awkwardengineer/Clock/Mechanical/Quotes/Case/Rev D Case Quote Package/Change notes to revC and revD.pdf

AWK-105-010 Rev C notes

# Change notes since last quote (now at Rev D.)

1. Material thickness changed from .060” to .050”
2. Overall dimensions slightly smaller
3. Addition of notches (see below)
4. QTY will be 550 pcs, each.
5. I am talking to Roy about finish. We’ll run two different colors, ANSI 61 Gray with black screenprint, and FED STD 34094 Green, with white screenprint. Final batch sizes TBD.
6. Artwork for screenprints is attached

# Changes from C to D

7. Height of box changed from 4” to 3.5”
8. Holes for knobs in top opened up
9. Only powder coat exterior faces
10. Artwork updated for new box size

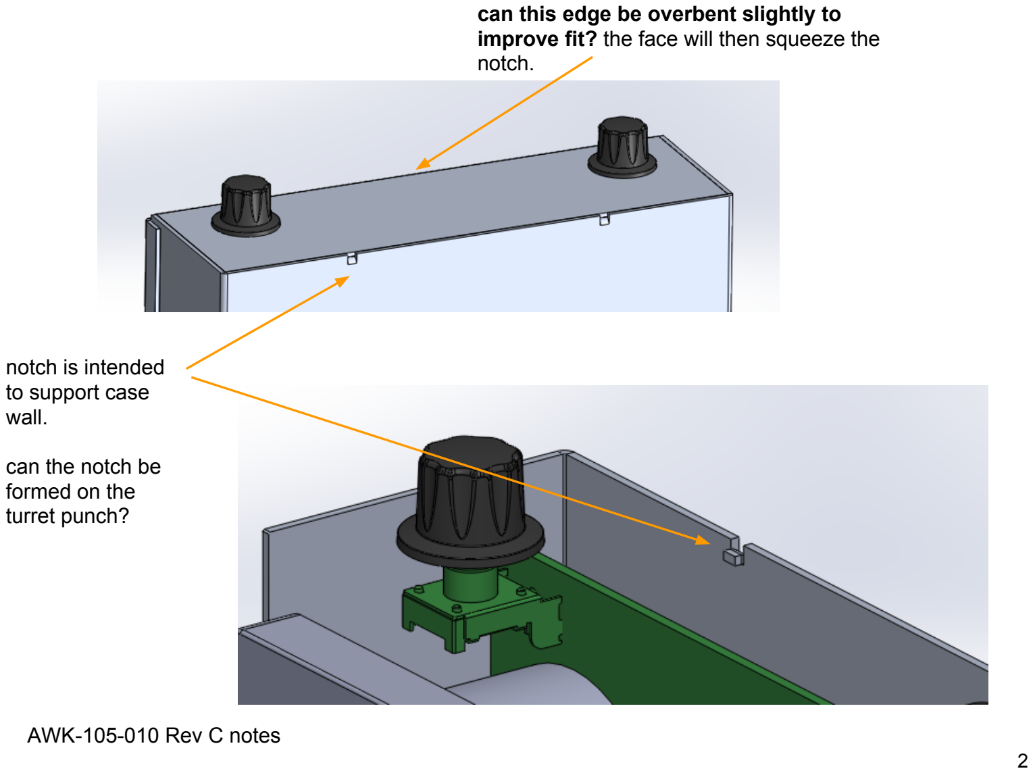
[picture p24: page 2]

notch is intended
to support case
wall.

can the notch be
formed on the
turret punch?

can this edge be overbent slightly to improve fit? the face will then squeeze the notch.

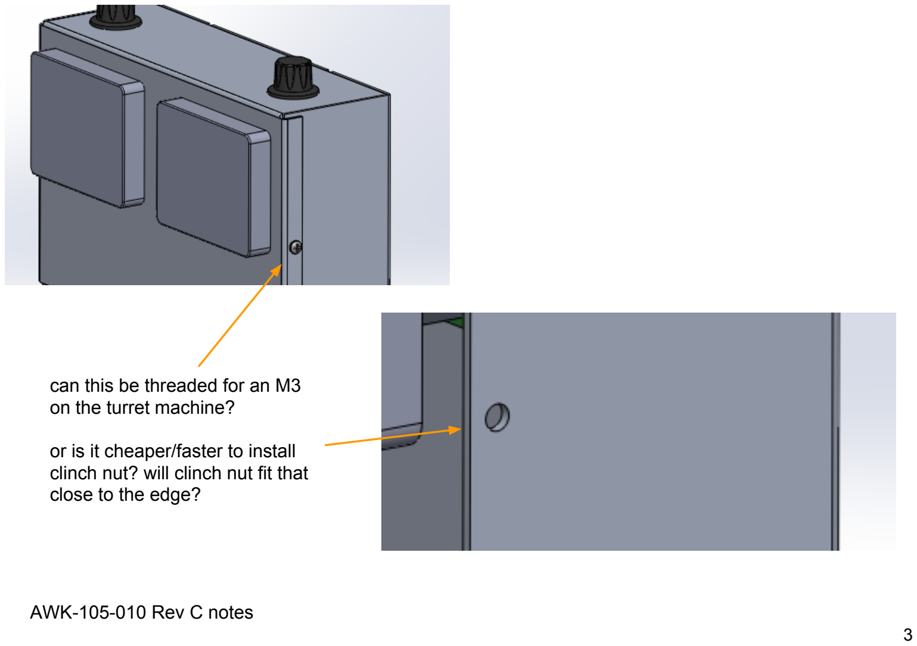
[picture p25: page 3]

can this be threaded for an M3 on the turret machine?

or is it cheaper/faster to install clinch nut? will clinch nut fit that close to the edge?
