awkwardengineer/Clock/Mechanical/Artwork/jameco 316603.pdf

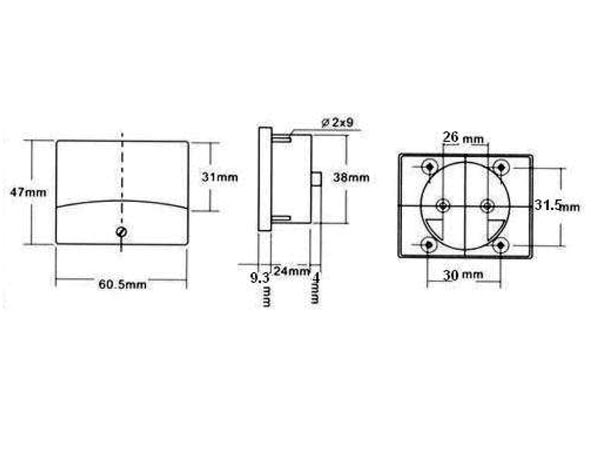
[picture p26: page 1]
