awkwardengineer/Clock/Mechanical/Quotes/Case/Rev D Case Quote Package/revD notes.pdf

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

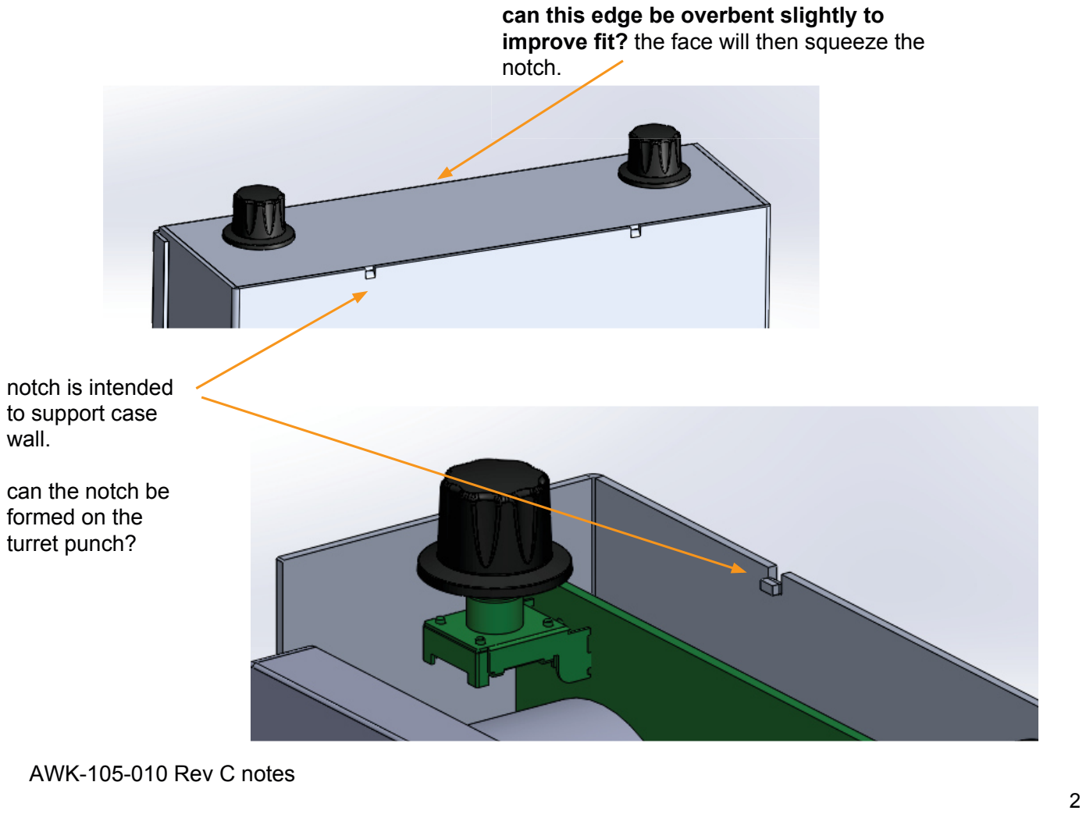
[picture p27: page 1]

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

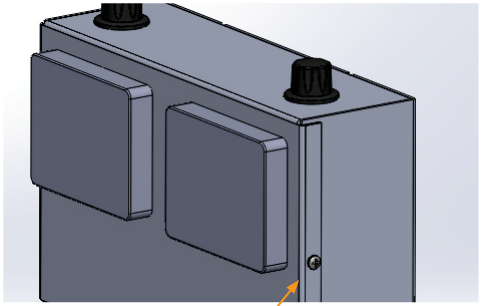
[picture p28: figure]
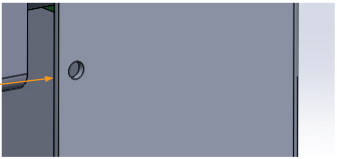
[picture p29: figure]
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
