awkwardengineer/Clock/Photos/exploded view.pdf

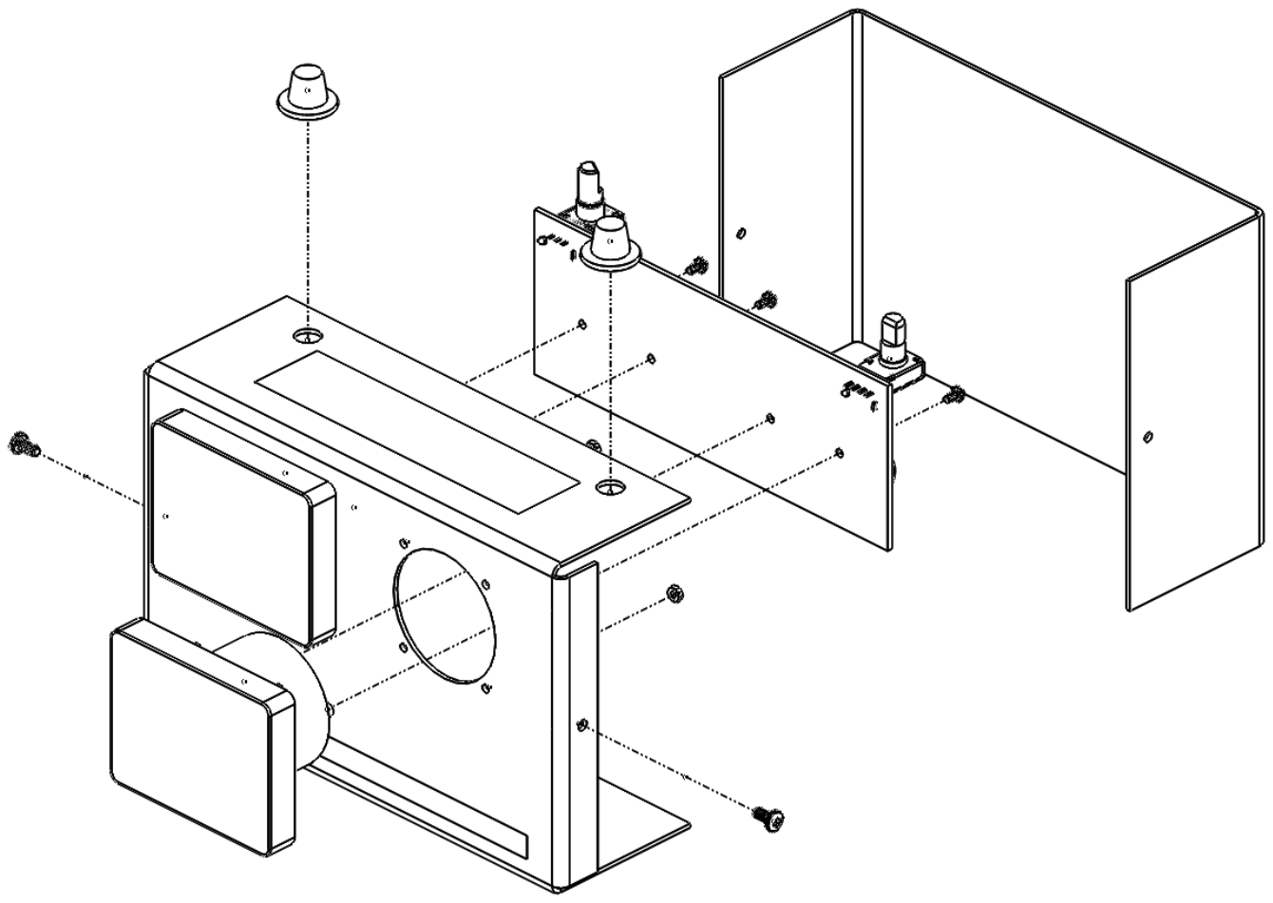
[picture p30: page 1]
