awkwardengineer/Clock/Mechanical/Artwork/AWK-105-0016 revE.png

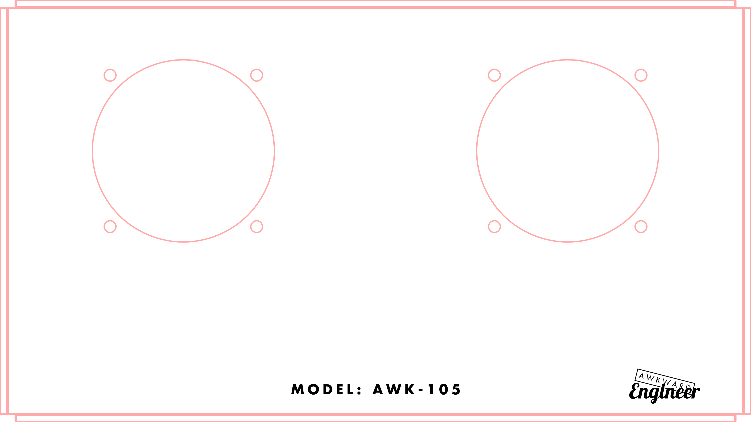
Mechanical/Artwork/AWK-105-0016 revE.png
