awkwardengineer/Clock/Mechanical/Artwork/AWK-105-0021-GRAY.png

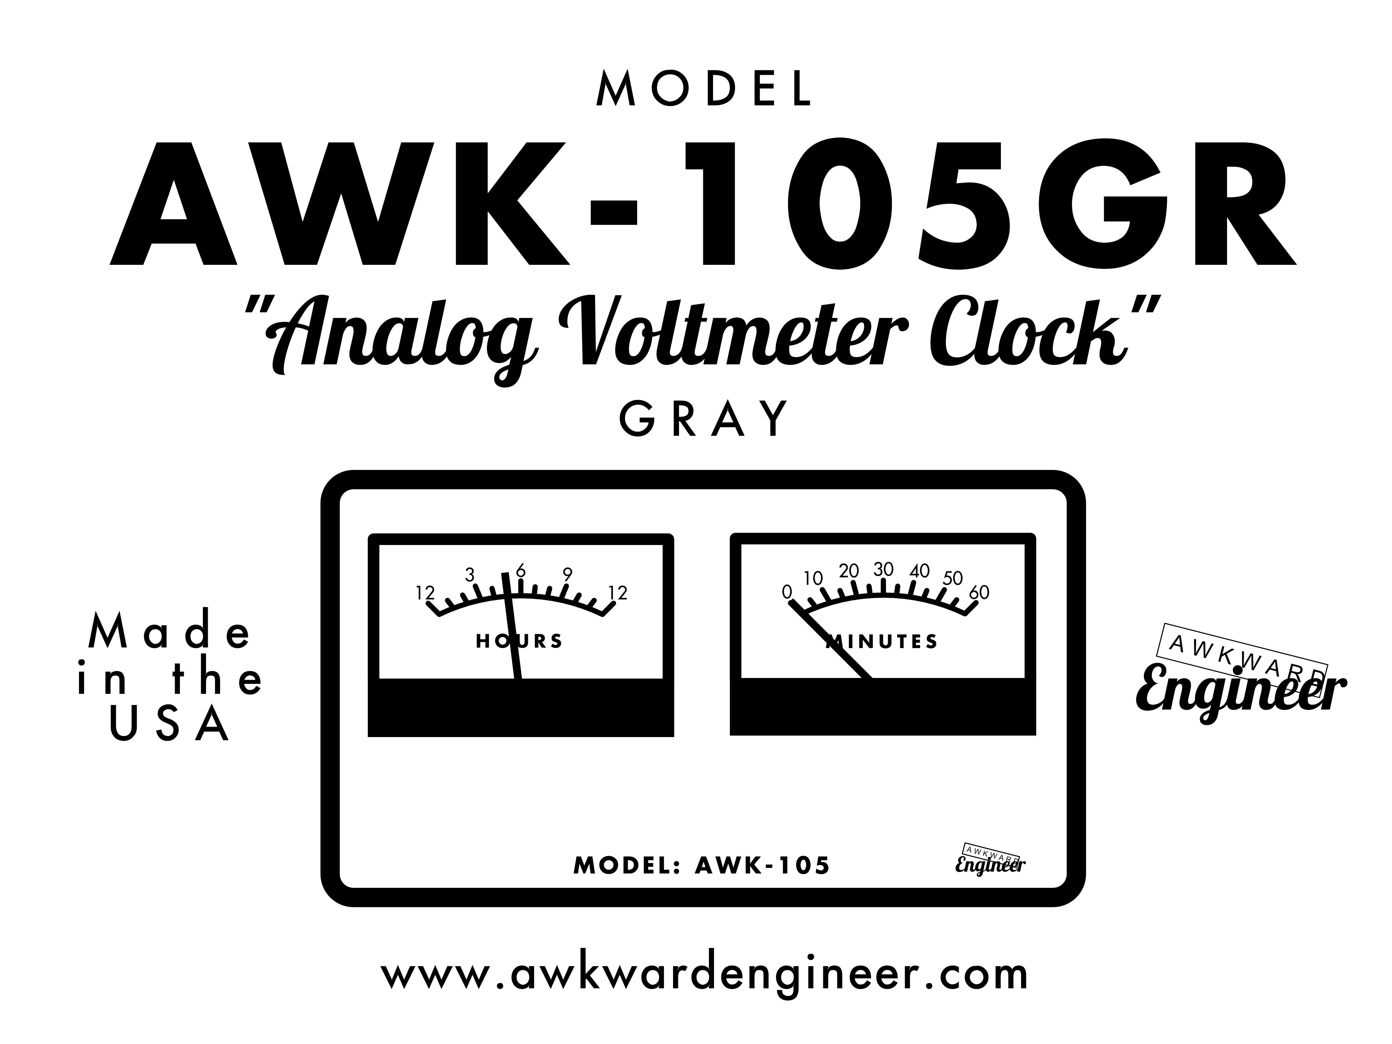
Mechanical/Artwork/AWK-105-0021-GRAY.png
