awkwardengineer/Clock/Mechanical/Artwork/AWK-105-0045.png

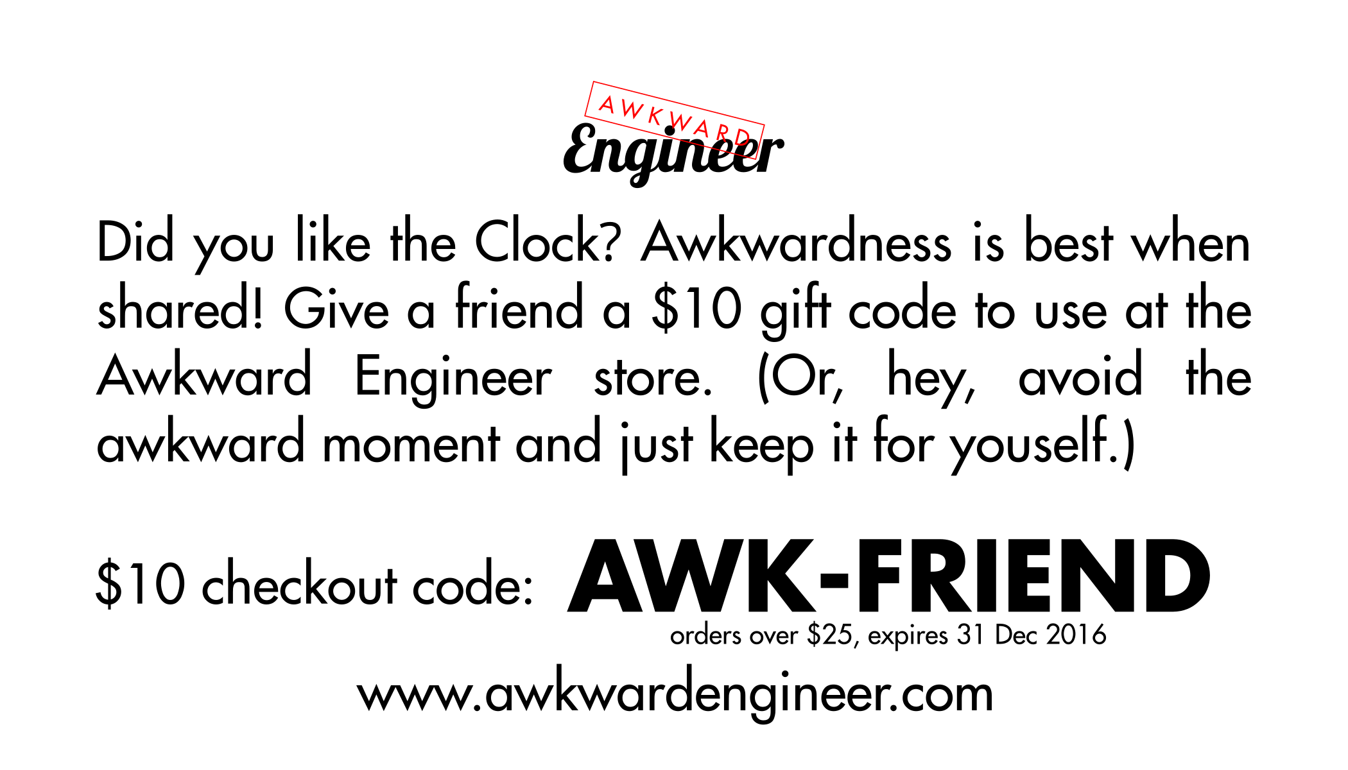
Mechanical/Artwork/AWK-105-0045.png
