awkwardengineer/Clock/Mechanical/Artwork/front decal.png

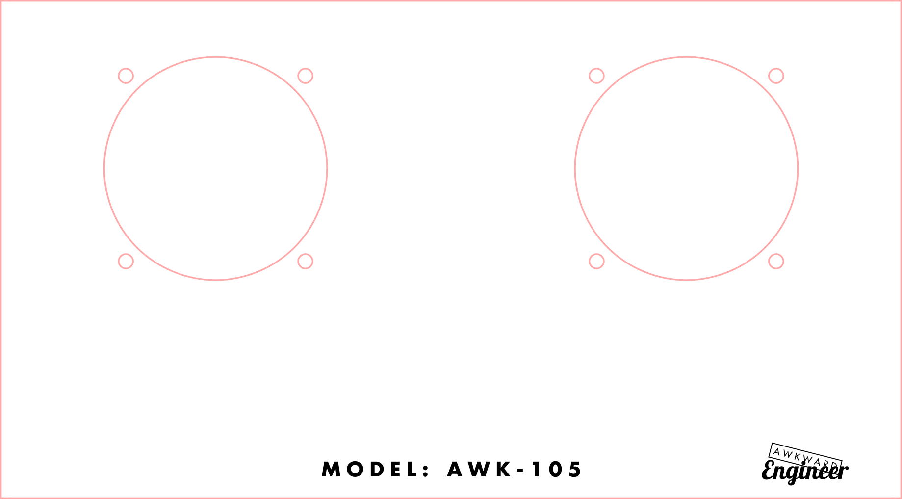
Mechanical/Artwork/front decal.png
