awkwardengineer/Clock/Mechanical/Artwork/Jameco 316603.png

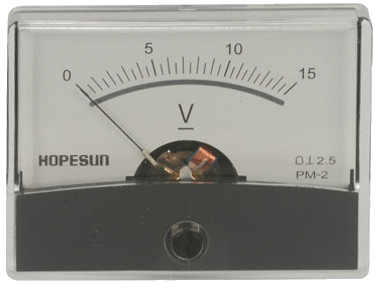
Mechanical/Artwork/Jameco 316603.png
