awkwardengineer/Clock/Mechanical/Artwork/Sparkfun 10285.jpg

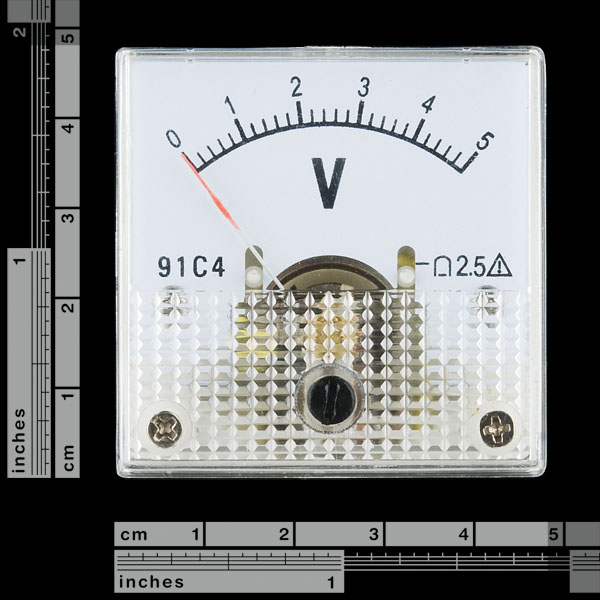
Mechanical/Artwork/Sparkfun 10285.jpg
