awkwardengineer/Clock/Mechanical/Artwork/top decal alarm.png

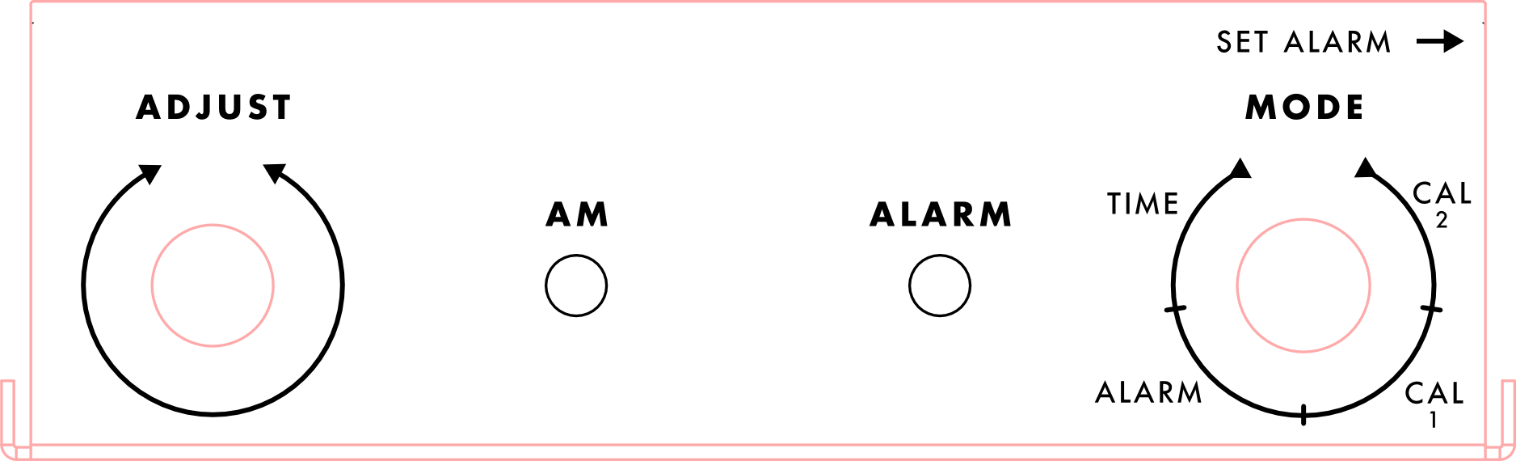
Mechanical/Artwork/top decal alarm.png
