awkwardengineer/Clock/Mechanical/Artwork/top decal.png

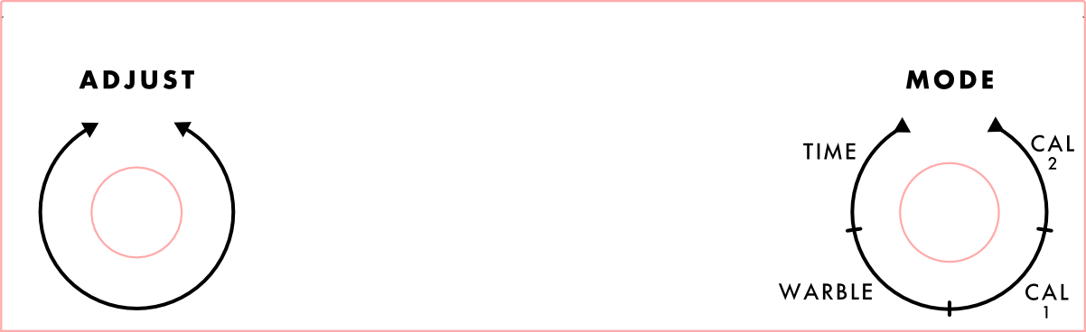
Mechanical/Artwork/top decal.png
