awkwardengineer/Clock/Mechanical/CAD/AWK-105-0007jpg.JPG

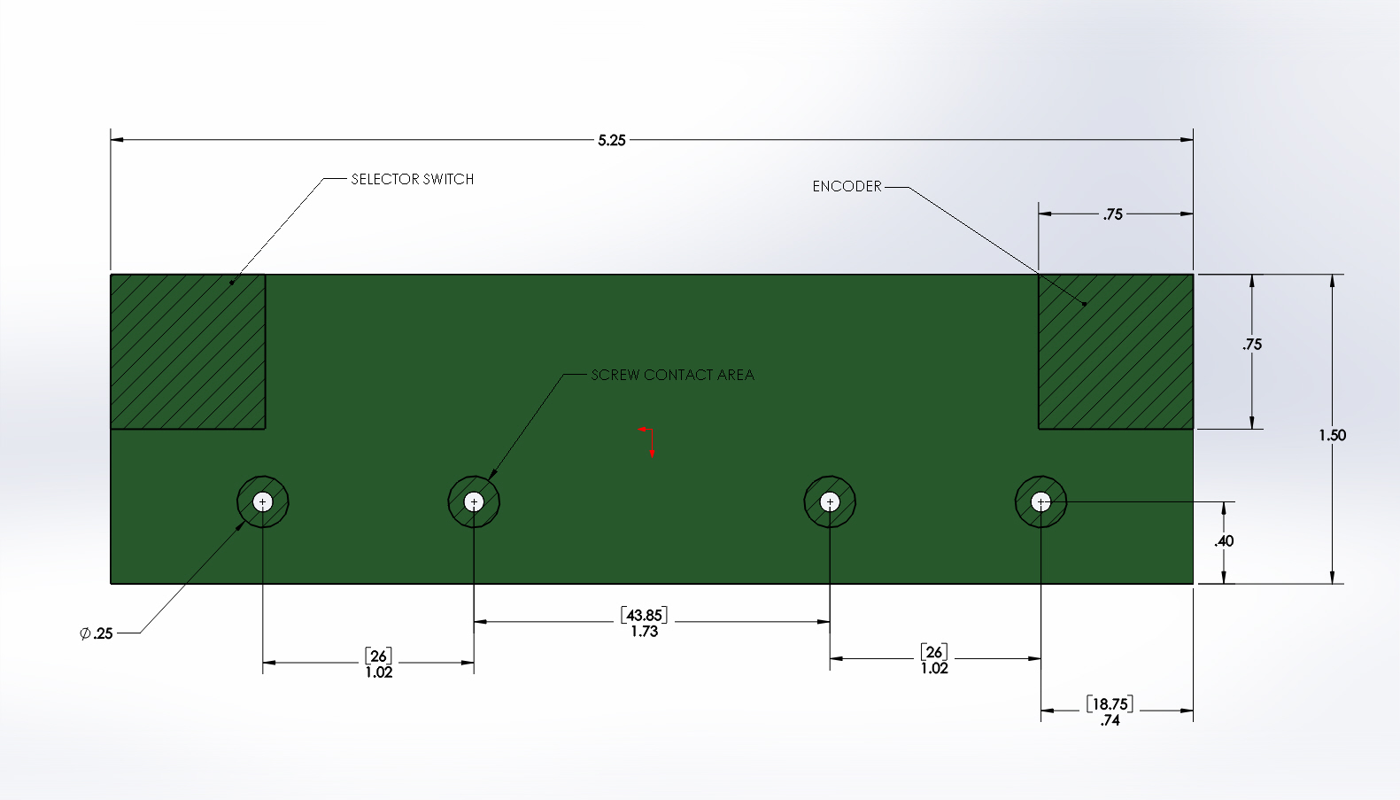
Mechanical/CAD/AWK-105-0007jpg.JPG
