awkwardengineer/Clock/Mechanical/Reference Material/ENCODER_mechanical.JPG

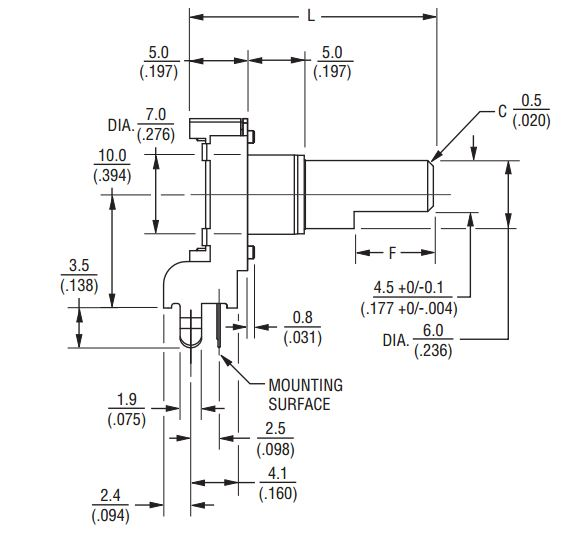
Mechanical/Reference Material/ENCODER_mechanical.JPG
