awkwardengineer/Clock/Photos/Blog Post Material/software_architecture.png

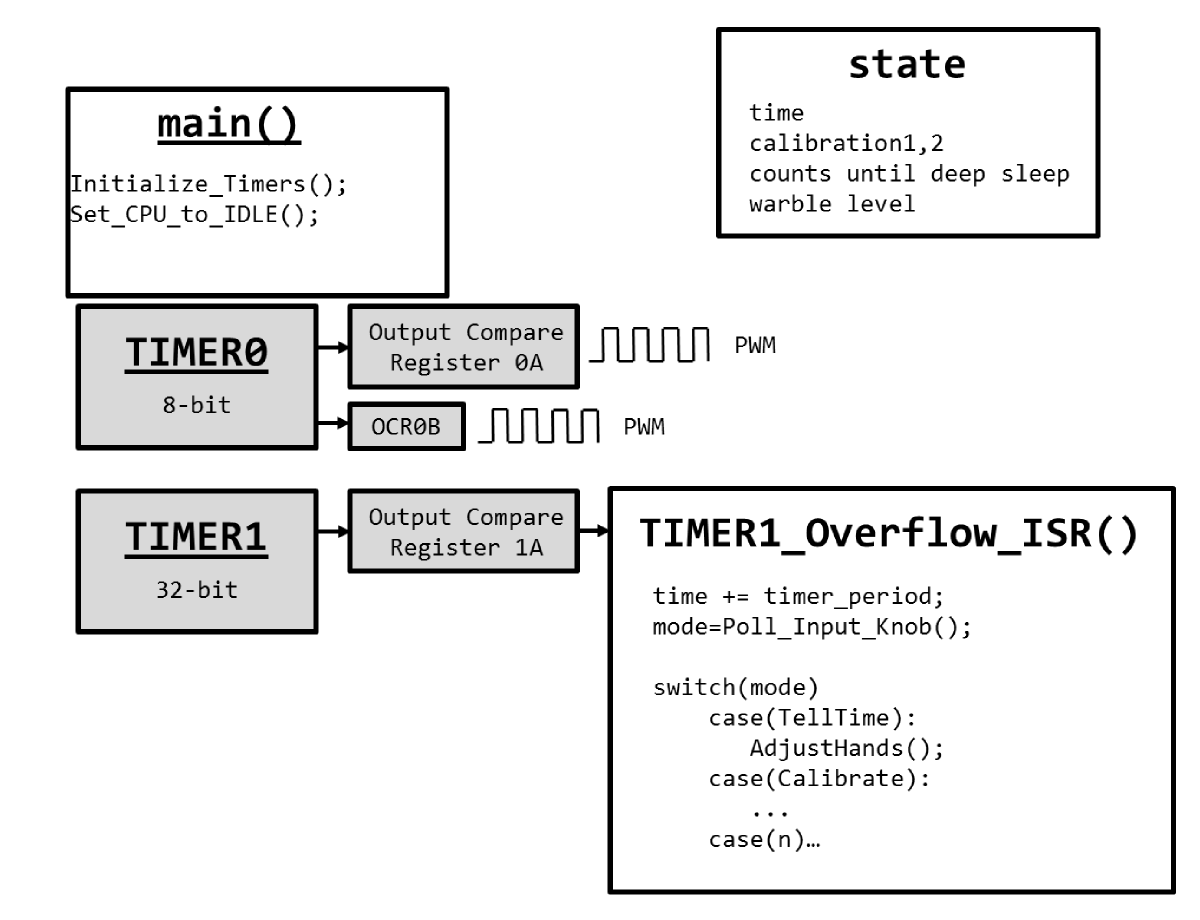
Photos/Blog Post Material/software_architecture.png
