awkwardengineer/Clock/Photos/Board Production Media/20150706_070131.jpg

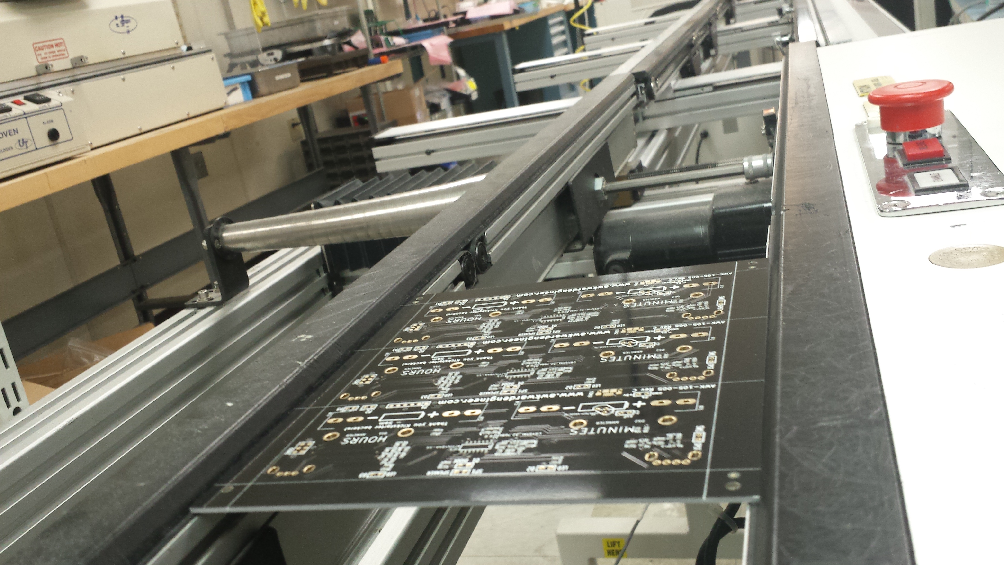
Photos/Board Production Media/20150706_070131.jpg
