awkwardengineer/Clock/Photos/Board Production Media/20150706_070157.jpg

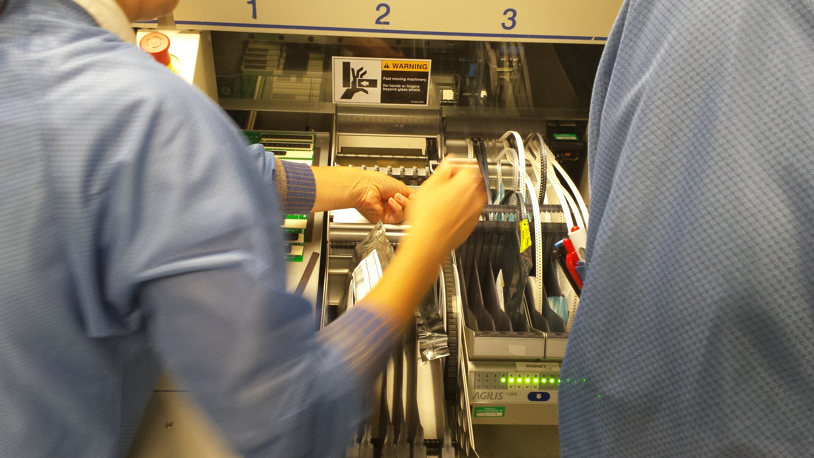
Photos/Board Production Media/20150706_070157.jpg
