awkwardengineer/Clock/Photos/Board Production Media/20150706_070753.jpg

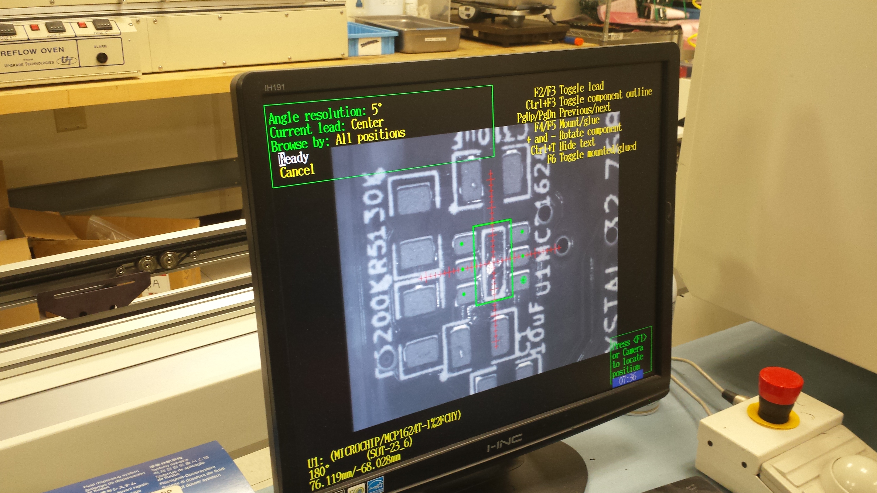
Photos/Board Production Media/20150706_070753.jpg
