awkwardengineer/Clock/Photos/Board Production Media/20150706_072234.jpg

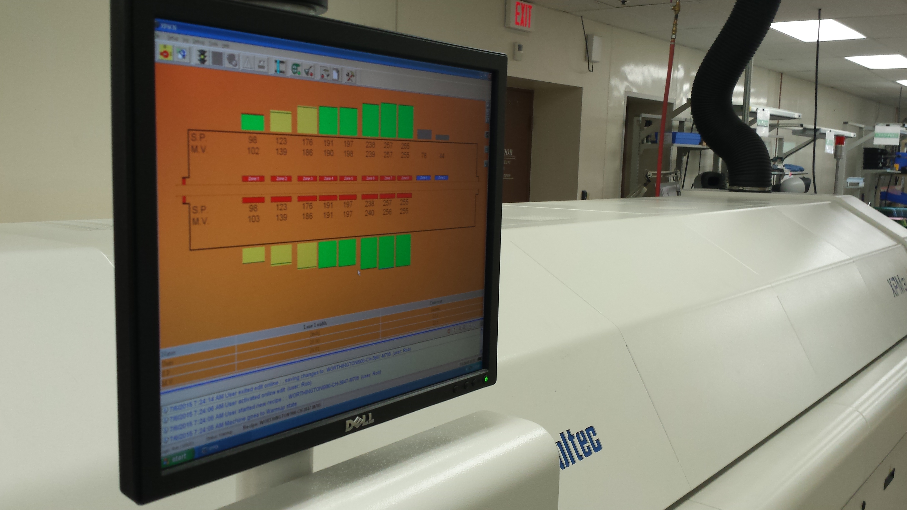
Photos/Board Production Media/20150706_072234.jpg
