awkwardengineer/Clock/Photos/Board Production Media/20150706_081147.jpg

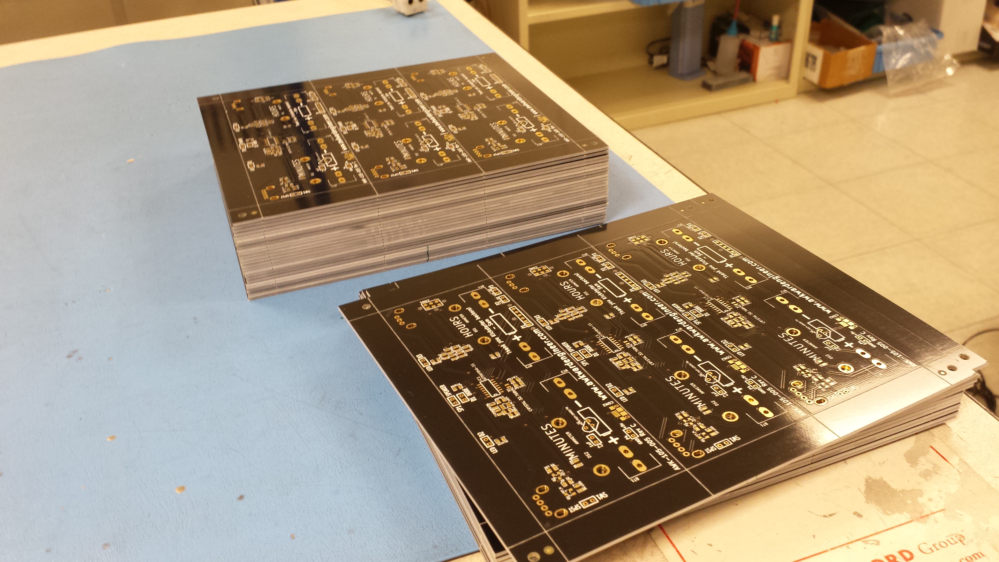
Photos/Board Production Media/20150706_081147.jpg
