awkwardengineer/Clock/Photos/Board Production Media/20150706_091250.jpg

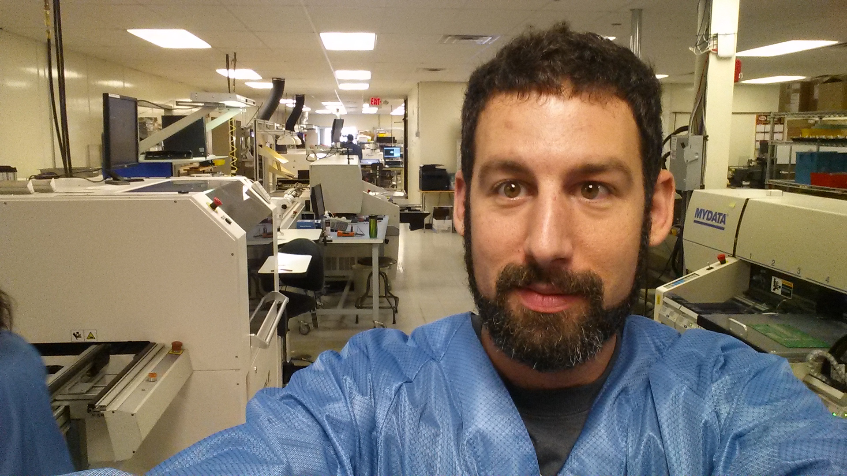
Photos/Board Production Media/20150706_091250.jpg
