awkwardengineer/Clock/Photos/Board Production Media/20150706_094641.jpg

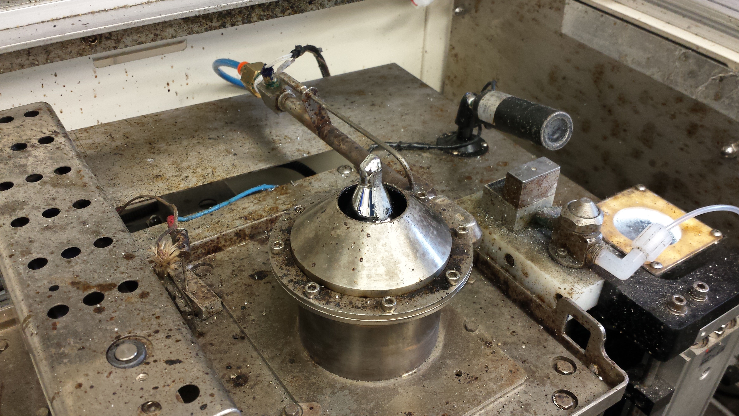
Photos/Board Production Media/20150706_094641.jpg
