awkwardengineer/Clock/Photos/Board Production Media/20150706_095433.jpg

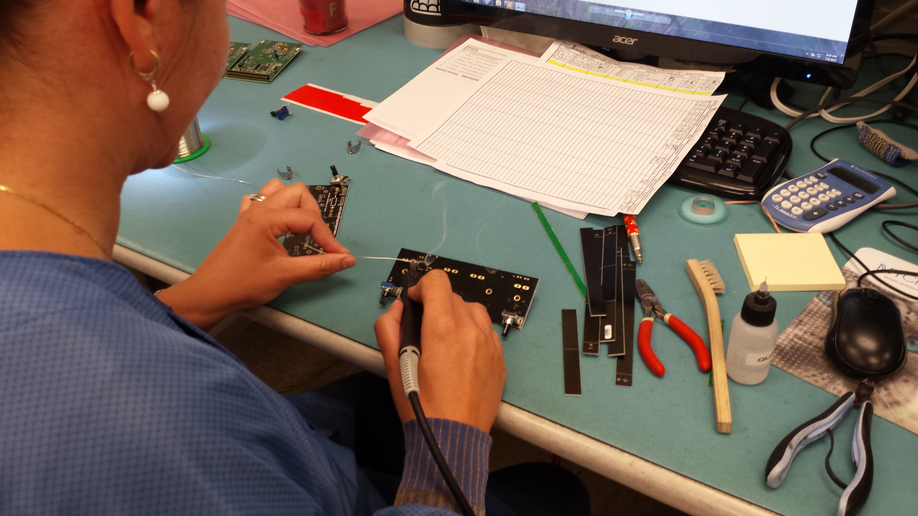
Photos/Board Production Media/20150706_095433.jpg
