awkwardengineer/Clock/Photos/Board Production Media/factory/20150706_064646.jpg

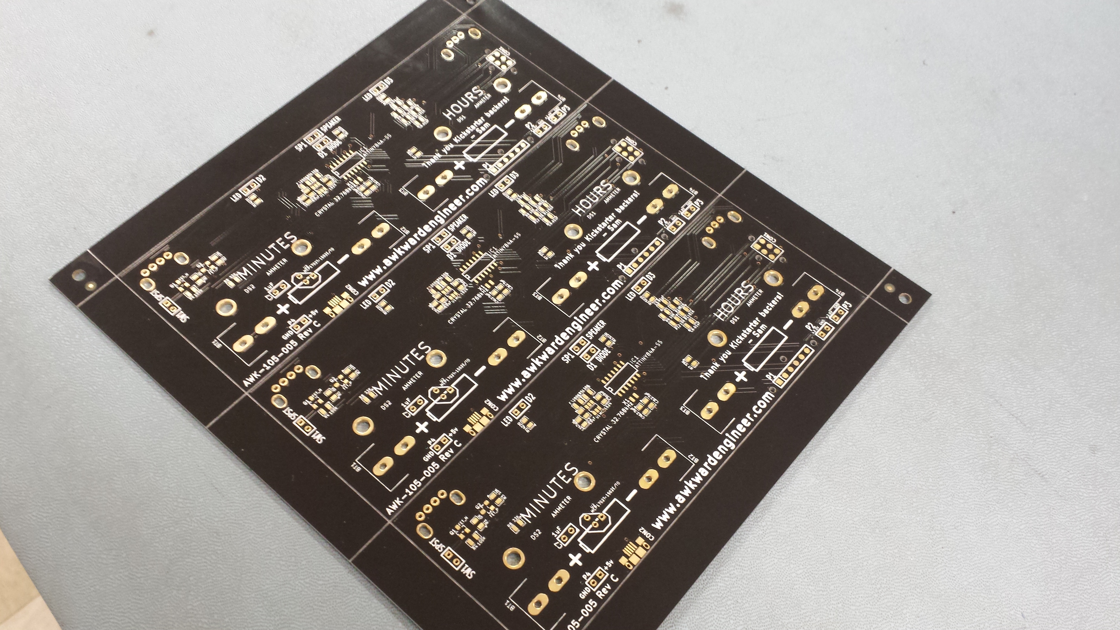
Photos/Board Production Media/factory/20150706_064646.jpg
