awkwardengineer/Clock/Photos/Board Production Media/factory/20150706_070143.jpg

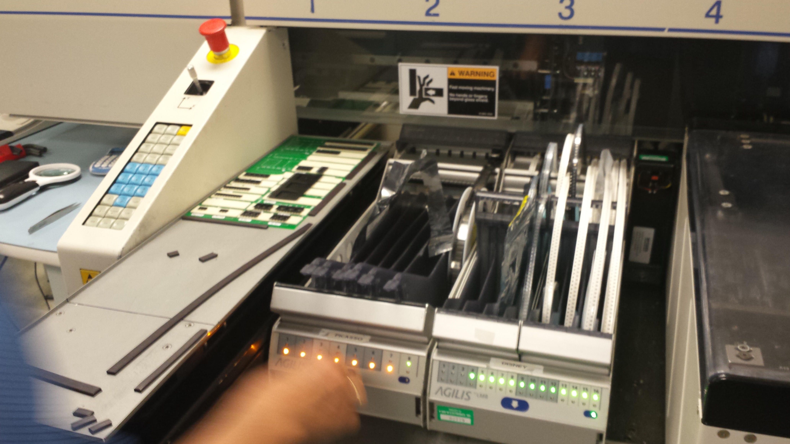
Photos/Board Production Media/factory/20150706_070143.jpg
