awkwardengineer/Clock/Photos/Board Production Media/factory/20150706_070641.jpg

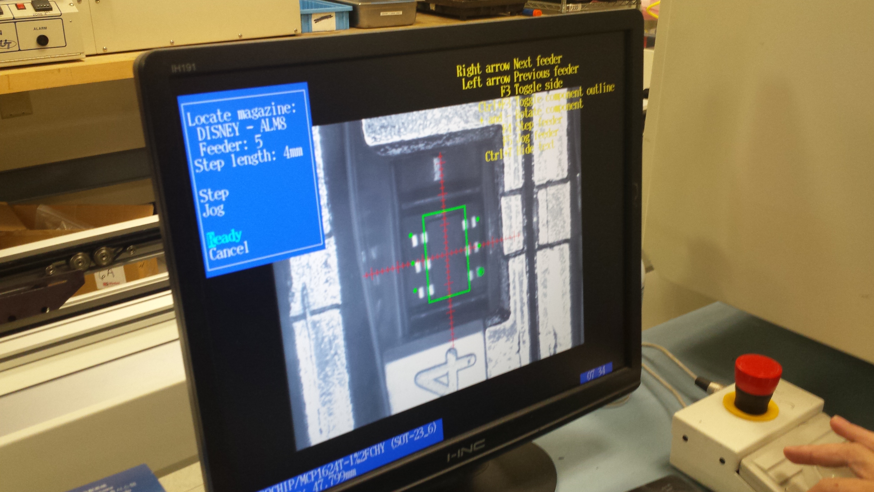
Photos/Board Production Media/factory/20150706_070641.jpg
