awkwardengineer/Clock/Photos/Board Production Media/factory/20150706_071905.jpg

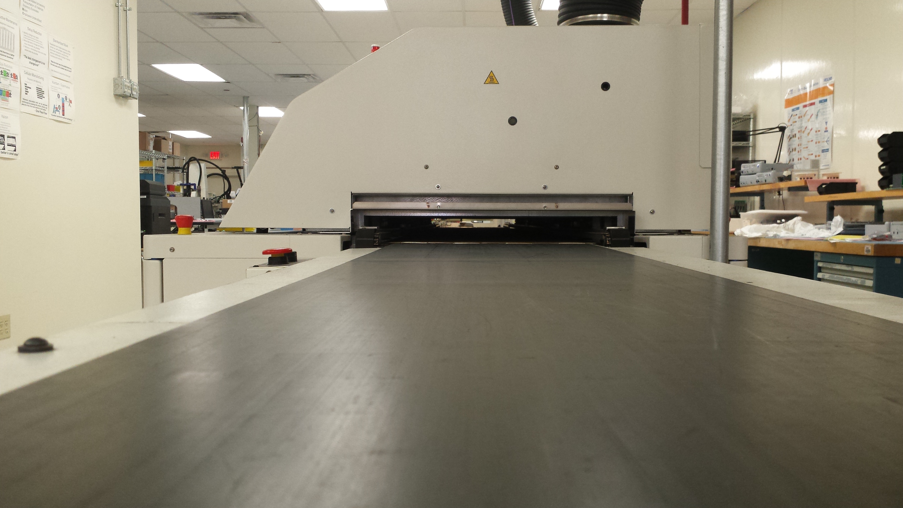
Photos/Board Production Media/factory/20150706_071905.jpg
