awkwardengineer/Clock/Photos/Board Production Media/factory/20150706_071955.jpg

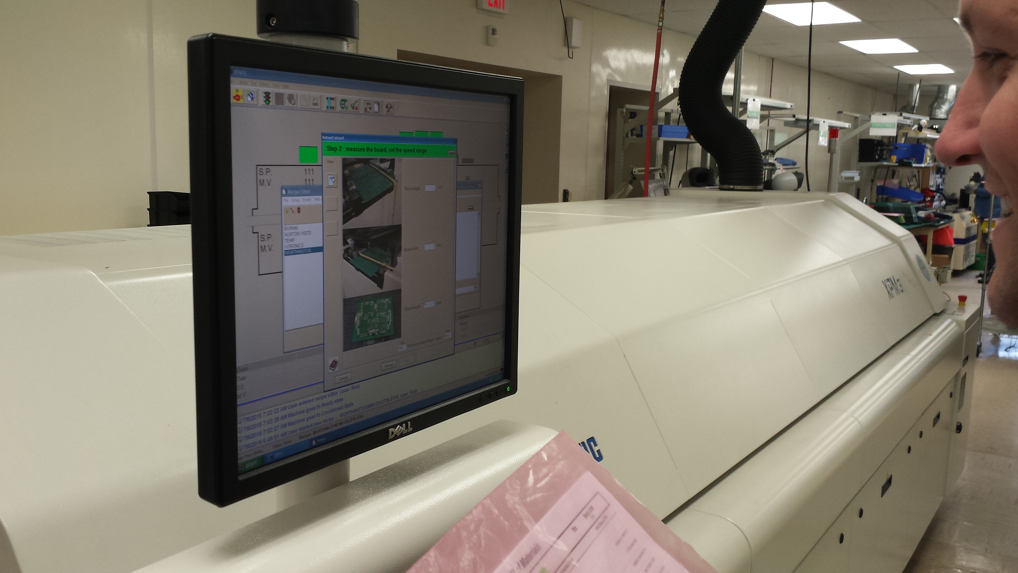
Photos/Board Production Media/factory/20150706_071955.jpg
