awkwardengineer/Clock/Photos/Board Production Media/factory/20150706_072637.jpg

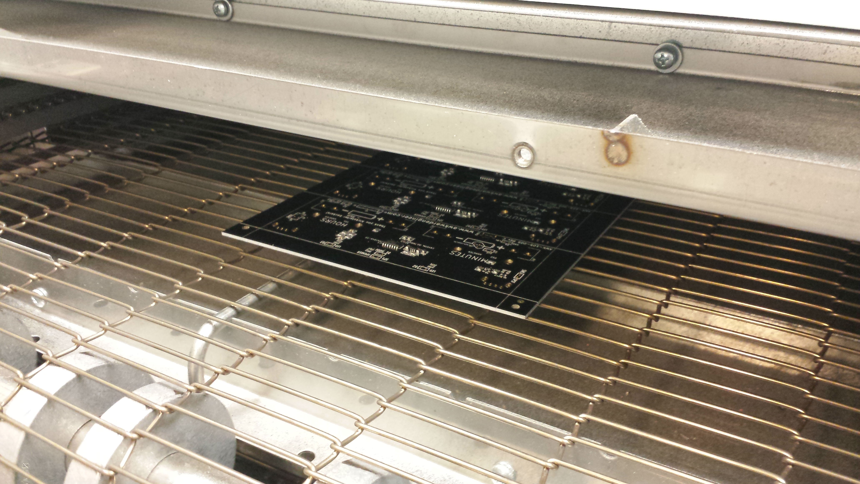
Photos/Board Production Media/factory/20150706_072637.jpg
