awkwardengineer/Clock/Photos/Board Production Media/factory/20150706_073539.jpg

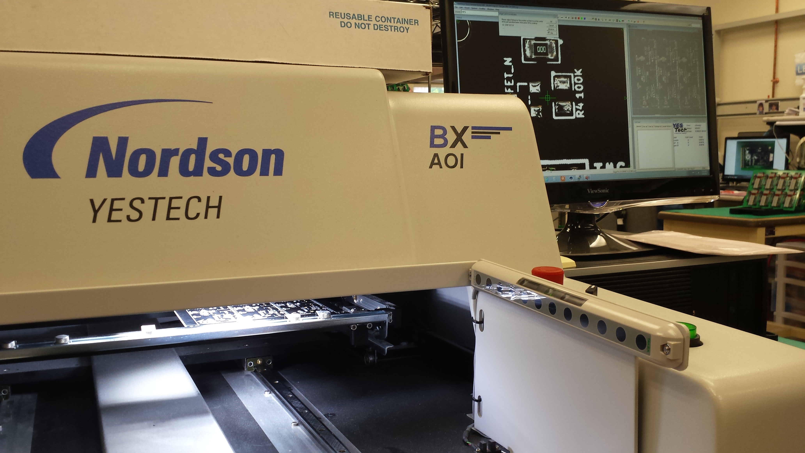
Photos/Board Production Media/factory/20150706_073539.jpg
