awkwardengineer/Clock/Photos/Board Production Media/factory/20150706_075311.jpg

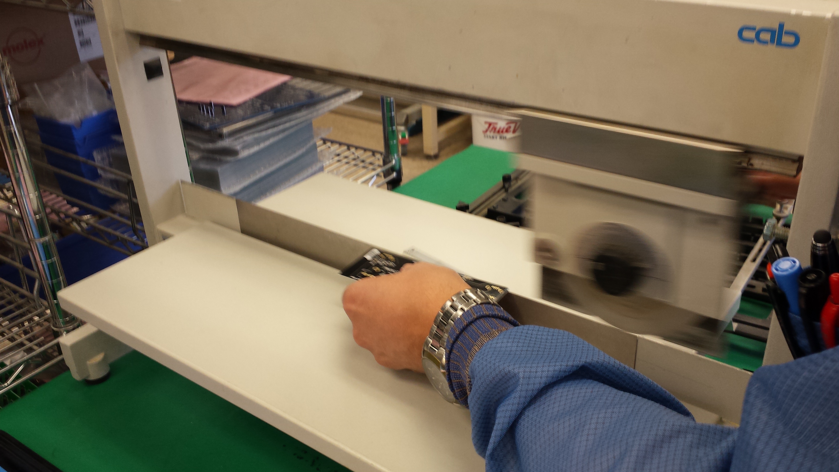
Photos/Board Production Media/factory/20150706_075311.jpg
