awkwardengineer/Clock/Photos/Board Production Media/factory/20150706_092922.jpg

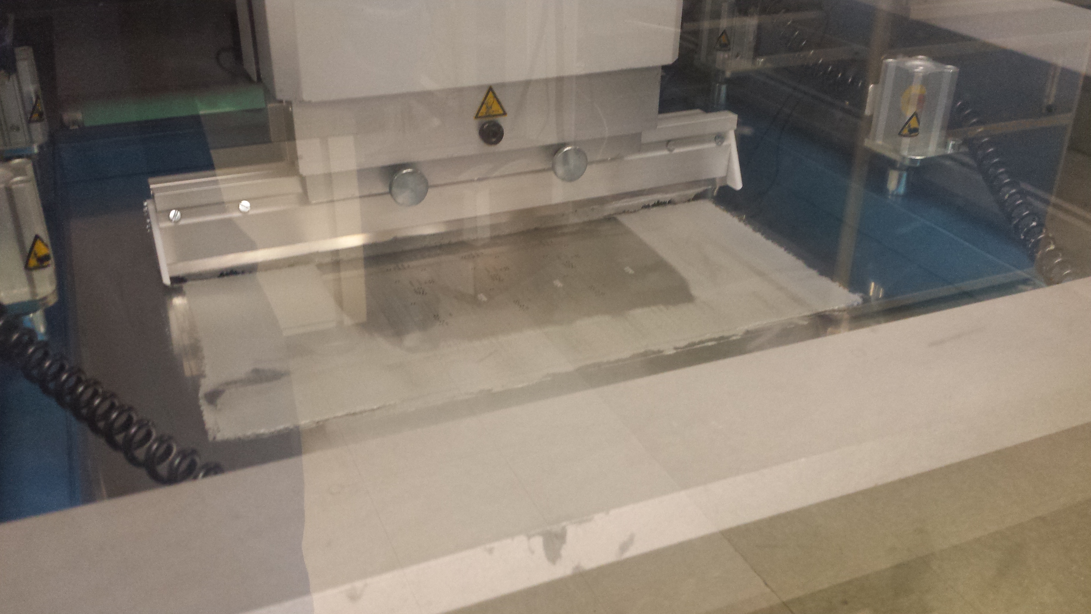
Photos/Board Production Media/factory/20150706_092922.jpg
