awkwardengineer/Clock/Photos/Board Production Media/factory/20150706_094656.jpg

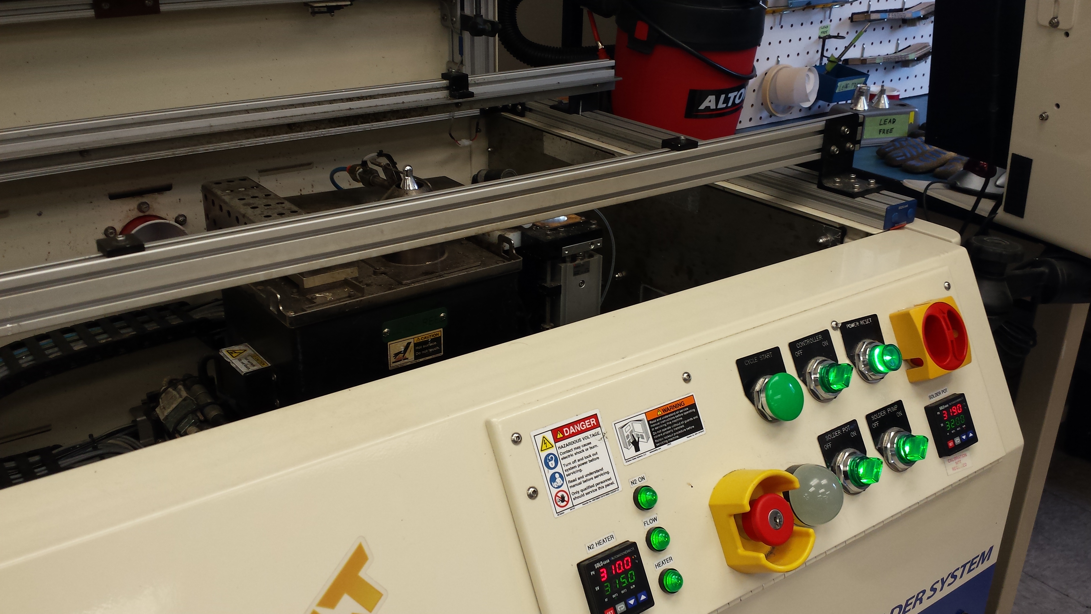
Photos/Board Production Media/factory/20150706_094656.jpg
