awkwardengineer/Clock/Photos/Board Production Media/factory/20150706_095524.jpg

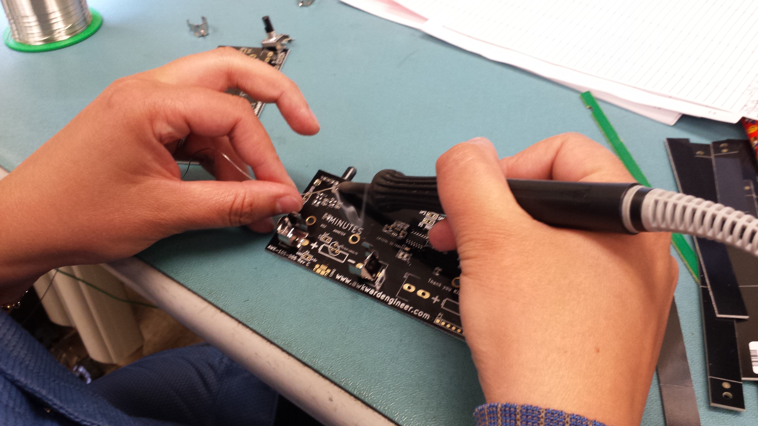
Photos/Board Production Media/factory/20150706_095524.jpg
