awkwardengineer/Clock/Photos/Covers/_ cover - cookie DFM.png

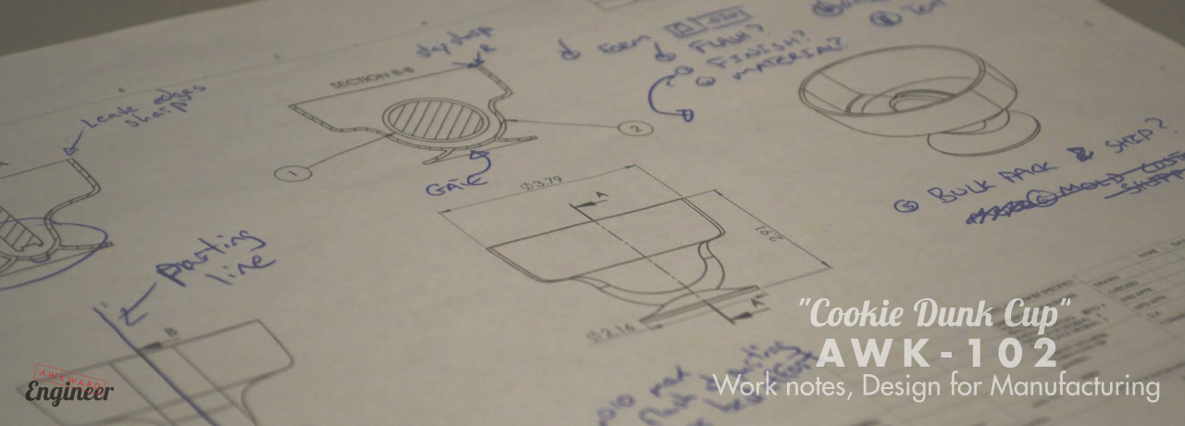
Photos/Covers/_ cover - cookie DFM.png
