awkwardengineer/Clock/Photos/Covers/_ cover - prodaddy.png

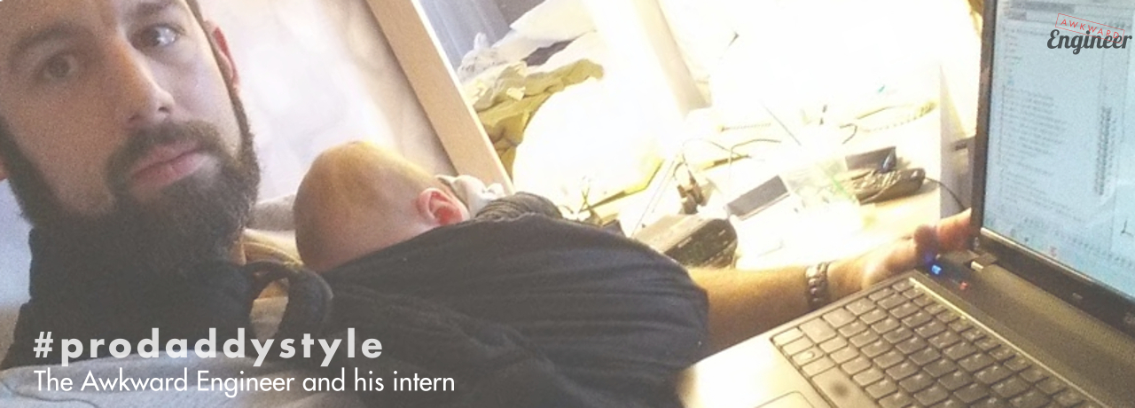
Photos/Covers/_ cover - prodaddy.png
