awkwardengineer/Clock/Photos/Covers/AWK-105AL cover.JPG

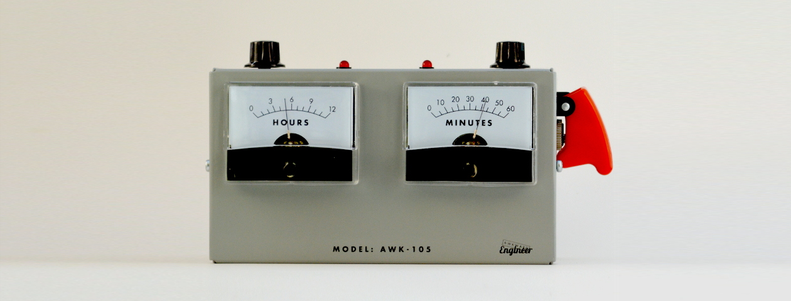
Photos/Covers/AWK-105AL cover.JPG
