awkwardengineer/Clock/Photos/Covers/click20.png

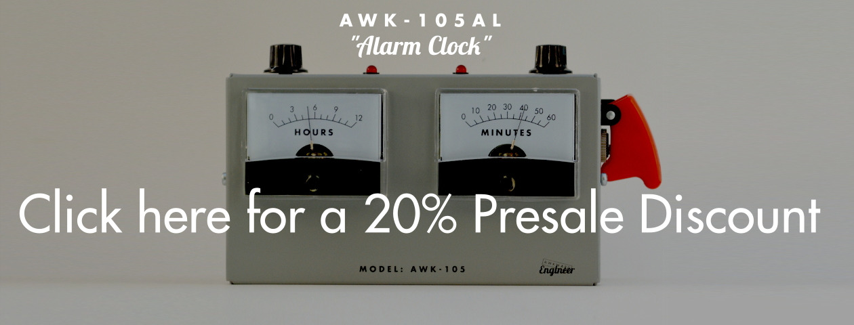
Photos/Covers/click20.png
