awkwardengineer/Clock/Photos/Covers/cover - awk moustache.jpg

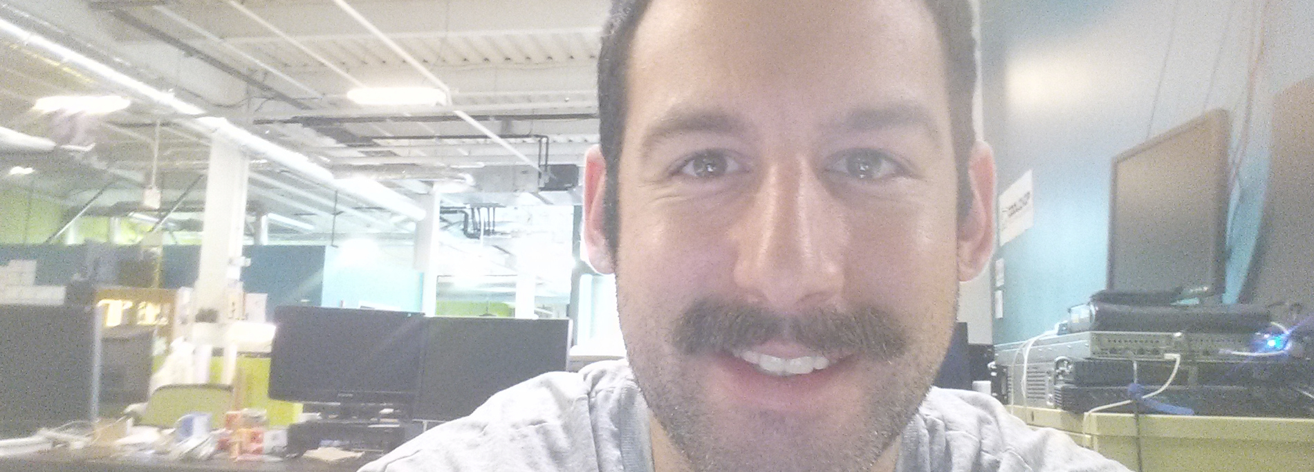
Photos/Covers/cover - awk moustache.jpg
