awkwardengineer/Clock/Photos/Covers/cover - button.JPG

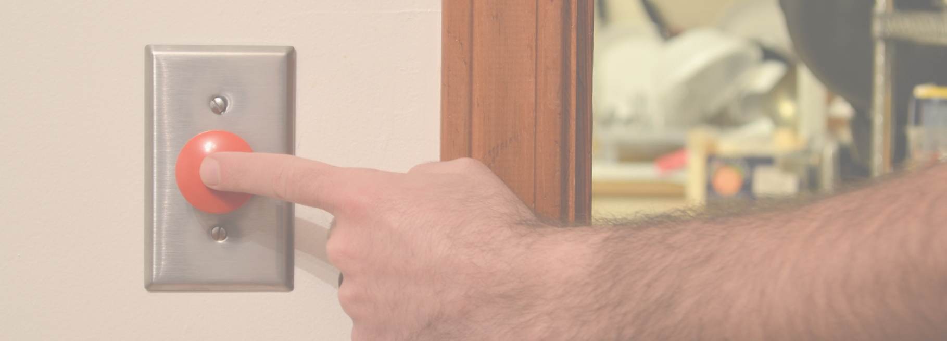
Photos/Covers/cover - button.JPG
