awkwardengineer/Clock/Photos/Covers/cover- button factory.jpg

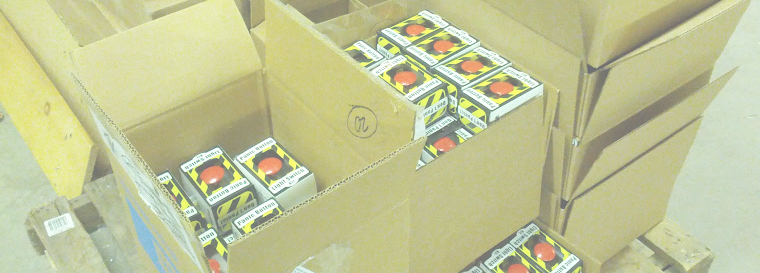
Photos/Covers/cover- button factory.jpg
