awkwardengineer/Clock/Photos/Covers/member20.png

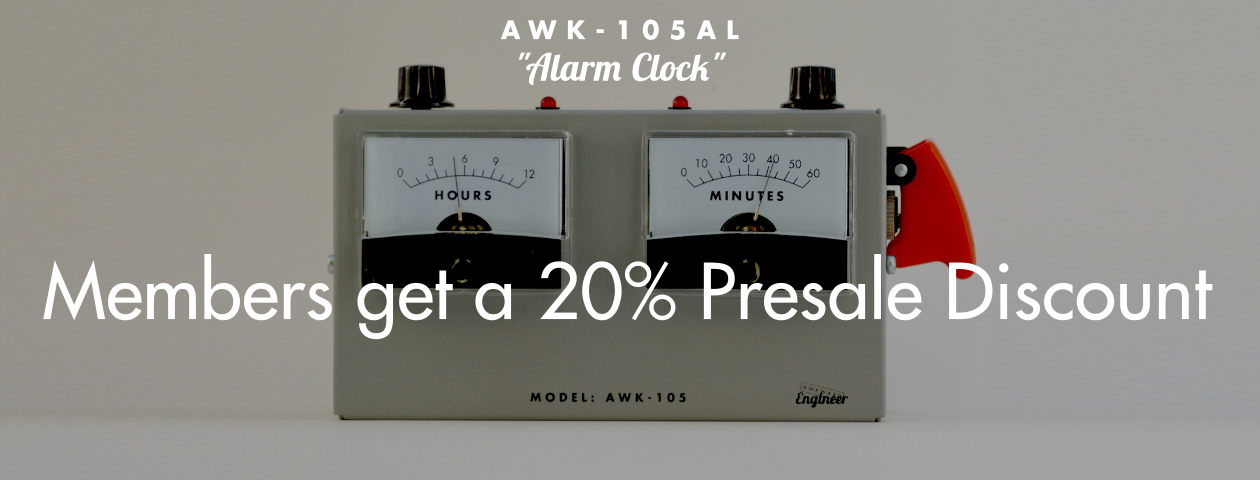
Photos/Covers/member20.png
