awkwardengineer/Clock/Photos/Covers/original covers/cover - alarm in progress.jpg

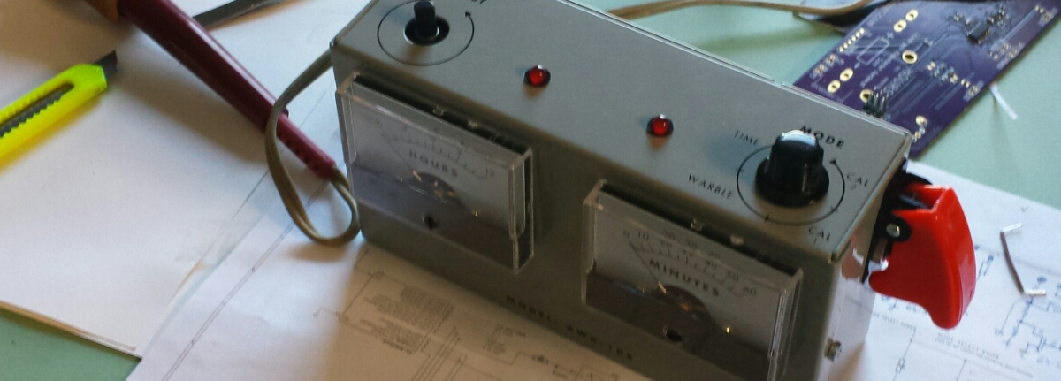
Photos/Covers/original covers/cover - alarm in progress.jpg
