awkwardengineer/Clock/Photos/Covers/original covers/cover - clock at paint.jpg

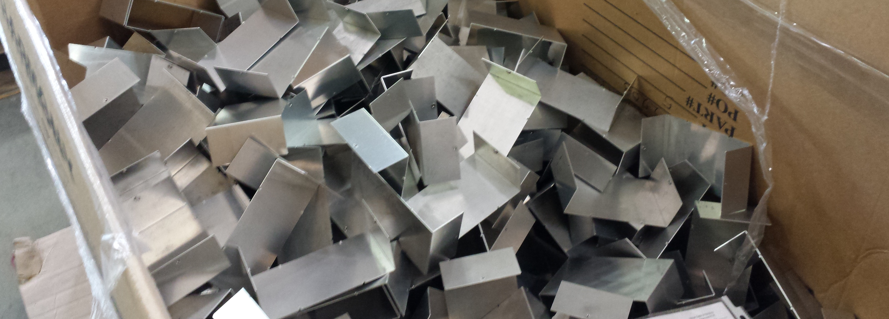
Photos/Covers/original covers/cover - clock at paint.jpg
