awkwardengineer/Clock/Photos/Covers/original covers/cover - paper prototype.jpg

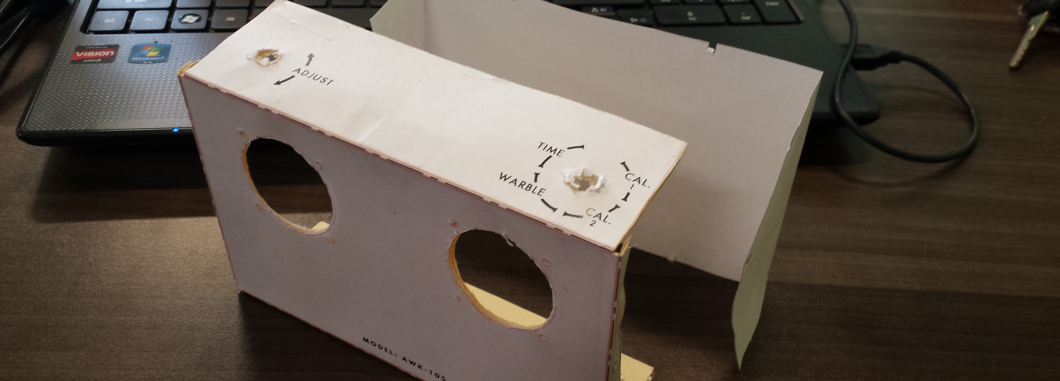
Photos/Covers/original covers/cover - paper prototype.jpg
