awkwardengineer/Clock/Photos/Customer Pics/12576274_10156384217585332_1704815280_n.jpg

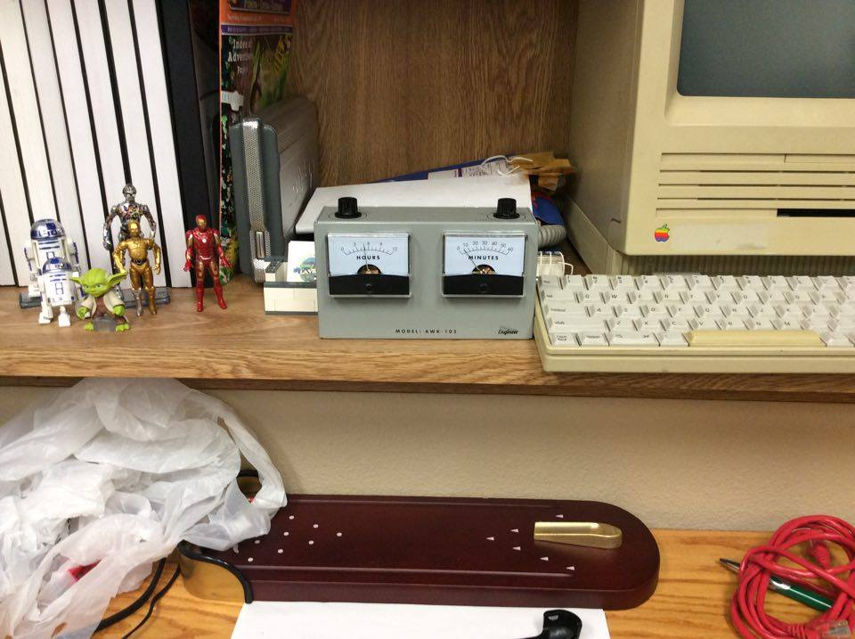
Photos/Customer Pics/12576274_10156384217585332_1704815280_n.jpg
