awkwardengineer/Clock/Photos/Customer Pics/audio studio.jpg

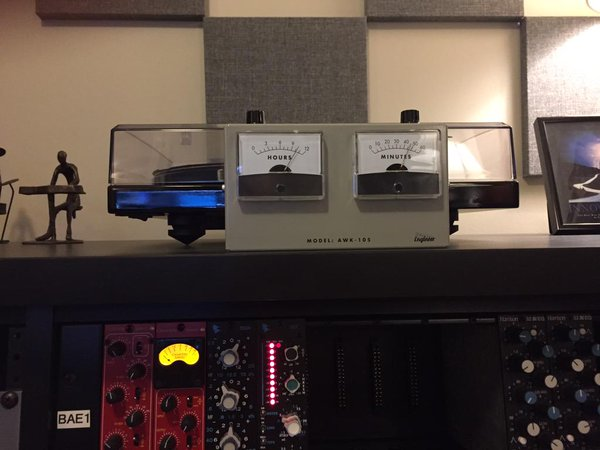
Photos/Customer Pics/audio studio.jpg
