awkwardengineer/Clock/Photos/Customer Pics/awk.JPG

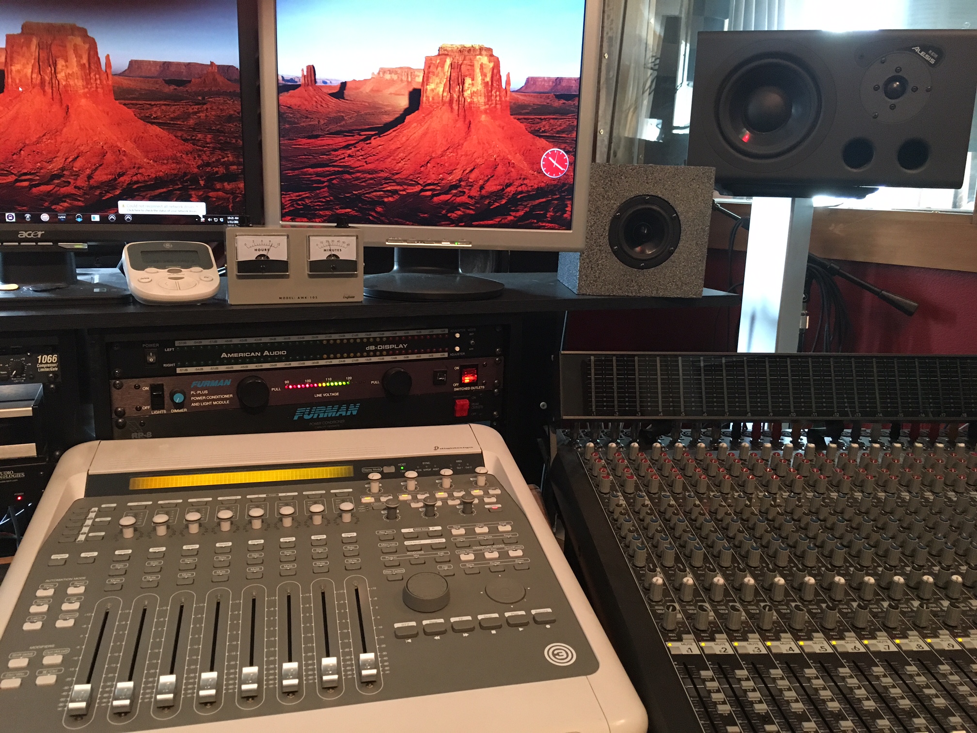
Photos/Customer Pics/awk.JPG
