awkwardengineer/Clock/Photos/Customer Pics/backlit.jpg

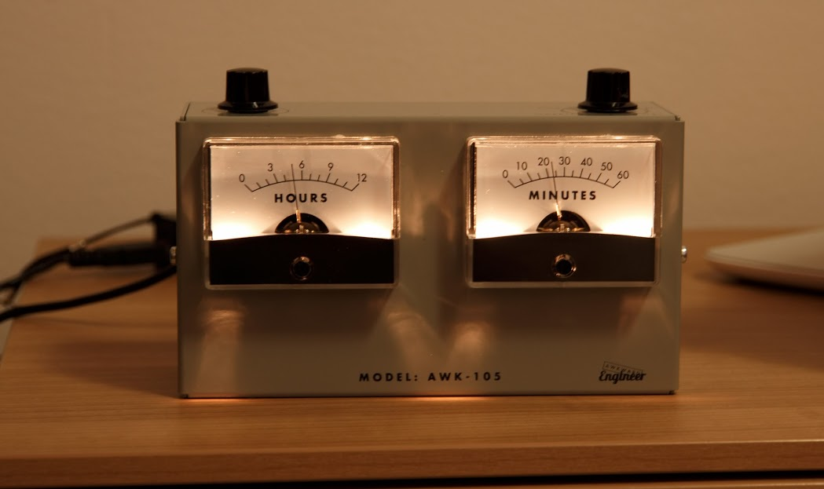
Photos/Customer Pics/backlit.jpg
