awkwardengineer/Clock/Photos/Customer Pics/bench.jpg

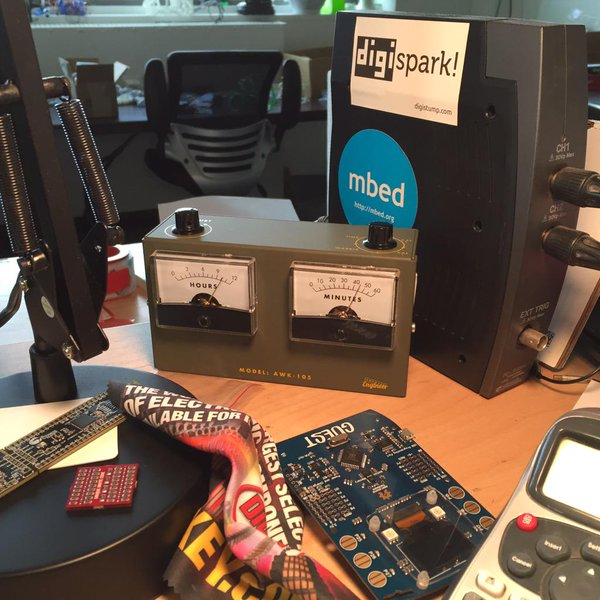
Photos/Customer Pics/bench.jpg
