awkwardengineer/Clock/Photos/Customer Pics/cat.jpg

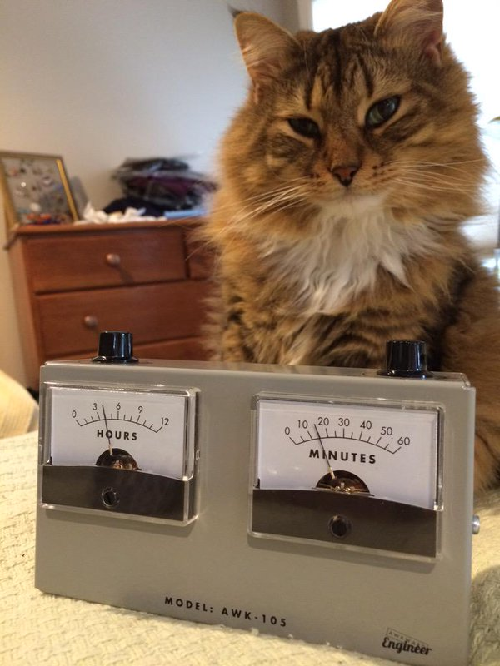
Photos/Customer Pics/cat.jpg
