awkwardengineer/Clock/Photos/Customer Pics/clock and coca-cola.jpg

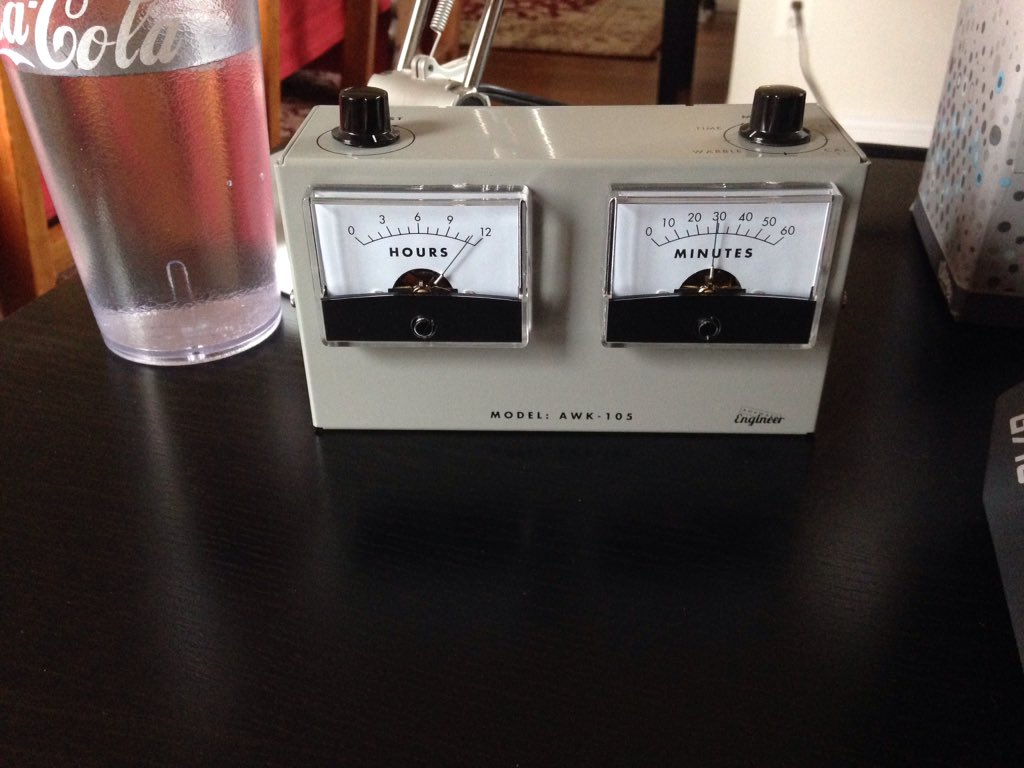
Photos/Customer Pics/clock and coca-cola.jpg
