awkwardengineer/Clock/Photos/Customer Pics/IMG_20151218_141032602.jpg

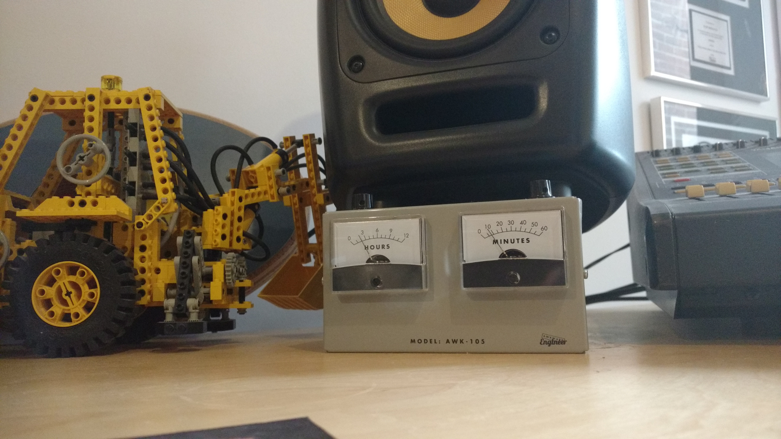
Photos/Customer Pics/IMG_20151218_141032602.jpg
