awkwardengineer/Clock/Photos/Customer Pics/launch2.jpg

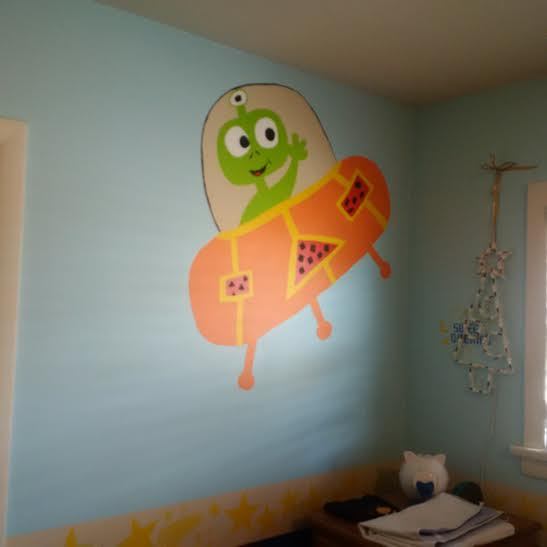
Photos/Customer Pics/launch2.jpg
