awkwardengineer/Clock/Photos/Customer Pics/leather.jpg

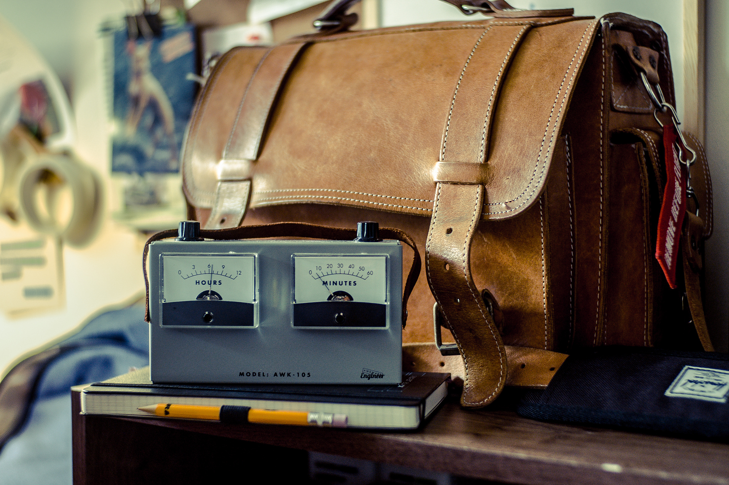
Photos/Customer Pics/leather.jpg
