awkwardengineer/Clock/Photos/Customer Pics/unposted pics/12473788_10154740270178206_92843413550761521_o.jpg

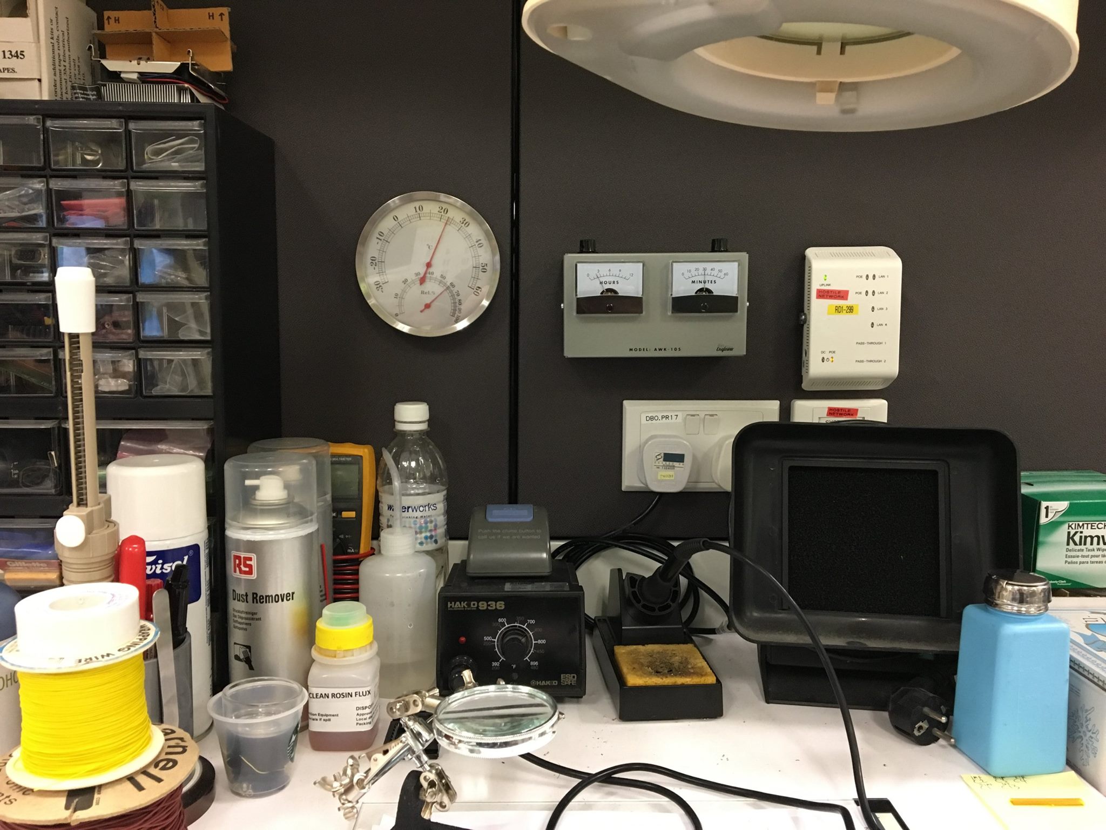
Photos/Customer Pics/unposted pics/12473788_10154740270178206_92843413550761521_o.jpg
