awkwardengineer/Clock/Photos/Customer Pics/unposted pics/IMG_1218.JPG

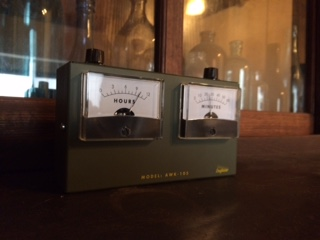
Photos/Customer Pics/unposted pics/IMG_1218.JPG
