awkwardengineer/Clock/Photos/Customer Pics/unposted pics/IMG_2800.jpg

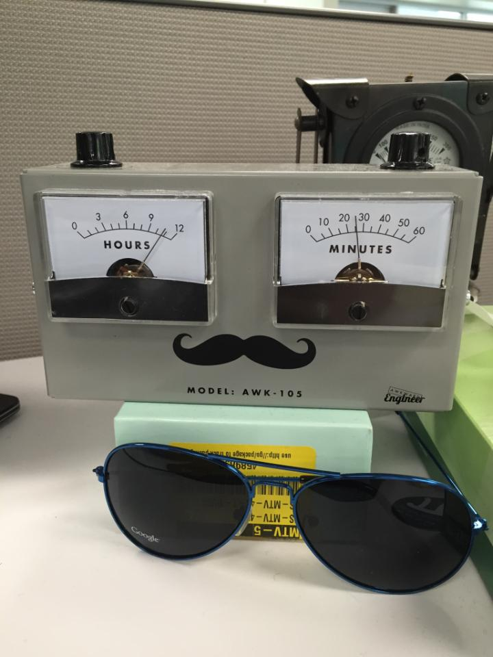
Photos/Customer Pics/unposted pics/IMG_2800.jpg
