awkwardengineer/Clock/Photos/Customer Pics/unposted pics/IMG_8957.JPG

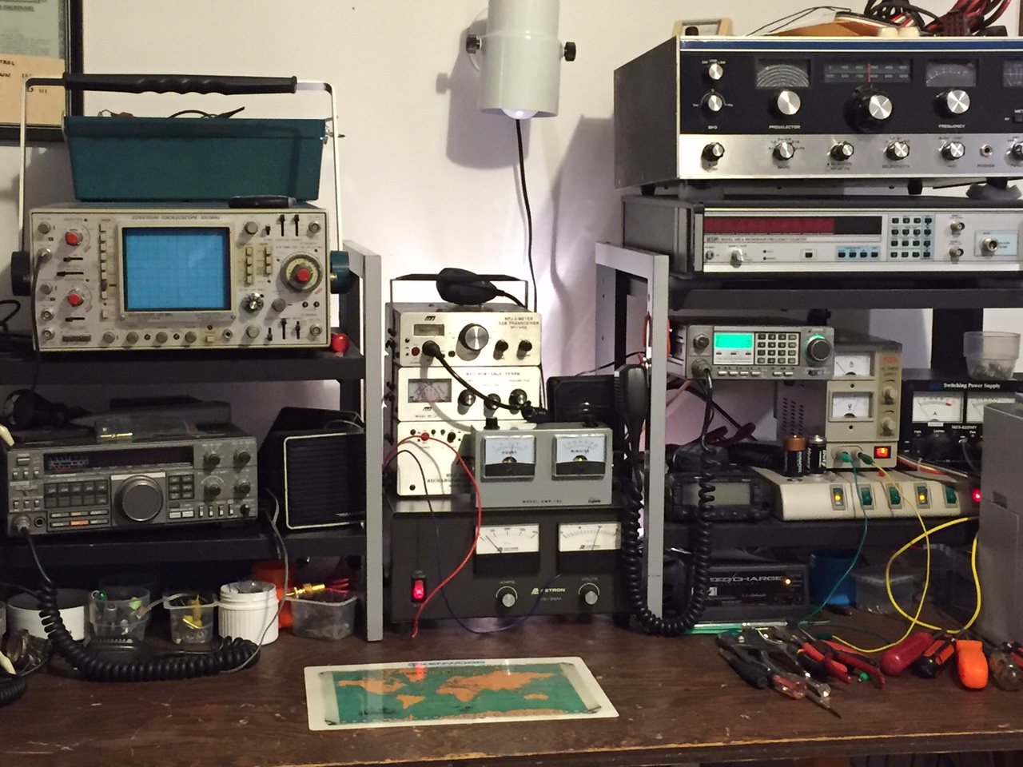
Photos/Customer Pics/unposted pics/IMG_8957.JPG
