awkwardengineer/Clock/Photos/Dial Designs for Backer Updates/baseline.png

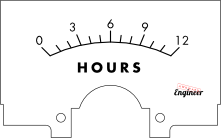
Photos/Dial Designs for Backer Updates/baseline.png
