awkwardengineer/Clock/Photos/Dial Designs for Backer Updates/case colors.png

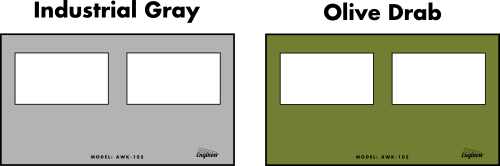
Photos/Dial Designs for Backer Updates/case colors.png
