awkwardengineer/Clock/Photos/Dial Designs for Backer Updates/concept A.png

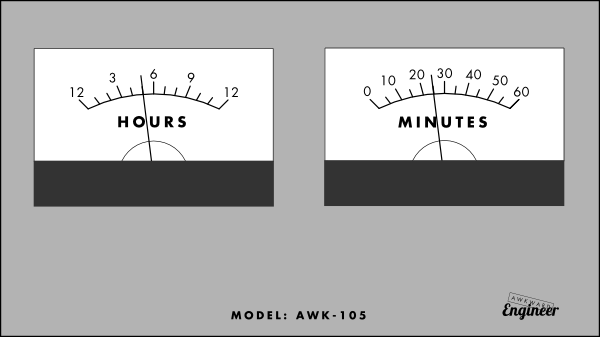
Photos/Dial Designs for Backer Updates/concept A.png
