awkwardengineer/Clock/Photos/Dial Designs for Backer Updates/hours_concepts.png

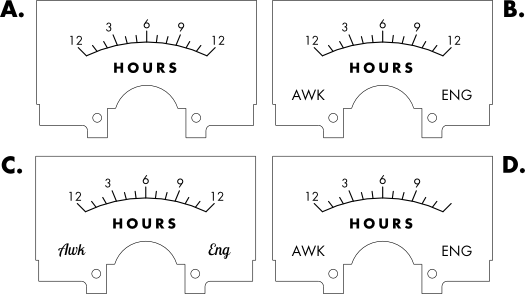
Photos/Dial Designs for Backer Updates/hours_concepts.png
