awkwardengineer/Clock/Photos/Dial Designs for Backer Updates/minutes_concepts.png

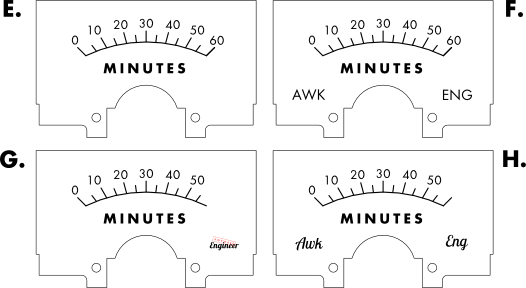
Photos/Dial Designs for Backer Updates/minutes_concepts.png
