awkwardengineer/Clock/Photos/Facebook/clock ad 1.png

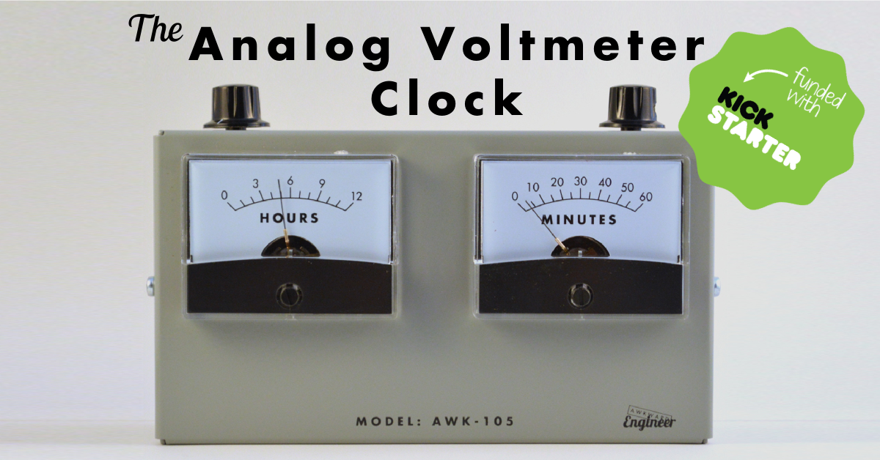
Photos/Facebook/clock ad 1.png
