awkwardengineer/Clock/Photos/Facebook/clock ad 2.png

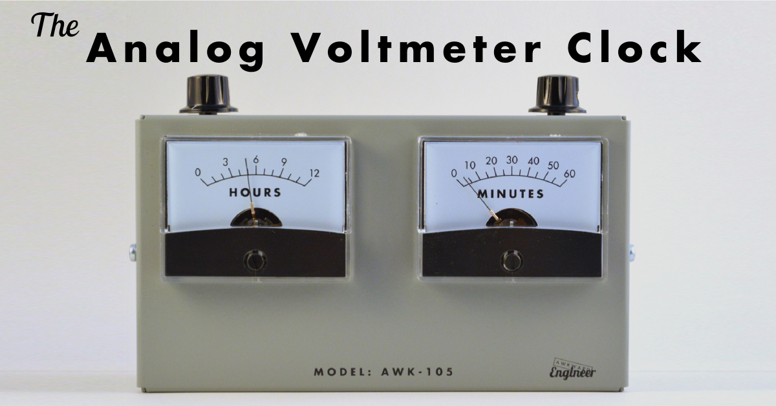
Photos/Facebook/clock ad 2.png
