awkwardengineer/Clock/Photos/Facebook/clock ad 4.png

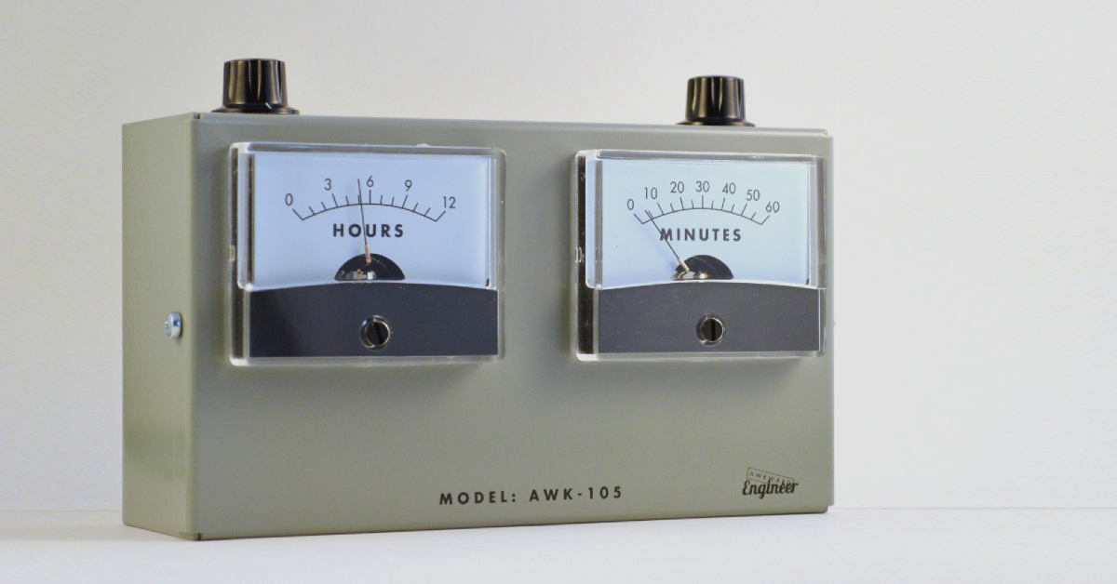
Photos/Facebook/clock ad 4.png
