awkwardengineer/Clock/Photos/Facebook/clock ad 5.png

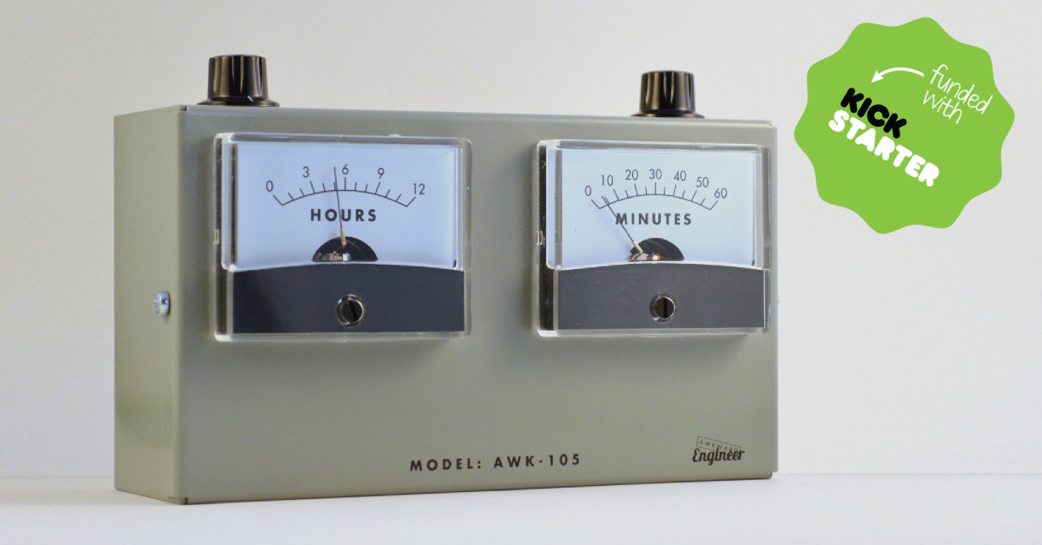
Photos/Facebook/clock ad 5.png
