awkwardengineer/Clock/Photos/Facebook/goog 1.jpg

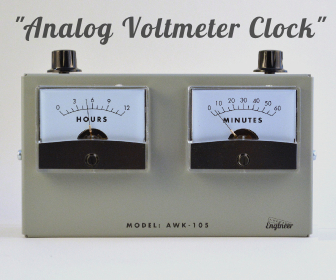
Photos/Facebook/goog 1.jpg
