awkwardengineer/Clock/Photos/Facebook/goog 2.png

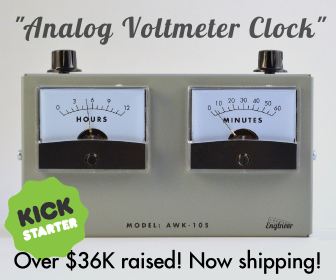
Photos/Facebook/goog 2.png
