awkwardengineer/Clock/Photos/Facebook/goog_1.JPG

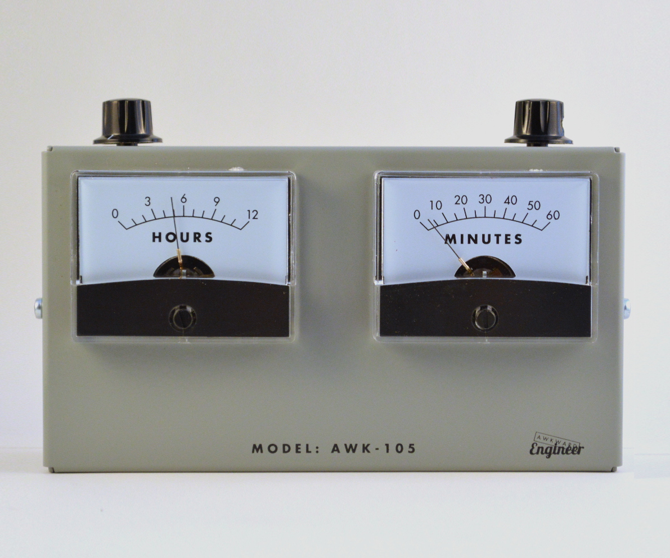
Photos/Facebook/goog_1.JPG
