awkwardengineer/Clock/Photos/Facebook/kickstarter_funded.png

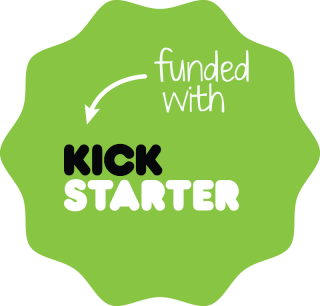
Photos/Facebook/kickstarter_funded.png
