awkwardengineer/Clock/Photos/Facebook/science.jpg

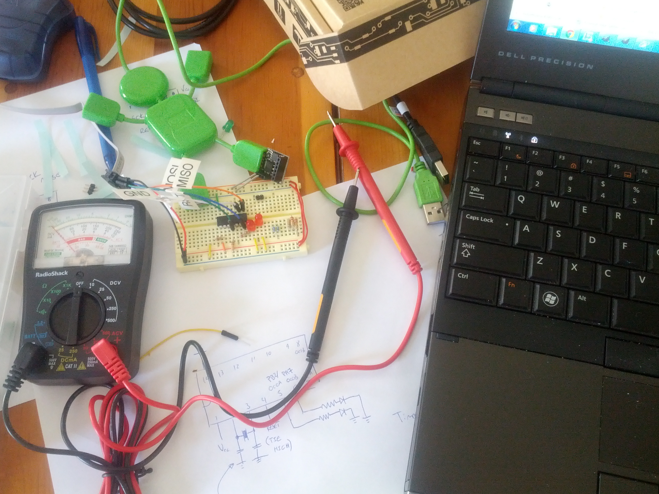
Photos/Facebook/science.jpg
