awkwardengineer/Clock/Photos/Facebook/wtf.jpg

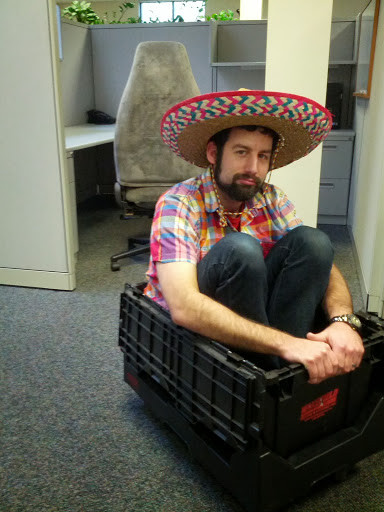
Photos/Facebook/wtf.jpg
