awkwardengineer/Clock/Photos/Meter Communications/20151102_094958.jpg

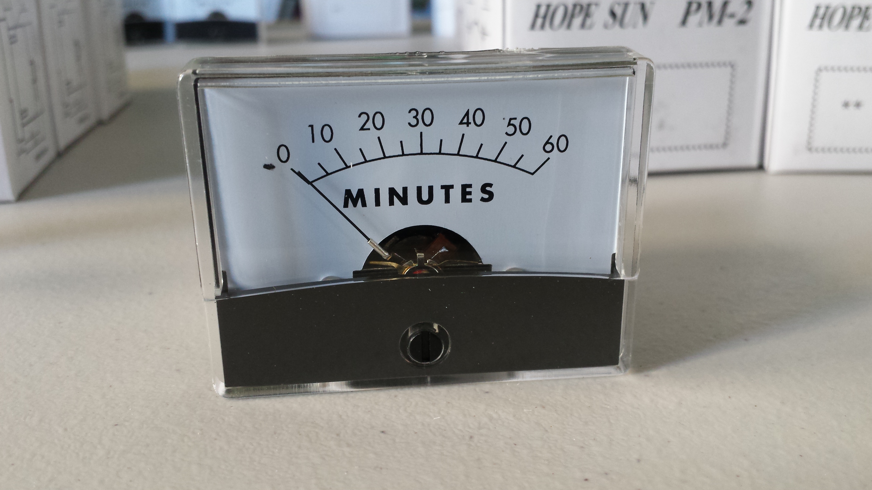
Photos/Meter Communications/20151102_094958.jpg
