awkwardengineer/Clock/Photos/Meter Communications/20151102_095239.jpg

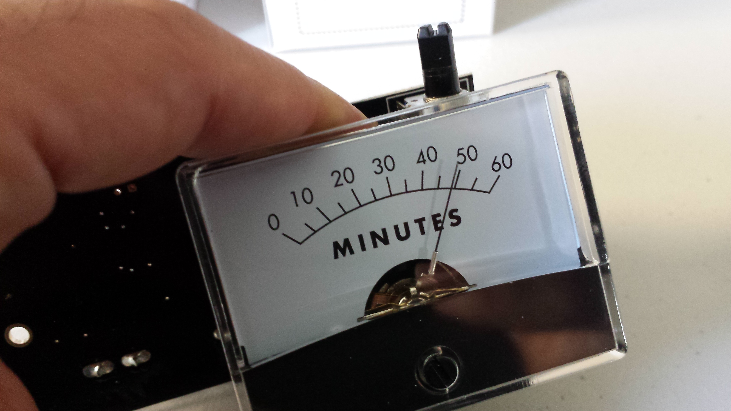
Photos/Meter Communications/20151102_095239.jpg
