awkwardengineer/Clock/Photos/Meter Communications/20160421_092021.jpg

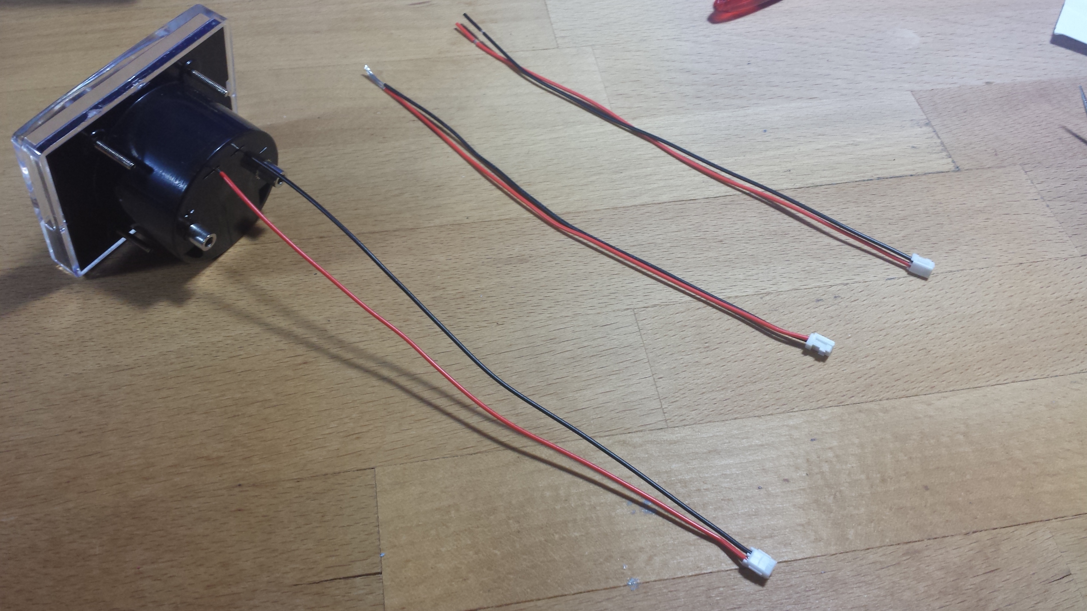
Photos/Meter Communications/20160421_092021.jpg
