awkwardengineer/Clock/Photos/Meter Communications/bulk pack carton.jpg

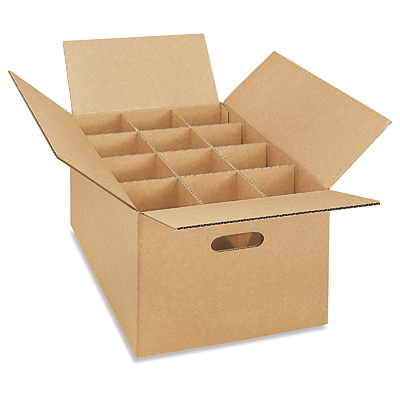
Photos/Meter Communications/bulk pack carton.jpg
