awkwardengineer/Clock/Photos/Meter Communications/bulk pack request.png

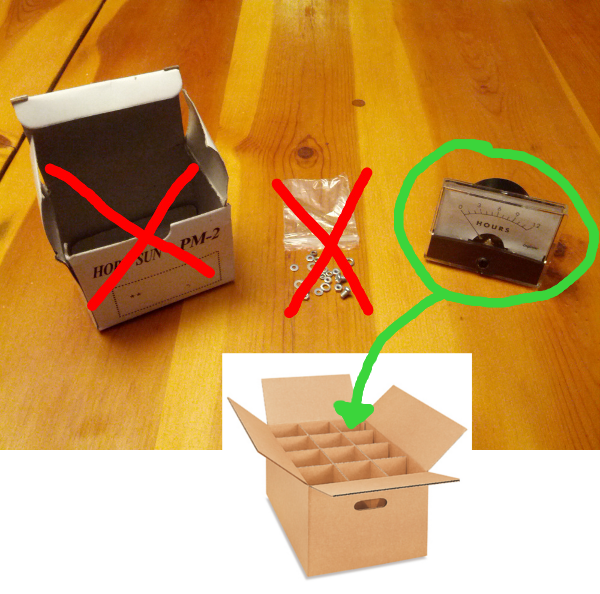
Photos/Meter Communications/bulk pack request.png
