awkwardengineer/Clock/Photos/Meter Communications/IMG_20150117_212509.jpg

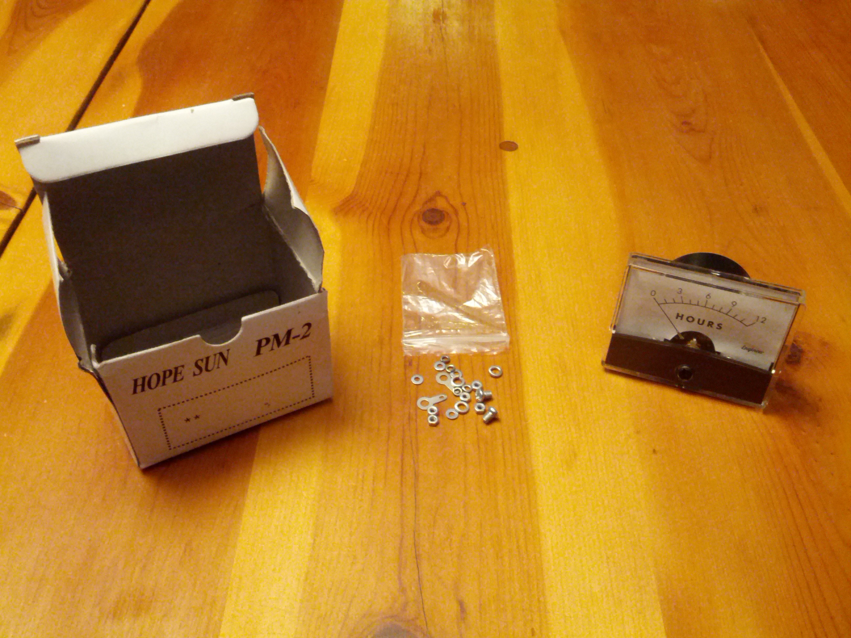
Photos/Meter Communications/IMG_20150117_212509.jpg
