awkwardengineer/Clock/Photos/Meter Communications/meter crop.jpg

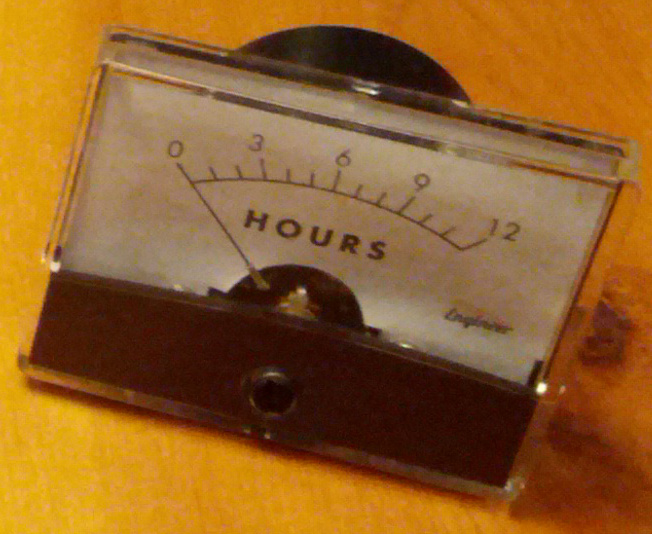
Photos/Meter Communications/meter crop.jpg
