awkwardengineer/Clock/Photos/Meter Communications/scale_alignment_quality.png

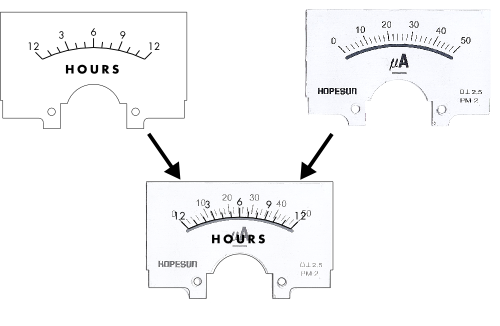
Photos/Meter Communications/scale_alignment_quality.png
