awkwardengineer/Clock/Photos/Meter Communications/scale_explanation.png

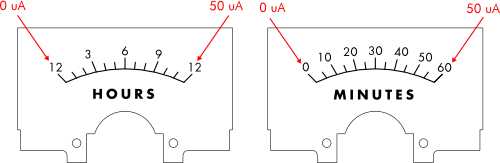
Photos/Meter Communications/scale_explanation.png
