awkwardengineer/Clock/Photos/Meter Communications/screwdriver.jpg

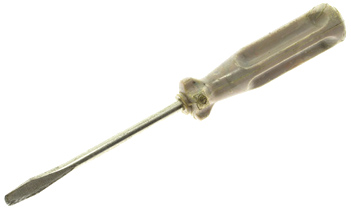
Photos/Meter Communications/screwdriver.jpg
