awkwardengineer/Clock/Photos/Meter Communications/shorter thread.jpg

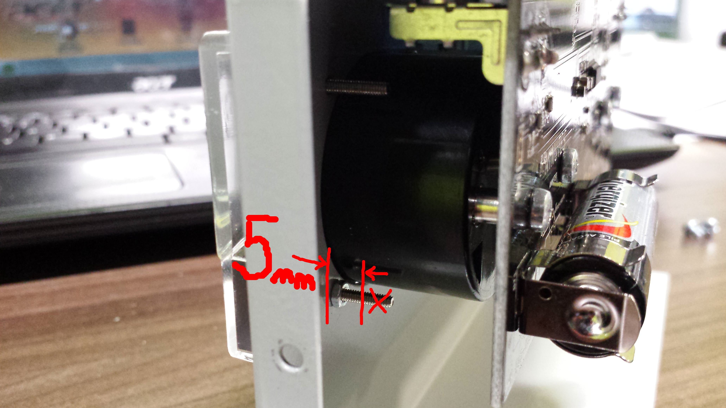
Photos/Meter Communications/shorter thread.jpg
