awkwardengineer/Clock/Photos/Painting/20150825_132055.jpg

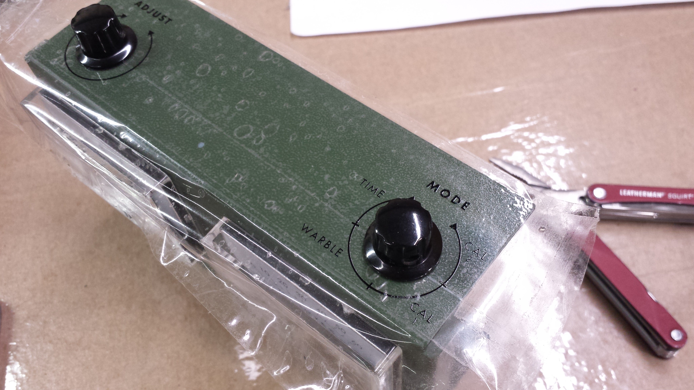
Photos/Painting/20150825_132055.jpg
