awkwardengineer/Clock/Photos/Painting/20150825_132628.jpg

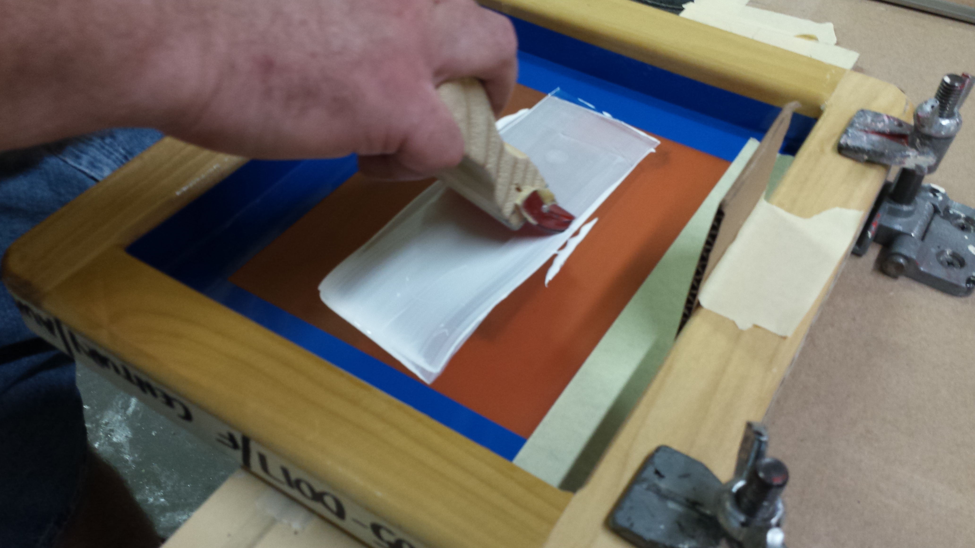
Photos/Painting/20150825_132628.jpg
