awkwardengineer/Clock/Photos/Painting/20150825_135141.jpg

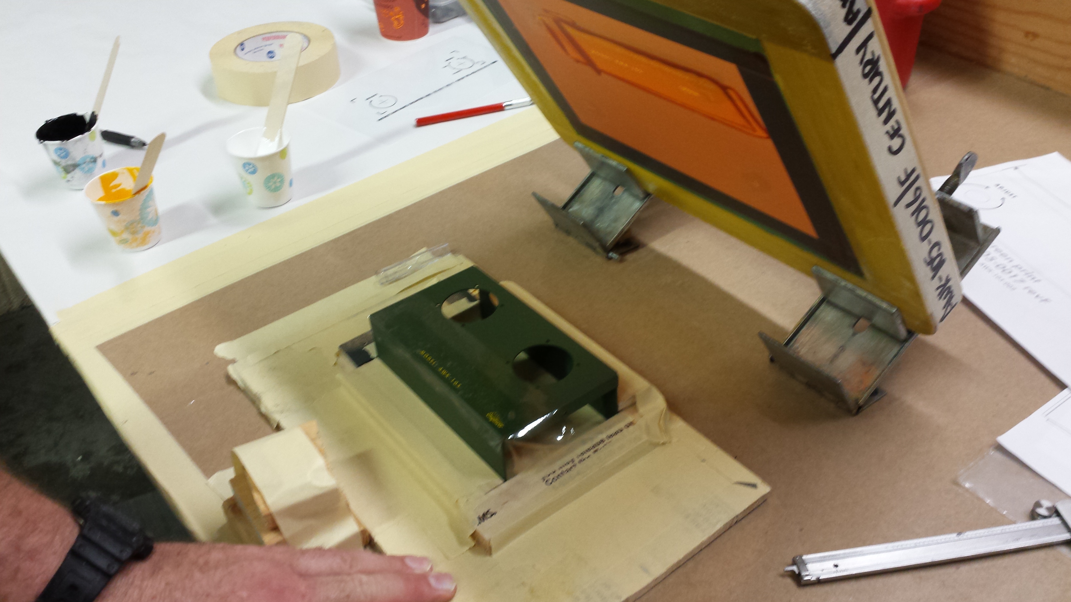
Photos/Painting/20150825_135141.jpg
