awkwardengineer/Clock/Photos/Painting/20150825_135424.jpg

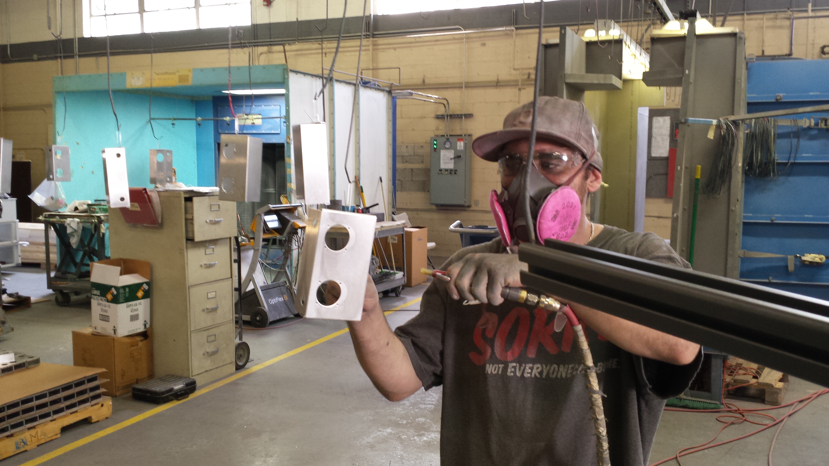
Photos/Painting/20150825_135424.jpg
