awkwardengineer/Clock/Photos/Painting/20150825_135453.jpg

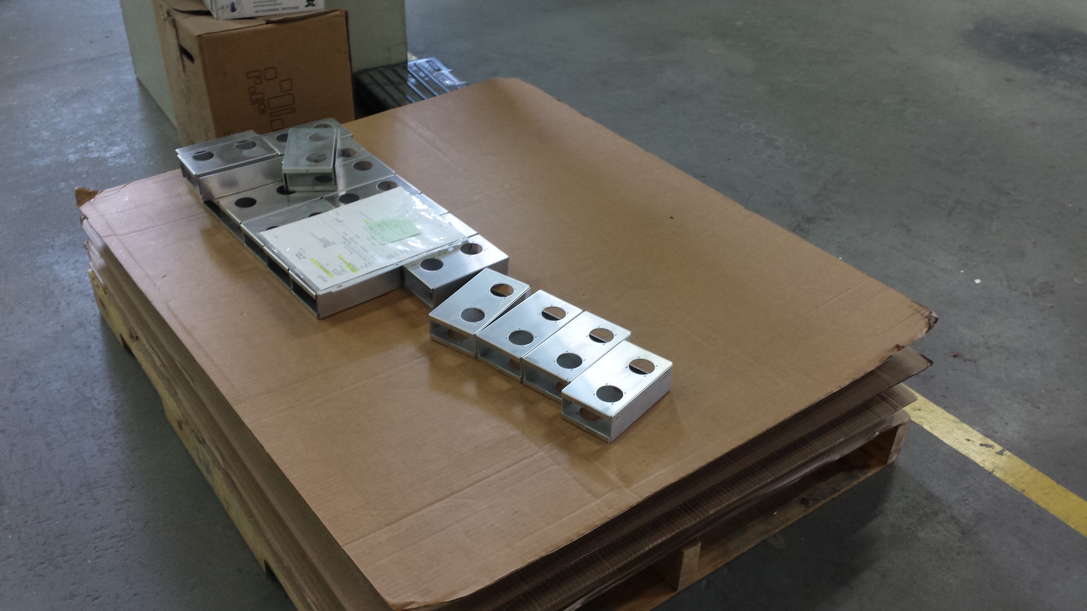
Photos/Painting/20150825_135453.jpg
