awkwardengineer/Clock/Photos/Painting/20150825_135511.jpg

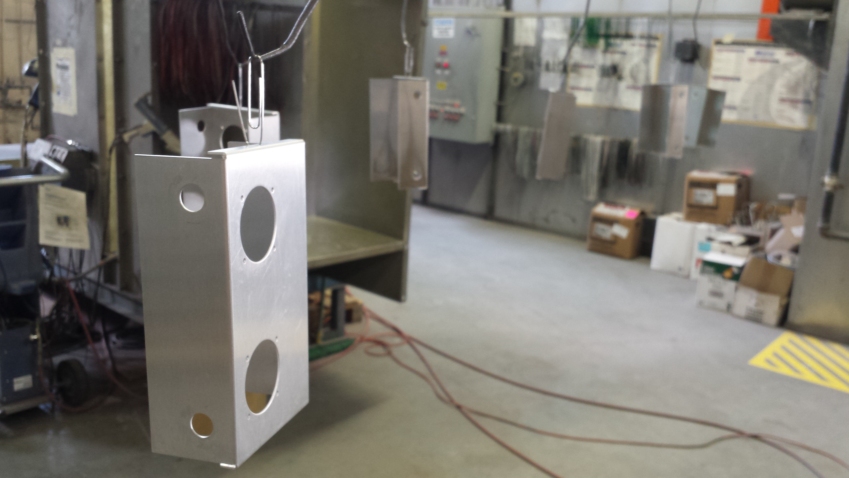
Photos/Painting/20150825_135511.jpg
