awkwardengineer/Clock/Photos/Painting/20150825_135517.jpg

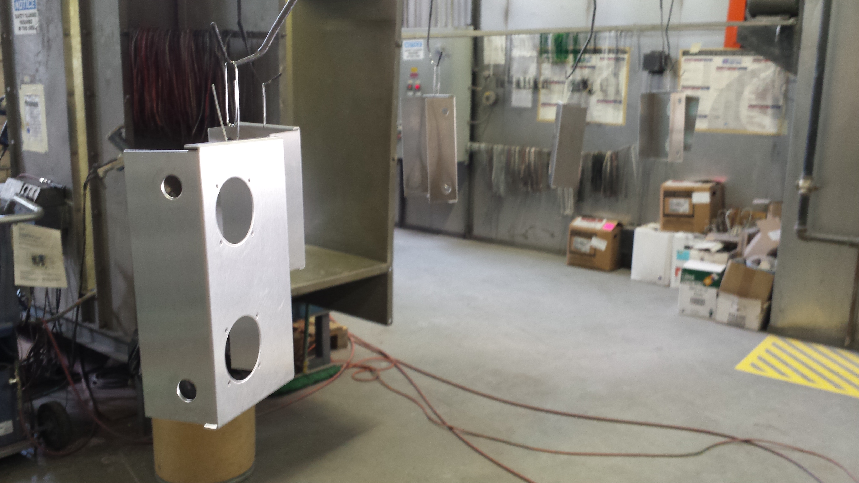
Photos/Painting/20150825_135517.jpg
