awkwardengineer/Clock/Photos/Painting/20150825_140420.jpg

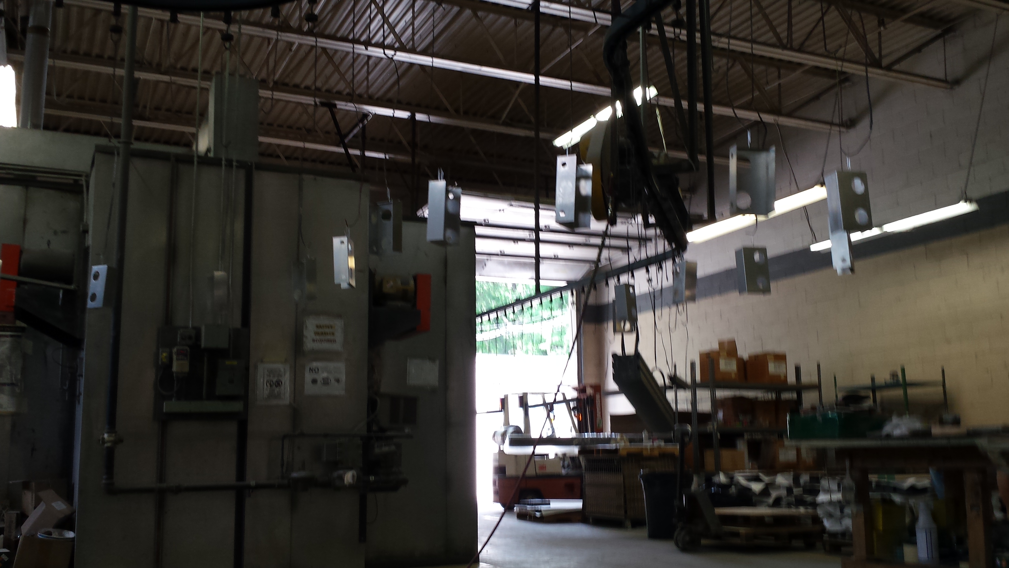
Photos/Painting/20150825_140420.jpg
