awkwardengineer/Clock/Photos/Painting/20150825_140557.jpg

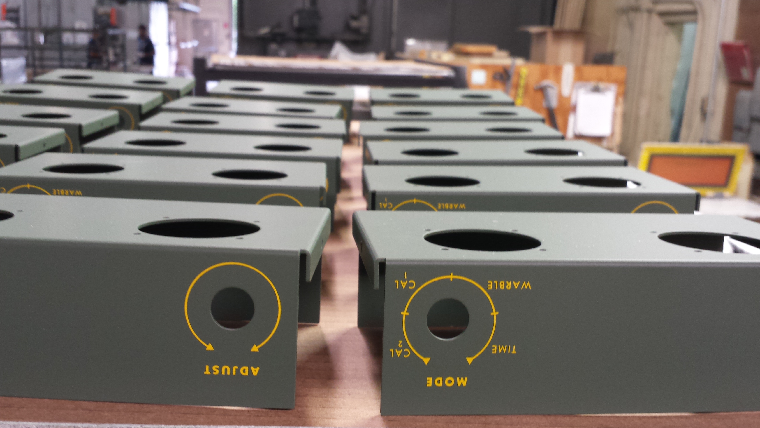
Photos/Painting/20150825_140557.jpg
