awkwardengineer/Clock/Photos/Painting/20150825_140642.jpg

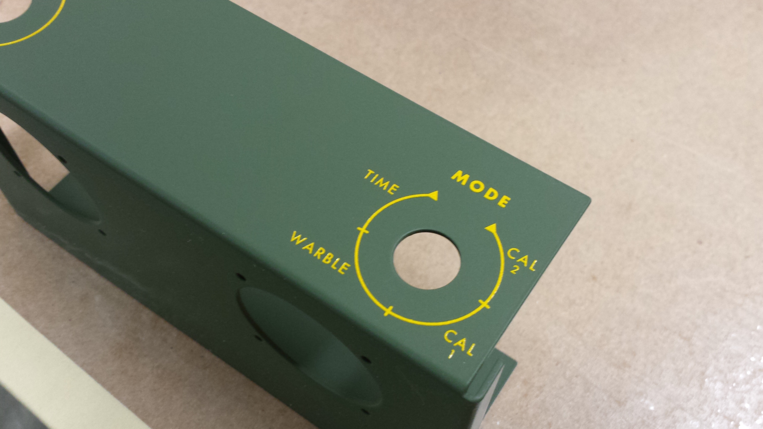
Photos/Painting/20150825_140642.jpg
