awkwardengineer/Clock/Photos/Raw/20150322_172100.jpg

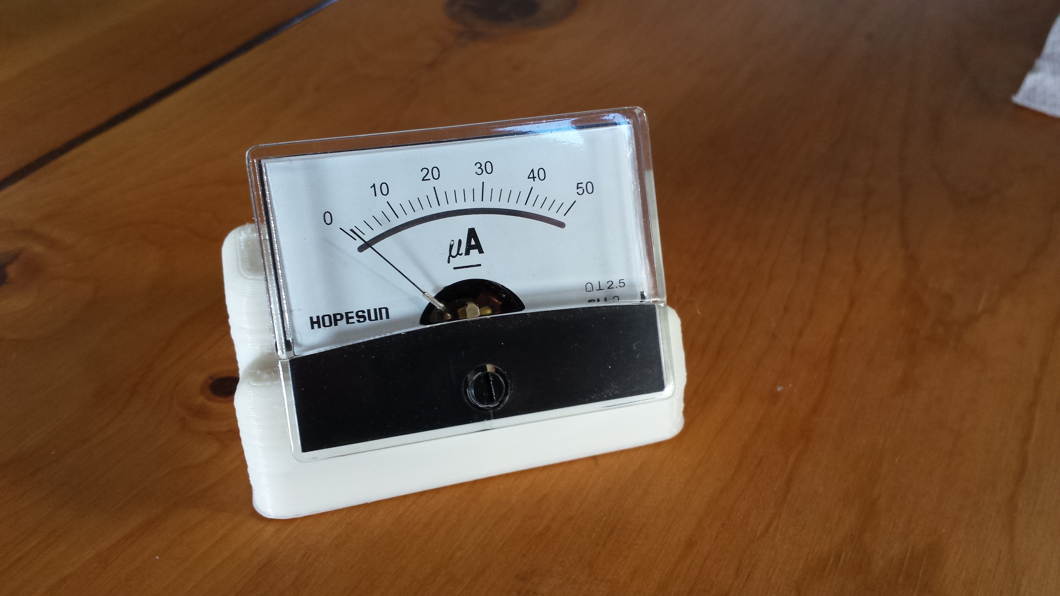
Photos/Raw/20150322_172100.jpg
