awkwardengineer/Clock/Photos/Raw/20150503_134743.jpg

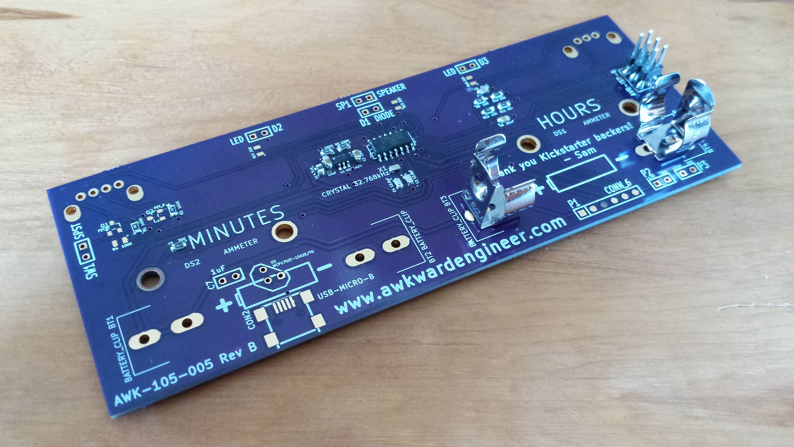
Photos/Raw/20150503_134743.jpg
