awkwardengineer/Clock/Photos/Raw/20150503_135845.jpg

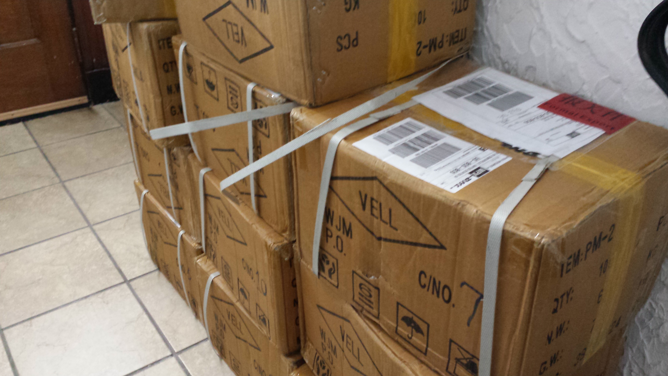
Photos/Raw/20150503_135845.jpg
