awkwardengineer/Clock/Photos/Raw/20150518_184042.jpg

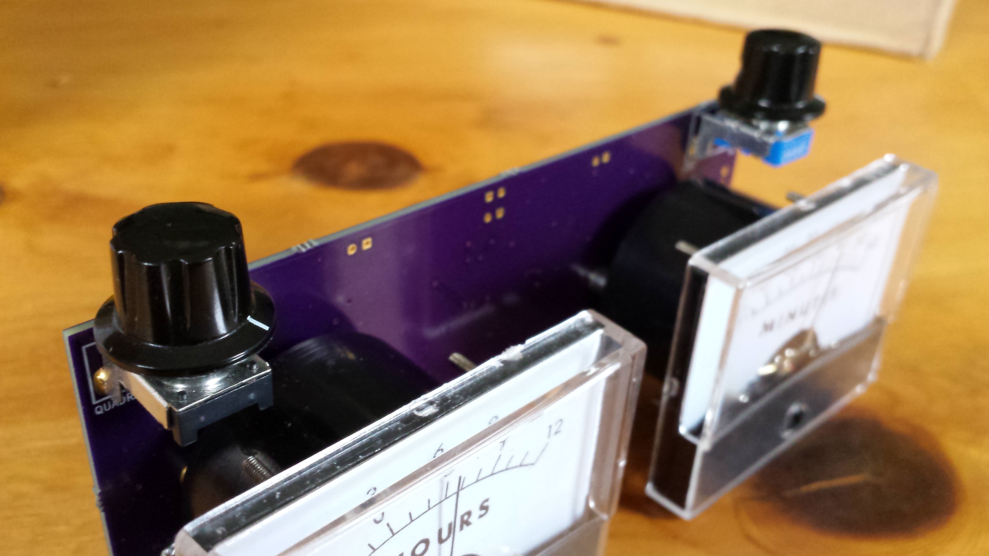
Photos/Raw/20150518_184042.jpg
