awkwardengineer/Clock/Photos/Raw/20150611_153450.jpg

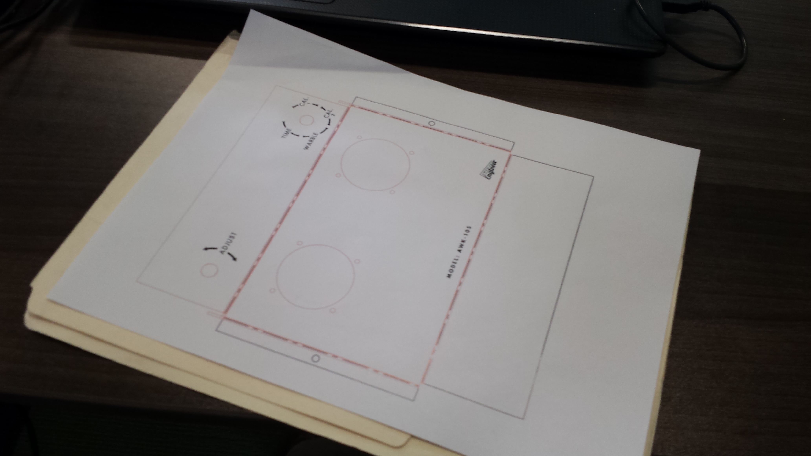
Photos/Raw/20150611_153450.jpg
