awkwardengineer/Clock/Photos/Raw/20150623_145908.jpg

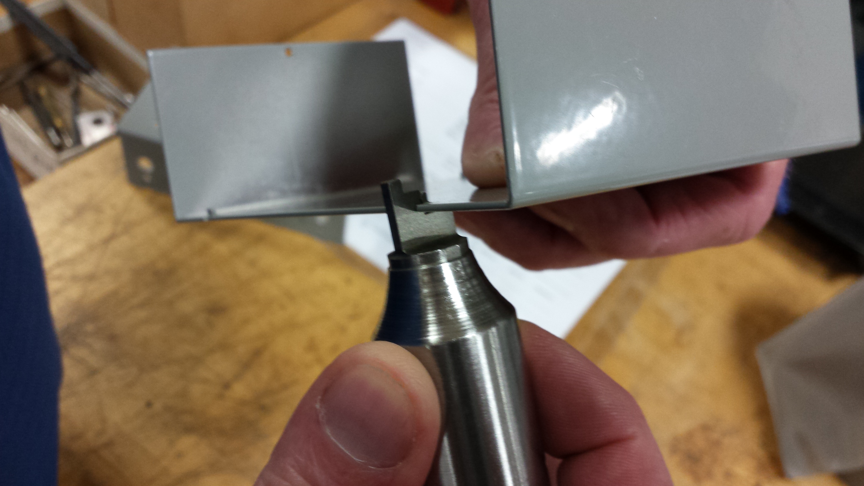
Photos/Raw/20150623_145908.jpg
