awkwardengineer/Clock/Photos/Raw/20150623_145926.jpg

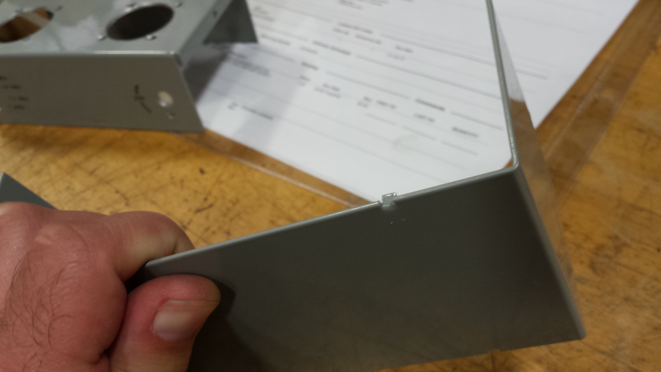
Photos/Raw/20150623_145926.jpg
