awkwardengineer/Clock/Photos/Raw/20150623_145947.jpg

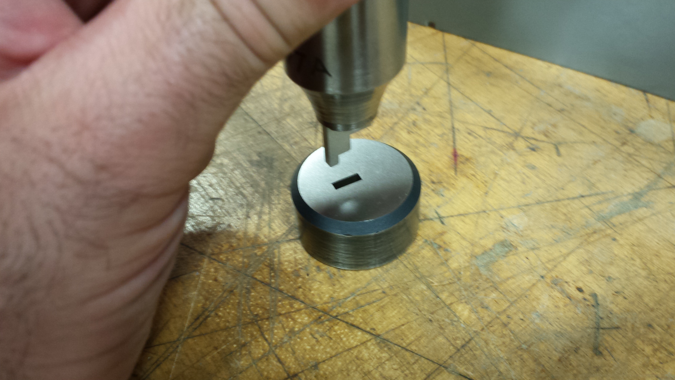
Photos/Raw/20150623_145947.jpg
