awkwardengineer/Clock/Photos/Raw/20150702_162255.jpg

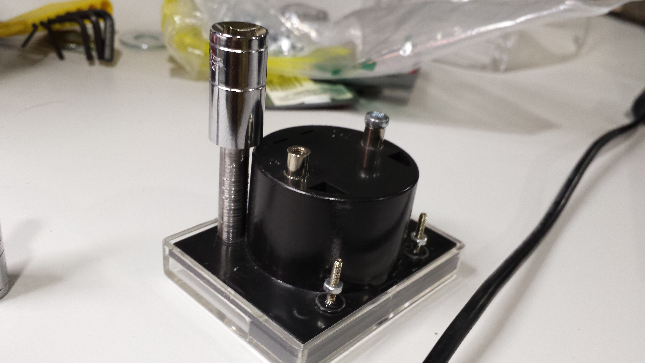
Photos/Raw/20150702_162255.jpg
