awkwardengineer/Clock/Photos/Raw/20150715_215624_1_bestshot.jpg

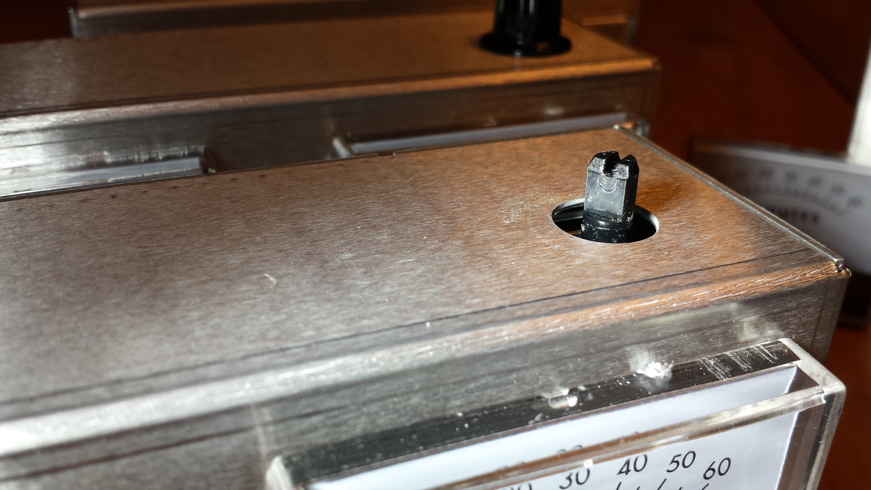
Photos/Raw/20150715_215624_1_bestshot.jpg
