awkwardengineer/Clock/Photos/Raw/20150715_215901.jpg

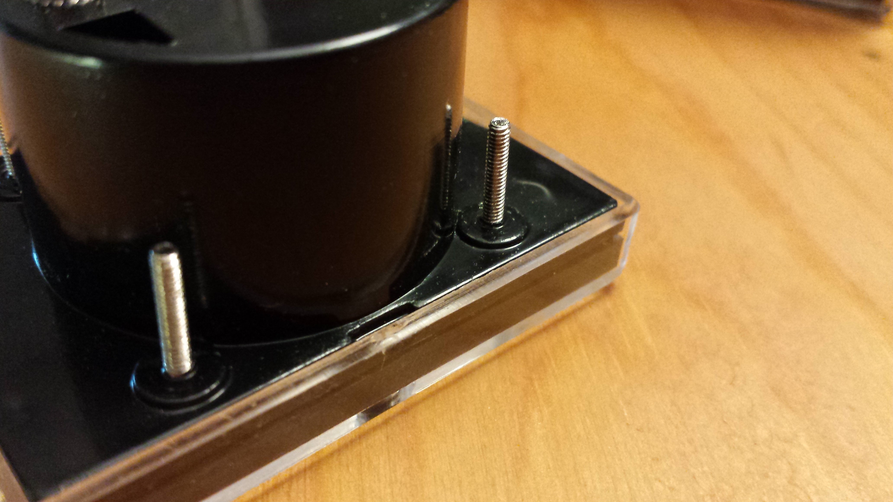
Photos/Raw/20150715_215901.jpg
