awkwardengineer/Clock/Photos/Raw/20151026_153911.png

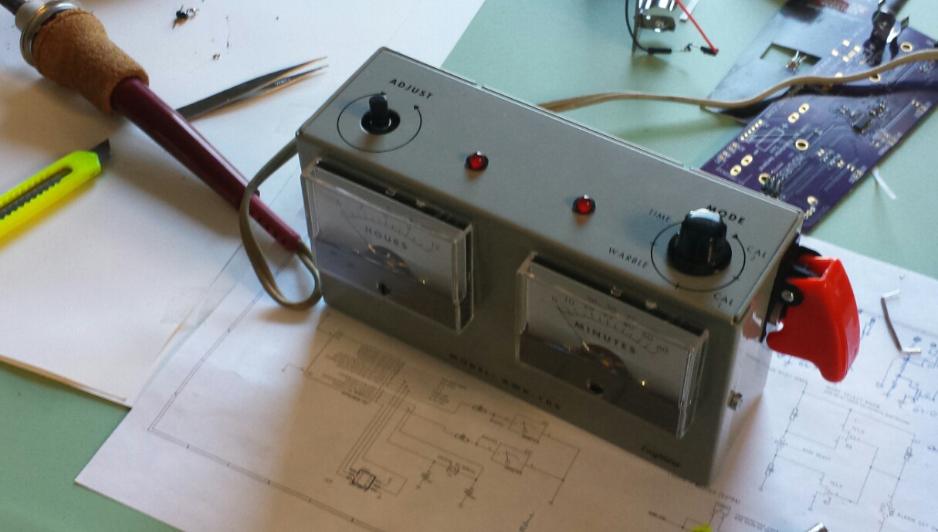
Photos/Raw/20151026_153911.png
