awkwardengineer/Clock/Photos/Raw/board layout.PNG

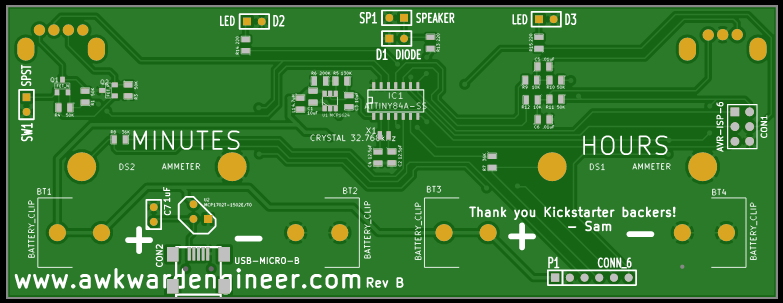
Photos/Raw/board layout.PNG
