awkwardengineer/Clock/Photos/Raw/board_meter_interface.jpg

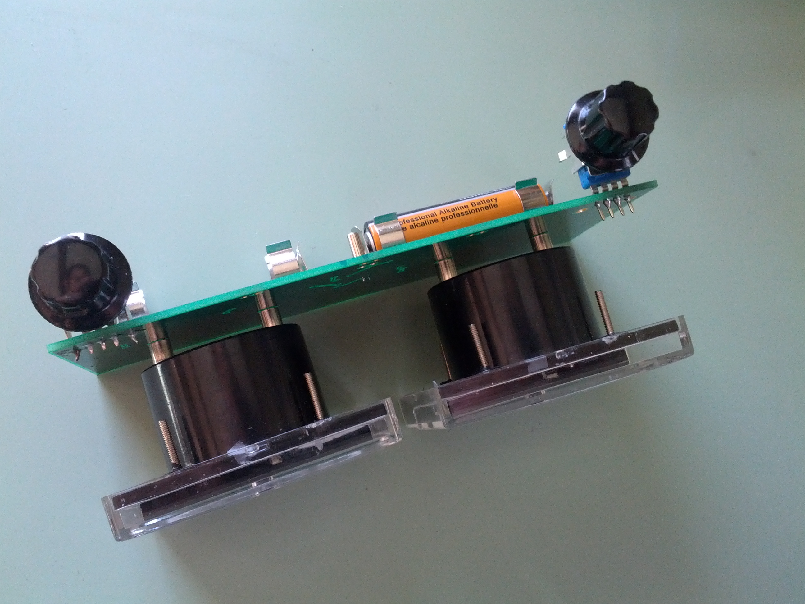
Photos/Raw/board_meter_interface.jpg
