awkwardengineer/Clock/Photos/Raw/board_meters_on.jpg

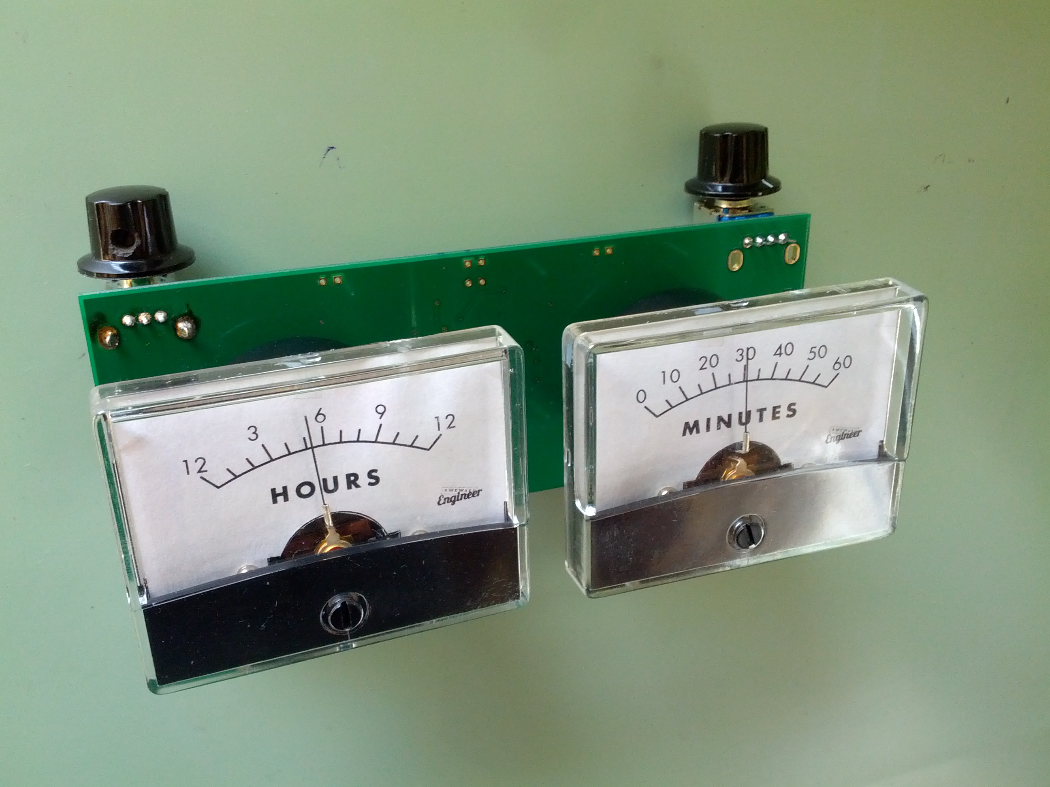
Photos/Raw/board_meters_on.jpg
