awkwardengineer/Clock/Photos/Raw/footprint.PNG

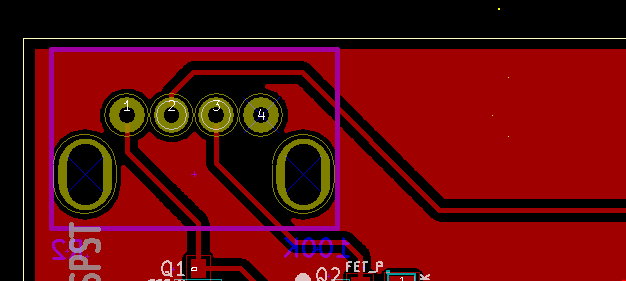
Photos/Raw/footprint.PNG
