awkwardengineer/Clock/Photos/Raw/IMG_20150103_105238.jpg

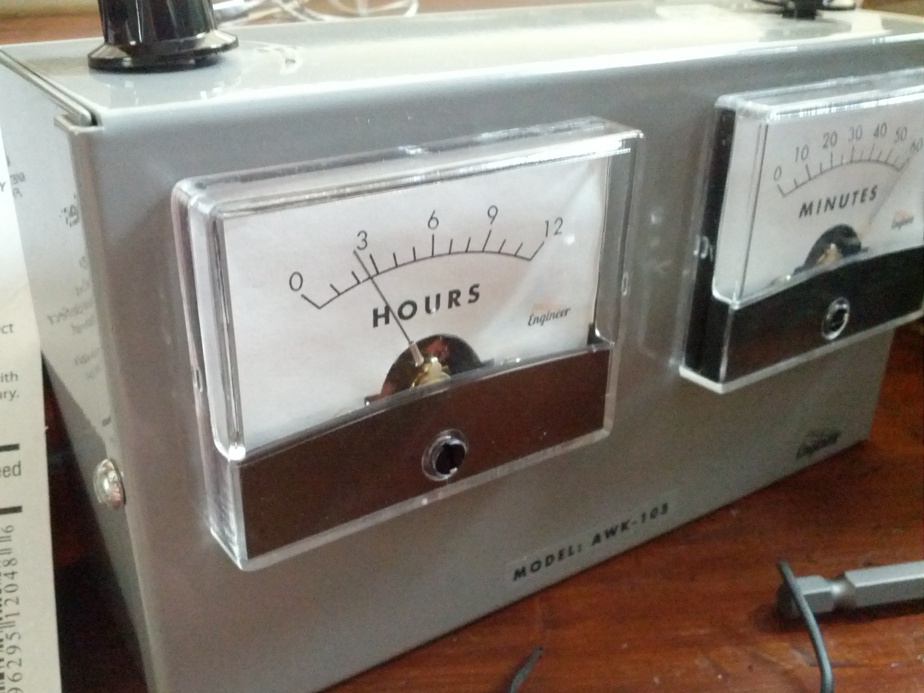
Photos/Raw/IMG_20150103_105238.jpg
