awkwardengineer/Clock/Photos/Raw/IMG_20150115_111529.jpg

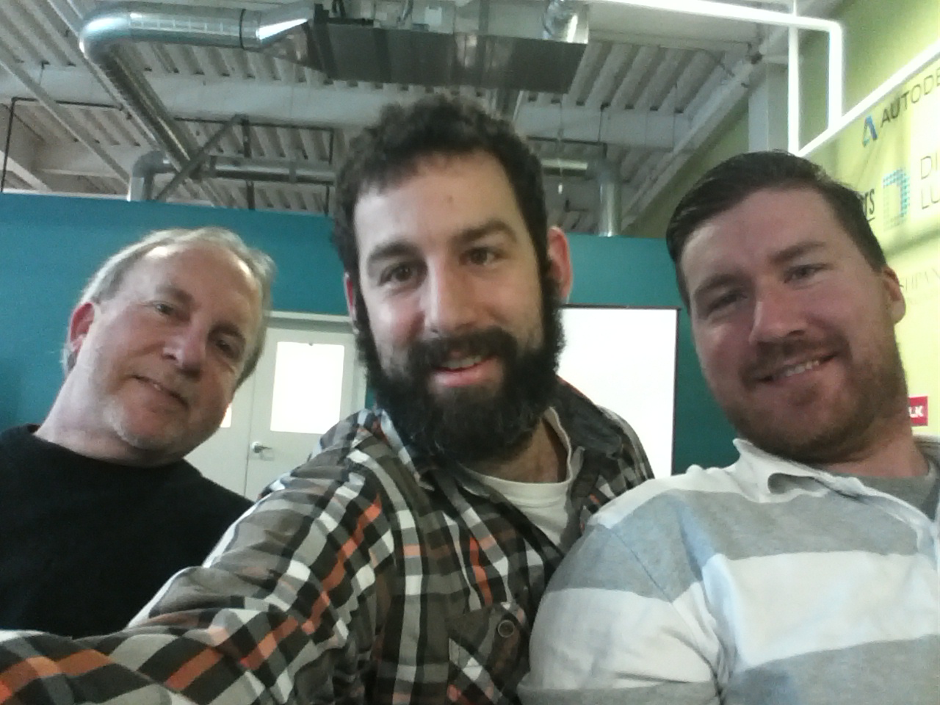
Photos/Raw/IMG_20150115_111529.jpg
