awkwardengineer/Clock/Photos/Raw/IMG_20150117_133323.jpg

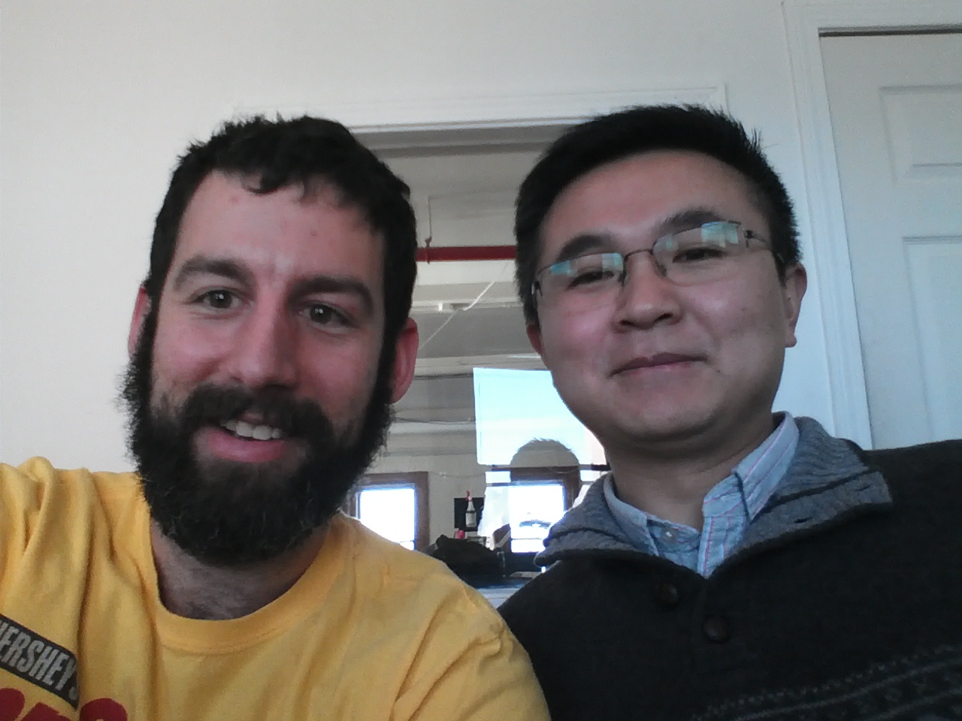
Photos/Raw/IMG_20150117_133323.jpg
