awkwardengineer/Clock/Photos/Raw/IMG_20150129_182523.jpg

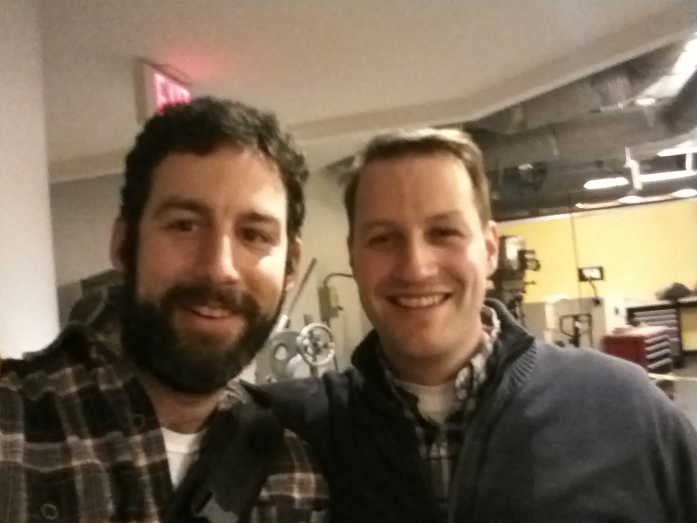
Photos/Raw/IMG_20150129_182523.jpg
