awkwardengineer/Clock/Photos/Raw/knob sample.JPG

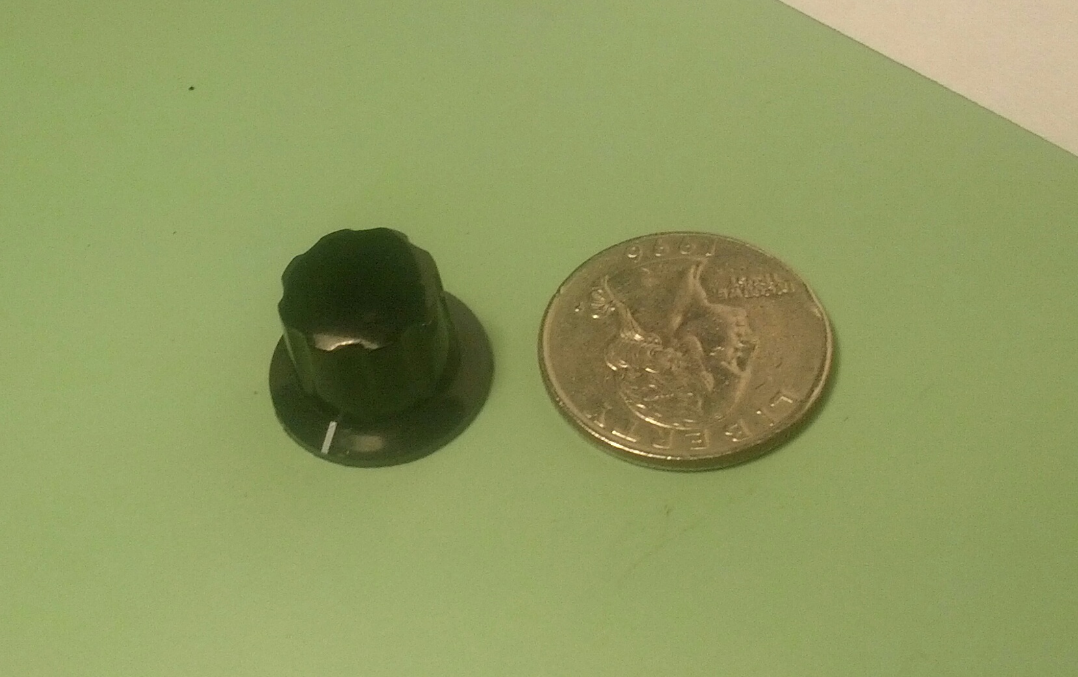
Photos/Raw/knob sample.JPG
