awkwardengineer/Clock/Photos/Raw/packaging planning.jpg

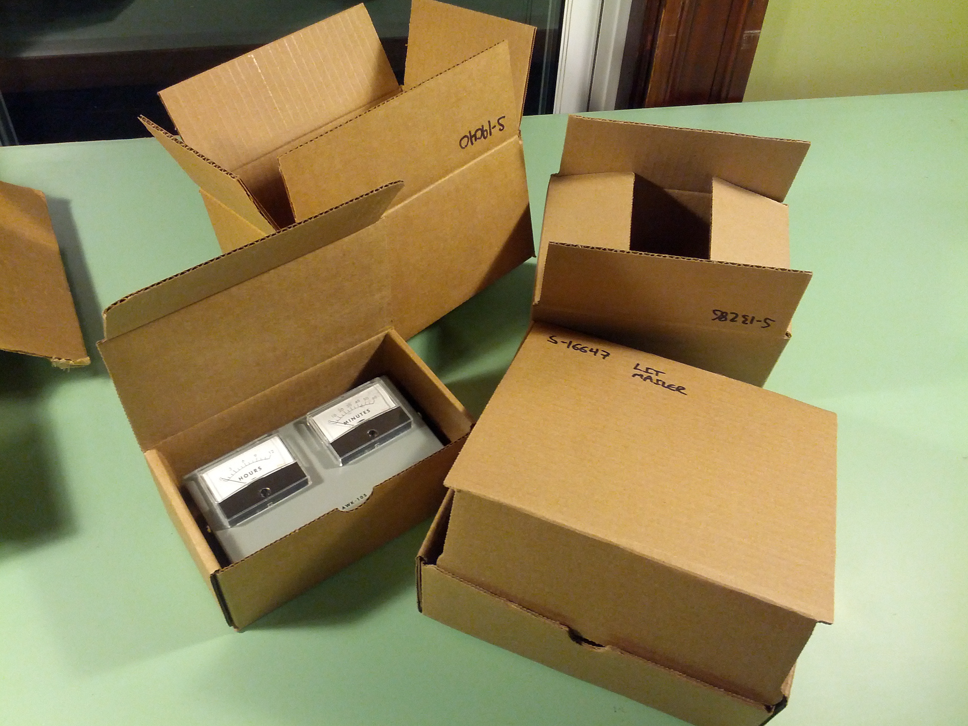
Photos/Raw/packaging planning.jpg
