awkwardengineer/Clock/Photos/Raw/PM-2 50UA 1.JPG

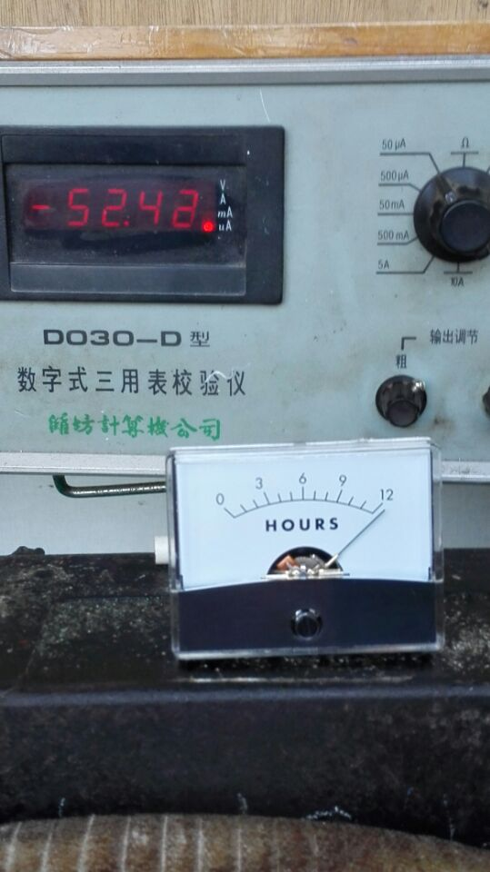
Photos/Raw/PM-2 50UA 1.JPG
