awkwardengineer/Clock/Photos/Raw/PM-2 50UA 2.JPG

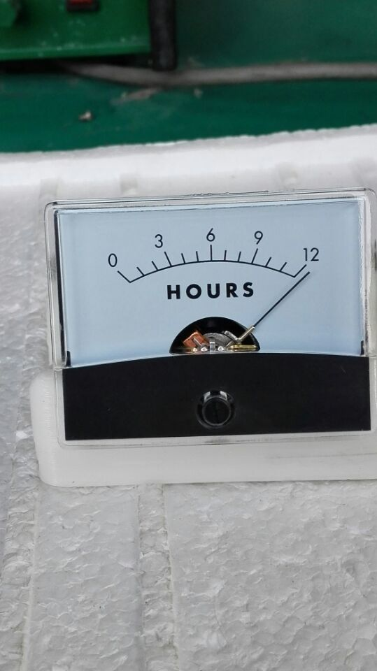
Photos/Raw/PM-2 50UA 2.JPG
