awkwardengineer/Clock/Photos/Raw/powder coat house.jpg

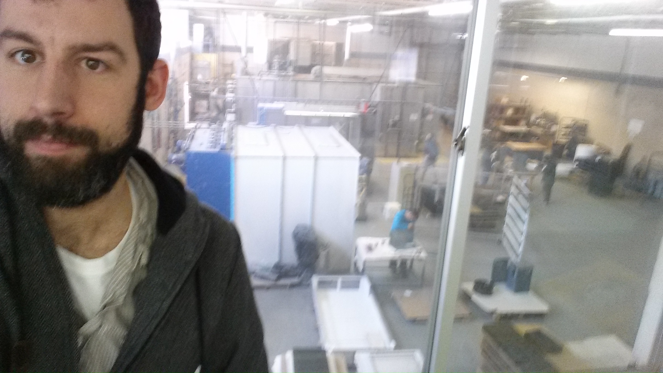
Photos/Raw/powder coat house.jpg
