awkwardengineer/Clock/Photos/Raw/set screw.PNG

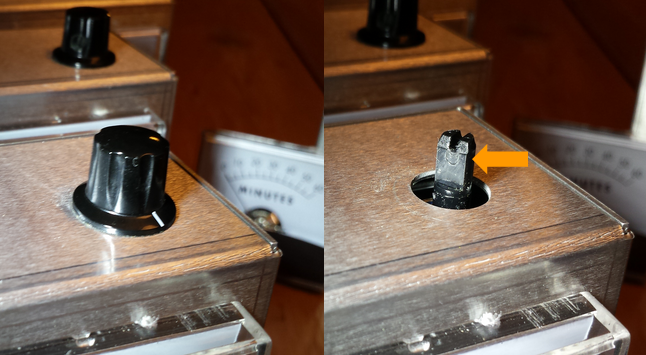
Photos/Raw/set screw.PNG
