awkwardengineer/Clock/Photos/Raw/translation.PNG

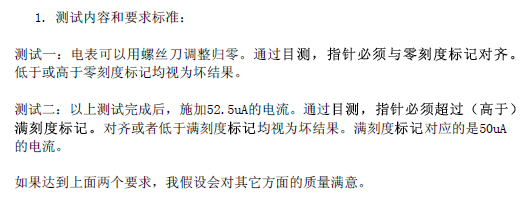
Photos/Raw/translation.PNG
