awkwardengineer/Clock/Photos/Retouched/AWK-105_500px.jpg

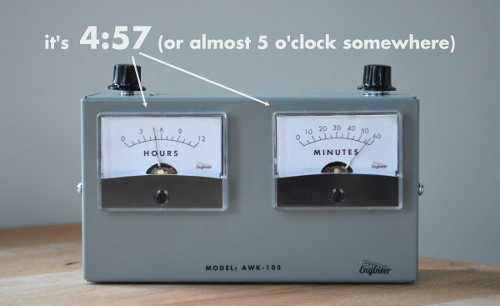
Photos/Retouched/AWK-105_500px.jpg
