awkwardengineer/Clock/Photos/Retouched/AWK-105AL left cover.JPG

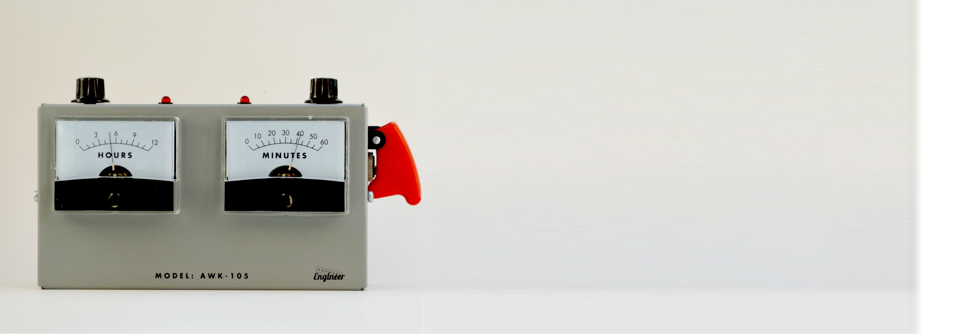
Photos/Retouched/AWK-105AL left cover.JPG
