awkwardengineer/Clock/Photos/Retouched/AWK-105AL-GR2.JPG

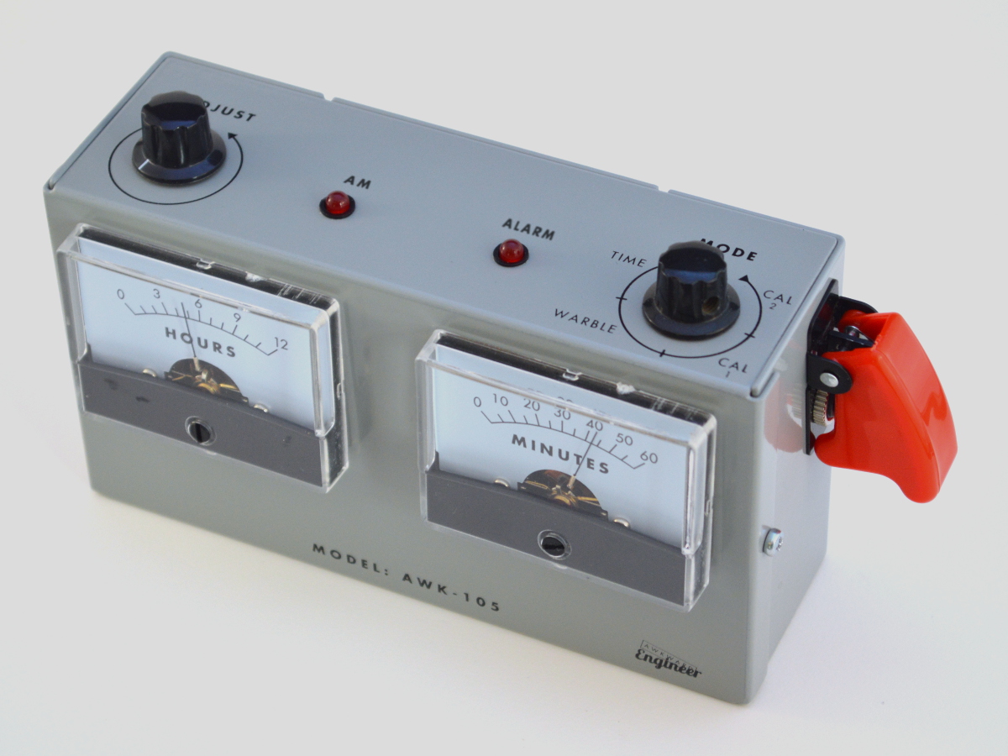
Photos/Retouched/AWK-105AL-GR2.JPG
