awkwardengineer/Clock/Photos/Retouched/AWK-105GR_3.JPG

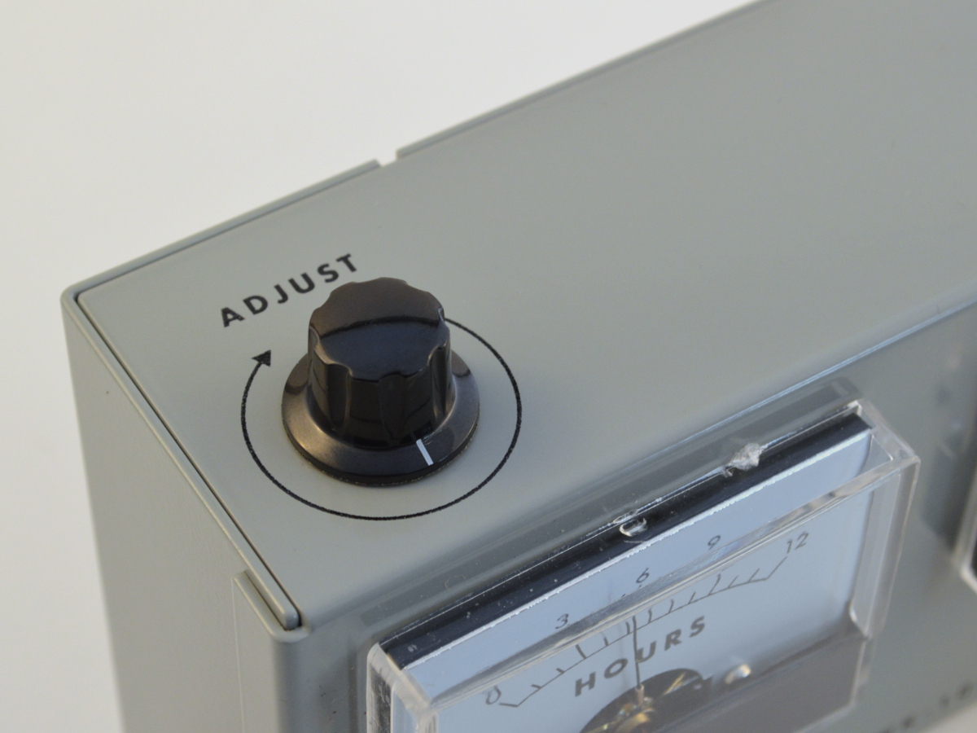
Photos/Retouched/AWK-105GR_3.JPG
