awkwardengineer/Clock/Photos/Retouched/AWK-105GR_4.JPG

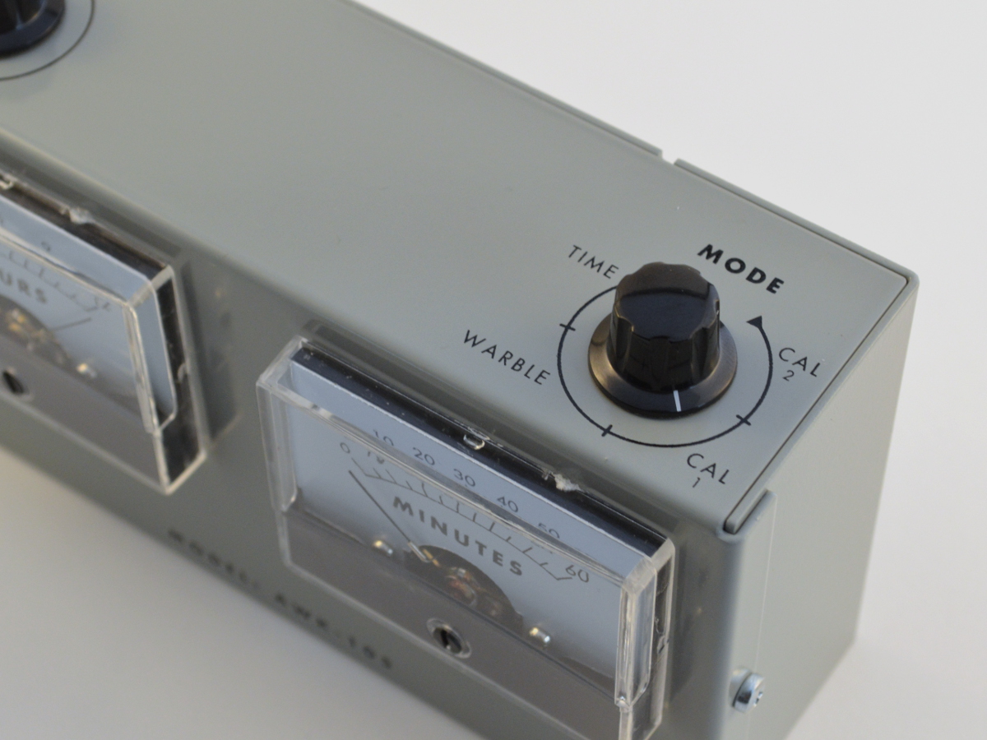
Photos/Retouched/AWK-105GR_4.JPG
