awkwardengineer/Clock/Photos/Retouched/AWK-105OL_2.JPG

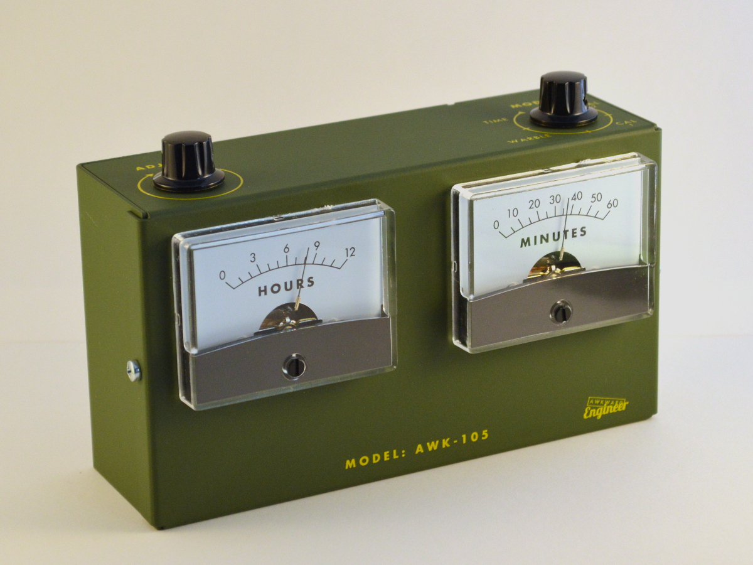
Photos/Retouched/AWK-105OL_2.JPG
