awkwardengineer/Clock/Photos/Retouched/AWK-105OL_4.JPG

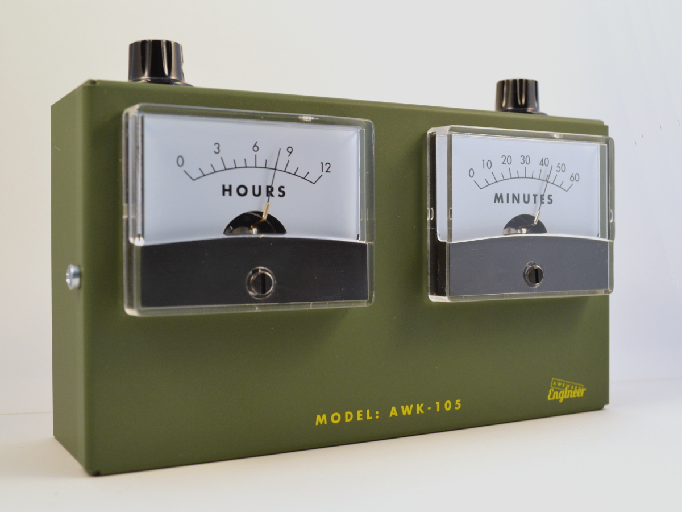
Photos/Retouched/AWK-105OL_4.JPG
