awkwardengineer/Clock/Photos/Retouched/clock.png

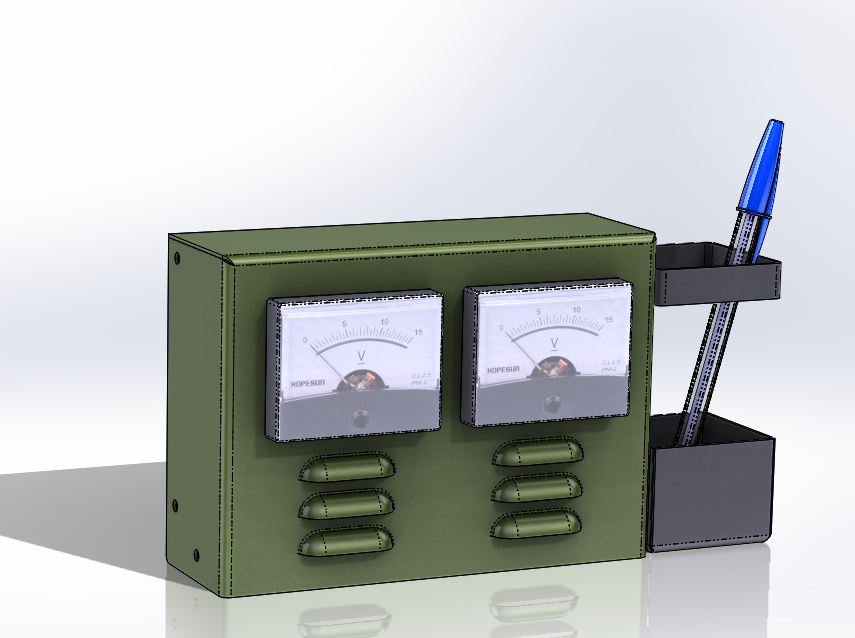
Photos/Retouched/clock.png
