awkwardengineer/Clock/Photos/Retouched/fb1.JPG

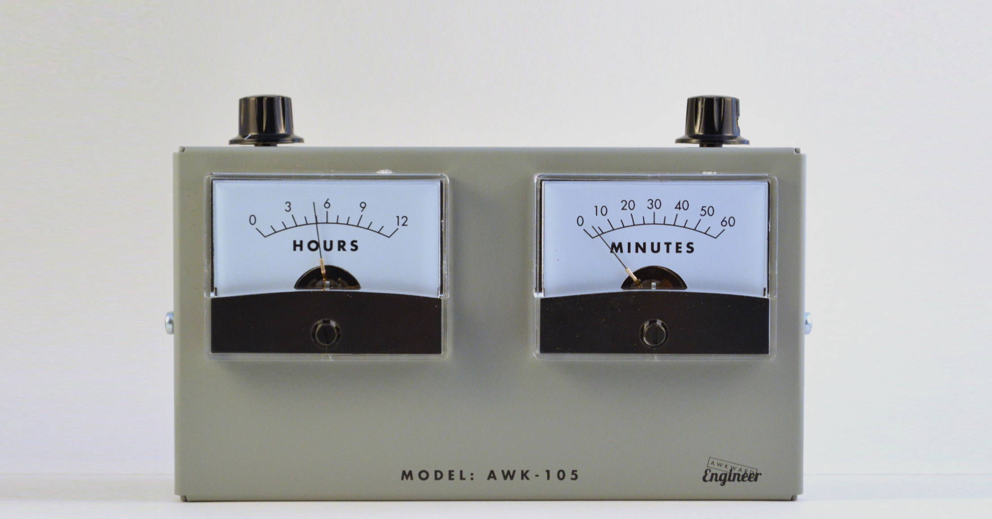
Photos/Retouched/fb1.JPG
