awkwardengineer/Clock/Photos/Retouched/outofstock.png

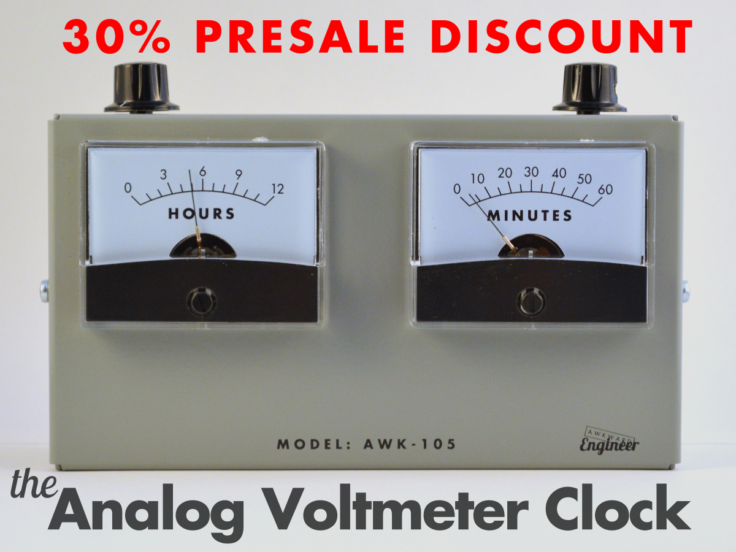
Photos/Retouched/outofstock.png
