awkwardengineer/Clock/Photos/USB Upgrade/2015-10-03 15_31_16.png

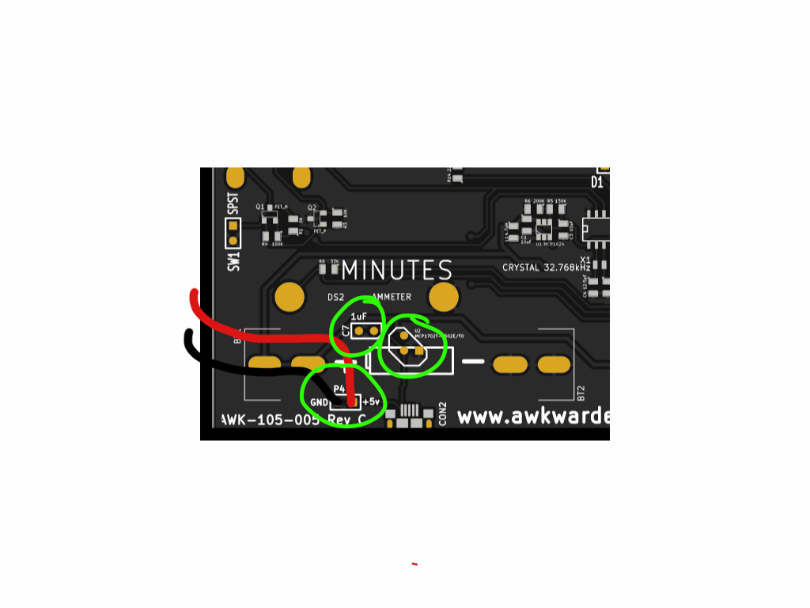
Photos/USB Upgrade/2015-10-03 15_31_16.png
