awkwardengineer/Clock/Photos/USB Upgrade/2015-10-03 15_46_44.png

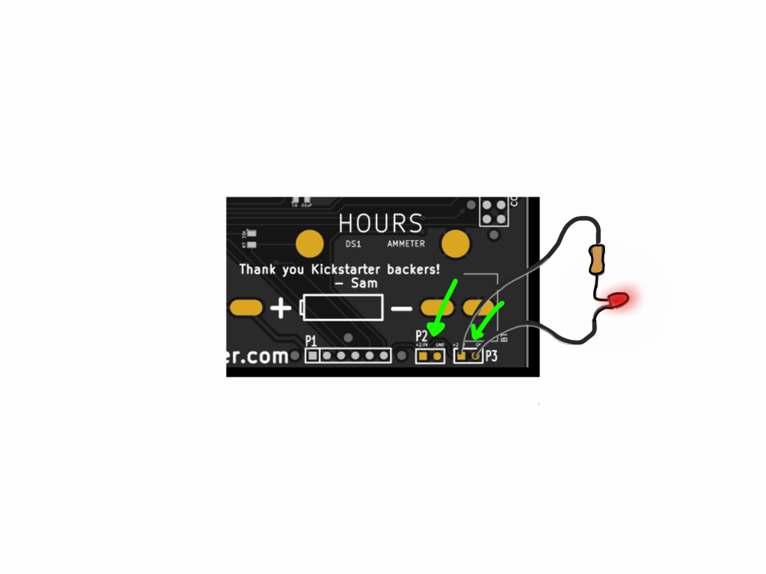
Photos/USB Upgrade/2015-10-03 15_46_44.png
