awkwardengineer/Clock/Photos/USB Upgrade/LED holders.jpg

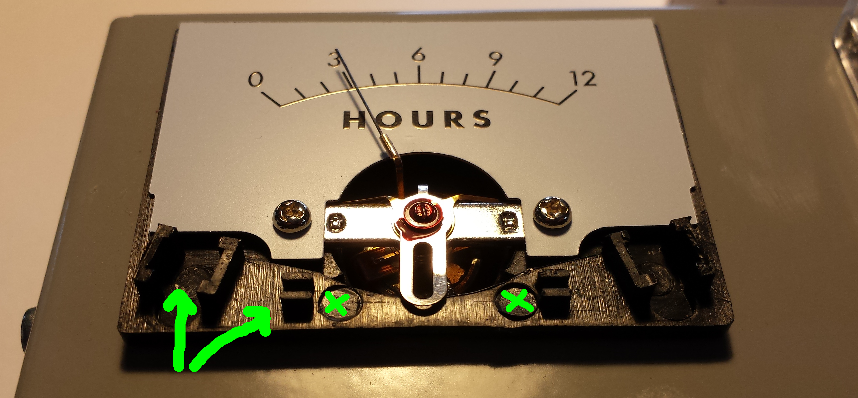
Photos/USB Upgrade/LED holders.jpg
