awkwardengineer/Clock/Photos/USB Upgrade/USB wires.jpg

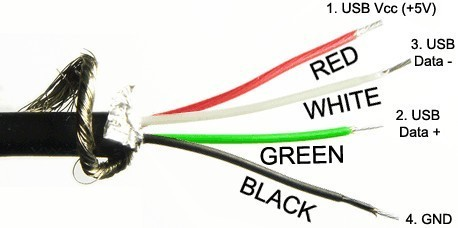
Photos/USB Upgrade/USB wires.jpg
