awkwardengineer/Clock/Photos/USB Upgrade/USB.PNG

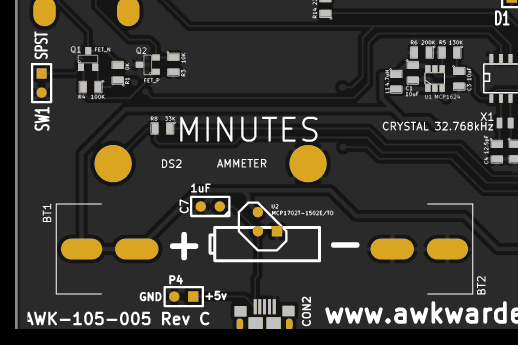
Photos/USB Upgrade/USB.PNG
