awkwardengineer/Clock/Photos/WW II Key/telegraph2.jpg

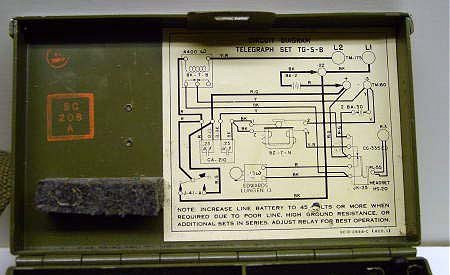
Photos/WW II Key/telegraph2.jpg
