awkwardengineer/Clock/Photos/WW II Key/telegraph3.jpg

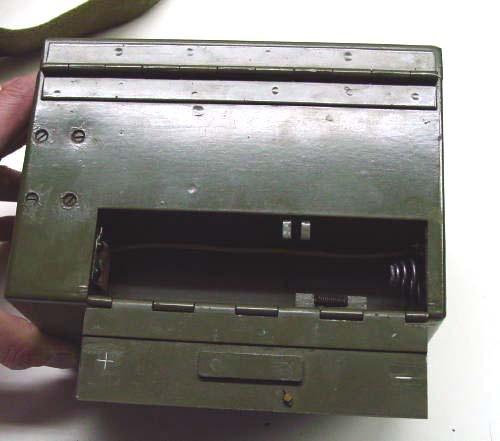
Photos/WW II Key/telegraph3.jpg
