awkwardengineer/Clock/Photos/WW II Key/telegraph.jpg

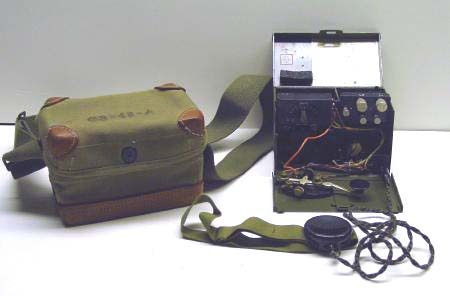
Photos/WW II Key/telegraph.jpg
