awkwardengineer/Clock/Photos/xander and clock.jpg

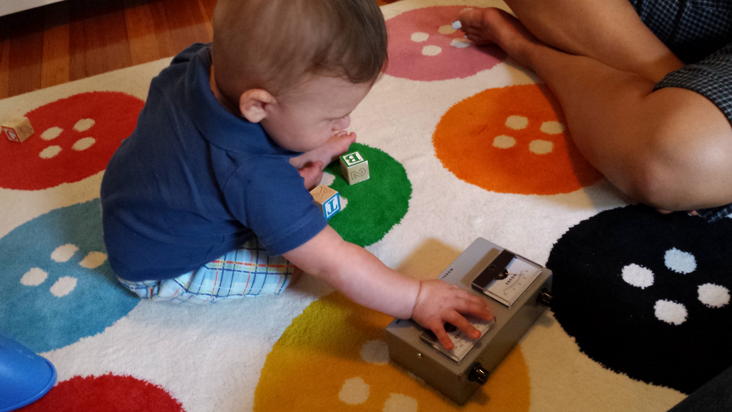
Photos/xander and clock.jpg
