awkwardengineer/Clock/Electrical/Reference Material/GT-4X toggle cover.pdf

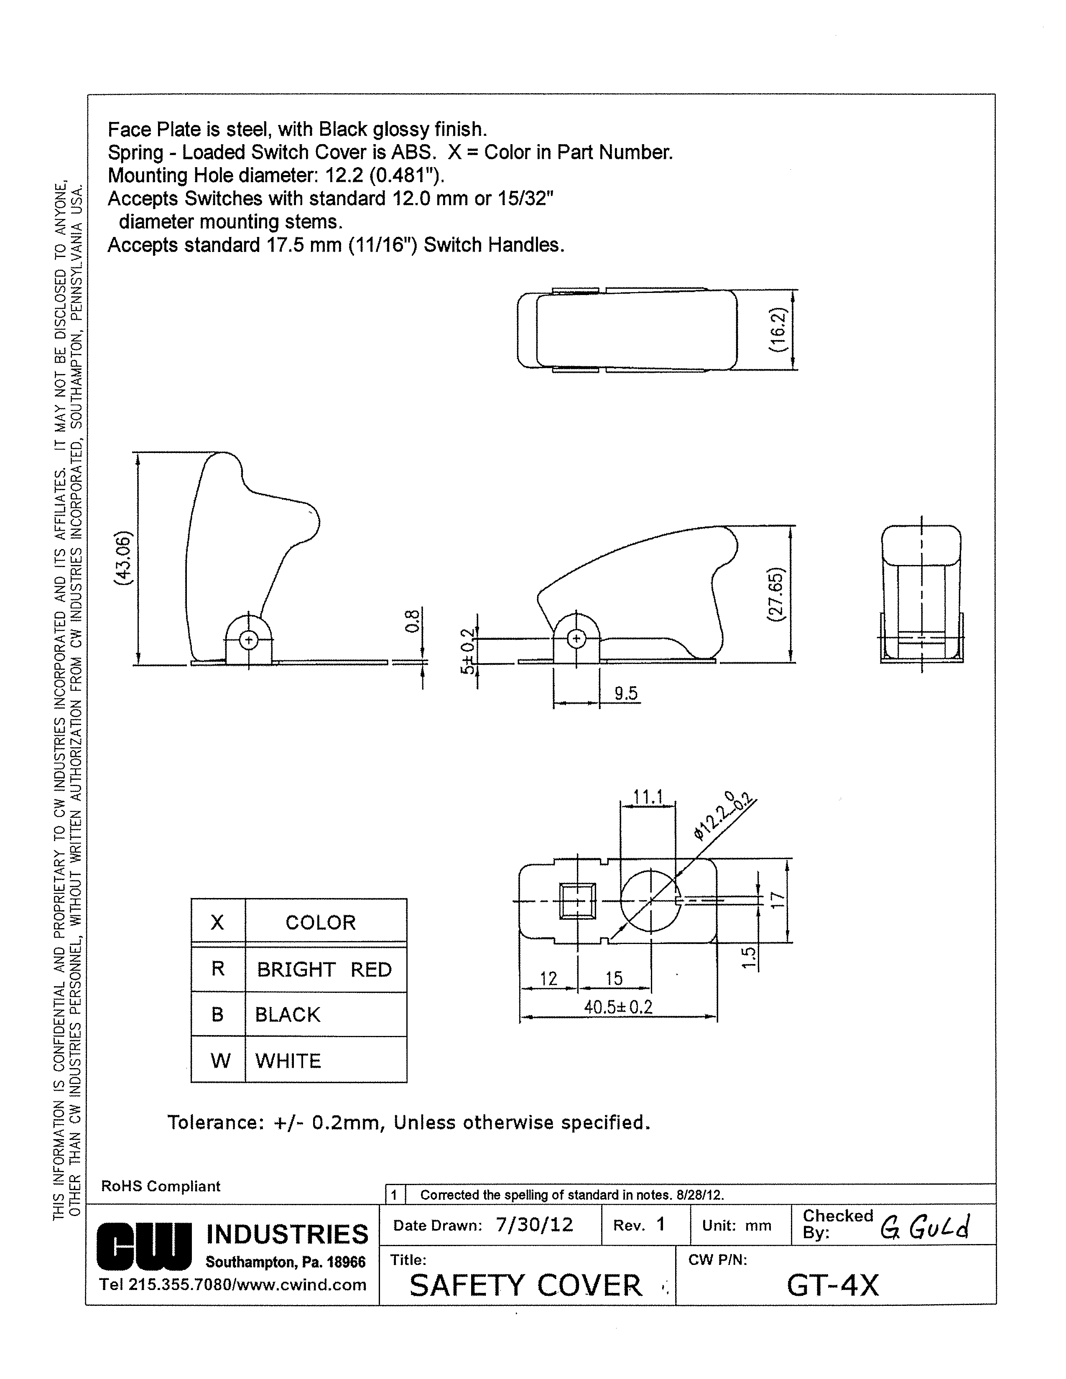
[picture p179: page 1]
