awkwardengineer/Clock/Electrical/Reference Material/GTS447SERIES toggle switch.pdf

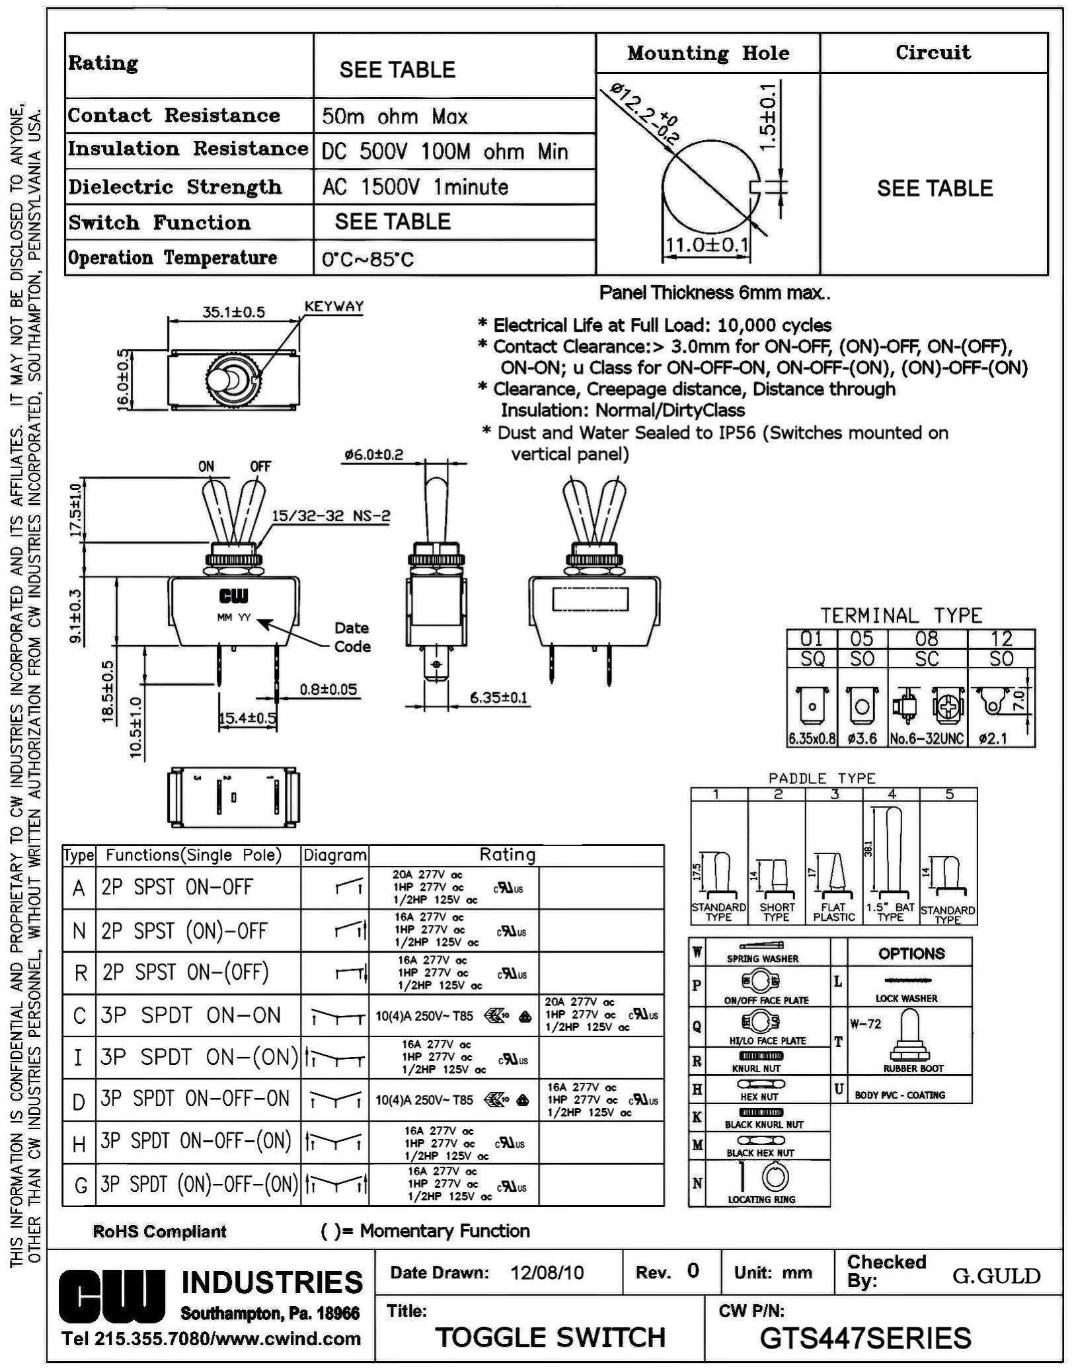
[picture p180: page 1]
