awkwardengineer/Clock/Electrical/Reference Material/fibonacci clock.jpg

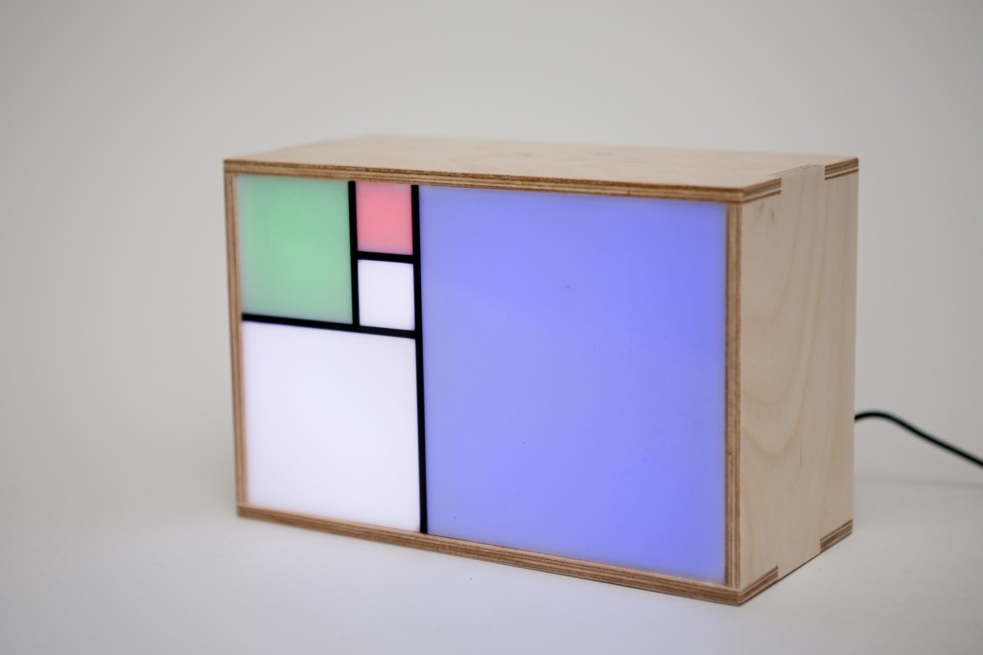
Electrical/Reference Material/fibonacci clock.jpg
