awkwardengineer/Clock/Electrical/Release to QUOTE/NexPCB (nov 25th release)/reference material/selected pot.JPG

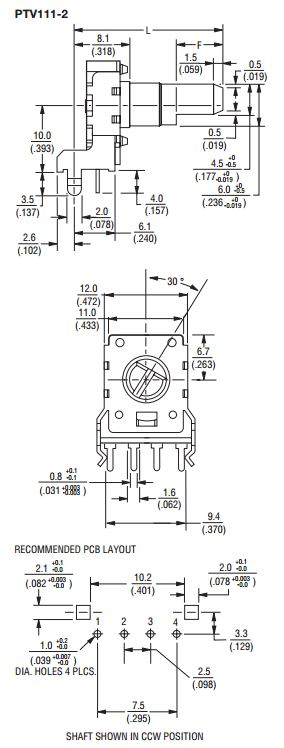
Electrical/Release to QUOTE/NexPCB (nov 25th release)/reference material/selected pot.JPG
