awkwardengineer/Clock/Mechanical/Design Memos/meter related sourcing questions/xander1.jpg

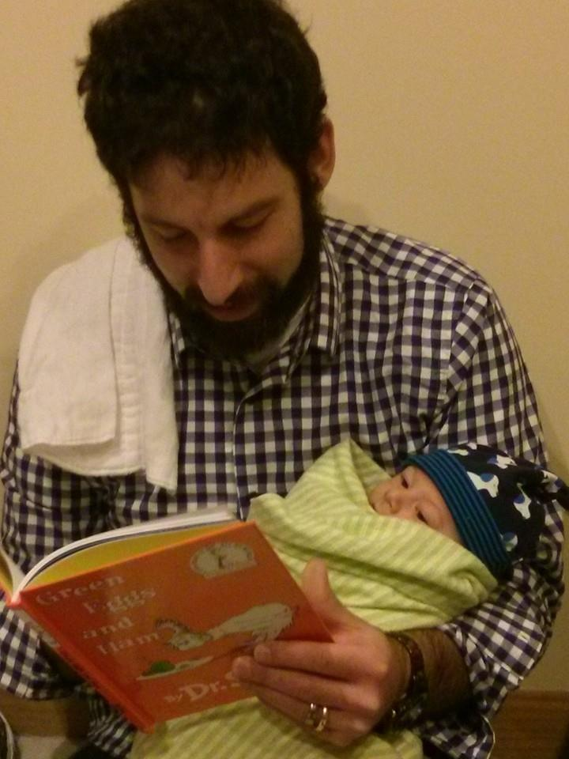
Mechanical/Design Memos/meter related sourcing questions/xander1.jpg
