awkwardengineer/Clock/Mechanical/Reference Material/BK-92 clip.PNG

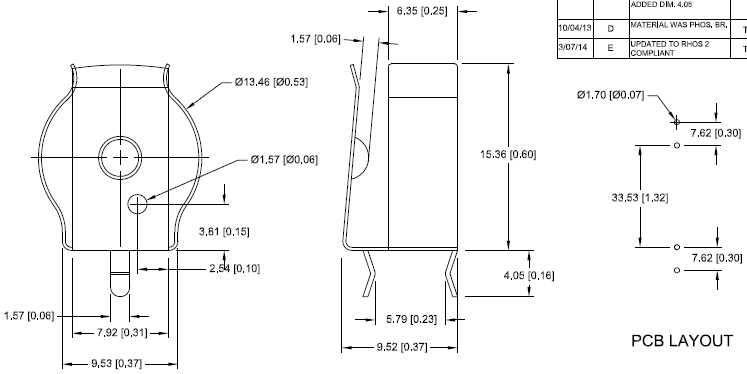
Mechanical/Reference Material/BK-92 clip.PNG
