awkwardengineer/Clock/Mechanical/Reference Material/davies 1910 knob.PNG

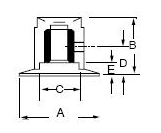
Mechanical/Reference Material/davies 1910 knob.PNG
