awkwardengineer/Clock/Mechanical/Reference Material/GTS447 toggle switch.PNG

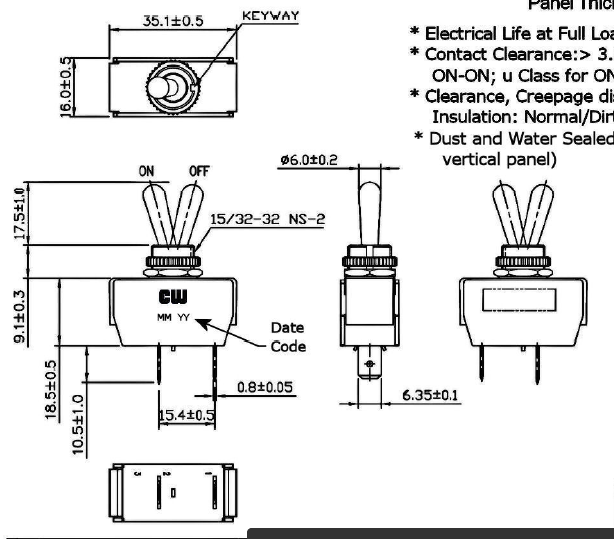
Mechanical/Reference Material/GTS447 toggle switch.PNG
