awkwardengineer/Clock/Mechanical/Reference Material/Hopesun - JM2.jpg

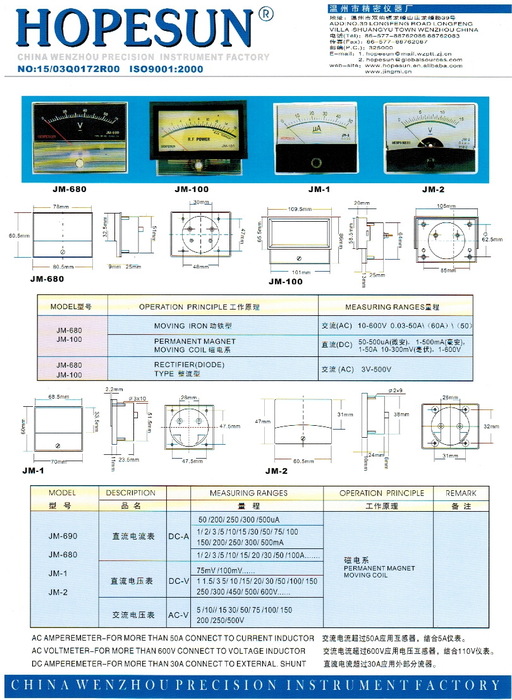
Mechanical/Reference Material/Hopesun - JM2.jpg
