awkwardengineer/Clock/Mechanical/Reference Material/Hopesun - PM2.jpg

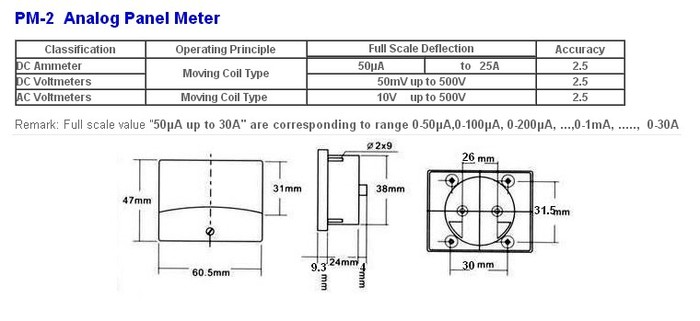
Mechanical/Reference Material/Hopesun - PM2.jpg
