awkwardengineer/Clock/Mechanical/Reference Material/switch cover.PNG

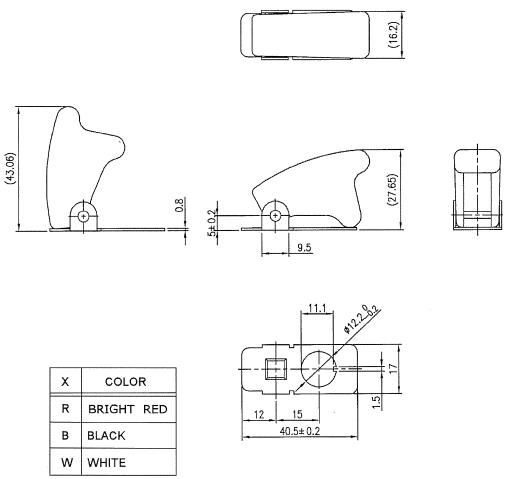
Mechanical/Reference Material/switch cover.PNG
