awkwardengineer/Clock/Media Campaign/Media Kit/board_components.jpg

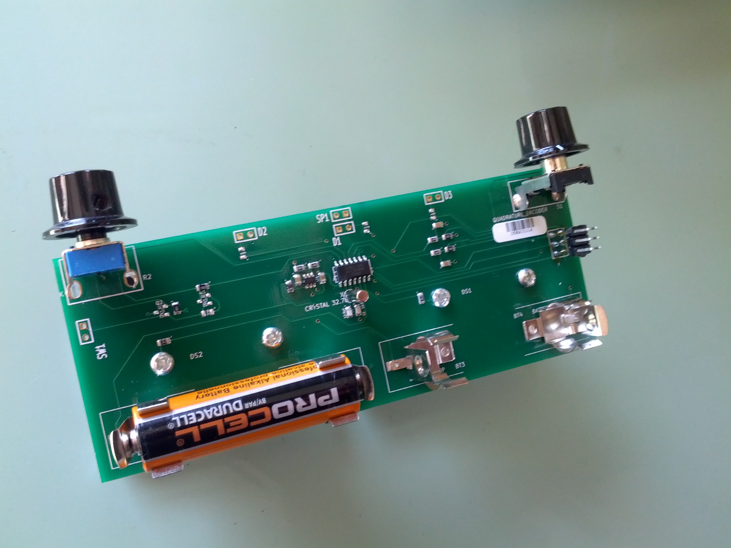
Media Campaign/Media Kit/board_components.jpg
