awkwardengineer/Clock/Photos/Blog Post Material/20151106_100225.jpg

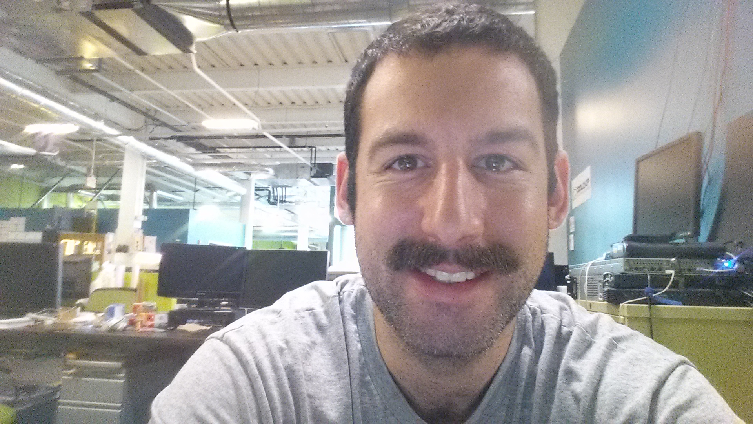
Photos/Blog Post Material/20151106_100225.jpg
