awkwardengineer/Clock/Photos/Blog Post Material/20151129_111324.jpg

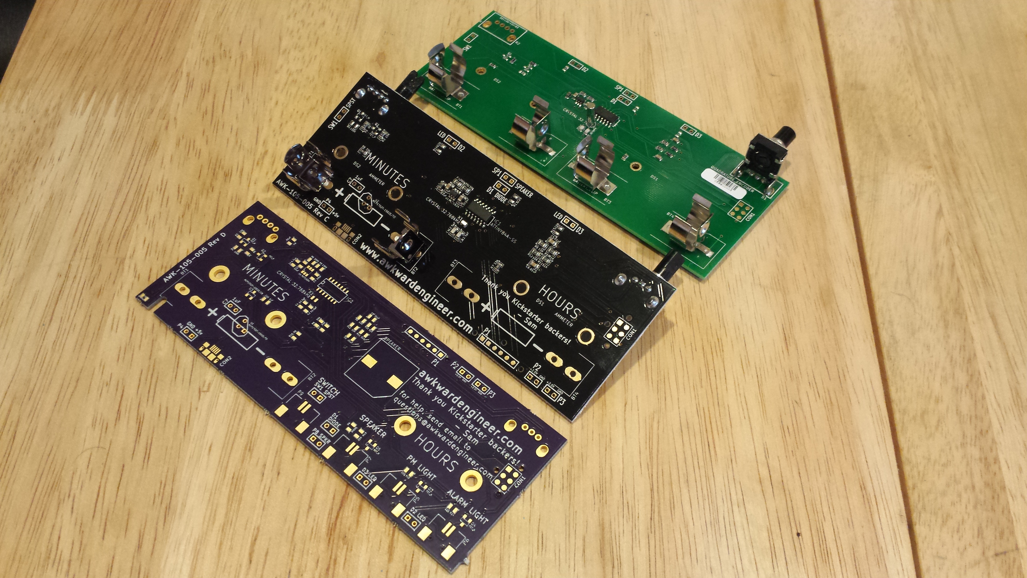
Photos/Blog Post Material/20151129_111324.jpg
