awkwardengineer/Clock/Photos/Blog Post Material/20151202_105100.jpg

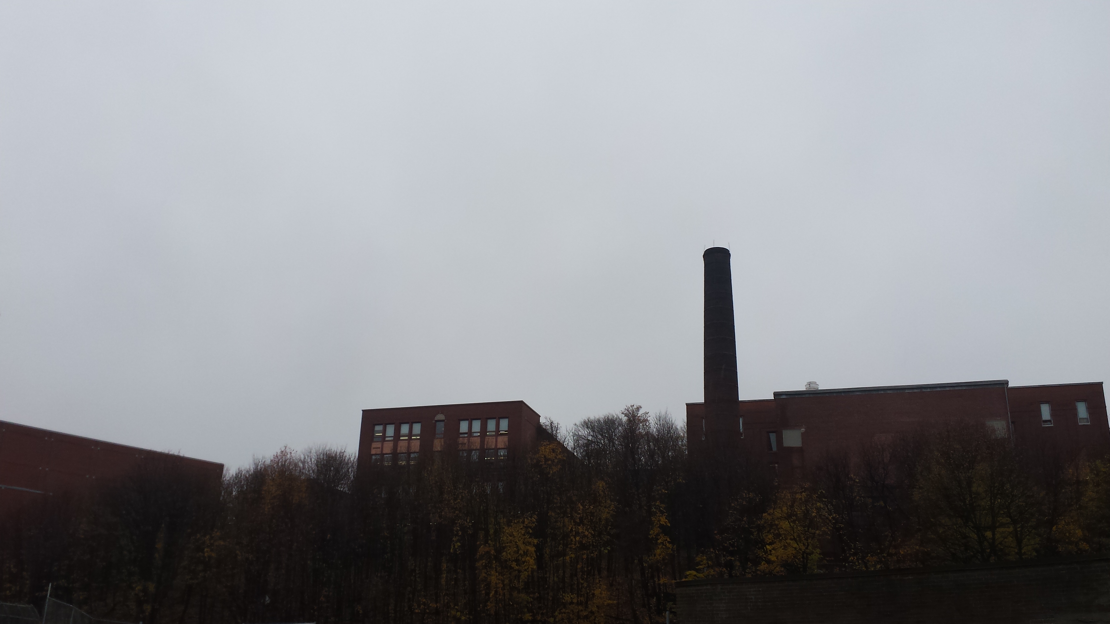
Photos/Blog Post Material/20151202_105100.jpg
