awkwardengineer/Clock/Photos/Blog Post Material/20151202_105147.jpg

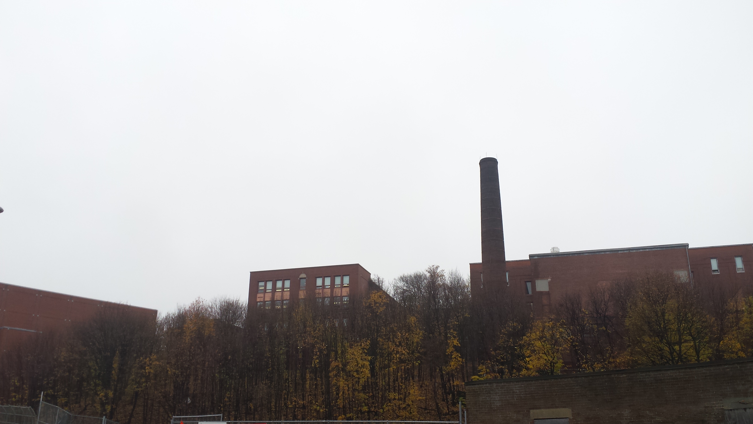
Photos/Blog Post Material/20151202_105147.jpg
