awkwardengineer/Clock/Photos/Blog Post Material/20151216_120424.jpg

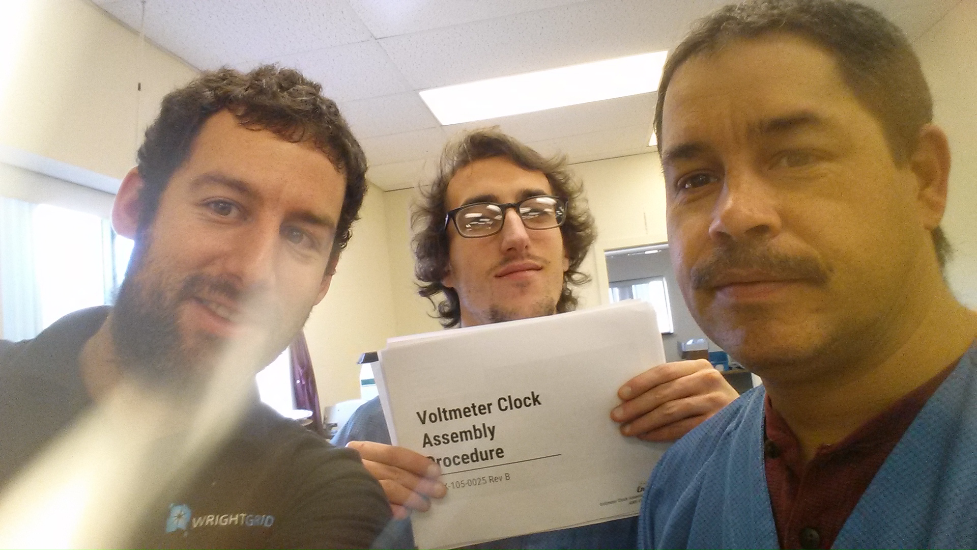
Photos/Blog Post Material/20151216_120424.jpg
