awkwardengineer/Clock/Photos/Blog Post Material/20160106_175553.jpg

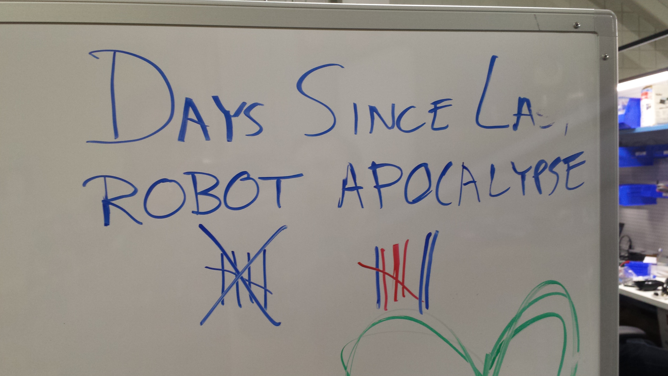
Photos/Blog Post Material/20160106_175553.jpg
