awkwardengineer/Clock/Photos/Blog Post Material/20160108_110015.jpg

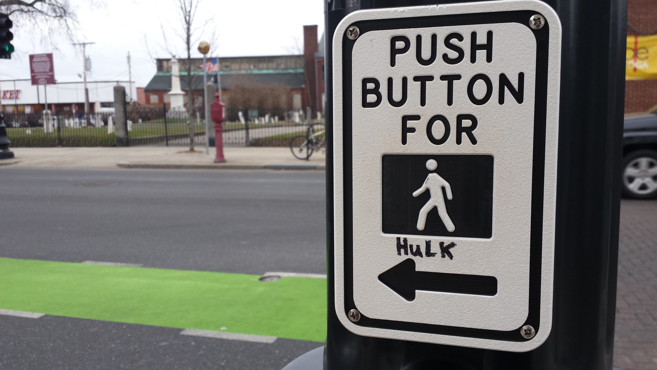
Photos/Blog Post Material/20160108_110015.jpg
