awkwardengineer/Clock/Photos/Blog Post Material/20160120_221308.jpg

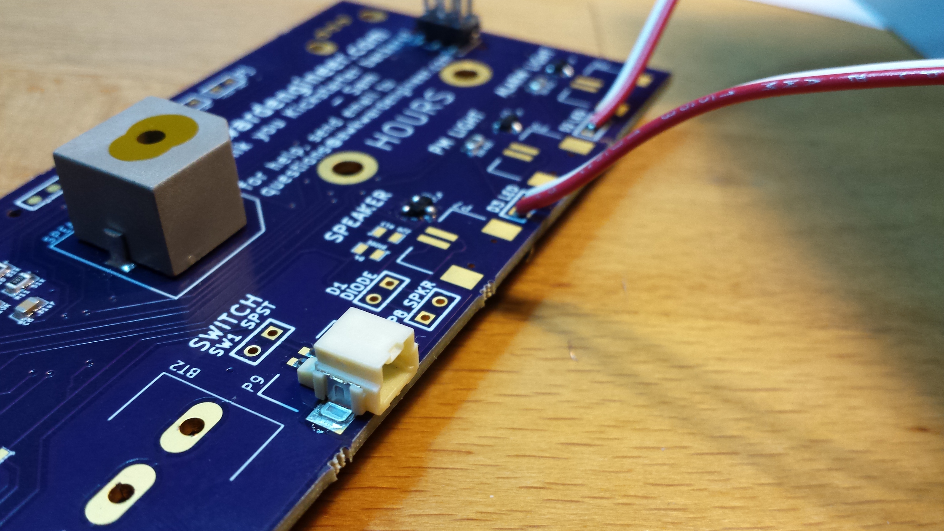
Photos/Blog Post Material/20160120_221308.jpg
