awkwardengineer/Clock/Photos/Blog Post Material/20160217_222457.jpg

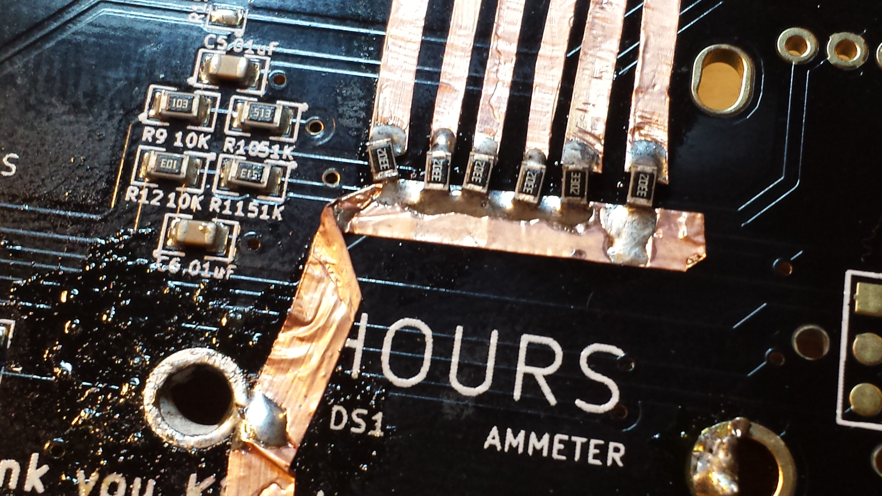
Photos/Blog Post Material/20160217_222457.jpg
