awkwardengineer/Clock/Photos/Blog Post Material/20160221_204508.jpg

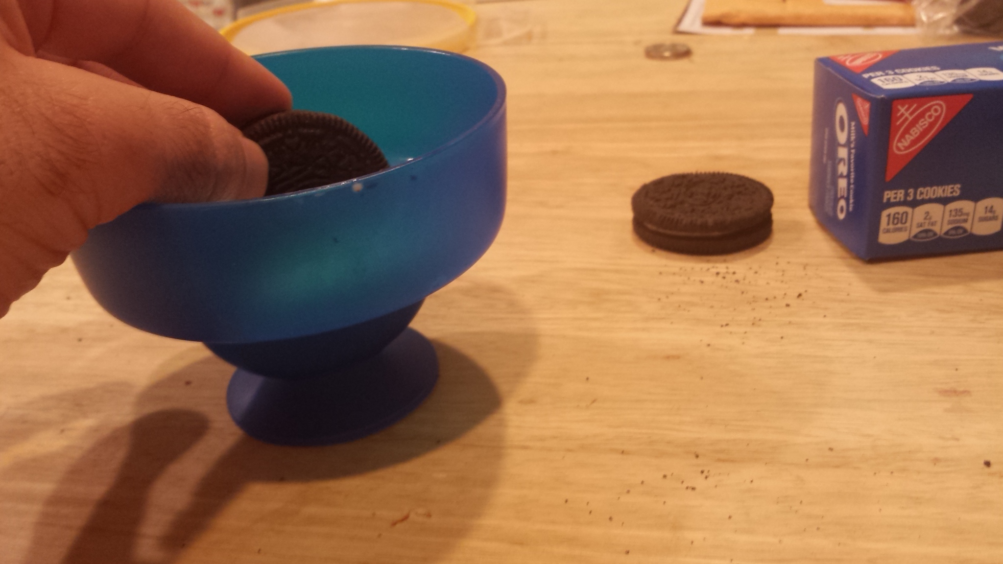
Photos/Blog Post Material/20160221_204508.jpg
