awkwardengineer/Clock/Photos/Blog Post Material/20160222_232903.jpg

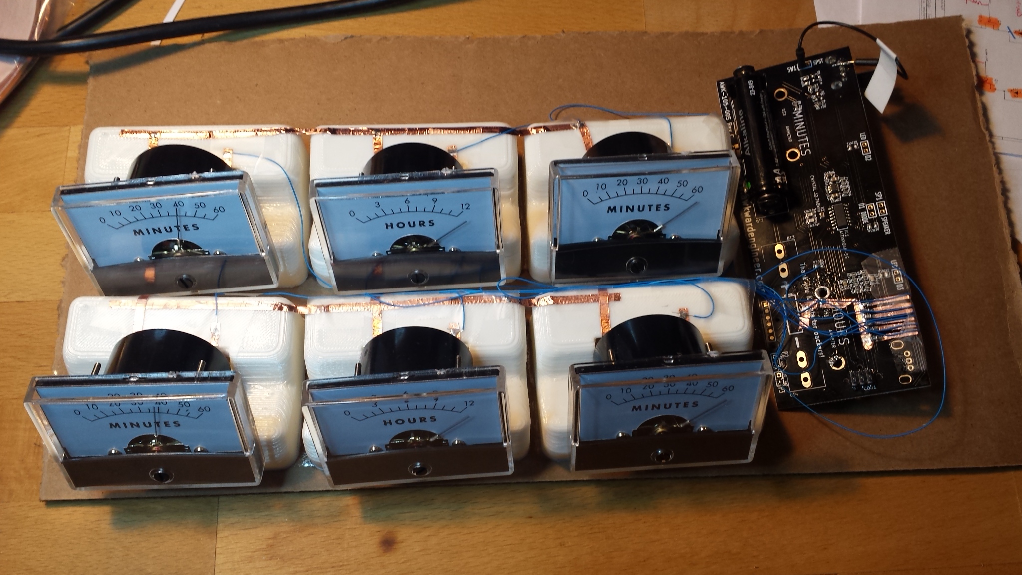
Photos/Blog Post Material/20160222_232903.jpg
