awkwardengineer/Clock/Photos/Blog Post Material/20160222_232951.jpg

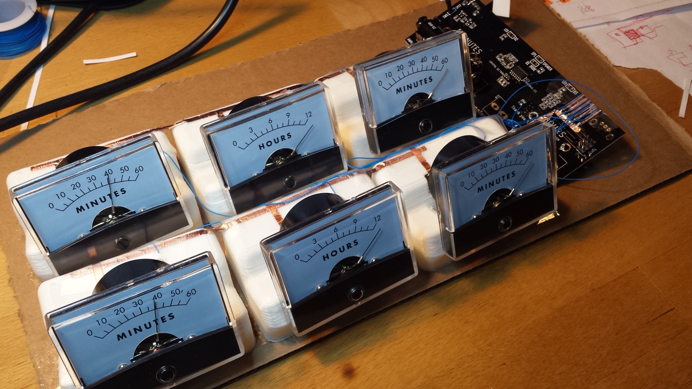
Photos/Blog Post Material/20160222_232951.jpg
