awkwardengineer/Clock/Photos/Blog Post Material/20160403_220637.jpg

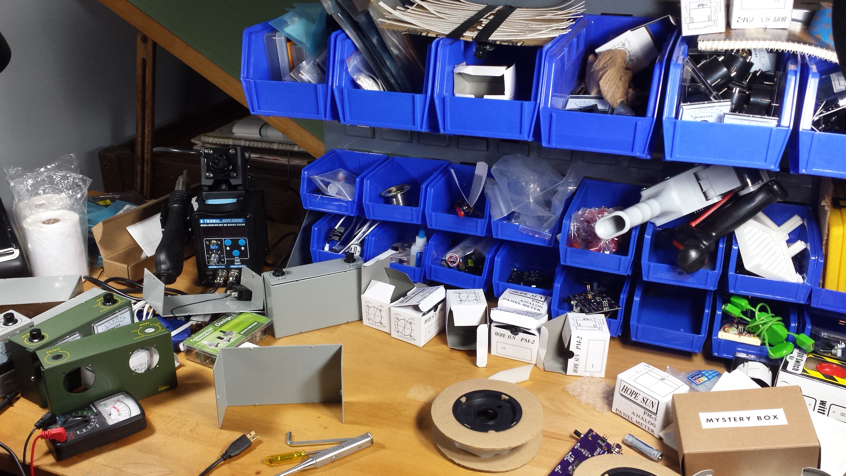
Photos/Blog Post Material/20160403_220637.jpg
