awkwardengineer/Clock/Photos/Blog Post Material/April/17 found this on my walk.jpg

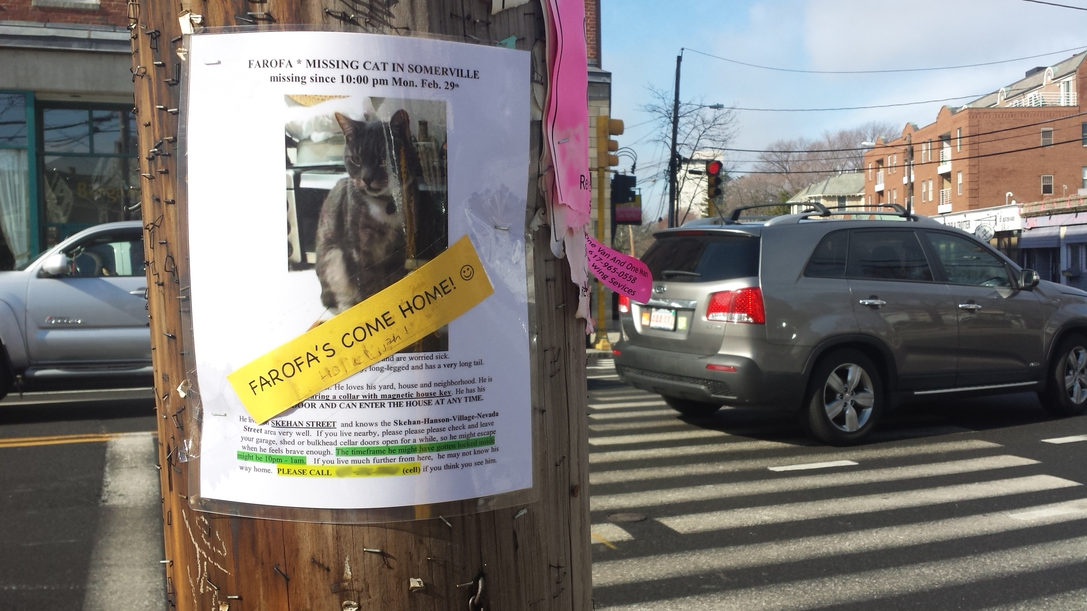
Photos/Blog Post Material/April/17 found this on my walk.jpg
