awkwardengineer/Clock/Photos/Blog Post Material/April/12919627_10156963606000354_4155046746797818152_n.jpg

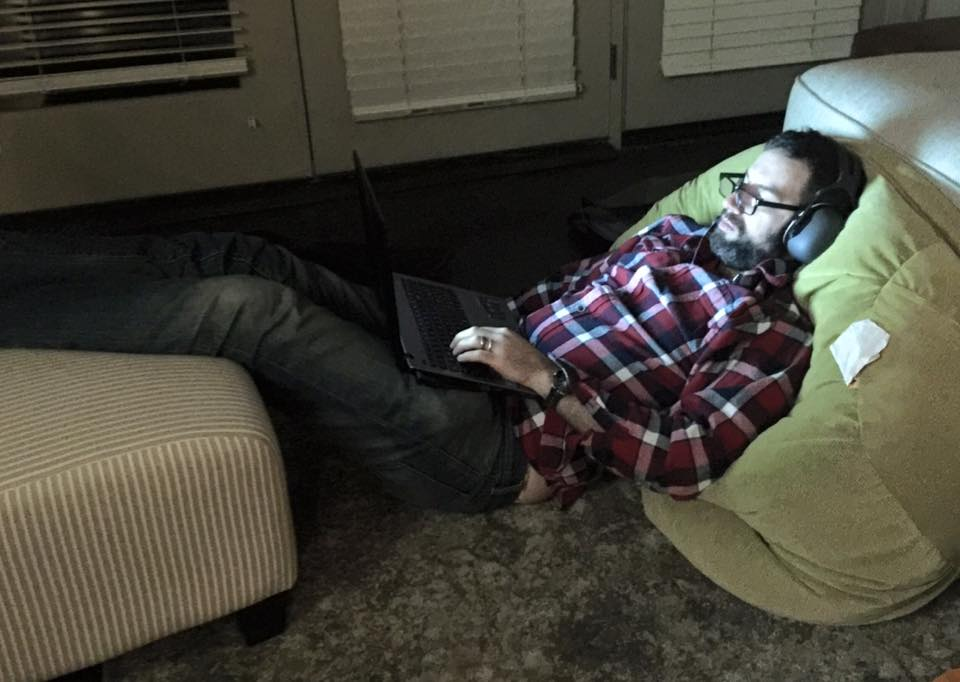
Photos/Blog Post Material/April/12919627_10156963606000354_4155046746797818152_n.jpg
