awkwardengineer/Clock/Photos/Blog Post Material/April/20160330_155615.jpg

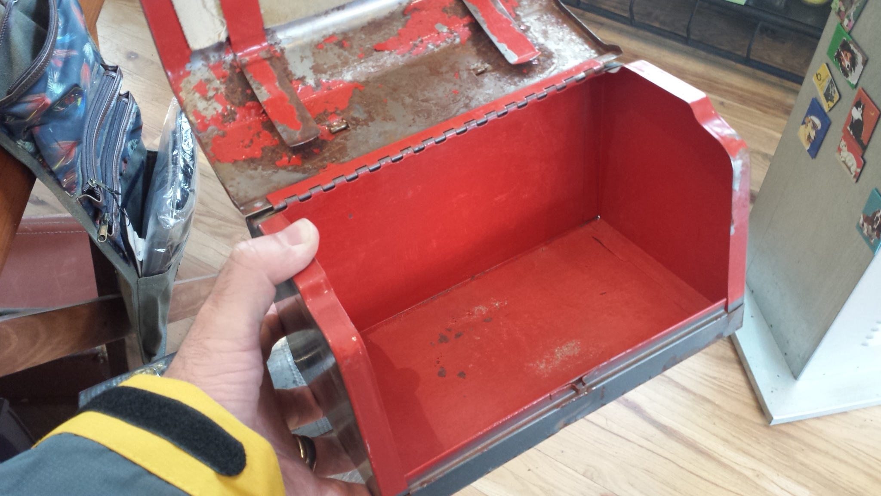
Photos/Blog Post Material/April/20160330_155615.jpg
