awkwardengineer/Clock/Photos/Blog Post Material/April/20160330_155641.jpg

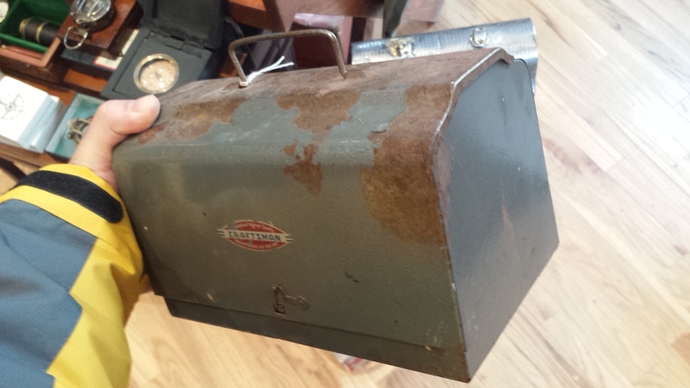
Photos/Blog Post Material/April/20160330_155641.jpg
