awkwardengineer/Clock/Photos/Blog Post Material/bare case.jpg

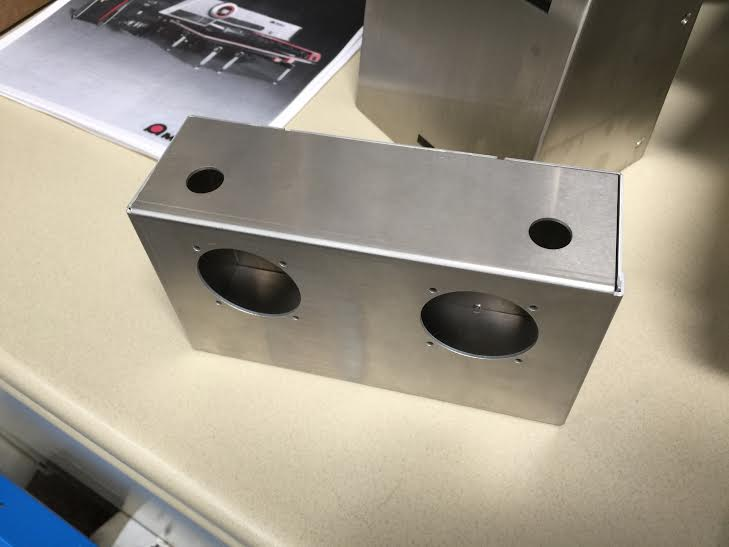
Photos/Blog Post Material/bare case.jpg
