awkwardengineer/Clock/Photos/Blog Post Material/board options.PNG

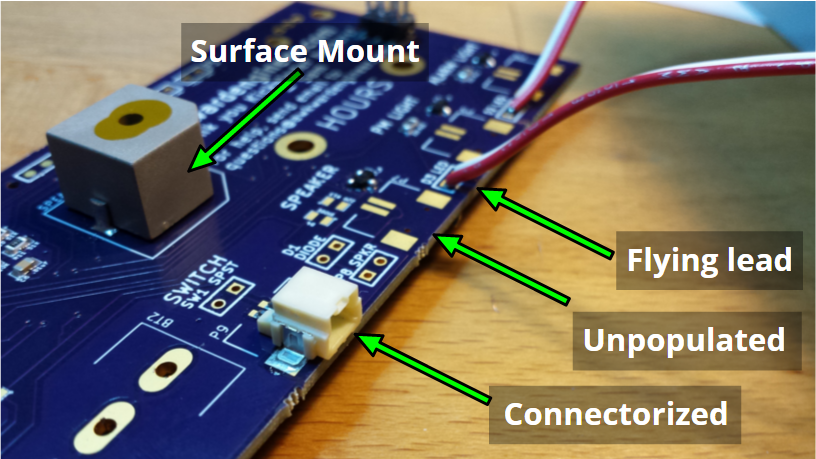
Photos/Blog Post Material/board options.PNG
