awkwardengineer/Clock/Photos/Blog Post Material/board_layout.JPG

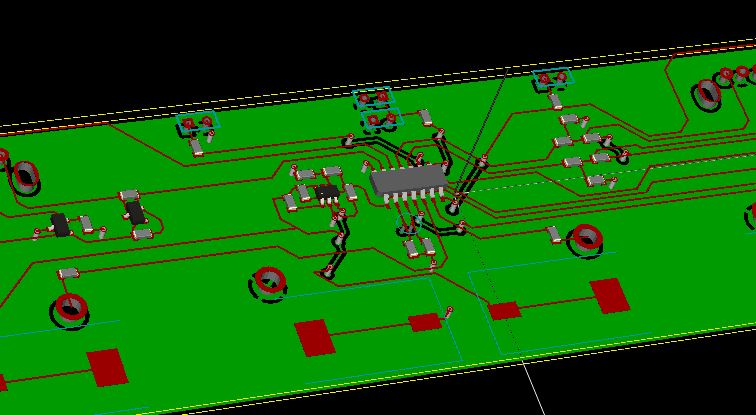
Photos/Blog Post Material/board_layout.JPG
