awkwardengineer/Clock/Photos/Blog Post Material/BOM.PNG

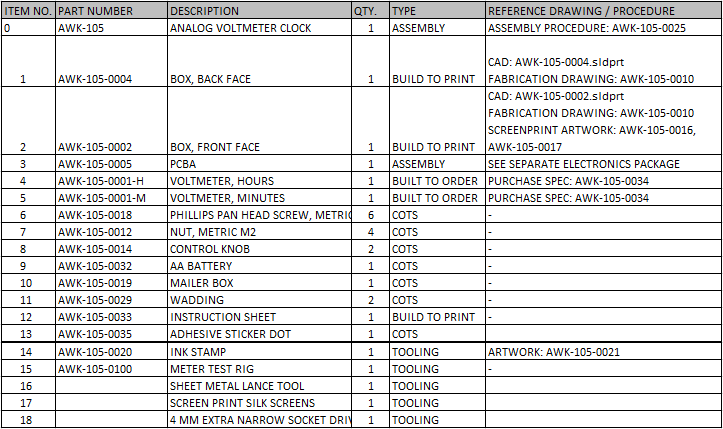
Photos/Blog Post Material/BOM.PNG
