awkwardengineer/Clock/Photos/Blog Post Material/hot and sparky.jpg

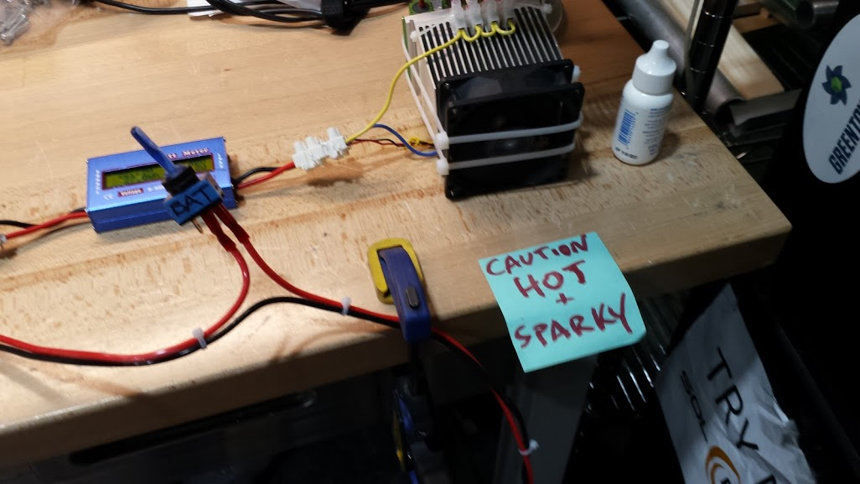
Photos/Blog Post Material/hot and sparky.jpg
