awkwardengineer/Clock/Photos/Blog Post Material/low power 1.PNG

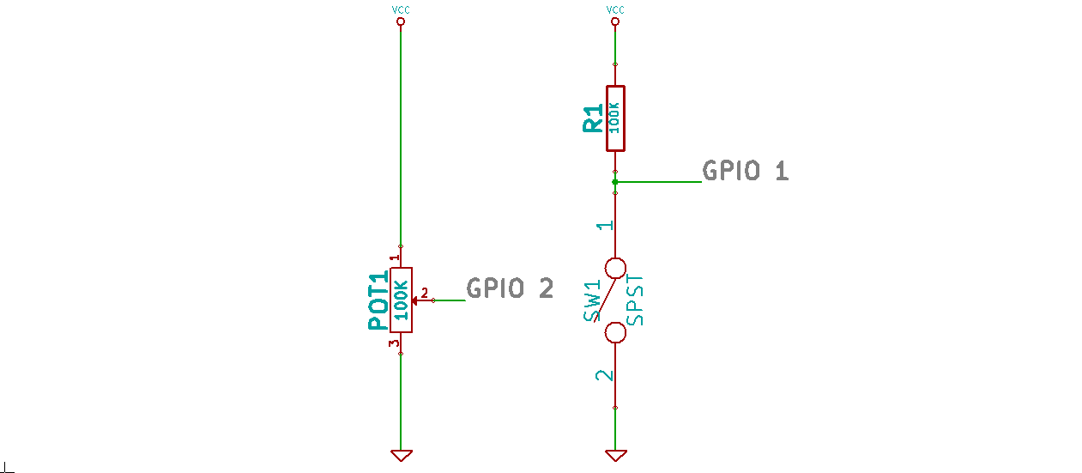
Photos/Blog Post Material/low power 1.PNG
