awkwardengineer/Clock/Photos/Blog Post Material/low power 2.PNG

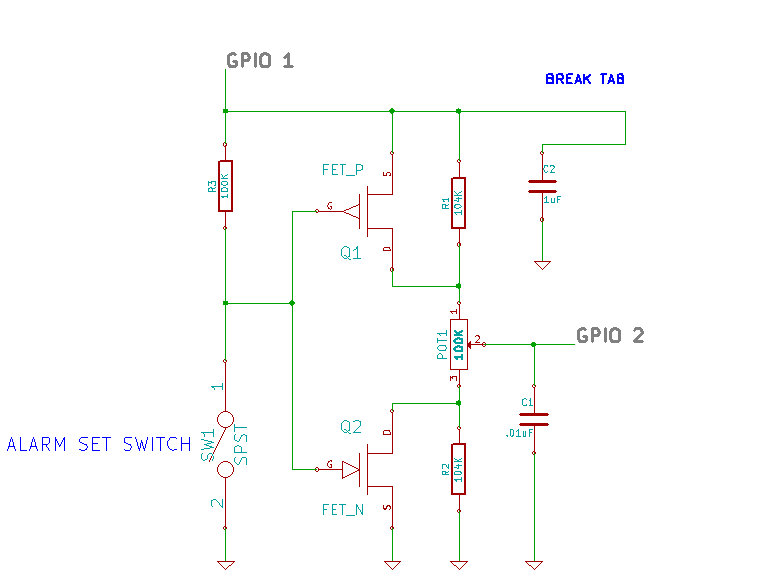
Photos/Blog Post Material/low power 2.PNG
