awkwardengineer/Clock/Photos/Blog Post Material/low power 3.PNG

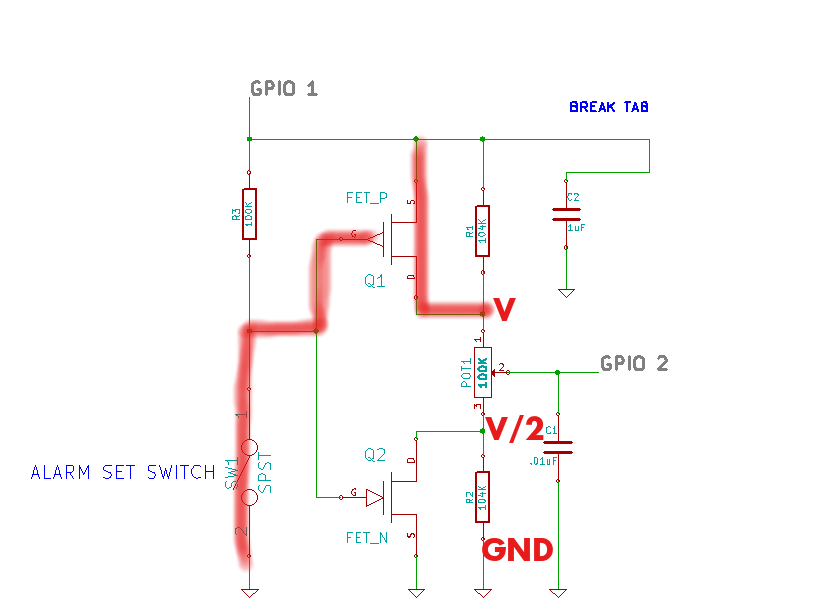
Photos/Blog Post Material/low power 3.PNG
