awkwardengineer/Clock/Photos/Blog Post Material/low power 4.PNG

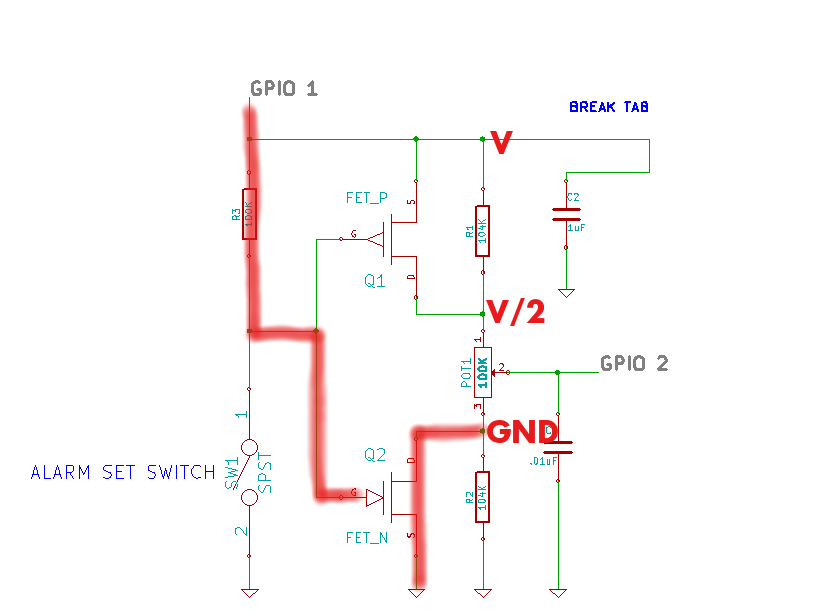
Photos/Blog Post Material/low power 4.PNG
