awkwardengineer/Clock/Photos/Blog Post Material/low power 5.PNG

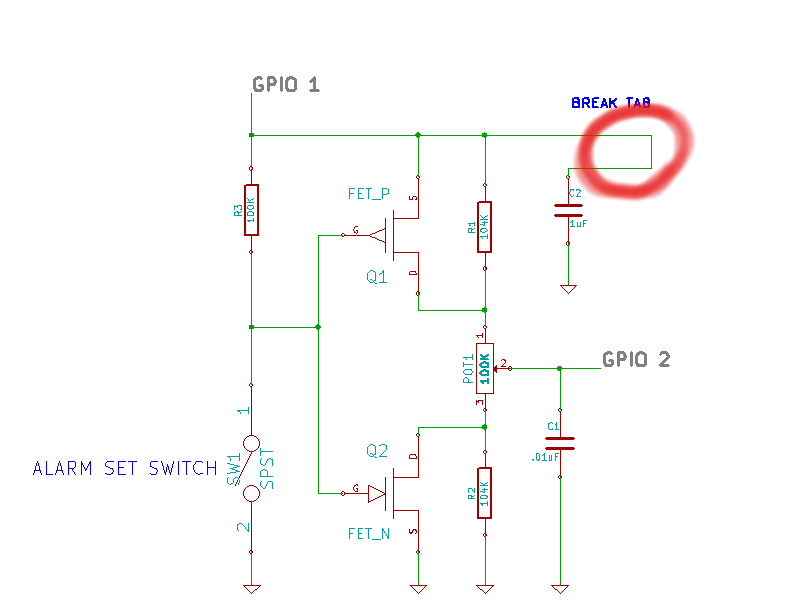
Photos/Blog Post Material/low power 5.PNG
