awkwardengineer/Clock/Photos/Blog Post Material/low power 7.jpg

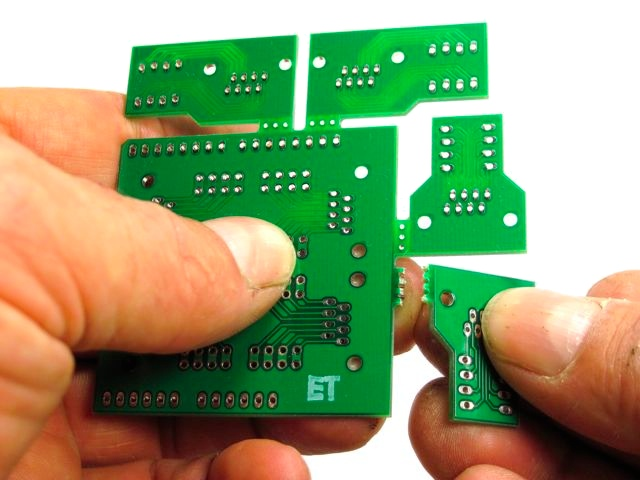
Photos/Blog Post Material/low power 7.jpg
