awkwardengineer/Clock/Photos/Blog Post Material/March/20150901_142101.jpg

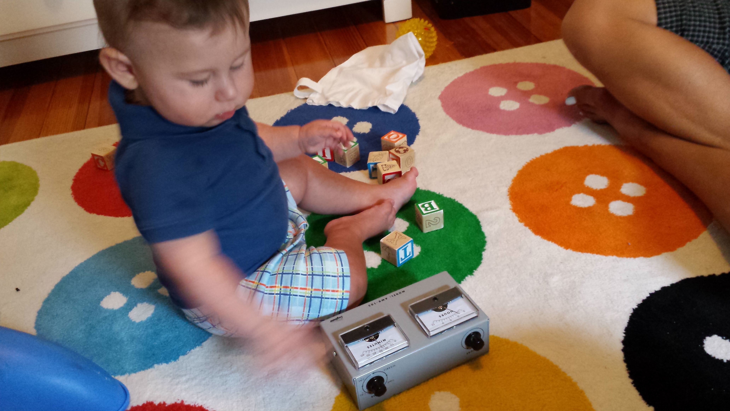
Photos/Blog Post Material/March/20150901_142101.jpg
