awkwardengineer/Clock/Photos/Blog Post Material/March/bts 0.jpg

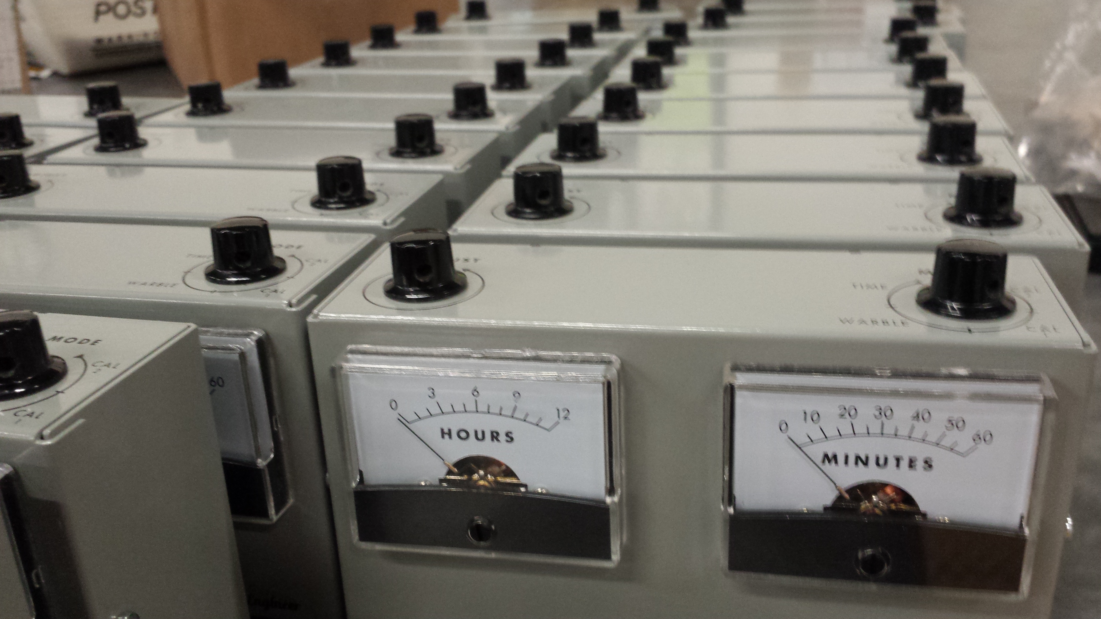
Photos/Blog Post Material/March/bts 0.jpg
