awkwardengineer/Clock/Photos/Blog Post Material/March/bts 1.jpg

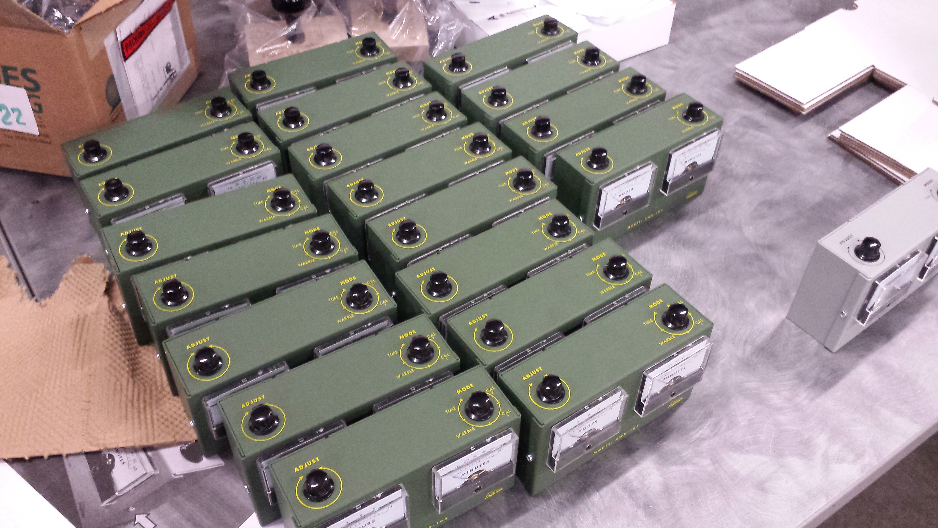
Photos/Blog Post Material/March/bts 1.jpg
