awkwardengineer/Clock/Photos/Blog Post Material/March/bts 3.jpg

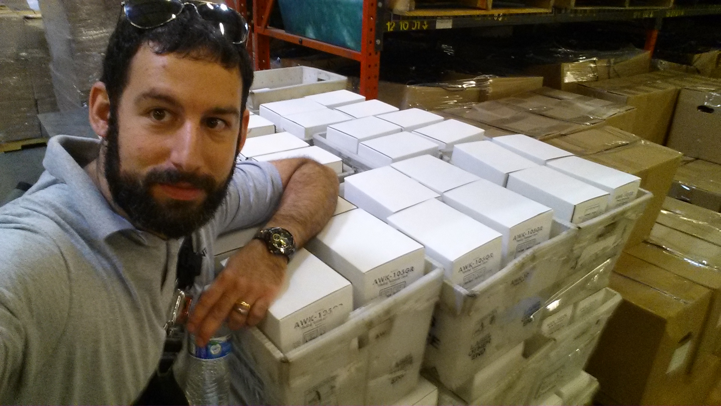
Photos/Blog Post Material/March/bts 3.jpg
