awkwardengineer/Clock/Photos/Blog Post Material/March/bts 4.jpg

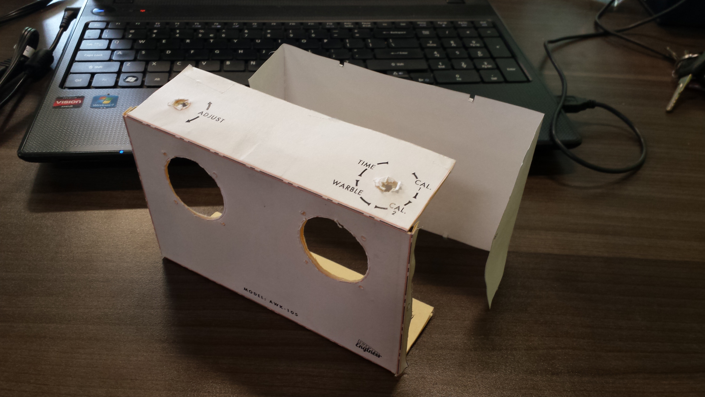
Photos/Blog Post Material/March/bts 4.jpg
