awkwardengineer/Clock/Photos/Blog Post Material/March/fig+1-2.jpg

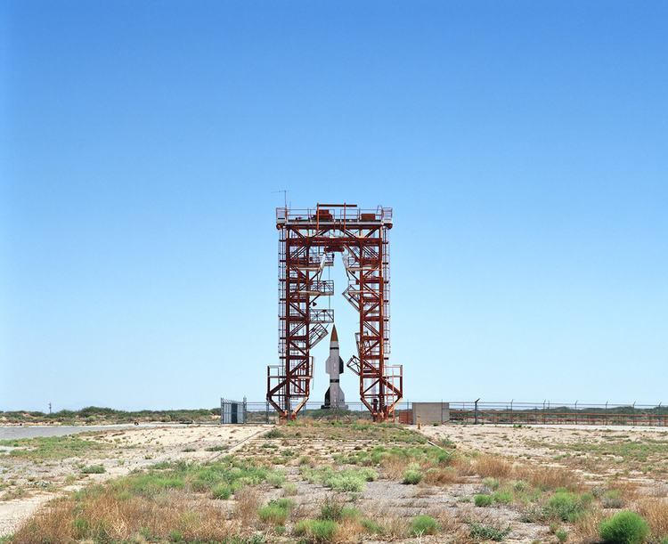
Photos/Blog Post Material/March/fig+1-2.jpg
