awkwardengineer/Clock/Photos/Blog Post Material/March/fig+3-18.jpg

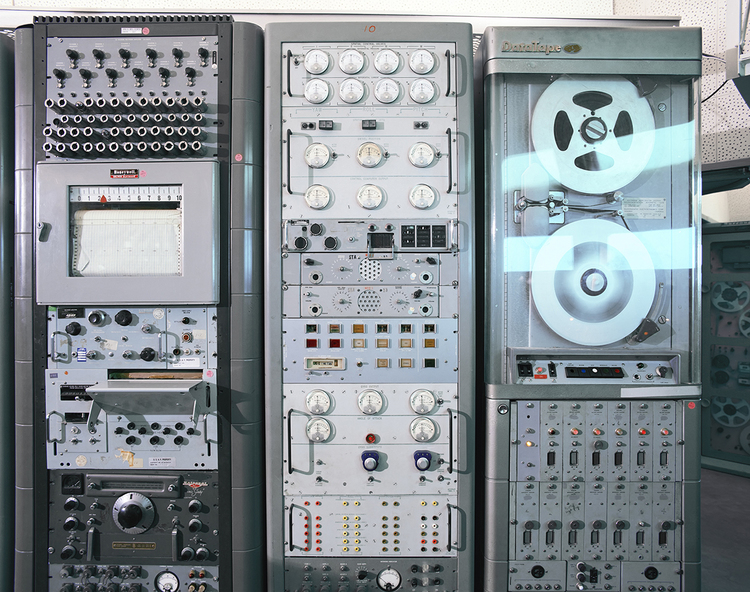
Photos/Blog Post Material/March/fig+3-18.jpg
