awkwardengineer/Clock/Photos/Blog Post Material/March/fig+4-17.jpg

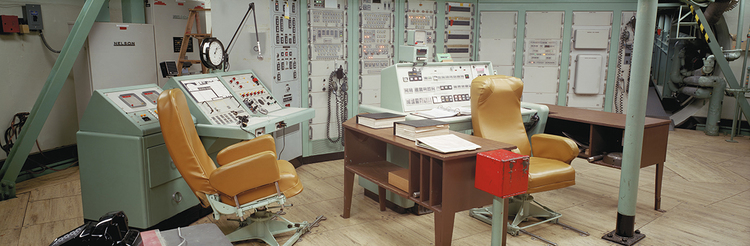
Photos/Blog Post Material/March/fig+4-17.jpg
