awkwardengineer/Clock/Photos/Blog Post Material/March/mr._sulu.JPG

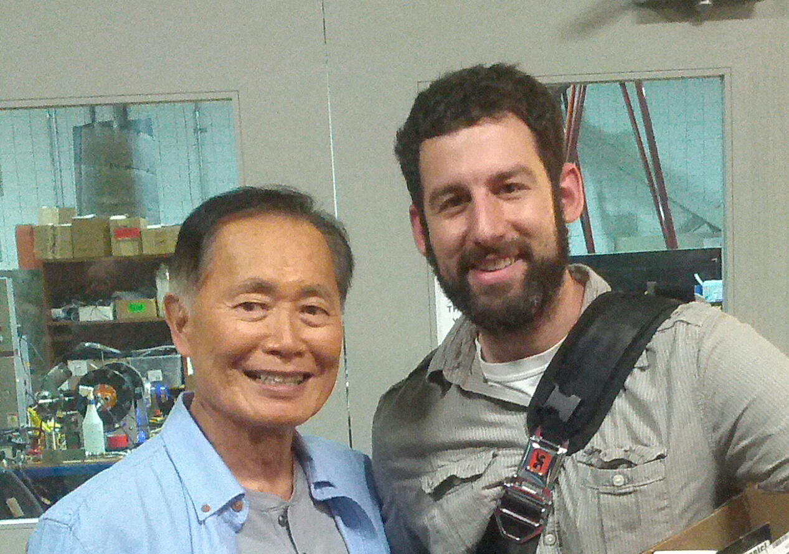
Photos/Blog Post Material/March/mr._sulu.JPG
