awkwardengineer/Clock/Photos/Blog Post Material/March/p1.JPG

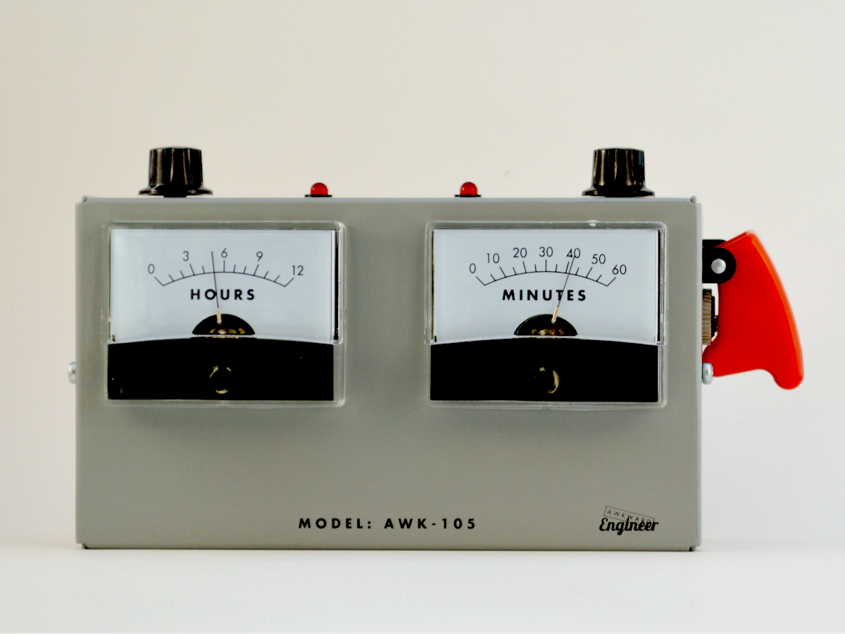
Photos/Blog Post Material/March/p1.JPG
