awkwardengineer/Clock/Photos/Blog Post Material/March/p2.JPG

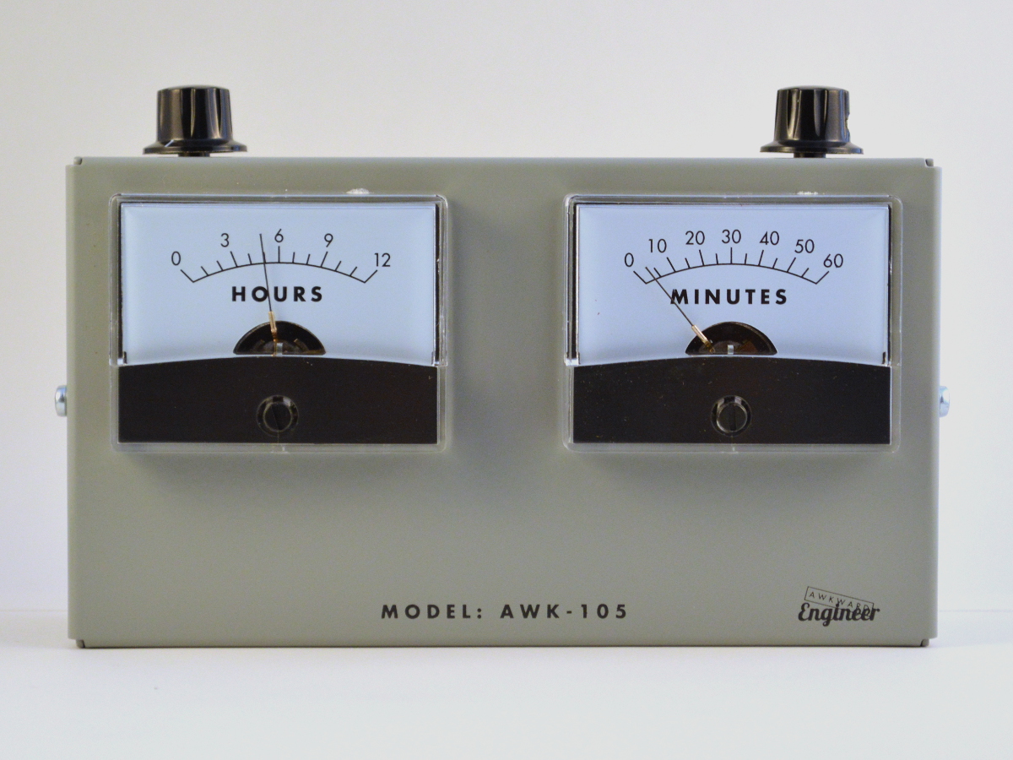
Photos/Blog Post Material/March/p2.JPG
