awkwardengineer/Clock/Photos/Blog Post Material/March/p3.JPG

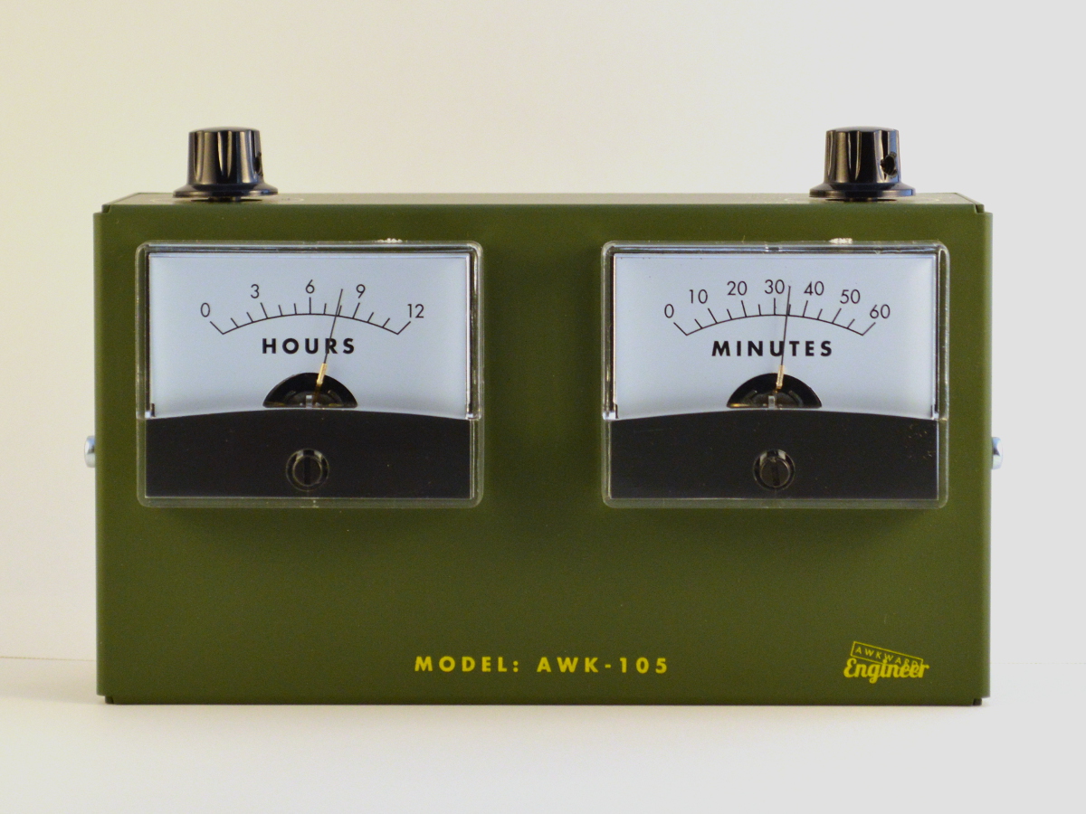
Photos/Blog Post Material/March/p3.JPG
