awkwardengineer/Clock/Photos/Blog Post Material/March/tbt 2.jpg

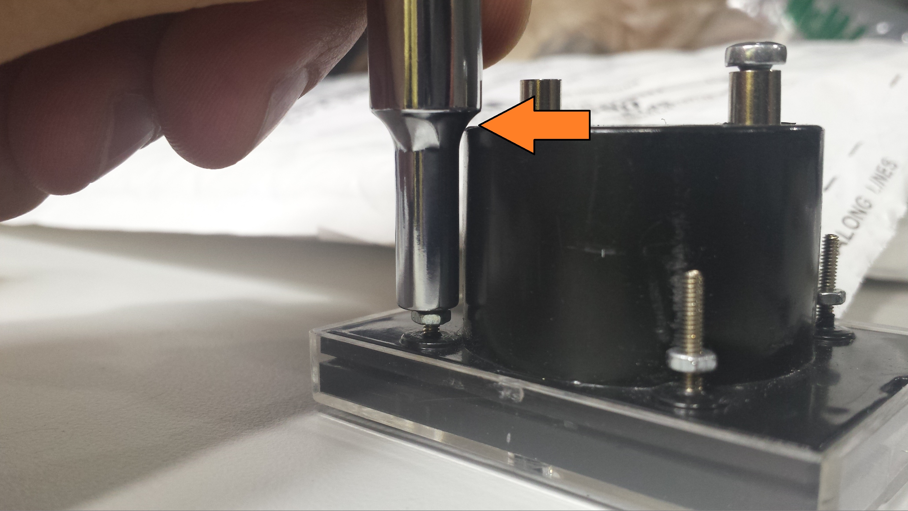
Photos/Blog Post Material/March/tbt 2.jpg
