awkwardengineer/Clock/Photos/Blog Post Material/more_with_less.JPG

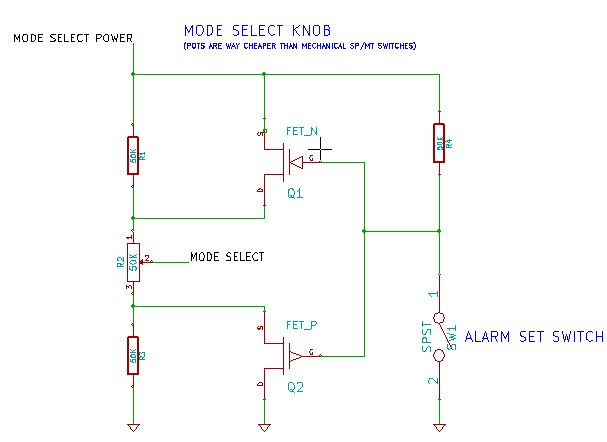
Photos/Blog Post Material/more_with_less.JPG
