awkwardengineer/Clock/Photos/Blog Post Material/New Doc 5_1.jpg

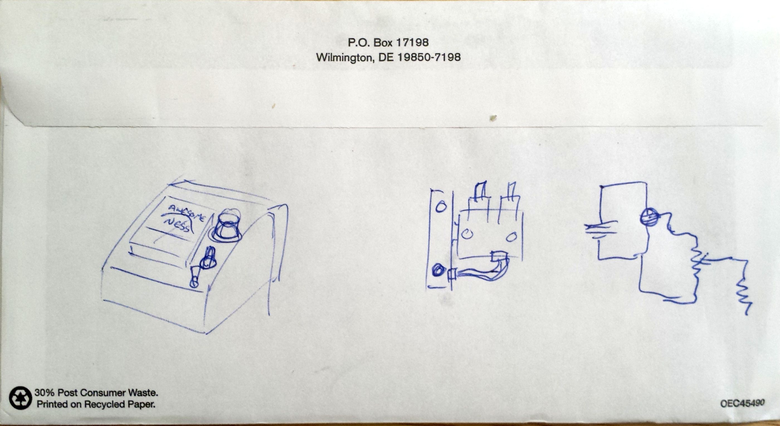
Photos/Blog Post Material/New Doc 5_1.jpg
