awkwardengineer/Clock/Photos/Blog Post Material/path_to_ground.jpg

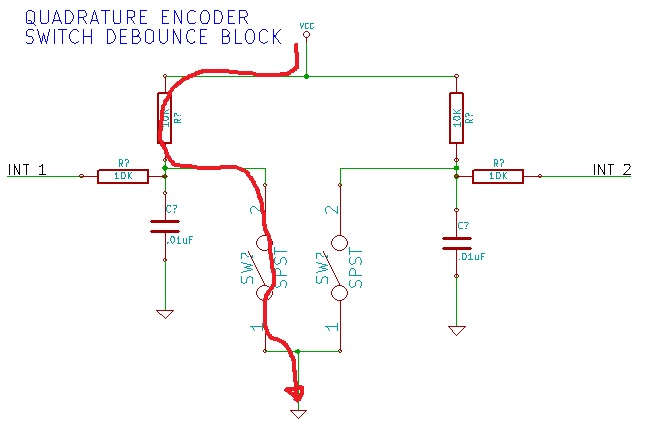
Photos/Blog Post Material/path_to_ground.jpg
