awkwardengineer/Clock/Photos/Blog Post Material/power saving code.png

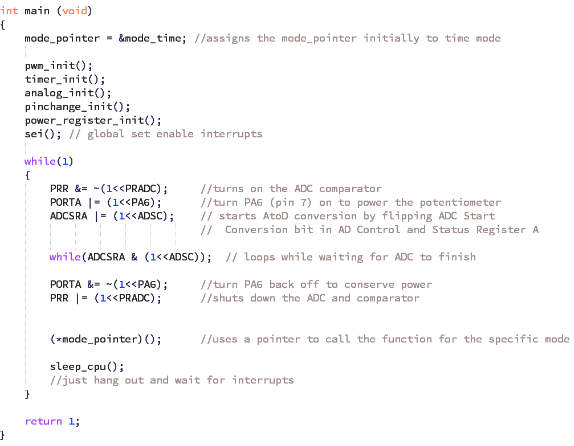
Photos/Blog Post Material/power saving code.png
