awkwardengineer/Clock/Photos/Blog Post Material/traffic and sales.png

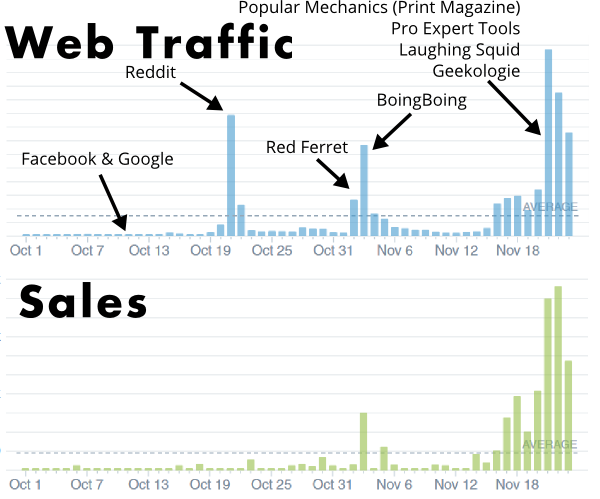
Photos/Blog Post Material/traffic and sales.png
