awkwardengineer/Clock/Photos/Blog Post Material/usbDetect.PNG

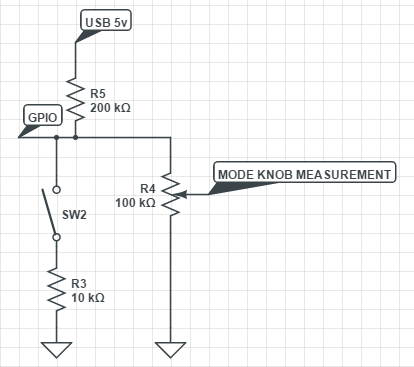
Photos/Blog Post Material/usbDetect.PNG
