awkwardengineer/Clock/Mechanical/CAD/AWK-105-0002.SLDPRT

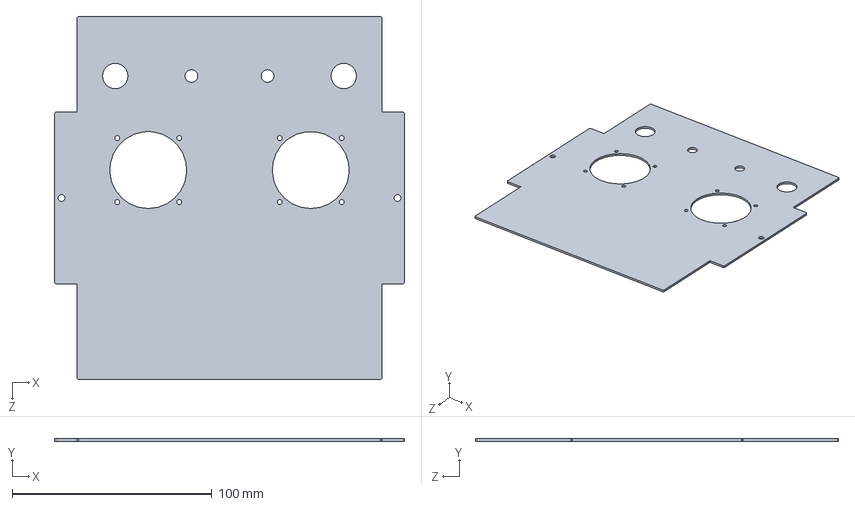
[picture p258: CAD file, 2016-03-23]
Mechanical/CAD/AWK-105-0002.SLDPRT
175.0 x 1.29 x 181.6 mm
