awkwardengineer/Clock/Mechanical/Design Memos/meter front face paper cutout/front face cutout.SLDPRT

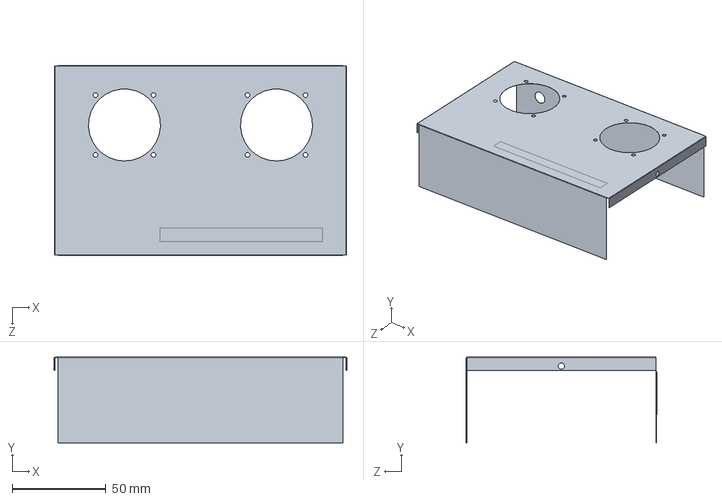
[picture p259: CAD file, 2015-07-05]
Mechanical/Design Memos/meter front face paper cutout/front face cutout.SLDPRT
156.1 x 45.8 x 101.7 mm
