awkwardengineer/Clock/Mechanical/Reference Material/BK-92.STEP

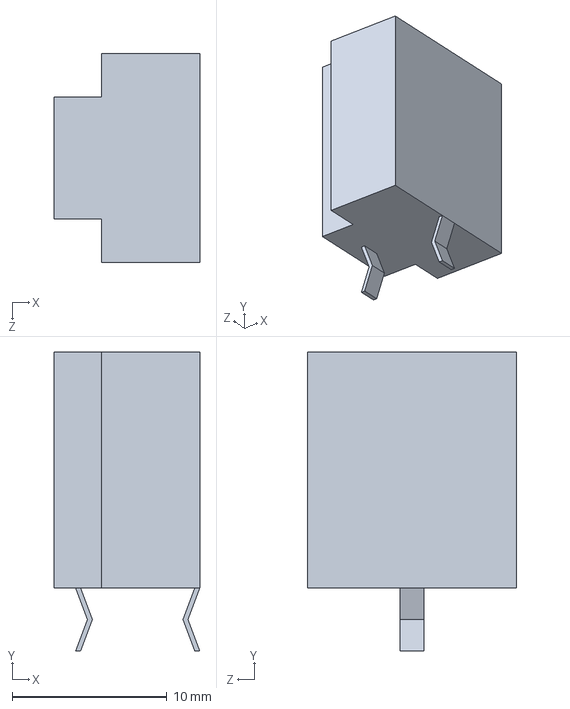
[picture p260: CAD file, 2015-03-23]
Mechanical/Reference Material/BK-92.STEP
9.40 x 19.3 x 13.5 mm
