awkwardengineer/Clock/Electrical/Design Memos/footprint test/footprint test.step

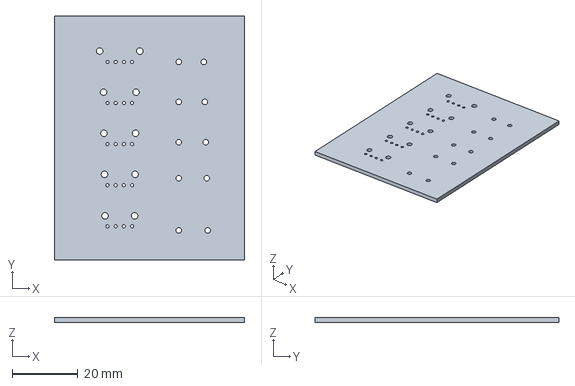
[picture p261: CAD file, 2015-05-18]
Electrical/Design Memos/footprint test/footprint test.step
57.8 x 74.2 x 1.52 mm
