awkwardengineer/Clock/Mechanical/A SIDE.SLDPRT

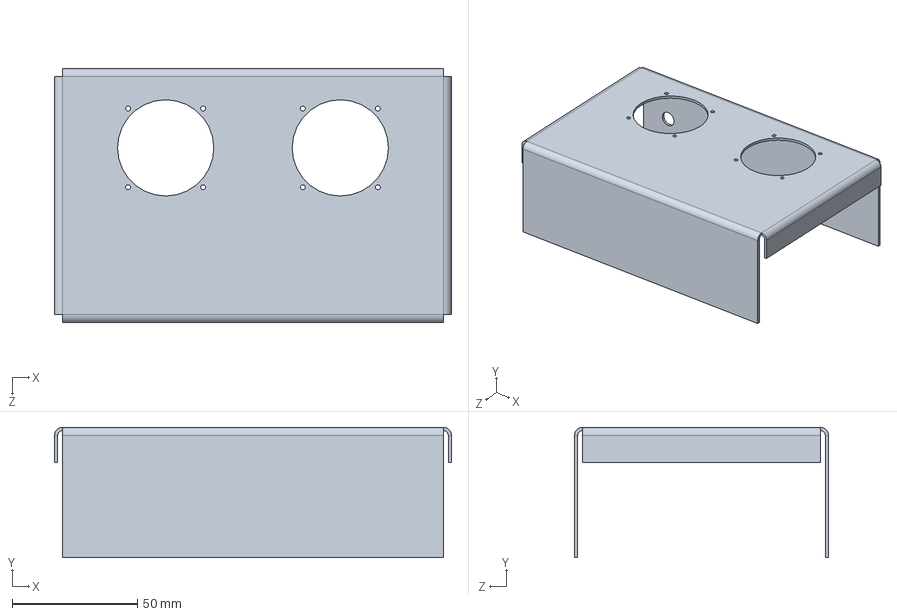
[picture p262: CAD file, 2014-03-26]
Mechanical/A SIDE.SLDPRT
158.8 x 52.1 x 101.6 mm
