awkwardengineer/Clock/Mechanical/Artwork/REFERENCE back flat pattern.DXF

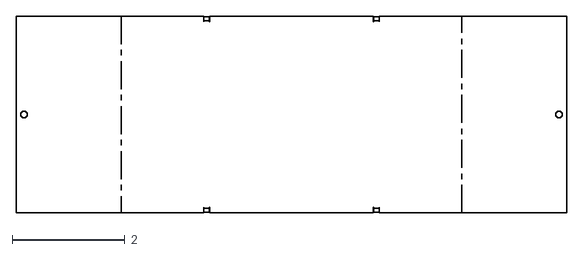
[picture p263: CAD file, 2015-07-05]
Mechanical/Artwork/REFERENCE back flat pattern.DXF
9.78 x 3.50
