awkwardengineer/Clock/Mechanical/Design Memos/meter front face paper cutout/Draw1.DXF

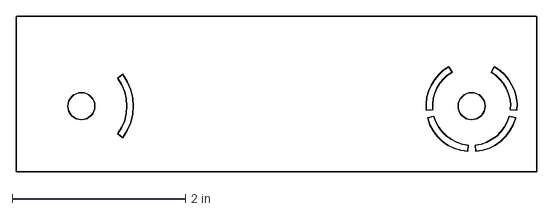
[picture p264: CAD file, 2015-07-05]
Mechanical/Design Memos/meter front face paper cutout/Draw1.DXF
6.00 x 1.79 in
