awkwardengineer/Clock/Mechanical/Quotes/Case/AWK-105-0002 revH.SLDPRT

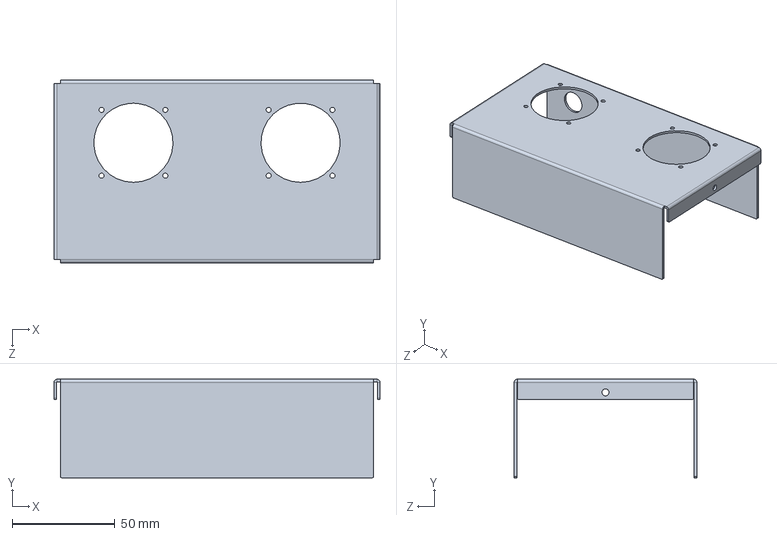
[picture p265: CAD file, 2015-12-17]
Mechanical/Quotes/Case/AWK-105-0002 revH.SLDPRT
158.5 x 48.0 x 88.9 mm
