awkwardengineer/Clock/Mechanical/Reference Material/davies 1910 knob.stp

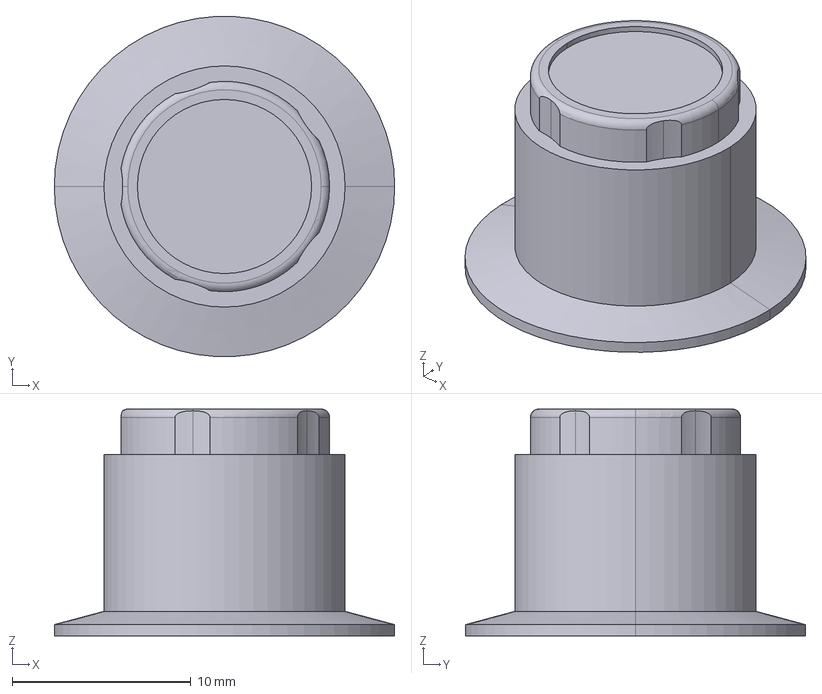
[picture p266: CAD file, 2015-03-06]
Mechanical/Reference Material/davies 1910 knob.stp
19.1 x 19.0 x 12.7 mm
