awkwardengineer/Clock/Mechanical/Artwork/REFERENCE front flat pattern.DXF

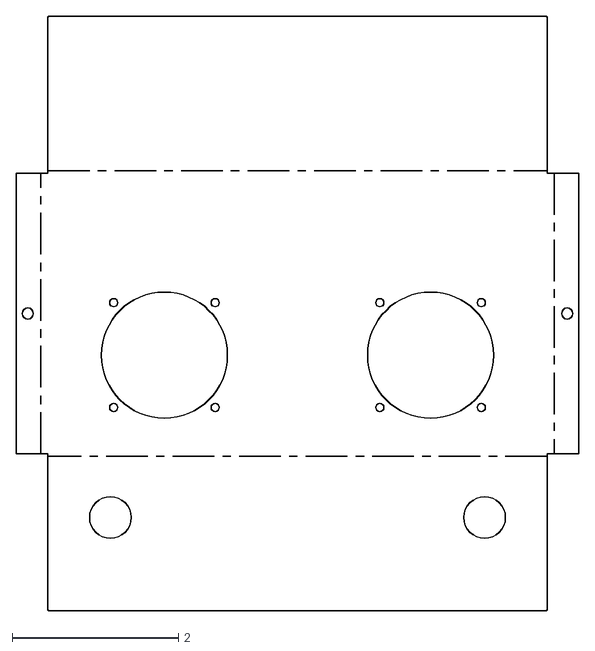
[picture p267: CAD file, 2015-07-05]
Mechanical/Artwork/REFERENCE front flat pattern.DXF
6.76 x 7.15
