awkwardengineer/Clock/Mechanical/Design Memos/meter front face paper cutout/Flat pattern - front face cutout.DXF

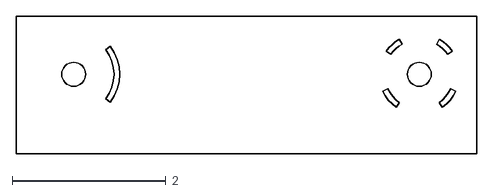
[picture p268: CAD file, 2015-07-05]
Mechanical/Design Memos/meter front face paper cutout/Flat pattern - front face cutout.DXF
6.00 x 1.79
