awkwardengineer/Clock/Mechanical/Reference Material/ptv111-2420a.stp

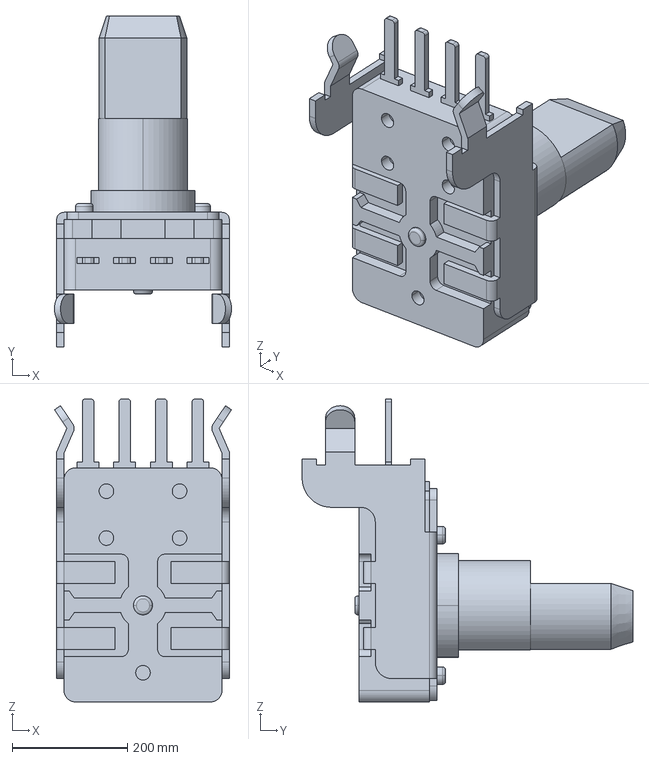
[picture p269: CAD file, 2014-07-22]
Mechanical/Reference Material/ptv111-2420a.stp
307.3 x 574.0 x 525.8 mm
