awkwardengineer/Clock/Mechanical/Artwork/REFERENCE box outlines.DXF

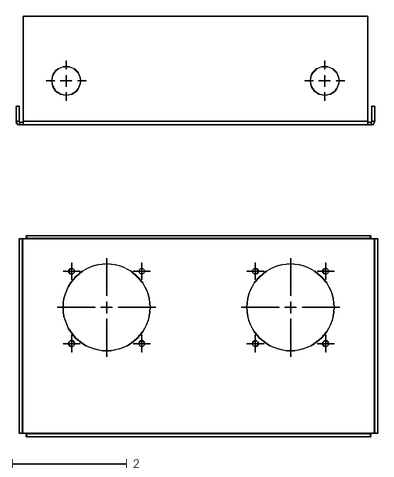
[picture p270: CAD file, 2015-07-05]
Mechanical/Artwork/REFERENCE box outlines.DXF
6.30 x 7.31
