awkwardengineer/Clock/Mechanical/CAD/AWK-105-0036.SLDPRT

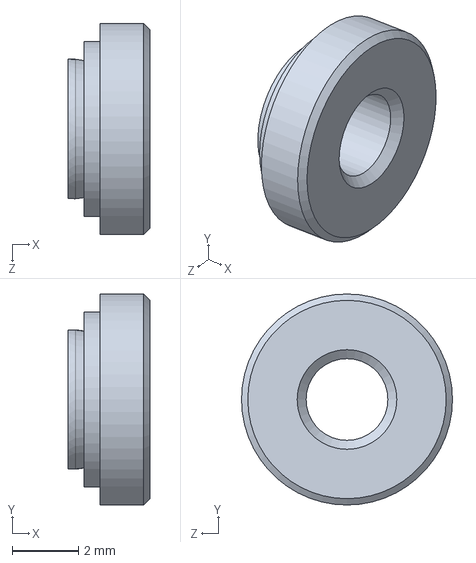
[picture p271: CAD file, 2015-10-14]
Mechanical/CAD/AWK-105-0036.SLDPRT
2.47 x 6.35 x 6.35 mm
