awkwardengineer/Clock/Mechanical/CAD/AWK-105-0014.SLDPRT

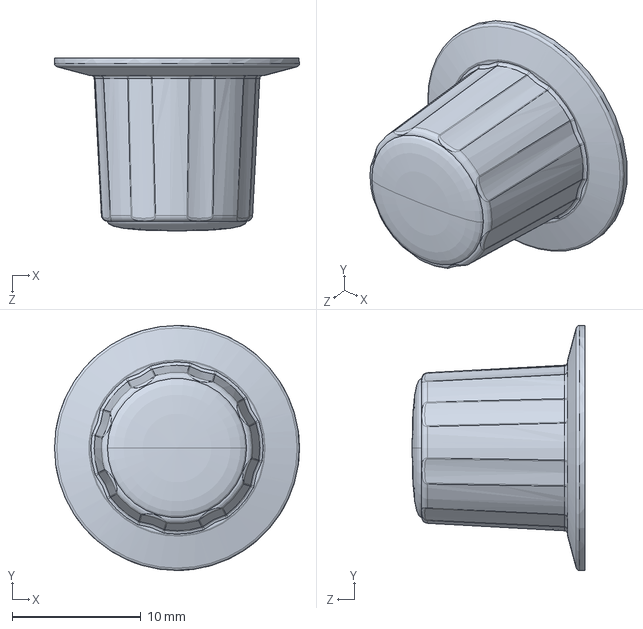
[picture p272: CAD file, 2015-10-14]
Mechanical/CAD/AWK-105-0014.SLDPRT
19.1 x 19.1 x 13.5 mm
