awkwardengineer/Clock/Mechanical/CAD/AWK-105-0019.SLDPRT

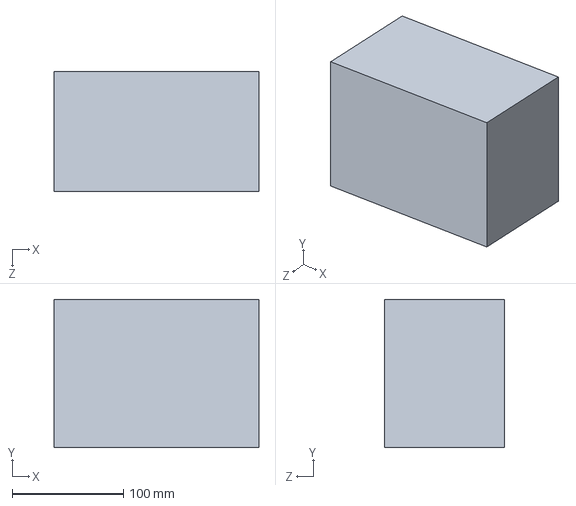
[picture p273: CAD file, 2015-10-14]
Mechanical/CAD/AWK-105-0019.SLDPRT
184.1 x 133.4 x 107.9 mm
