awkwardengineer/Clock/Mechanical/CAD/AWK-105-0008.SLDPRT

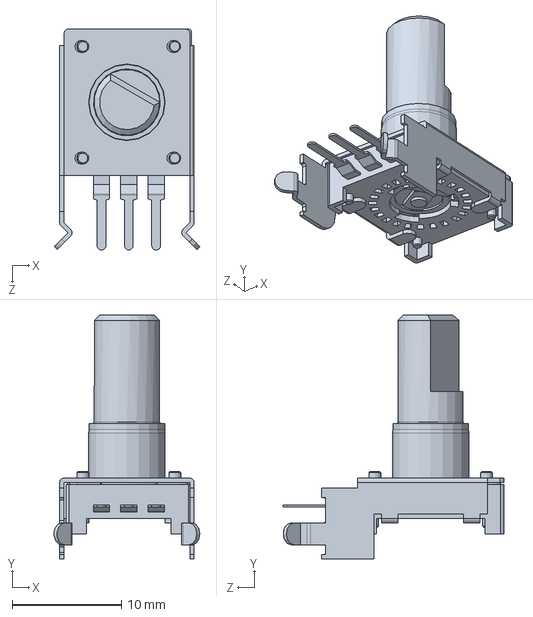
[picture p274: CAD file, 2015-10-14]
Mechanical/CAD/AWK-105-0008.SLDPRT
13.3 x 22.3 x 20.2 mm
