awkwardengineer/Clock/Mechanical/CAD/AWK-105-0001-H.SLDPRT

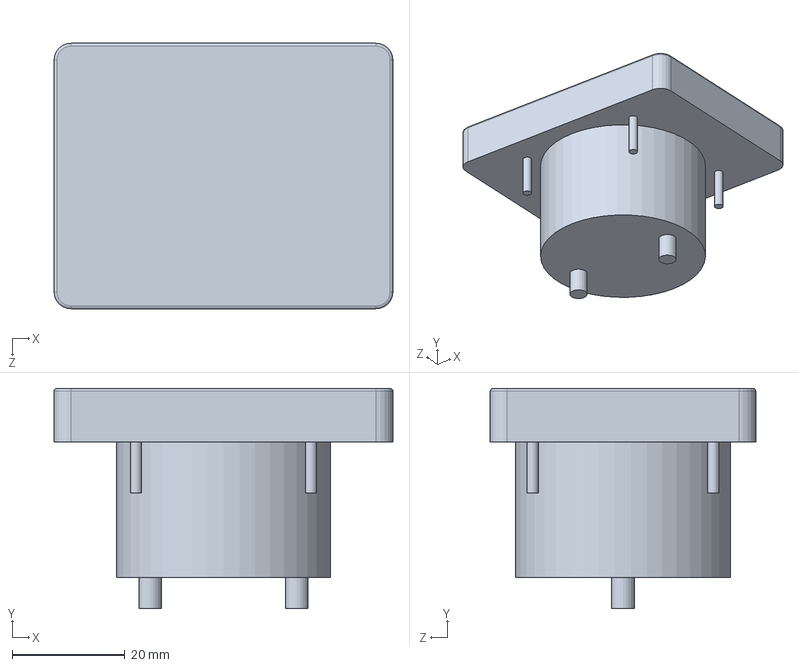
[picture p275: CAD file, 2015-10-14]
Mechanical/CAD/AWK-105-0001-H.SLDPRT
60.0 x 39.0 x 47.0 mm
