awkwardengineer/Clock/Mechanical/CAD/AWK-105-0032.SLDPRT

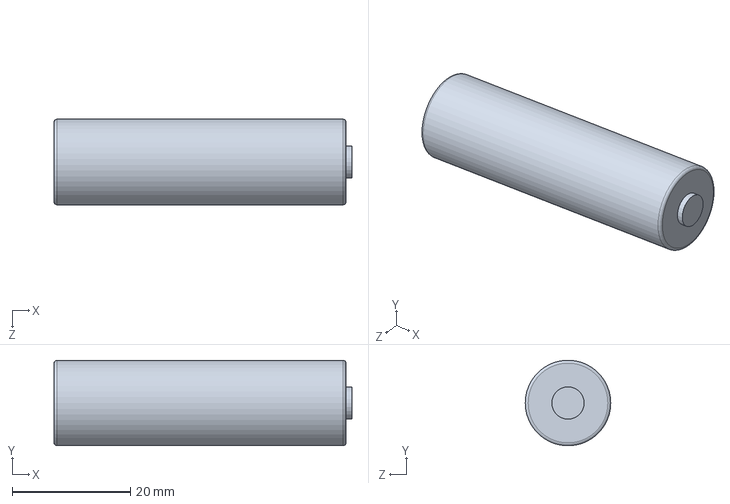
[picture p276: CAD file, 2015-10-14]
Mechanical/CAD/AWK-105-0032.SLDPRT
50.5 x 14.5 x 14.5 mm
