awkwardengineer/Clock/Mechanical/CAD/AWK-105-0018.SLDPRT

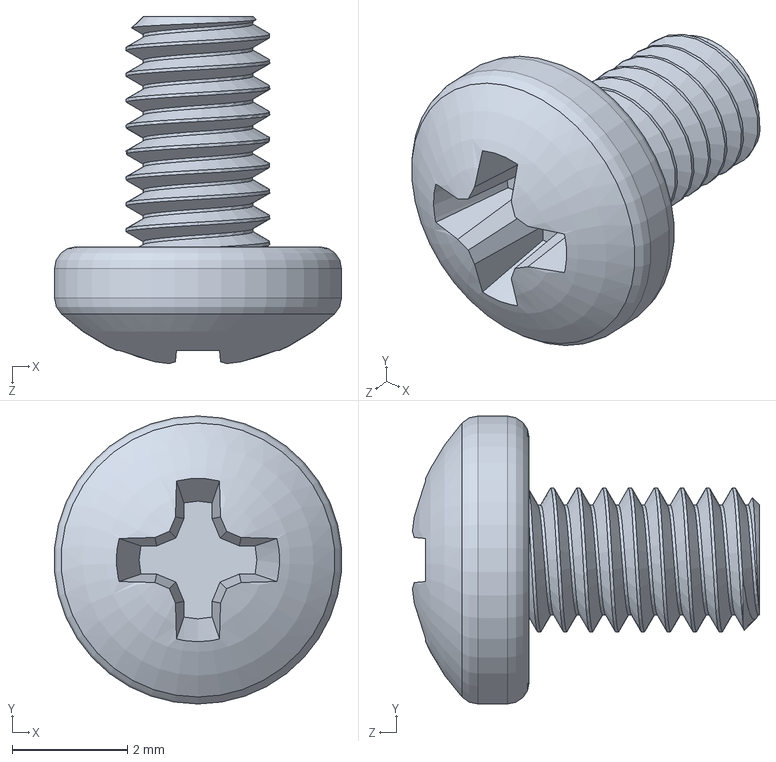
[picture p277: CAD file, 2015-08-24]
Mechanical/CAD/AWK-105-0018.SLDPRT
4.98 x 5.00 x 6.03 mm
