awkwardengineer/Clock/Mechanical/CAD/AWK-105-0026.SLDPRT

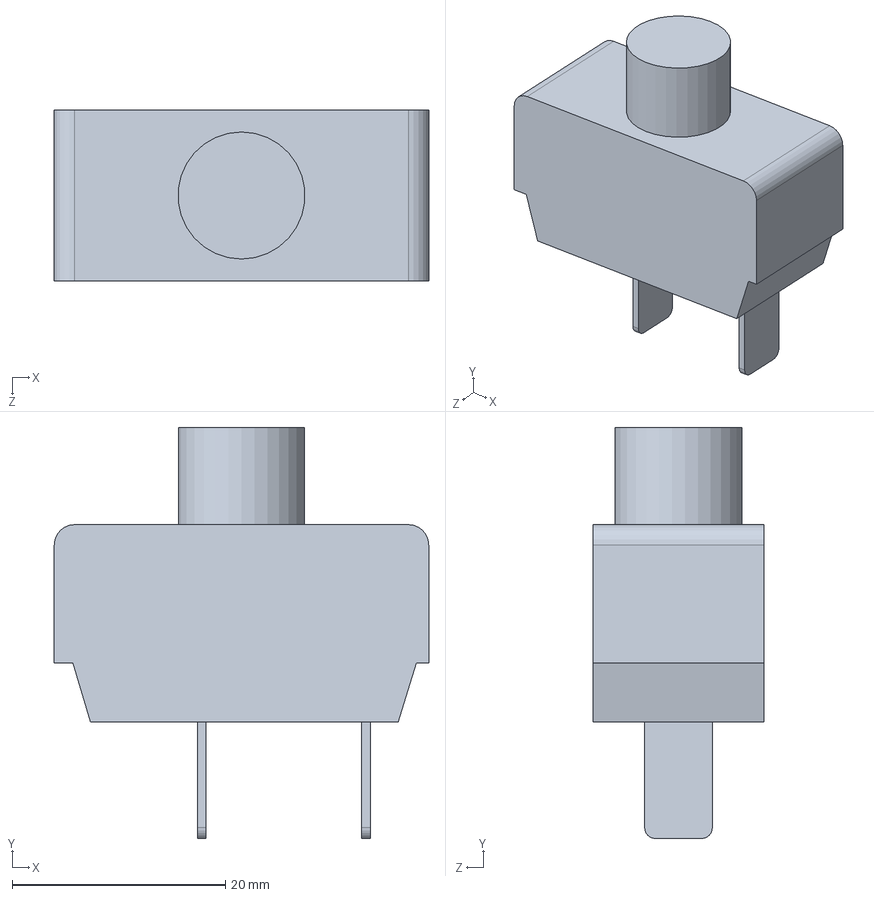
[picture p278: CAD file, 2015-08-24]
Mechanical/CAD/AWK-105-0026.SLDPRT
35.1 x 38.5 x 16.0 mm
