awkwardengineer/Clock/Mechanical/CAD/AWK-105-0028.SLDPRT

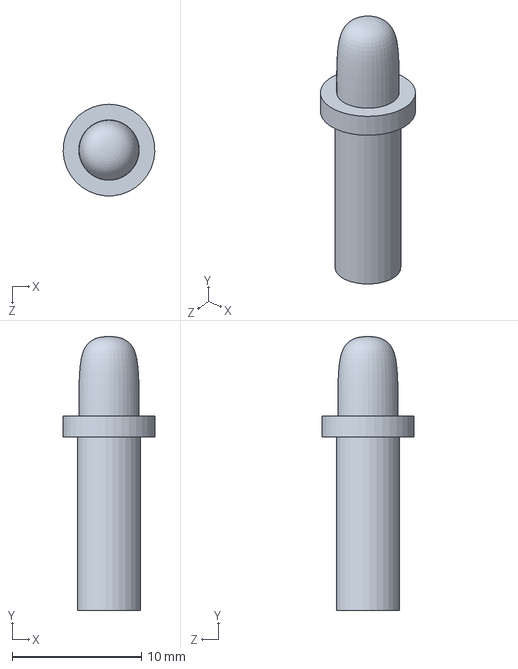
[picture p279: CAD file, 2015-08-24]
Mechanical/CAD/AWK-105-0028.SLDPRT
7.10 x 21.2 x 7.10 mm
