awkwardengineer/Clock/Mechanical/CAD/AWK-105-0027.SLDPRT

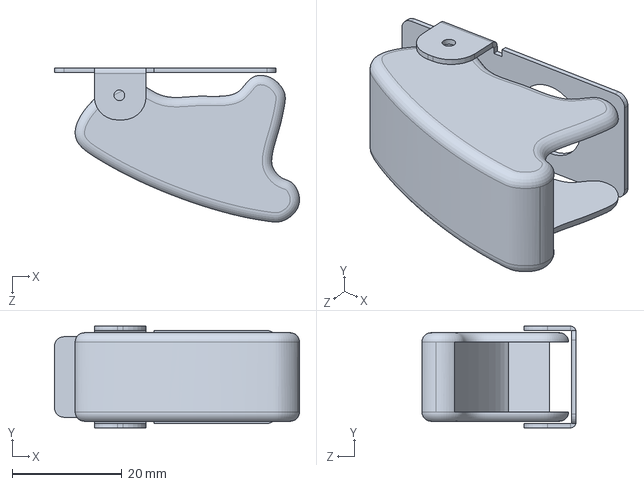
[picture p280: CAD file, 2015-08-24]
Mechanical/CAD/AWK-105-0027.SLDPRT
44.7 x 18.6 x 28.2 mm
