awkwardengineer/Clock/Mechanical/CAD/AWK-105-0009.SLDPRT

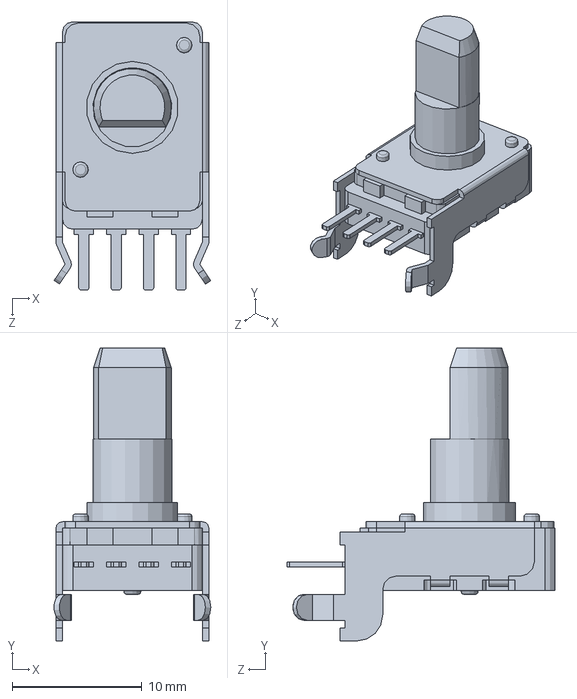
[picture p281: CAD file, 2015-08-24]
Mechanical/CAD/AWK-105-0009.SLDPRT
12.1 x 22.6 x 20.7 mm
