awkwardengineer/Clock/Mechanical/CAD/AWK-105-0012.SLDPRT

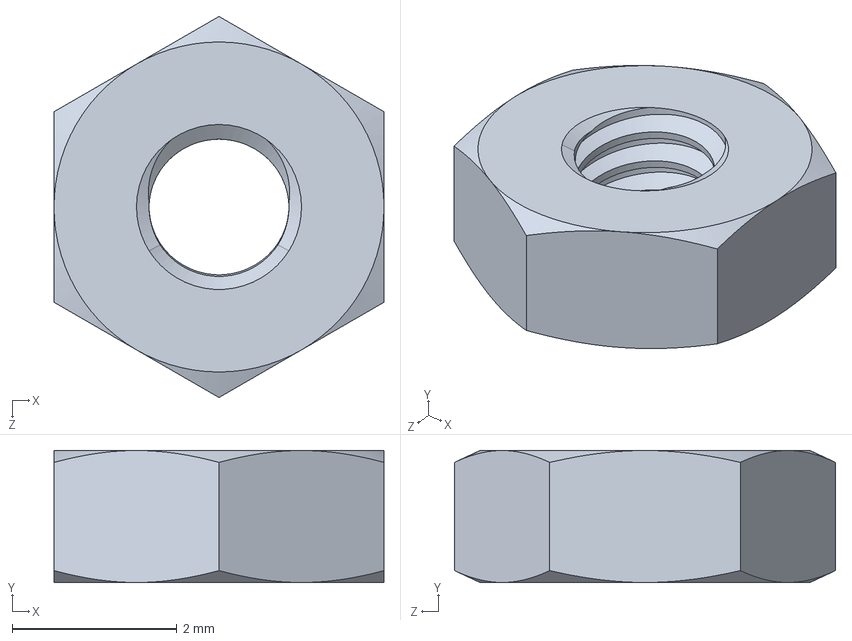
[picture p282: CAD file, 2015-04-25]
Mechanical/CAD/AWK-105-0012.SLDPRT
4.00 x 1.60 x 4.62 mm
