awkwardengineer/Clock/Mechanical/CAD/AWK-105-0014 Cosmetic.SLDPRT

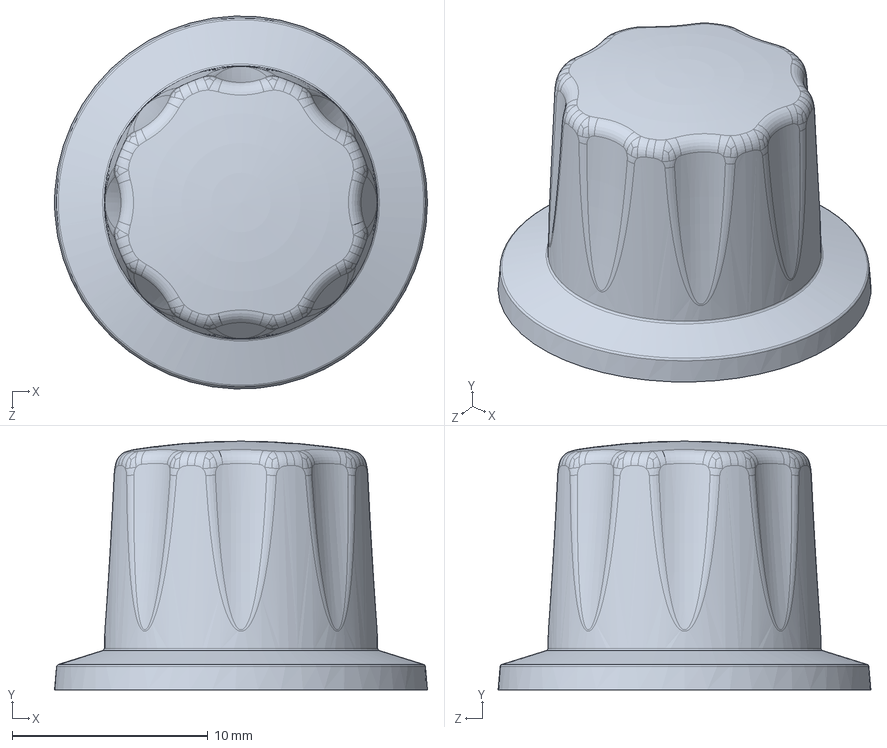
[picture p283: CAD file, 2015-04-25]
Mechanical/CAD/AWK-105-0014 Cosmetic.SLDPRT
19.1 x 12.7 x 19.0 mm
