awkwardengineer/Clock/Mechanical/CAD/bk-92.SLDPRT

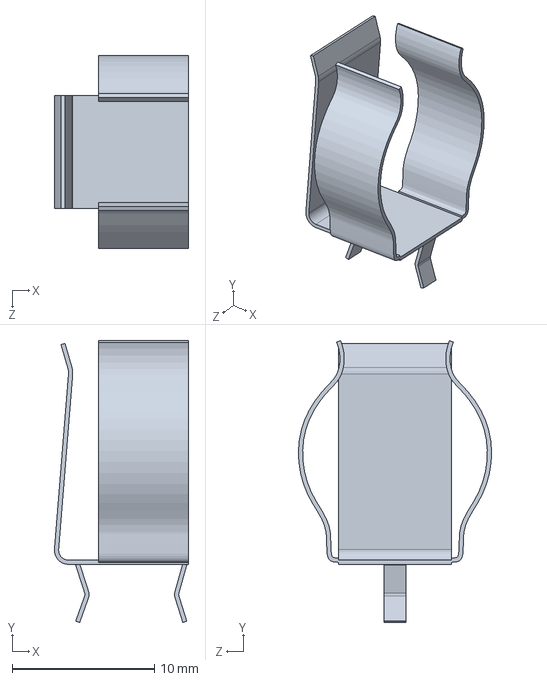
[picture p284: CAD file, 2015-03-23]
Mechanical/CAD/bk-92.SLDPRT
9.43 x 19.8 x 13.6 mm
