awkwardengineer/Clock/Mechanical/CAD/AWK-105-0013.SLDPRT

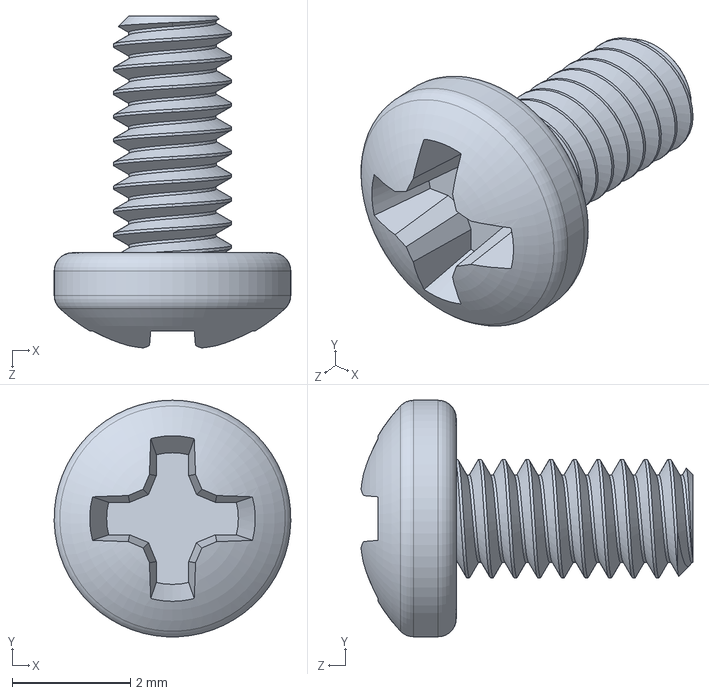
[picture p285: CAD file, 2014-11-13]
Mechanical/CAD/AWK-105-0013.SLDPRT
4.00 x 4.00 x 5.61 mm
