awkwardengineer/Clock/Mechanical/CAD/PTV111-3415A.stp

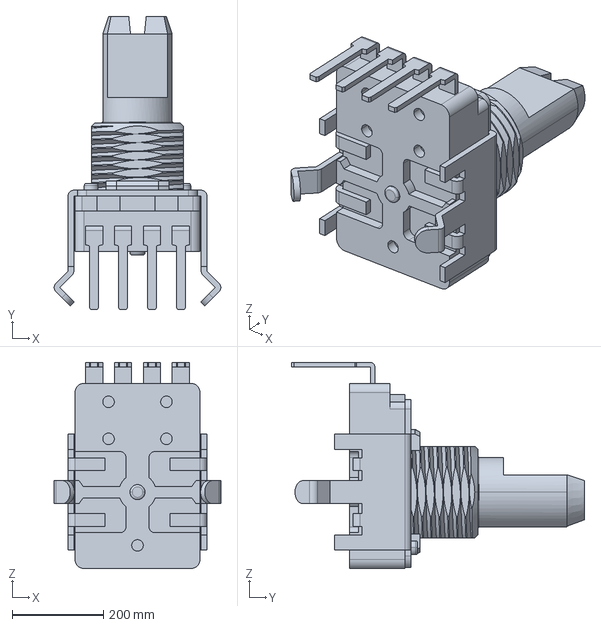
[picture p286: CAD file, 2014-07-17]
Mechanical/CAD/PTV111-3415A.stp
365.7 x 642.6 x 452.1 mm
