awkwardengineer/Clock/Mechanical/CAD/PEC12-2125F.STP

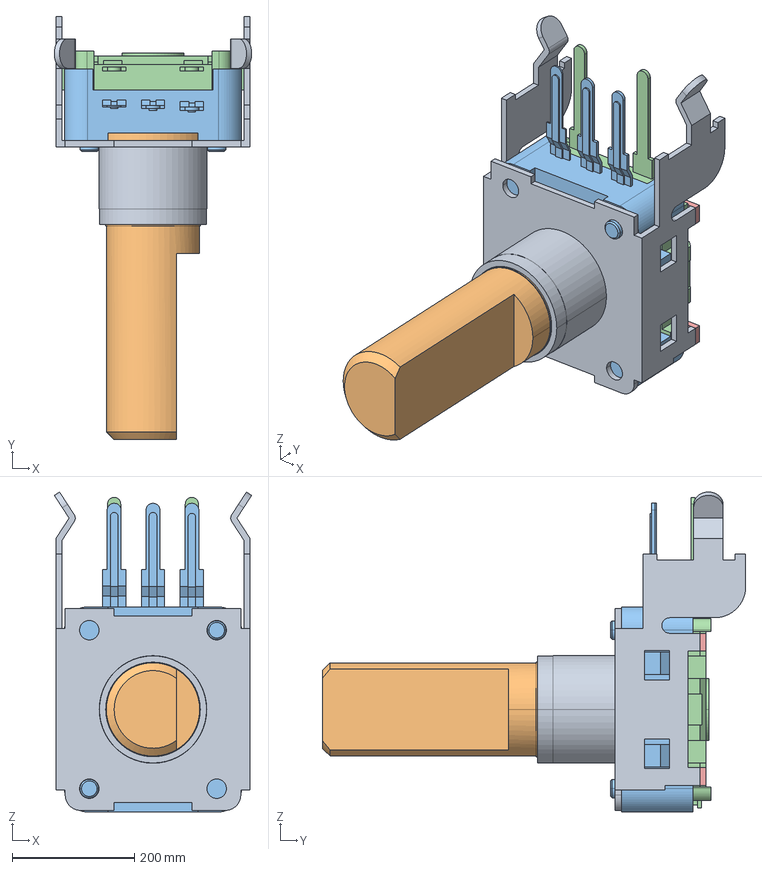
[picture p287: CAD file, 2014-07-17]
Mechanical/CAD/PEC12-2125F.STP
322.6 x 692.1 x 523.0 mm
EA12133_AF1
EI12139
EB12121
ES12124
PRT0002
