awkwardengineer/Clock/Mechanical/CAD/AWK-105-0011.SLDPRT

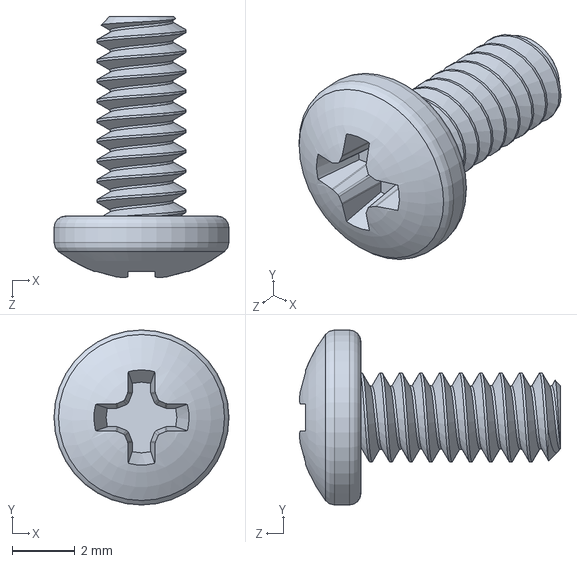
[picture p288: CAD file, 2014-06-24]
Mechanical/CAD/AWK-105-0011.SLDPRT
5.56 x 5.56 x 8.31 mm
