awkwardengineer/Clock/Mechanical/CAD/Faceplate.SLDPRT

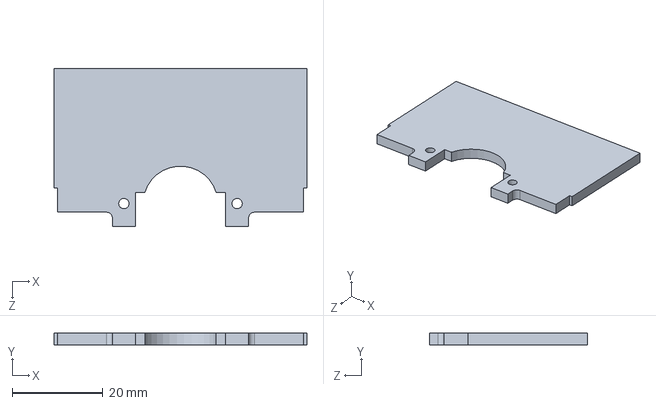
[picture p289: CAD file, 2014-04-25]
Mechanical/CAD/Faceplate.SLDPRT
55.9 x 2.54 x 34.9 mm
