awkwardengineer/Clock/Mechanical/CAD/AWK-105-0007.DXF

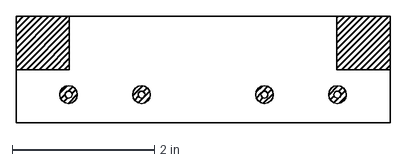
[picture p290: CAD file, 2014-03-26]
Mechanical/CAD/AWK-105-0007.DXF
5.25 x 1.50 in
