awkwardengineer/Clock/Mechanical/CAD/ENCODER CARTOON.SLDPRT

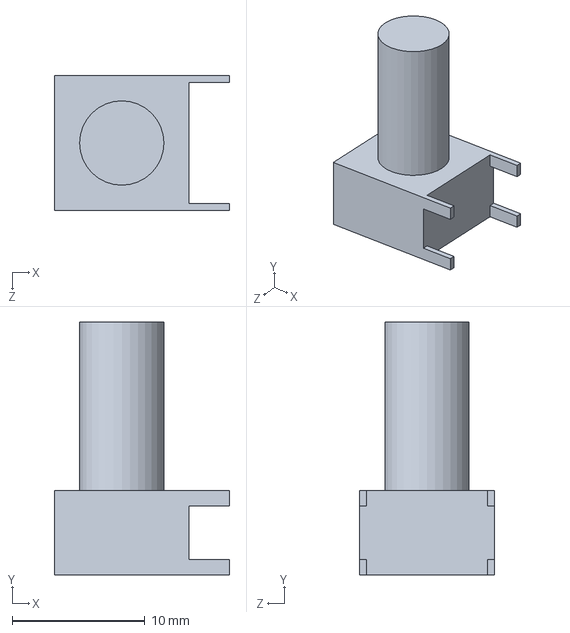
[picture p291: CAD file, 2014-03-26]
Mechanical/CAD/ENCODER CARTOON.SLDPRT
13.2 x 19.0 x 10.2 mm
