awkwardengineer/Clock/Mechanical/CAD/Jameco 316603.SLDPRT

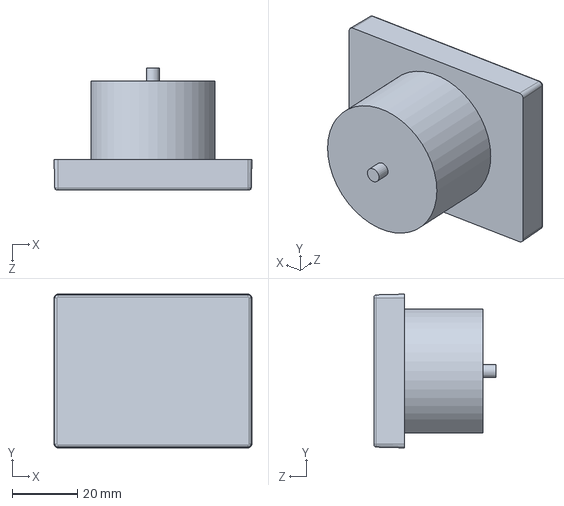
[picture p292: CAD file, 2014-03-26]
Mechanical/CAD/Jameco 316603.SLDPRT
60.5 x 47.0 x 37.3 mm
