awkwardengineer/Clock/Mechanical/Quotes/Full Turnkey Assembly/AWK-105-0033 instruction sheet.pdf

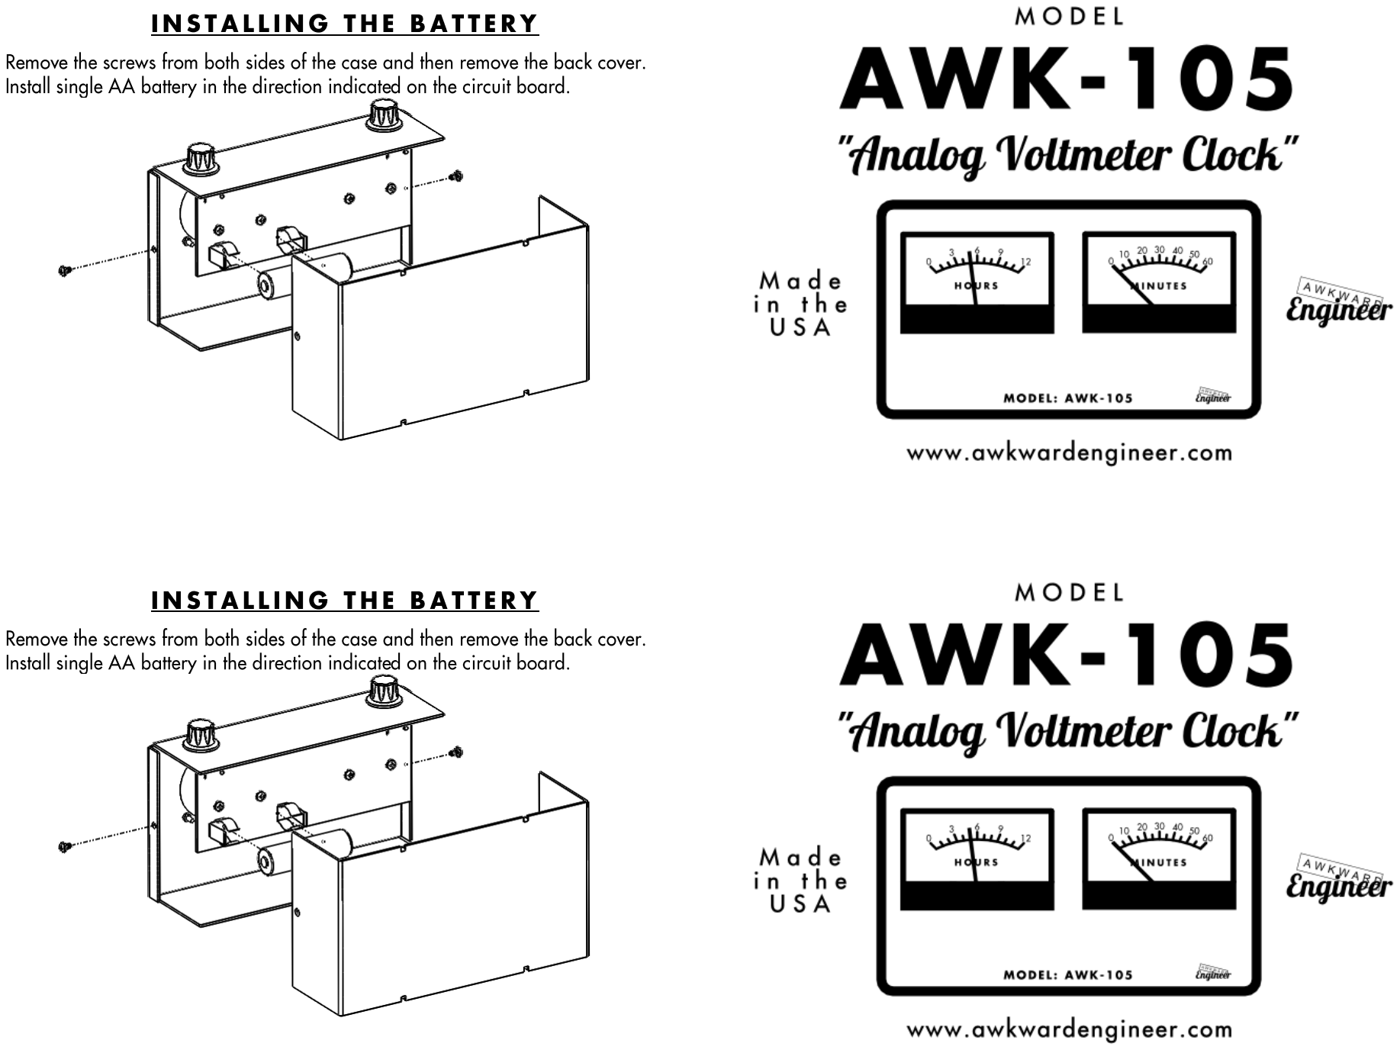
[picture p294: page 1]
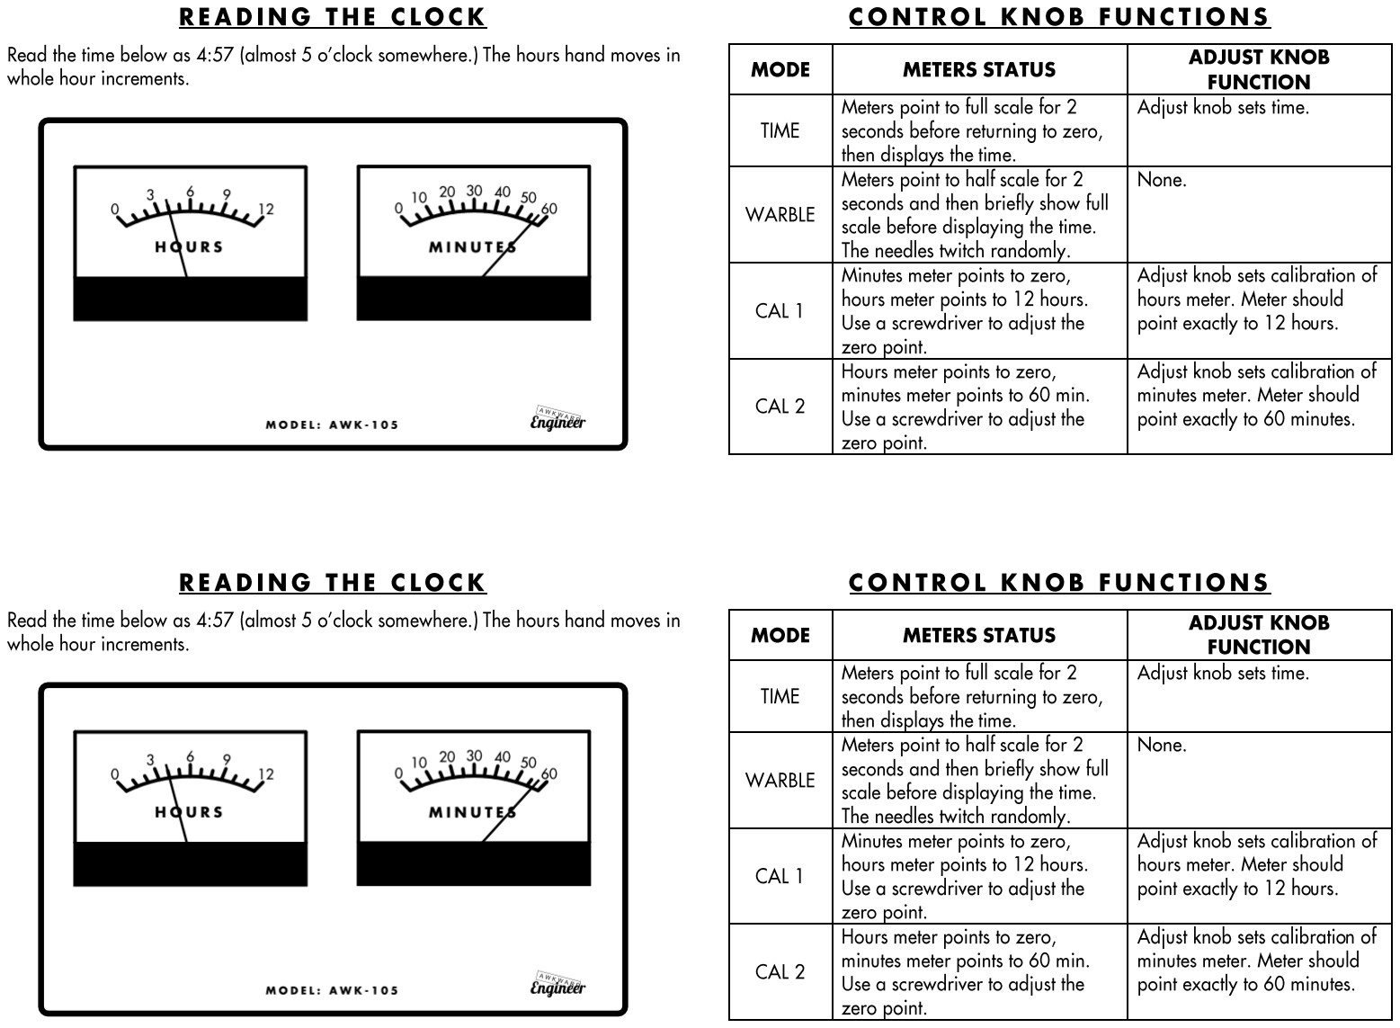
[picture p295: page 2]
