awkwardengineer/Clock/Mechanical/Assembly Pics/20150322_172204.jpg

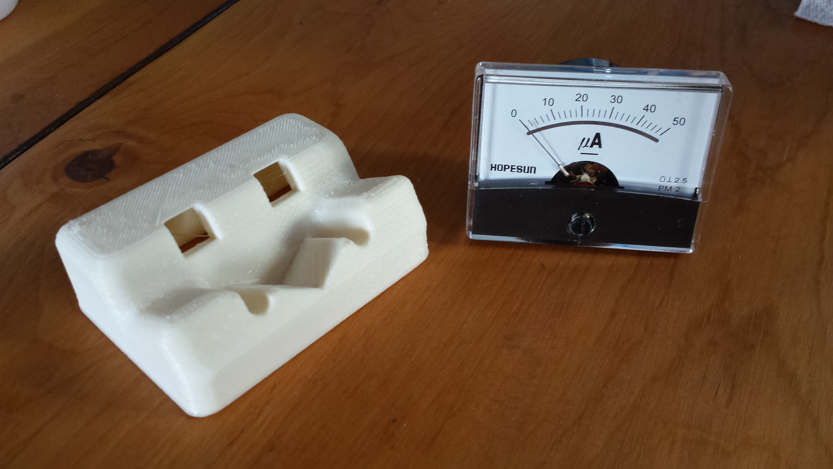
Mechanical/Assembly Pics/20150322_172204.jpg
