awkwardengineer/Clock/Mechanical/Assembly Pics/20150503_135418.jpg

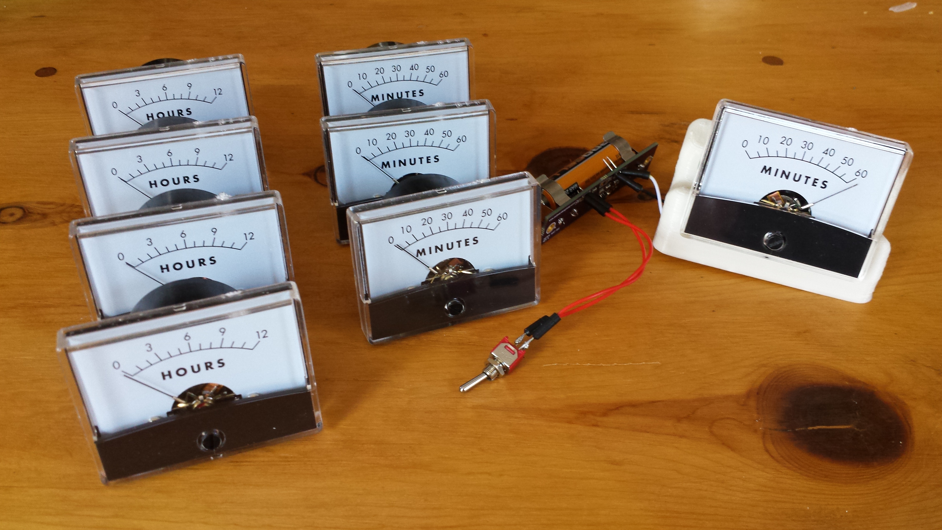
Mechanical/Assembly Pics/20150503_135418.jpg
