awkwardengineer/Clock/Mechanical/Assembly Pics/20150617_092149.jpg

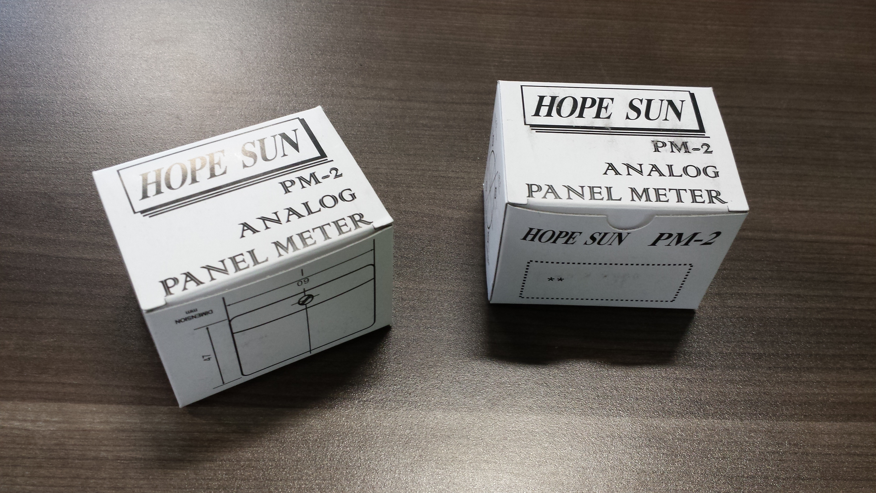
Mechanical/Assembly Pics/20150617_092149.jpg
