awkwardengineer/Clock/Mechanical/Assembly Pics/20150617_092314.jpg

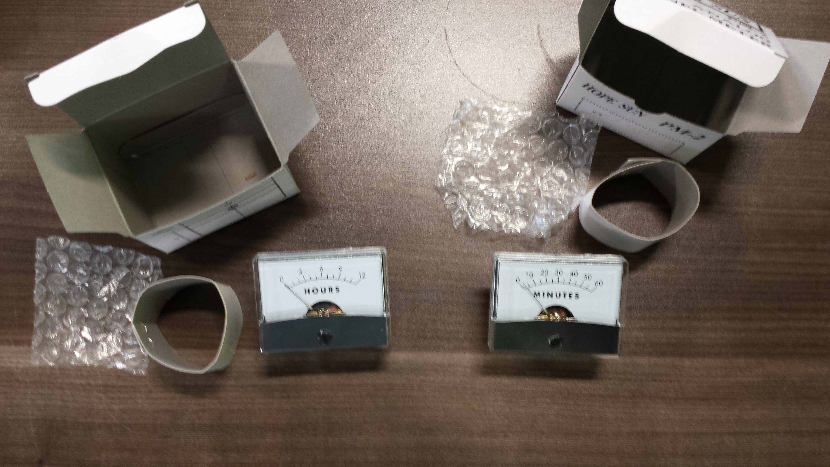
Mechanical/Assembly Pics/20150617_092314.jpg
