awkwardengineer/Clock/Mechanical/Assembly Pics/20150617_092450.jpg

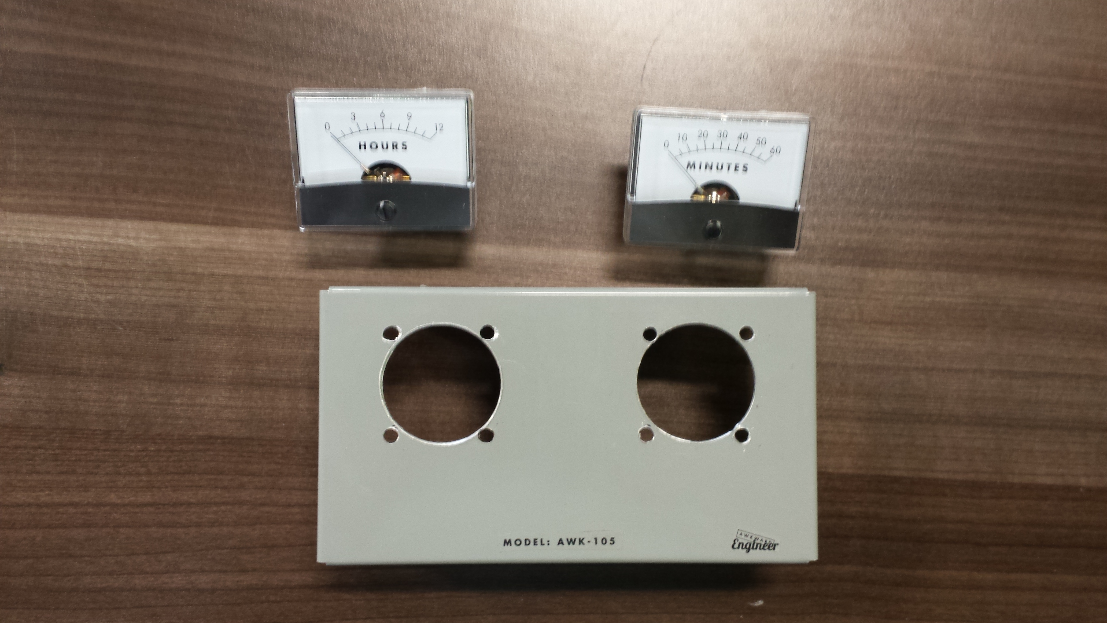
Mechanical/Assembly Pics/20150617_092450.jpg
