awkwardengineer/Clock/Mechanical/Assembly Pics/20150617_092522.jpg

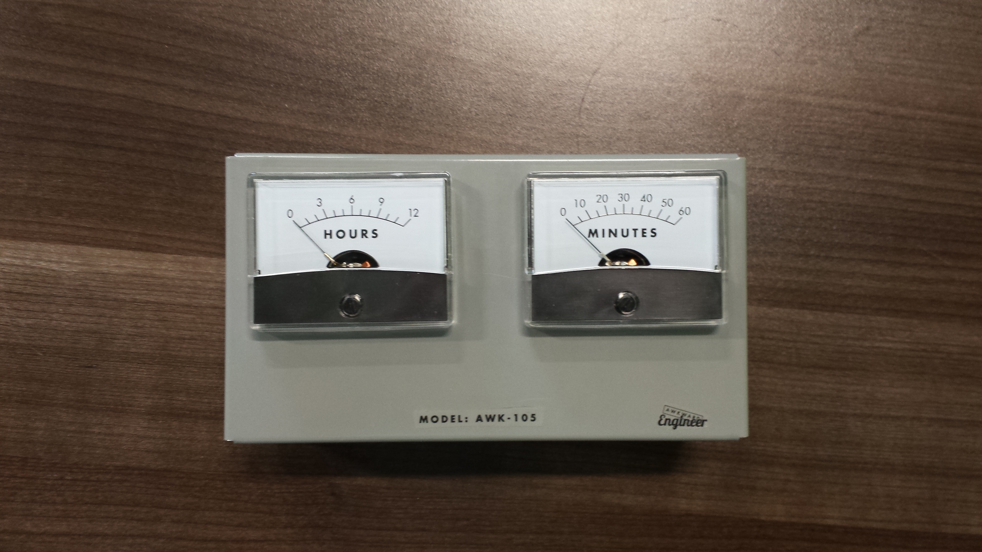
Mechanical/Assembly Pics/20150617_092522.jpg
