awkwardengineer/Clock/Mechanical/Assembly Pics/20150617_092629.jpg

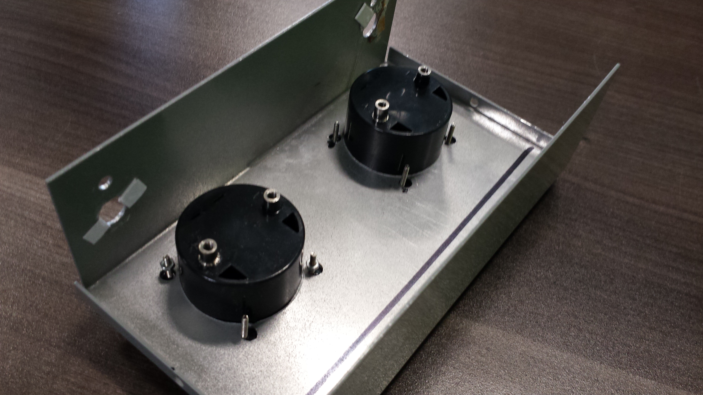
Mechanical/Assembly Pics/20150617_092629.jpg
