awkwardengineer/Clock/Mechanical/Assembly Pics/20150617_093341.jpg

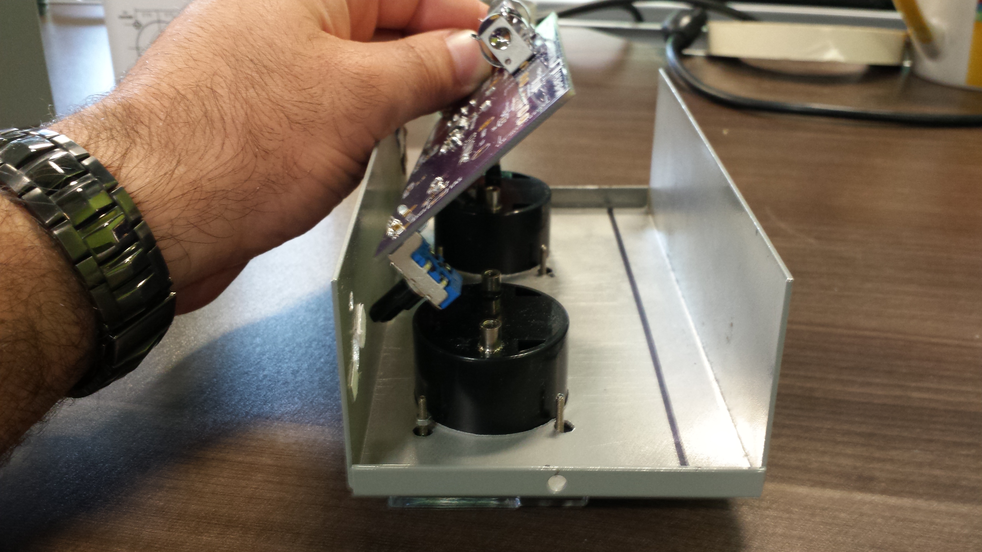
Mechanical/Assembly Pics/20150617_093341.jpg
