awkwardengineer/Clock/Mechanical/Assembly Pics/20150617_093510.jpg

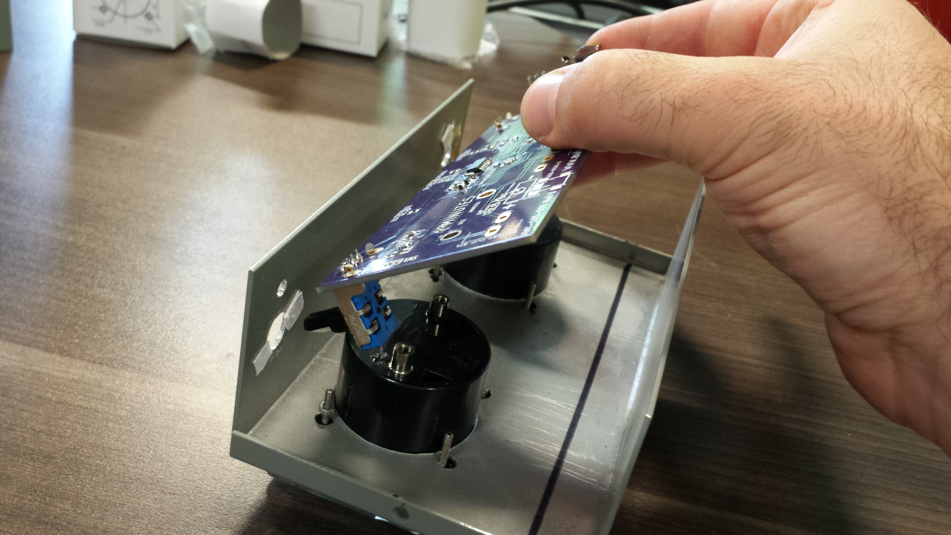
Mechanical/Assembly Pics/20150617_093510.jpg
