awkwardengineer/Clock/Mechanical/Assembly Pics/20150617_094124.jpg

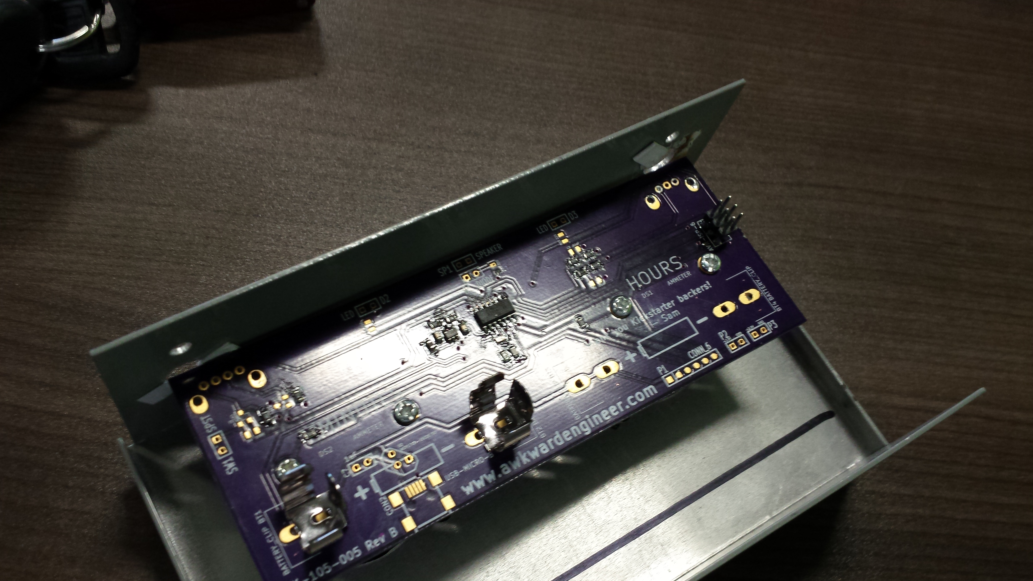
Mechanical/Assembly Pics/20150617_094124.jpg
