awkwardengineer/Clock/Mechanical/Assembly Pics/20150617_094423.jpg

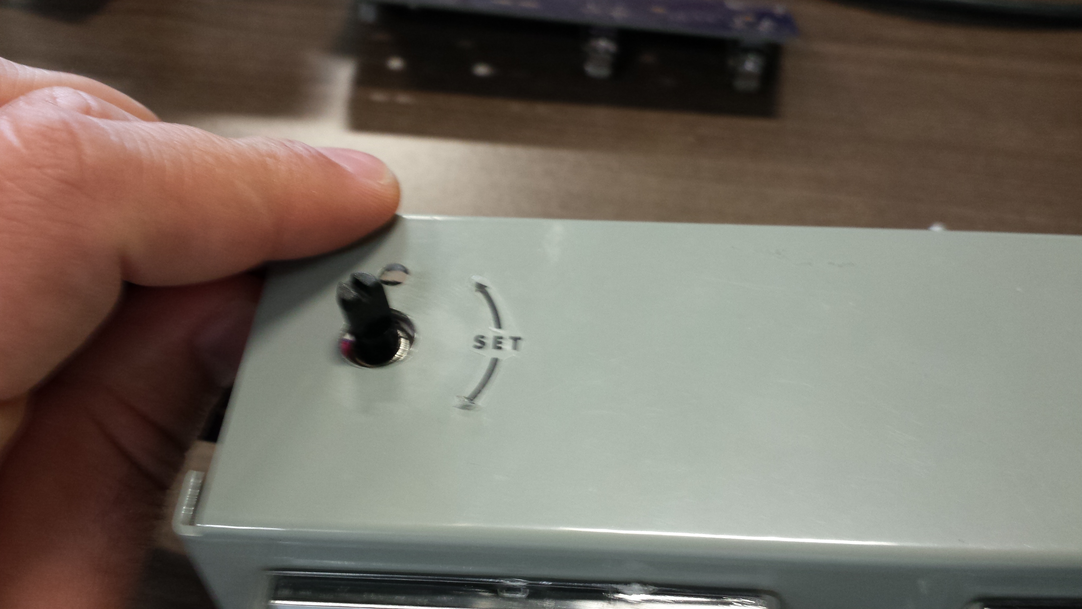
Mechanical/Assembly Pics/20150617_094423.jpg
