awkwardengineer/Clock/Mechanical/Assembly Pics/20150617_094558.jpg

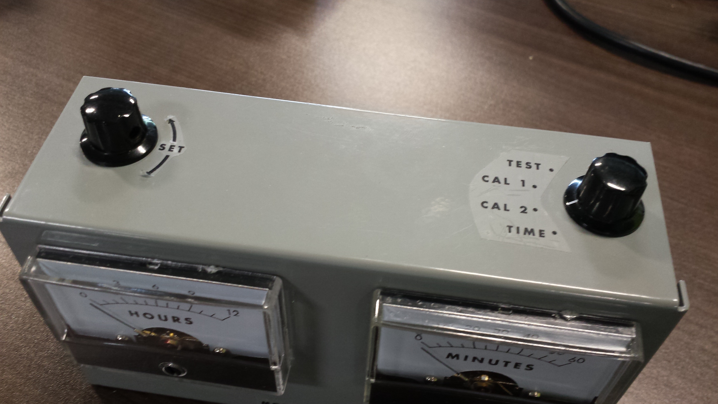
Mechanical/Assembly Pics/20150617_094558.jpg
