awkwardengineer/Clock/Mechanical/Assembly Pics/20150617_094918.jpg

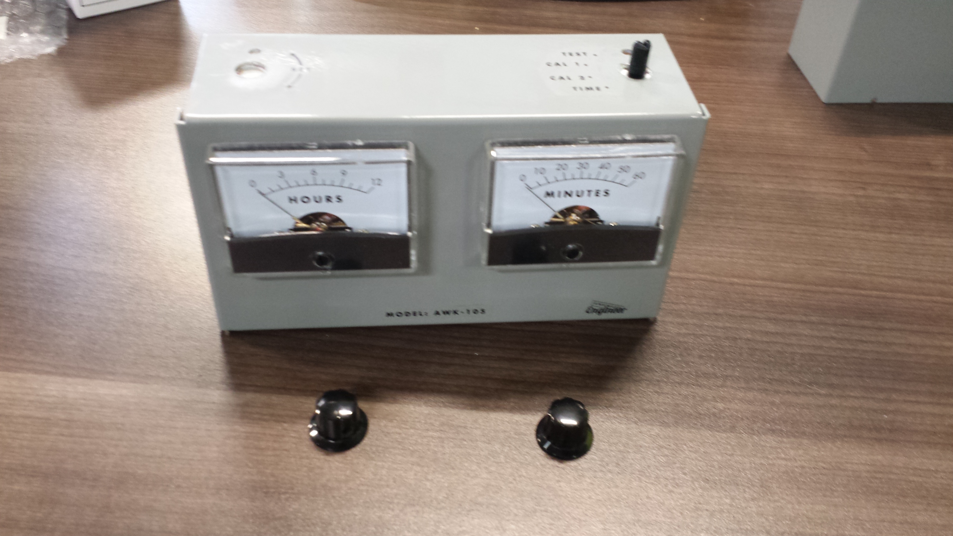
Mechanical/Assembly Pics/20150617_094918.jpg
