awkwardengineer/Clock/Mechanical/Assembly Pics/20150617_095010.jpg

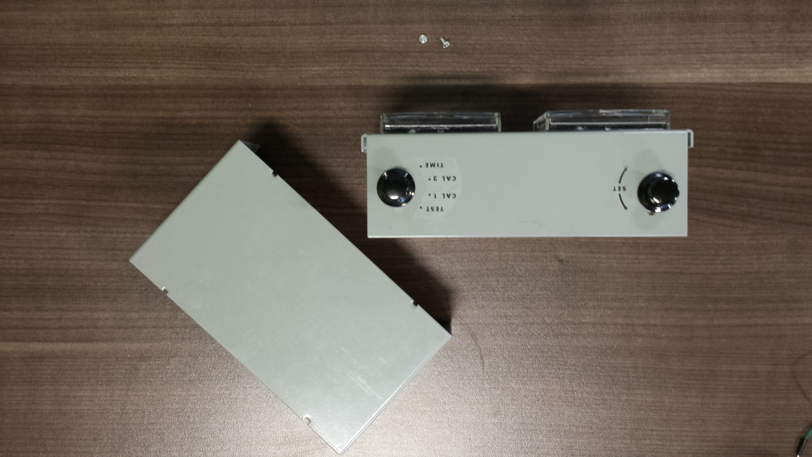
Mechanical/Assembly Pics/20150617_095010.jpg
