awkwardengineer/Clock/Mechanical/Assembly Pics/20150617_095140.jpg

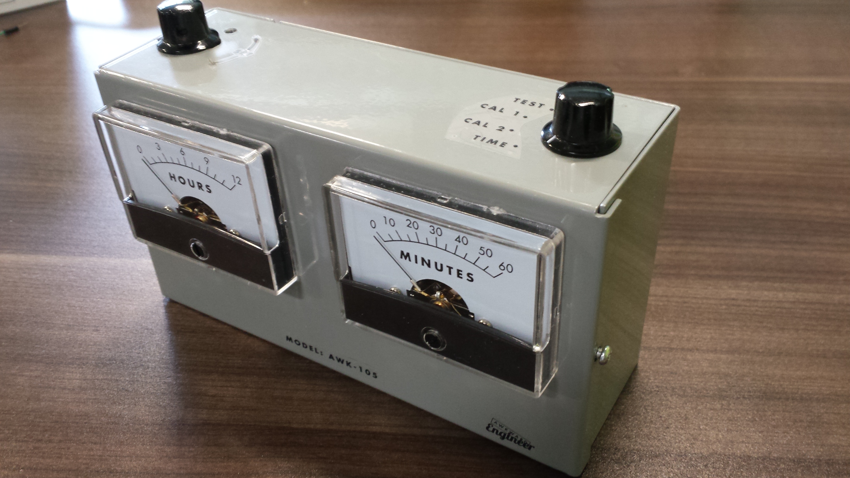
Mechanical/Assembly Pics/20150617_095140.jpg
