awkwardengineer/Clock/Media Campaign/Media Kit/mechanical assembly.png

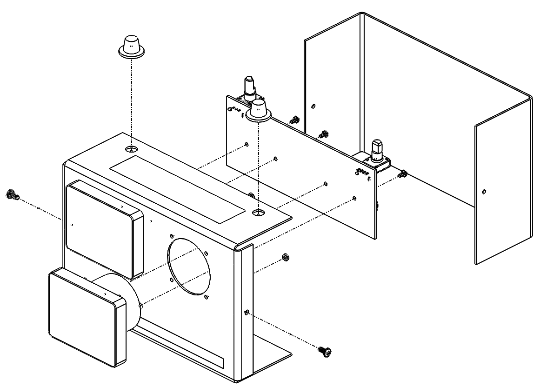
Media Campaign/Media Kit/mechanical assembly.png
