awkwardengineer/Clock/Photos/Assembly/20150909_100646.jpg

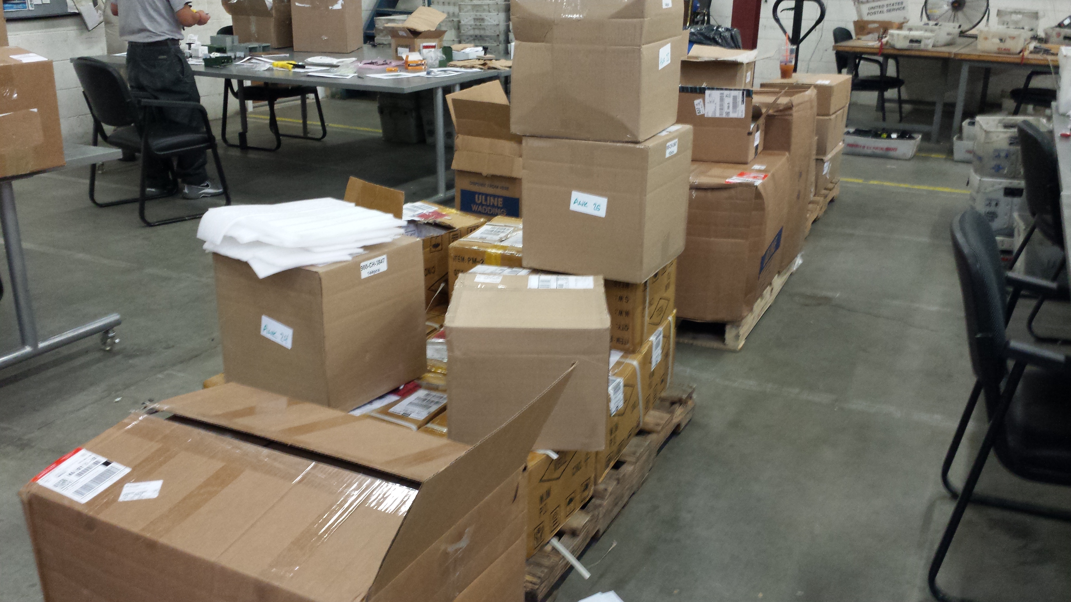
Photos/Assembly/20150909_100646.jpg
