awkwardengineer/Clock/Photos/Assembly/20150909_100700.jpg

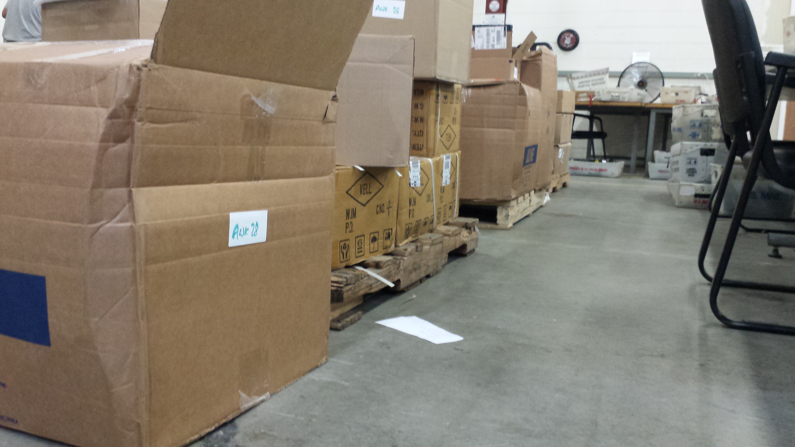
Photos/Assembly/20150909_100700.jpg
