awkwardengineer/Clock/Photos/Assembly/20150909_100712.jpg

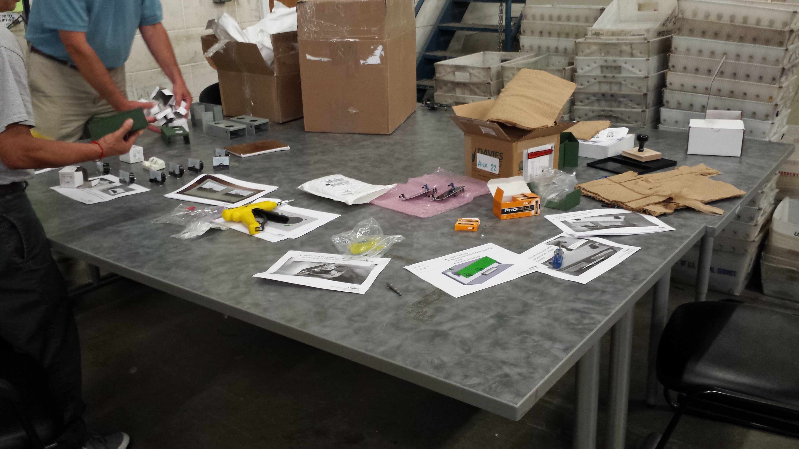
Photos/Assembly/20150909_100712.jpg
