awkwardengineer/Clock/Photos/Assembly/20150909_111654.jpg

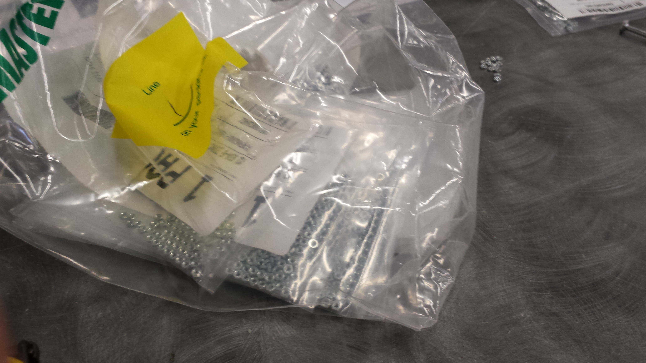
Photos/Assembly/20150909_111654.jpg
