awkwardengineer/Clock/Photos/Assembly/20150909_112817.jpg

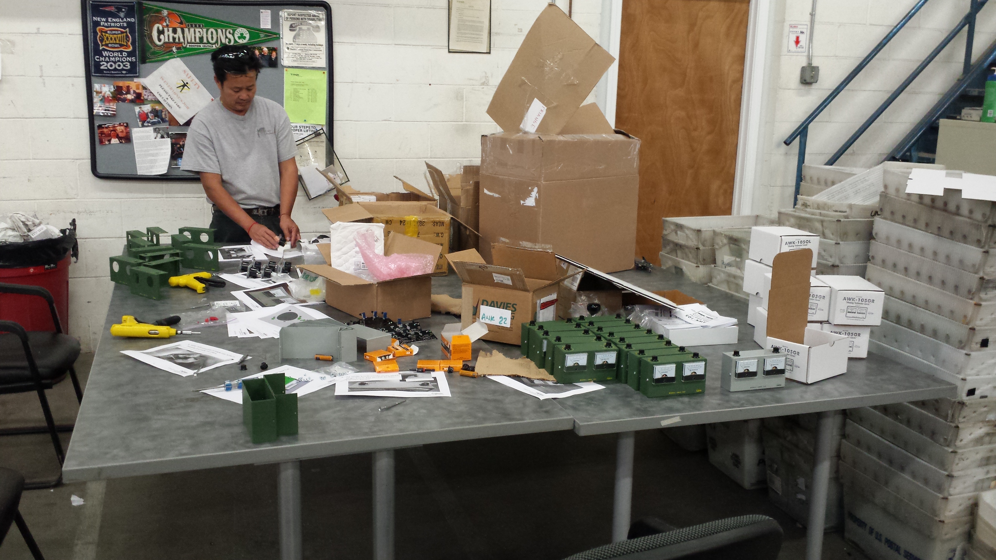
Photos/Assembly/20150909_112817.jpg
