awkwardengineer/Clock/Photos/Assembly/20150909_115054.jpg

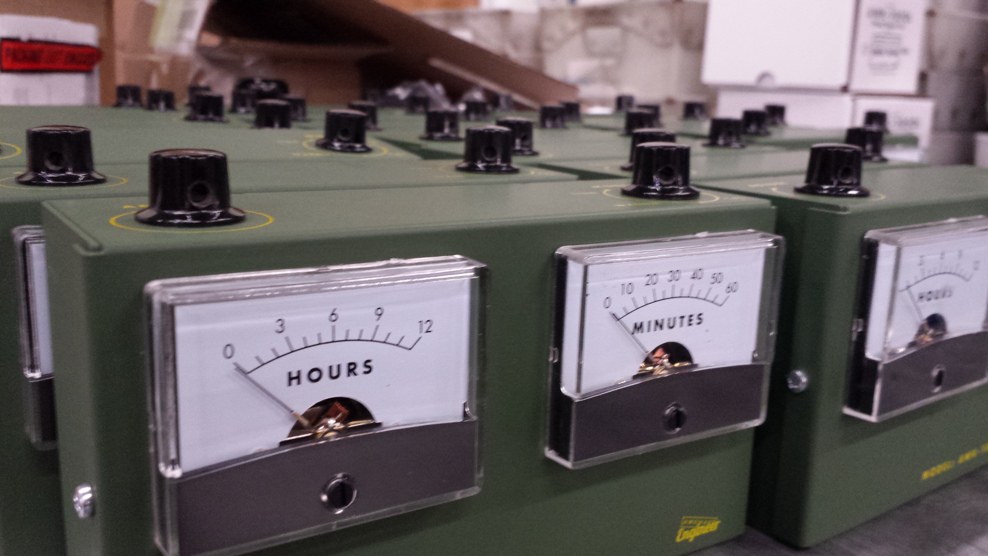
Photos/Assembly/20150909_115054.jpg
