awkwardengineer/Clock/Photos/Assembly/20150909_115239.jpg

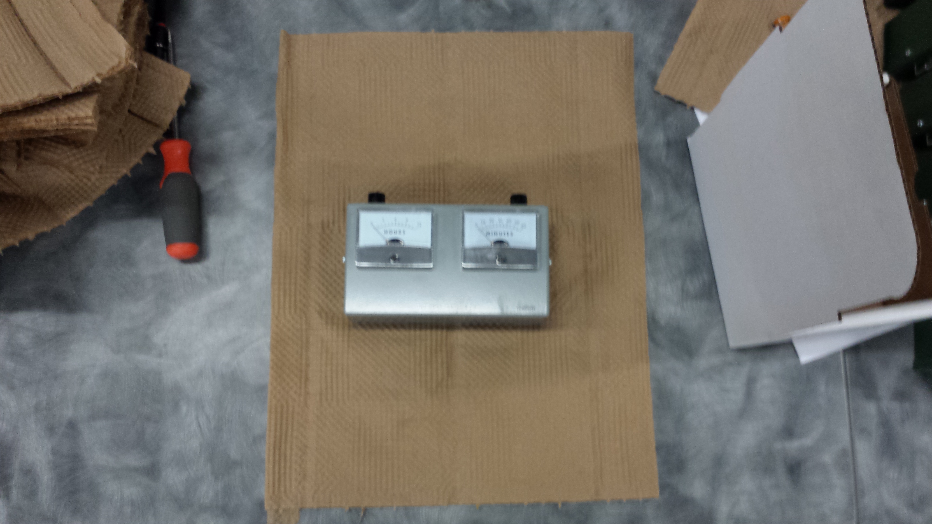
Photos/Assembly/20150909_115239.jpg
