awkwardengineer/Clock/Photos/Assembly/20150909_115340.jpg

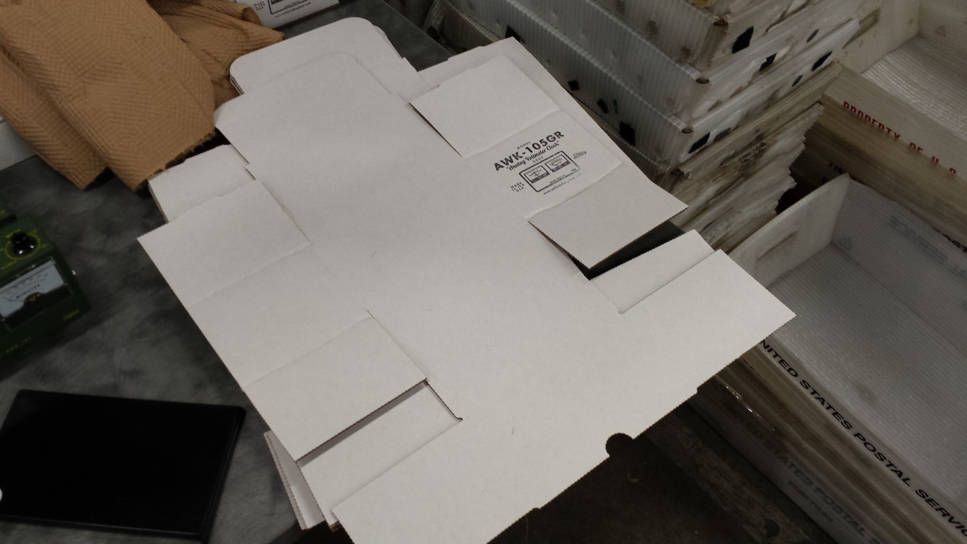
Photos/Assembly/20150909_115340.jpg
