awkwardengineer/Clock/Photos/Assembly/20150909_115432.jpg

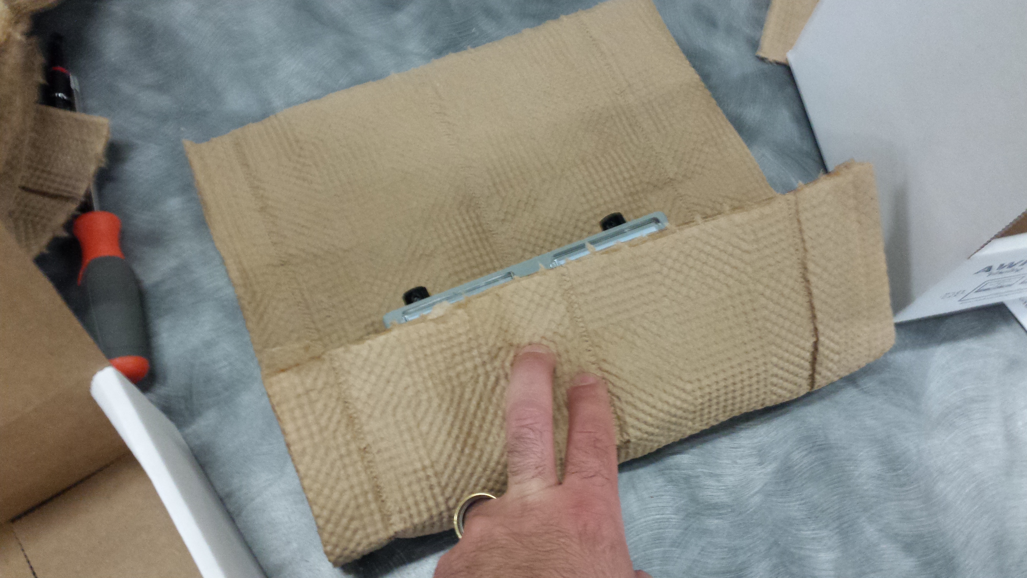
Photos/Assembly/20150909_115432.jpg
