awkwardengineer/Clock/Photos/Assembly/20150909_115500.jpg

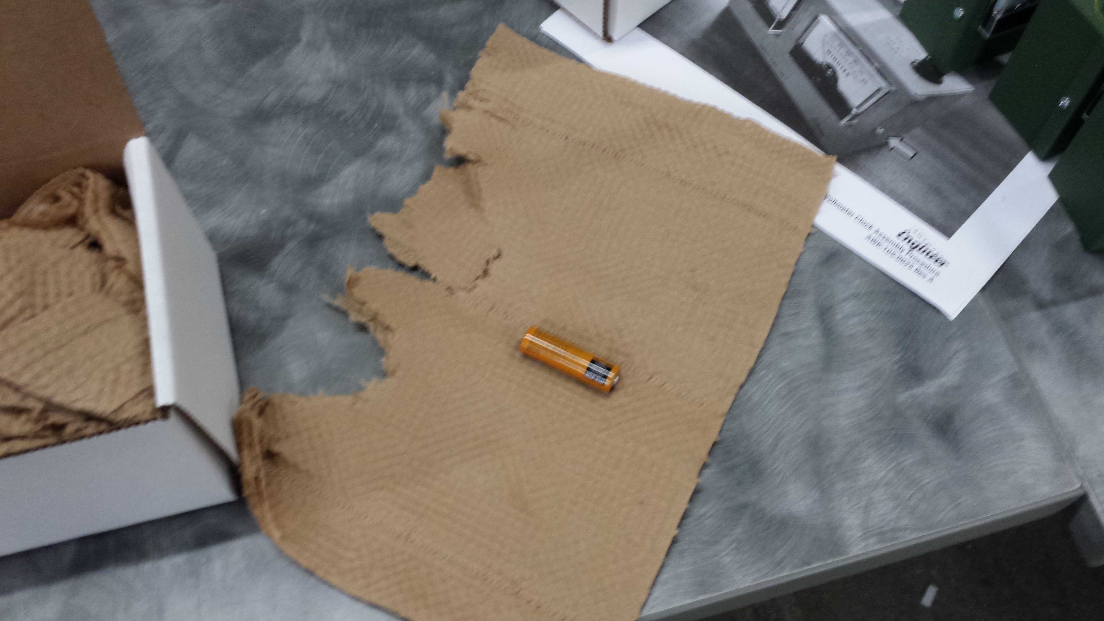
Photos/Assembly/20150909_115500.jpg
