awkwardengineer/Clock/Photos/Assembly/20150909_115527.jpg

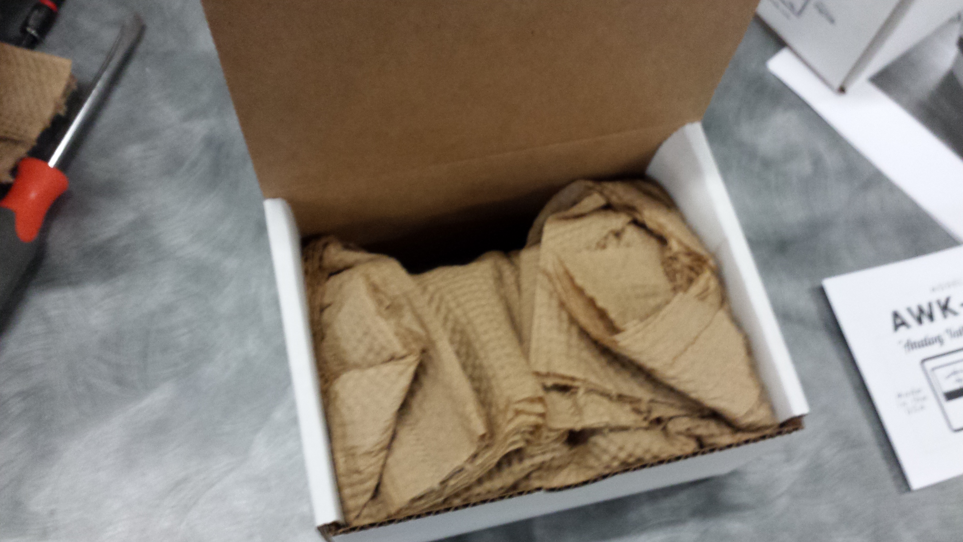
Photos/Assembly/20150909_115527.jpg
