awkwardengineer/Clock/Photos/Assembly/20150909_115532.jpg

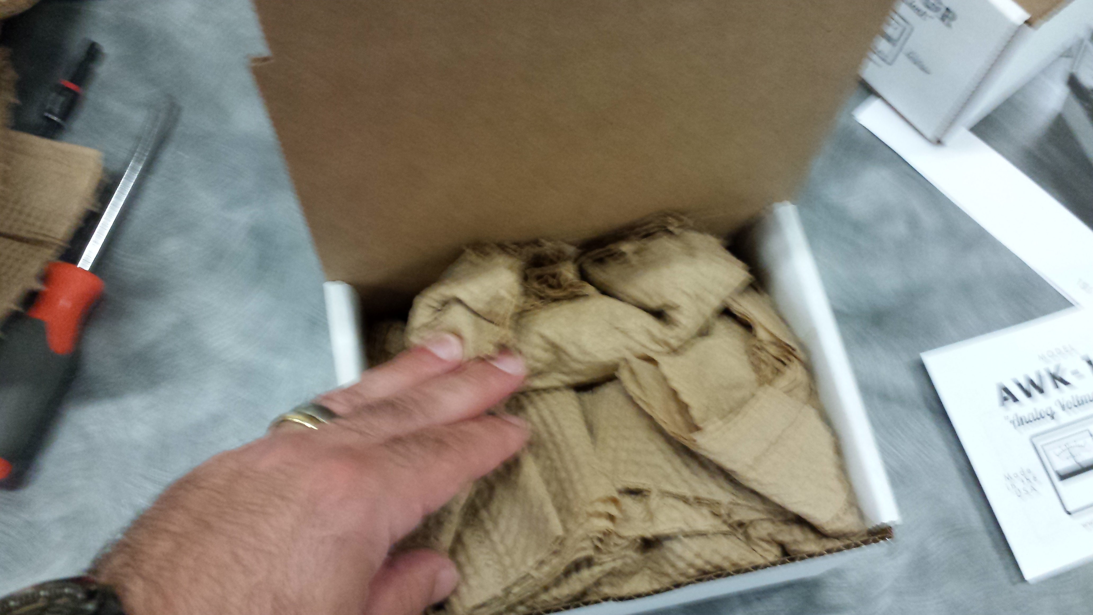
Photos/Assembly/20150909_115532.jpg
