awkwardengineer/Clock/Photos/Assembly/20150909_115544.jpg

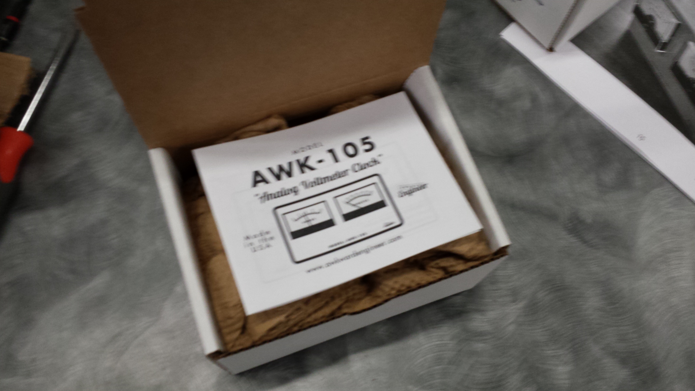
Photos/Assembly/20150909_115544.jpg
