awkwardengineer/Clock/Photos/Assembly/20150909_120141.jpg

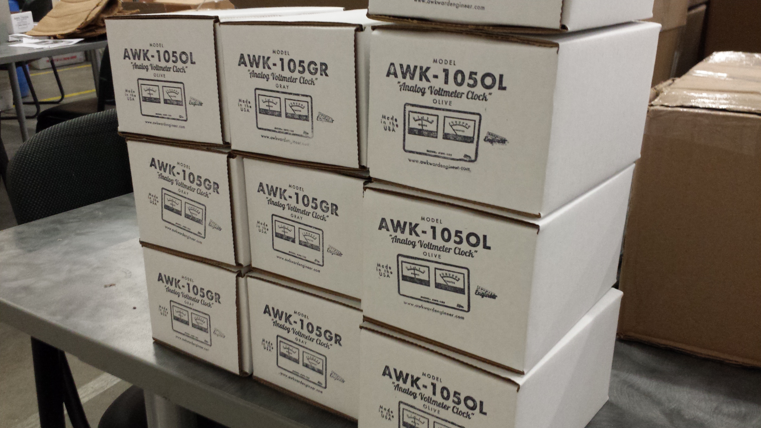
Photos/Assembly/20150909_120141.jpg
