awkwardengineer/Clock/Photos/Assembly/20150911_110341.jpg

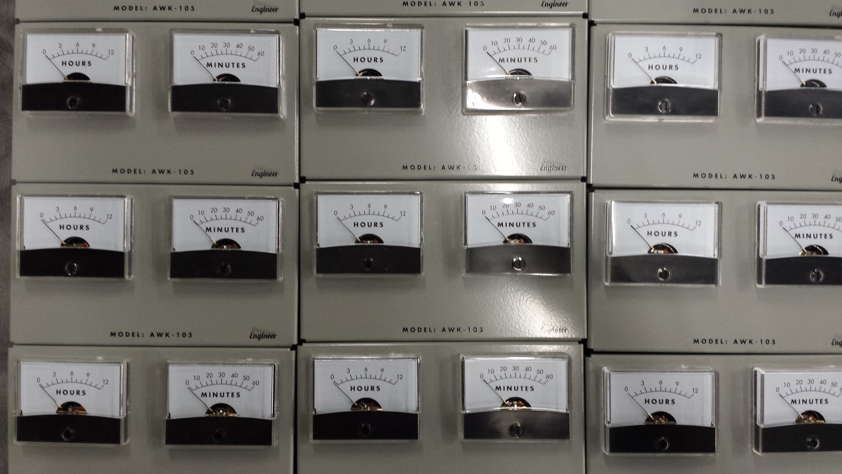
Photos/Assembly/20150911_110341.jpg
