awkwardengineer/Clock/Photos/Assembly/20150911_115920.jpg

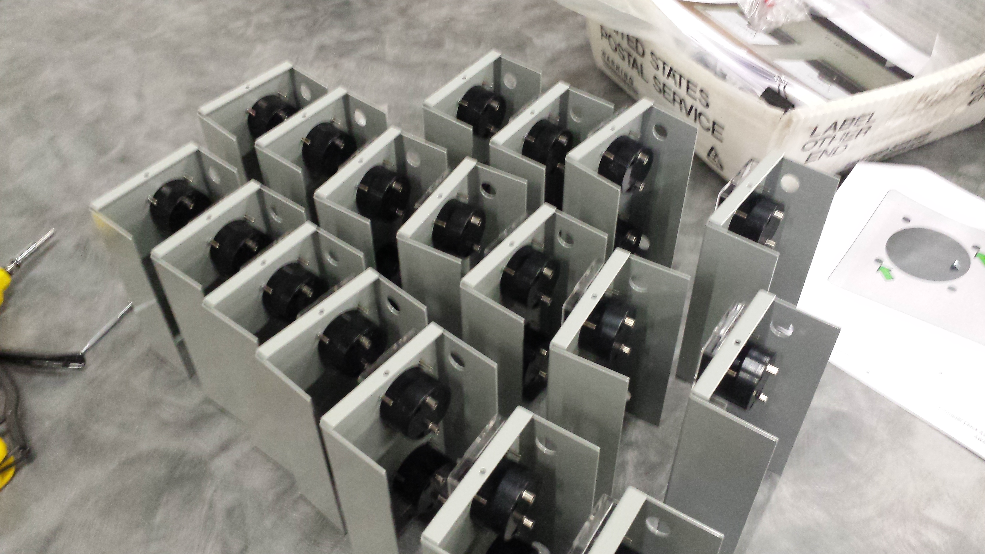
Photos/Assembly/20150911_115920.jpg
