awkwardengineer/Clock/Photos/Assembly/20150922_081130.jpg

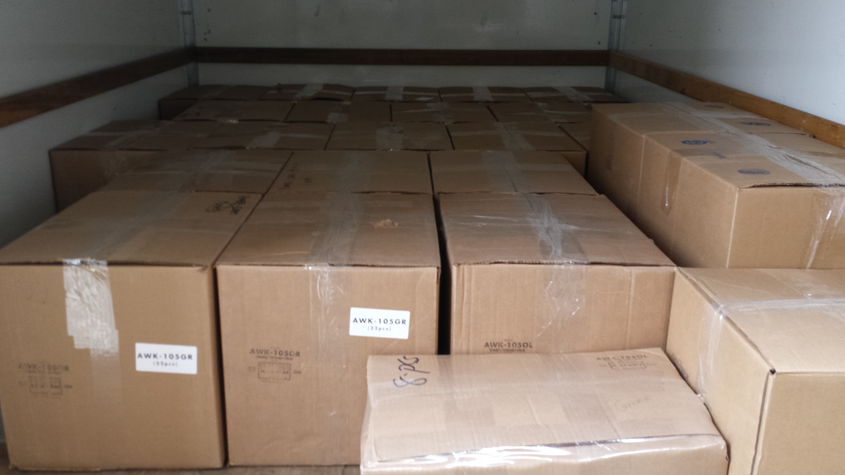
Photos/Assembly/20150922_081130.jpg
