awkwardengineer/Clock/Photos/Blog Post Material/assembly 1.jpg

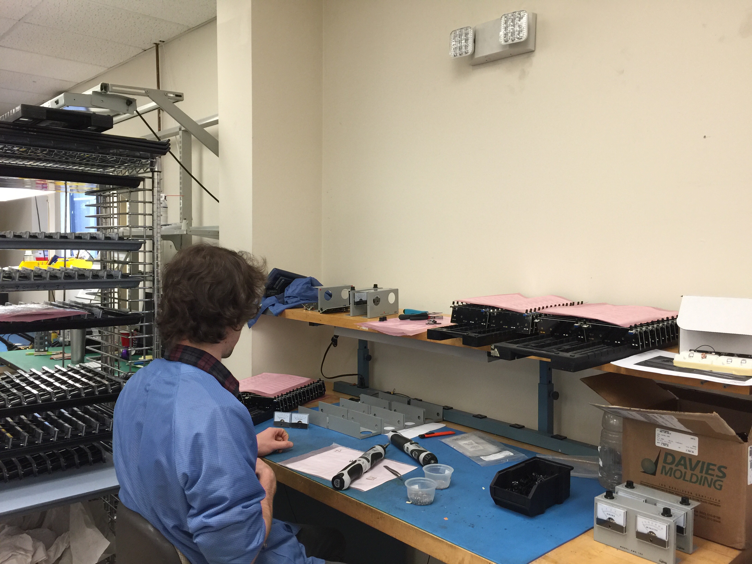
Photos/Blog Post Material/assembly 1.jpg
