awkwardengineer/Clock/Photos/Blog Post Material/assembly 2.jpg

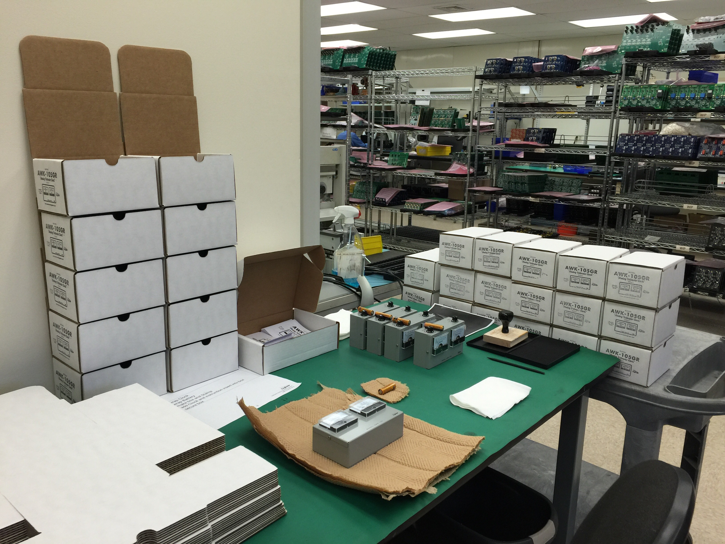
Photos/Blog Post Material/assembly 2.jpg
