awkwardengineer/Clock/Photos/Blog Post Material/assembly 3.jpg

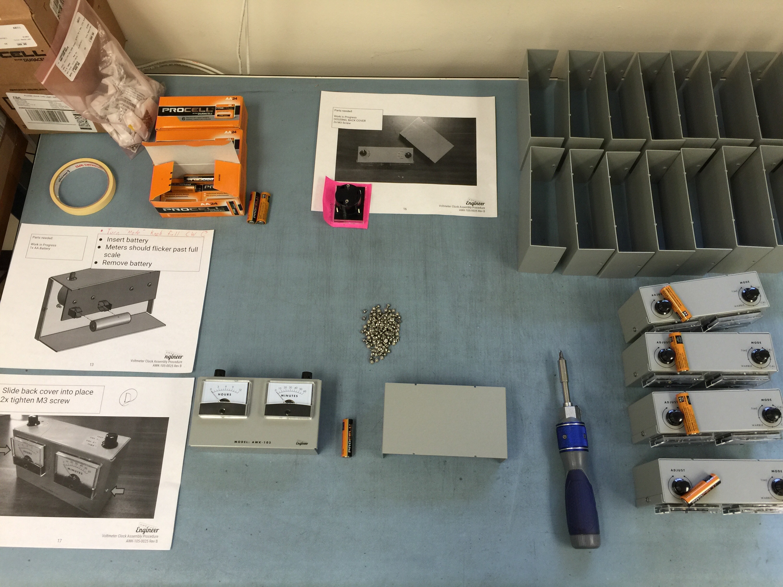
Photos/Blog Post Material/assembly 3.jpg
