awkwardengineer/Clock/Photos/Blog Post Material/soldering_iron.jpg

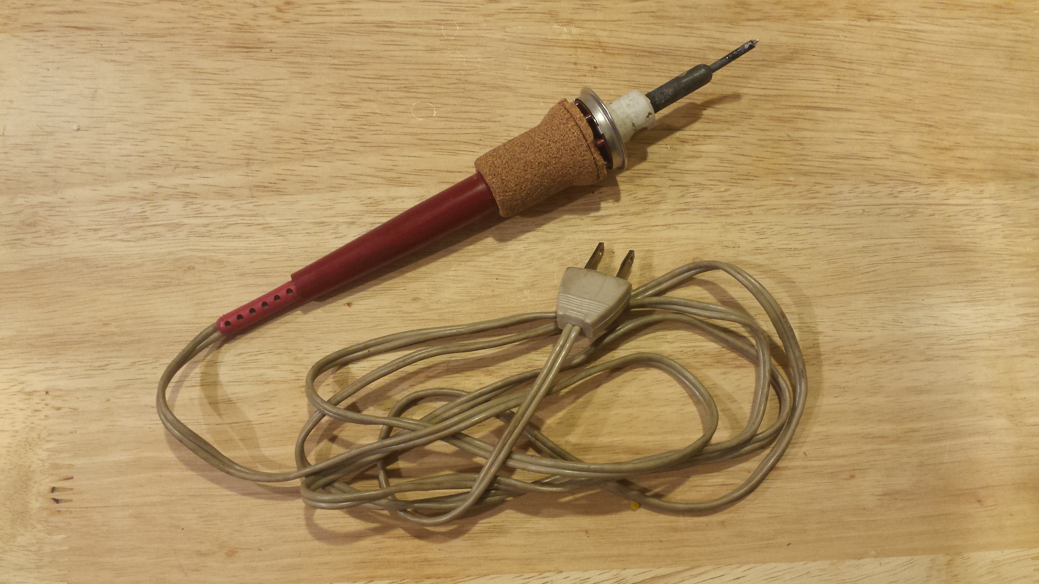
Photos/Blog Post Material/soldering_iron.jpg
