awkwardengineer/Clock/Photos/Covers/cover - assembly training.jpg

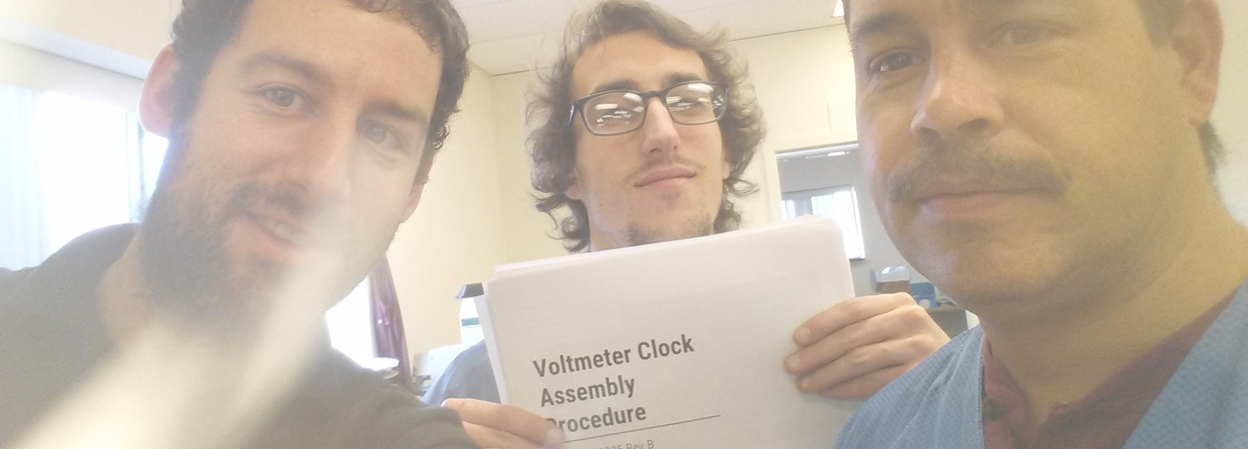
Photos/Covers/cover - assembly training.jpg
