awkwardengineer/Clock/Photos/Covers/original covers/cover - assembly 3.jpg

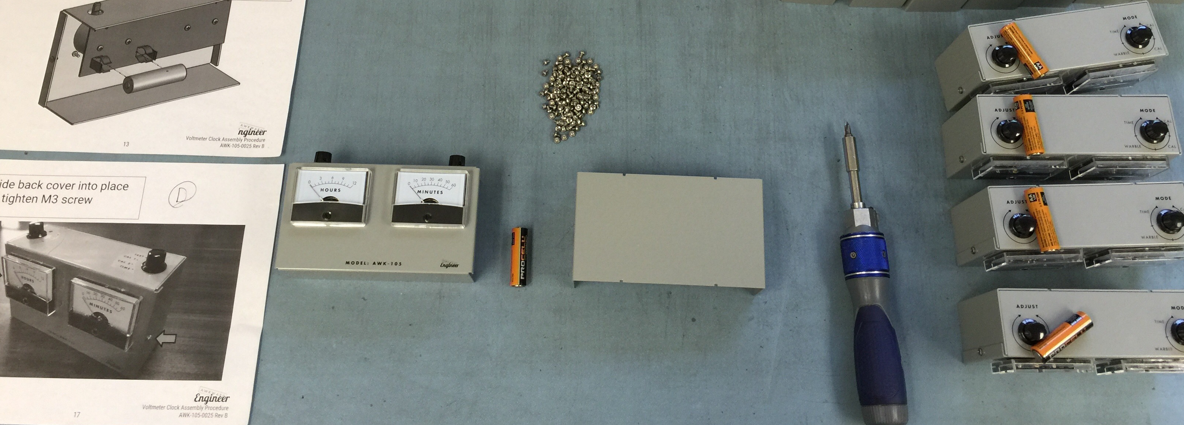
Photos/Covers/original covers/cover - assembly 3.jpg
