awkwardengineer/Clock/Photos/Covers/original covers/cover - fabrication.jpg

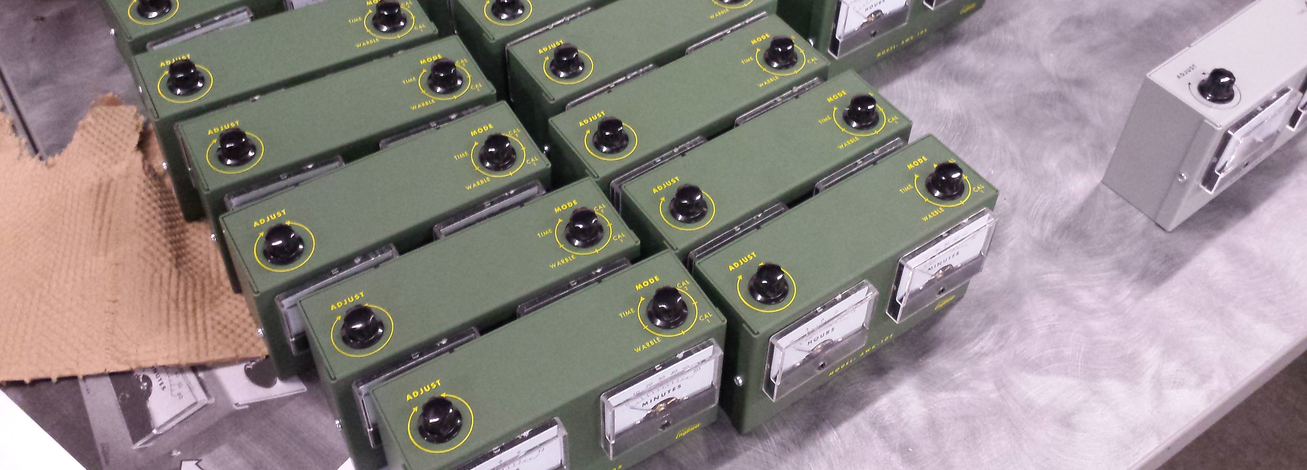
Photos/Covers/original covers/cover - fabrication.jpg
