awkwardengineer/Clock/Photos/Meter Communications/screen prints request.png

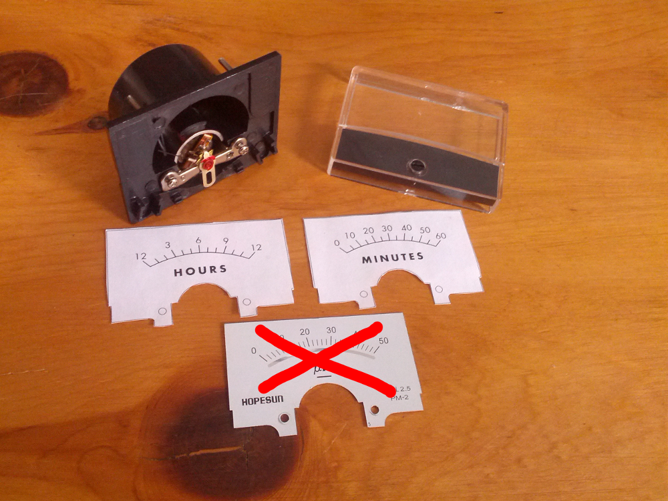
Photos/Meter Communications/screen prints request.png
