awkwardengineer/Clock/Electrical/Design Memos/footprint test/20150605_094024.jpg

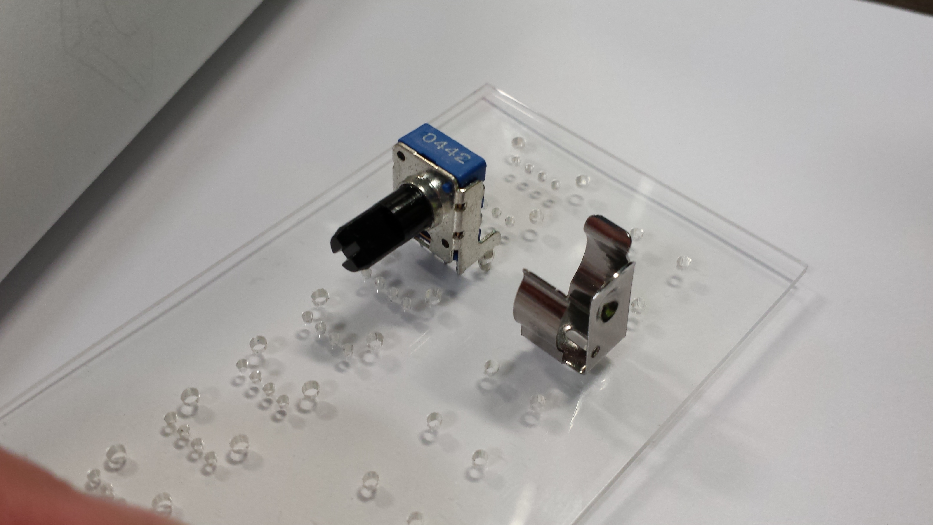
Electrical/Design Memos/footprint test/20150605_094024.jpg
