awkwardengineer/Clock/Photos/Raw/test rig.jpg

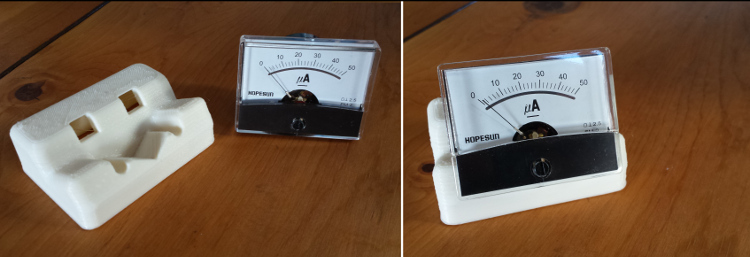
Photos/Raw/test rig.jpg
