awkwardengineer/Clock/Photos/Coating issues/20151121_203433.jpg

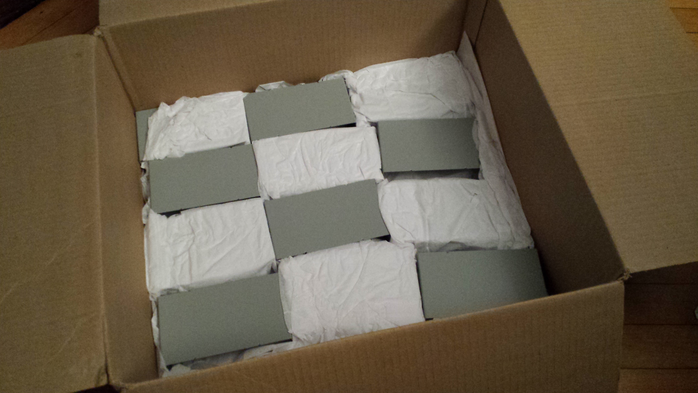
Photos/Coating issues/20151121_203433.jpg
