awkwardengineer/Clock/Photos/Coating issues/20151122_001710.jpg

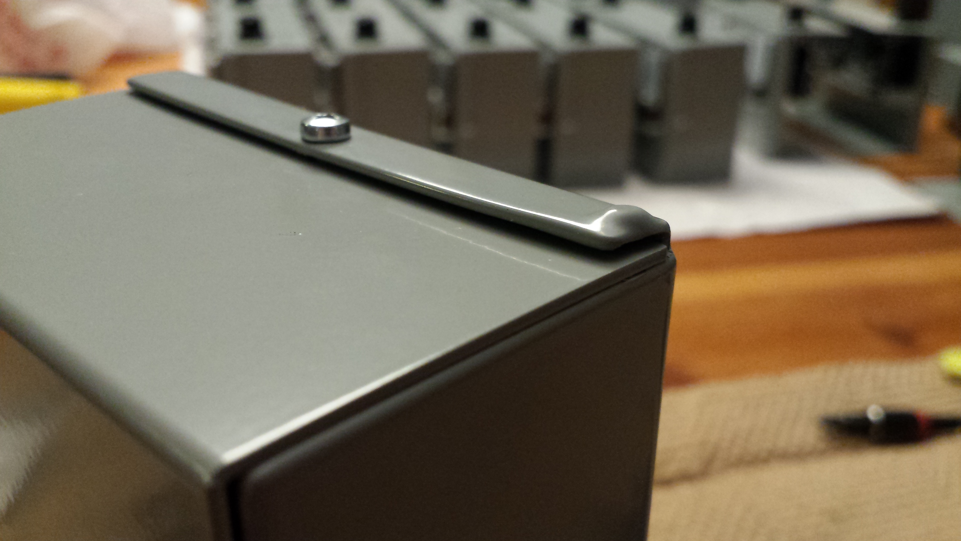
Photos/Coating issues/20151122_001710.jpg
