awkwardengineer/Clock/Photos/Coating issues/20151123_121920.jpg

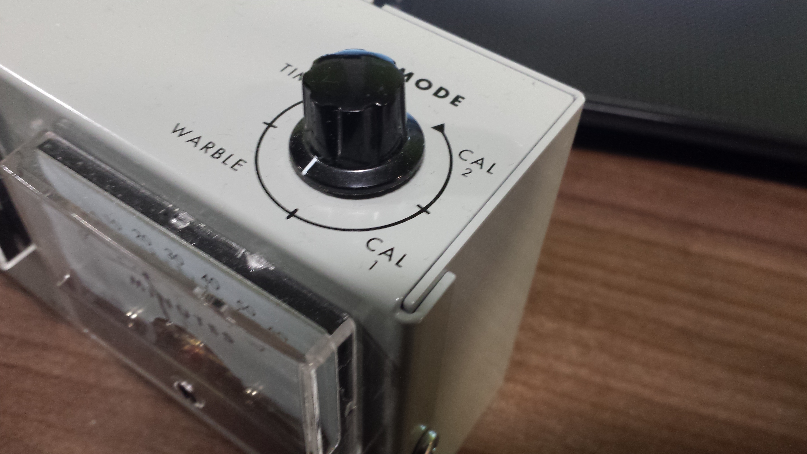
Photos/Coating issues/20151123_121920.jpg
