awkwardengineer/Clock/Photos/Coating issues/20160119_112043.jpg

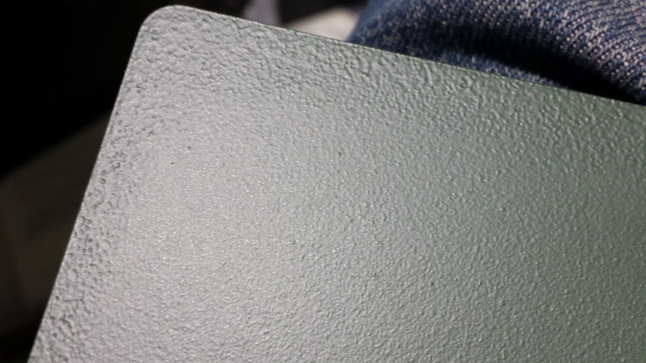
Photos/Coating issues/20160119_112043.jpg
