awkwardengineer/Clock/Photos/Coating issues/chip texture.jpg

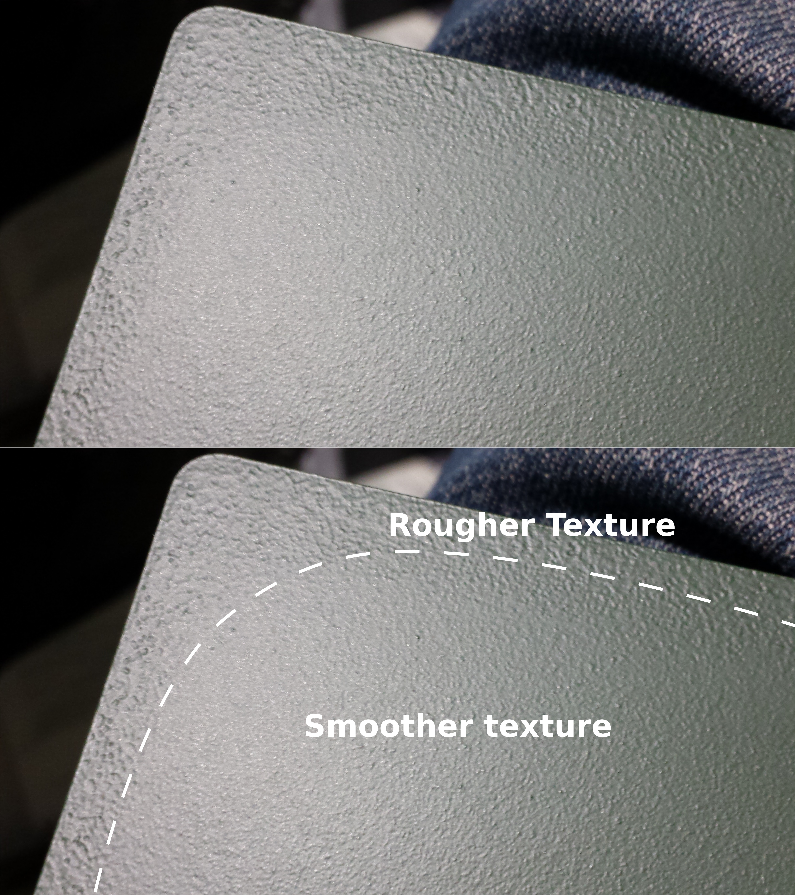
Photos/Coating issues/chip texture.jpg
