awkwardengineer/Clock/Photos/Coating issues/IMG_1810.jpg

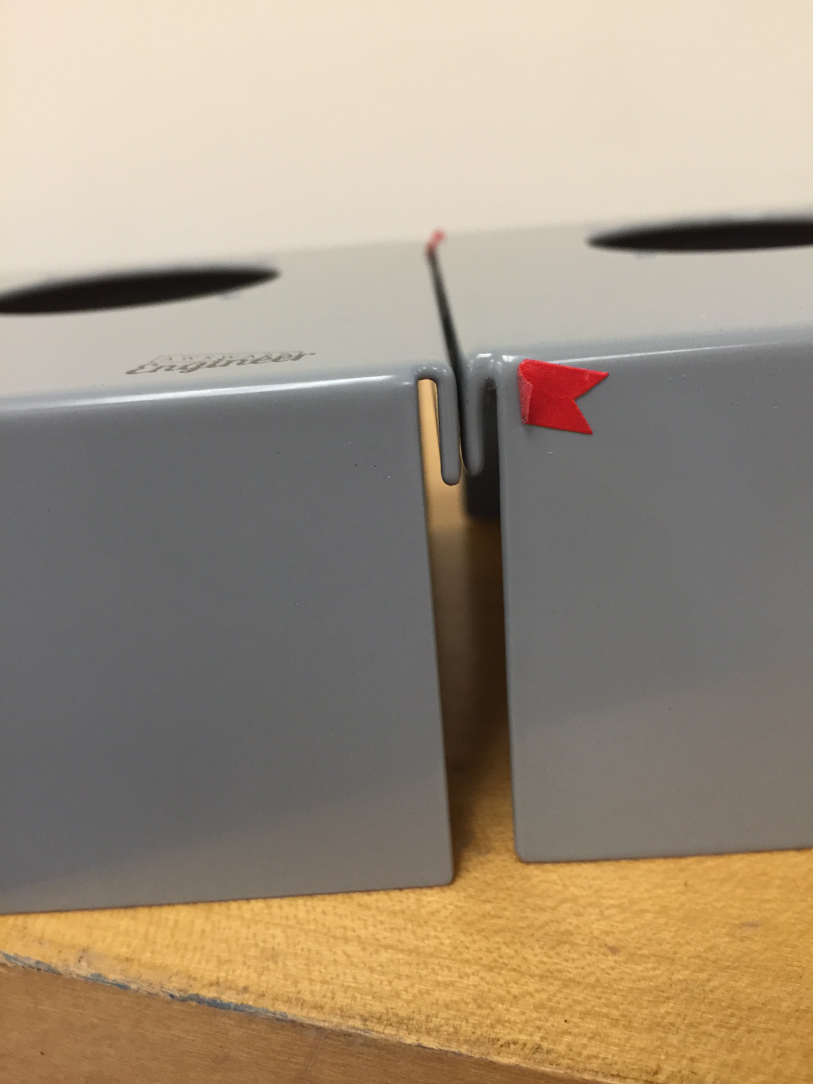
Photos/Coating issues/IMG_1810.jpg
