awkwardengineer/Clock/Photos/Coating issues/packing.png

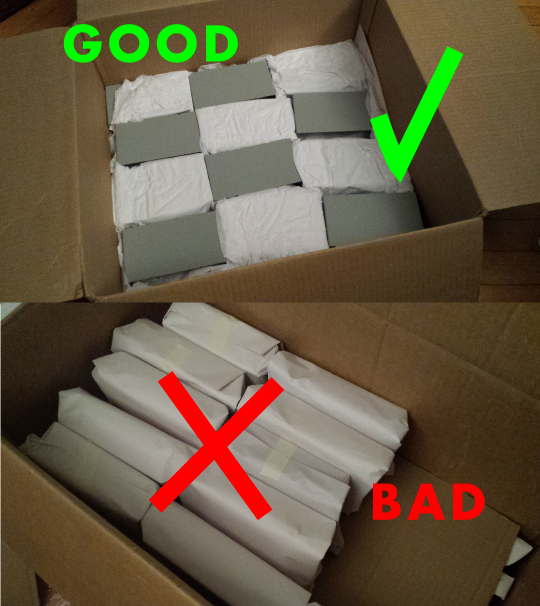
Photos/Coating issues/packing.png
