awkwardengineer/Clock/Photos/Coating issues/quality.png

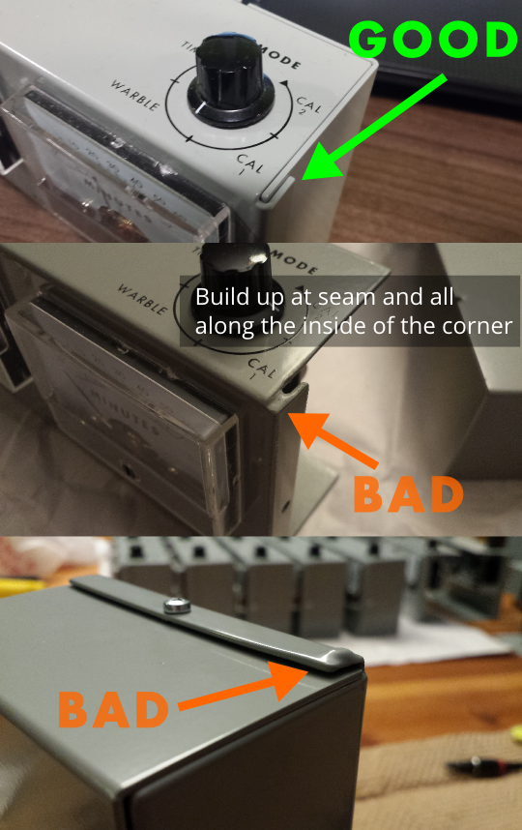
Photos/Coating issues/quality.png
