awkwardengineer/Clock/Photos/meter failure/20151003_120725.jpg

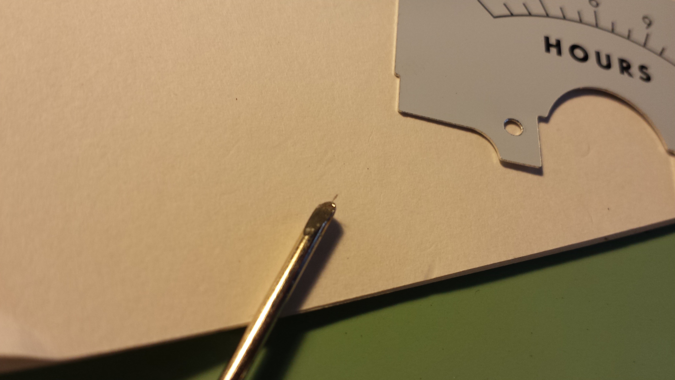
Photos/meter failure/20151003_120725.jpg
