awkwardengineer/Clock/Photos/meter failure/20151003_120737.jpg

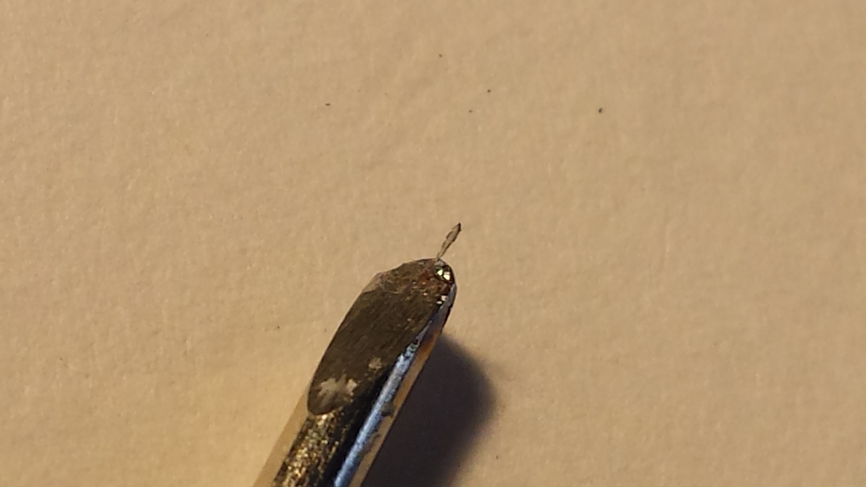
Photos/meter failure/20151003_120737.jpg
