awkwardengineer/Clock/Photos/meter failure/20151005_145625.png

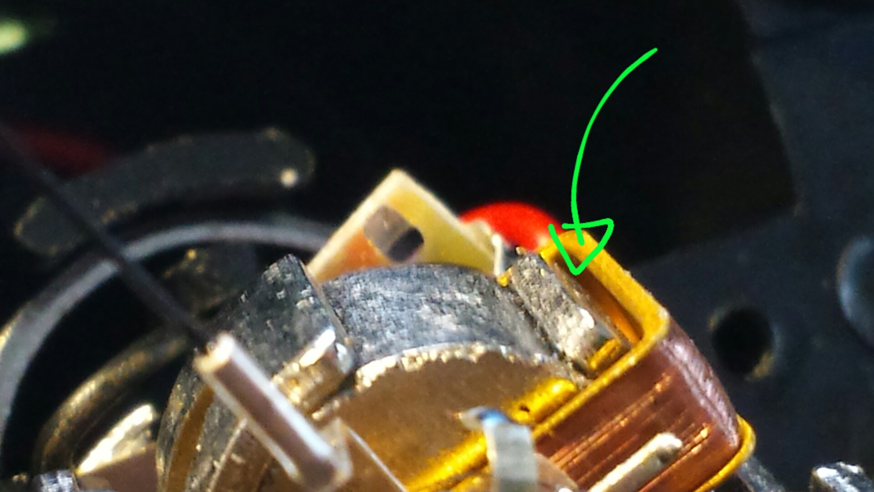
Photos/meter failure/20151005_145625.png
