awkwardengineer/Clock/Photos/USB Upgrade/LED fix.png

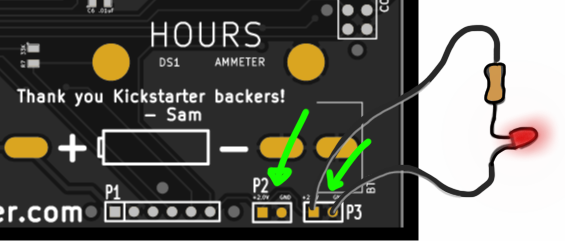
Photos/USB Upgrade/LED fix.png
