awkwardengineer/Clock/Photos/USB Upgrade/USB fix.png

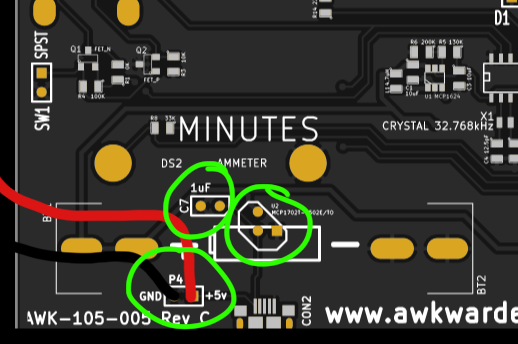
Photos/USB Upgrade/USB fix.png
