awkwardengineer/Clock/Electrical/Board Design/clock.pdf

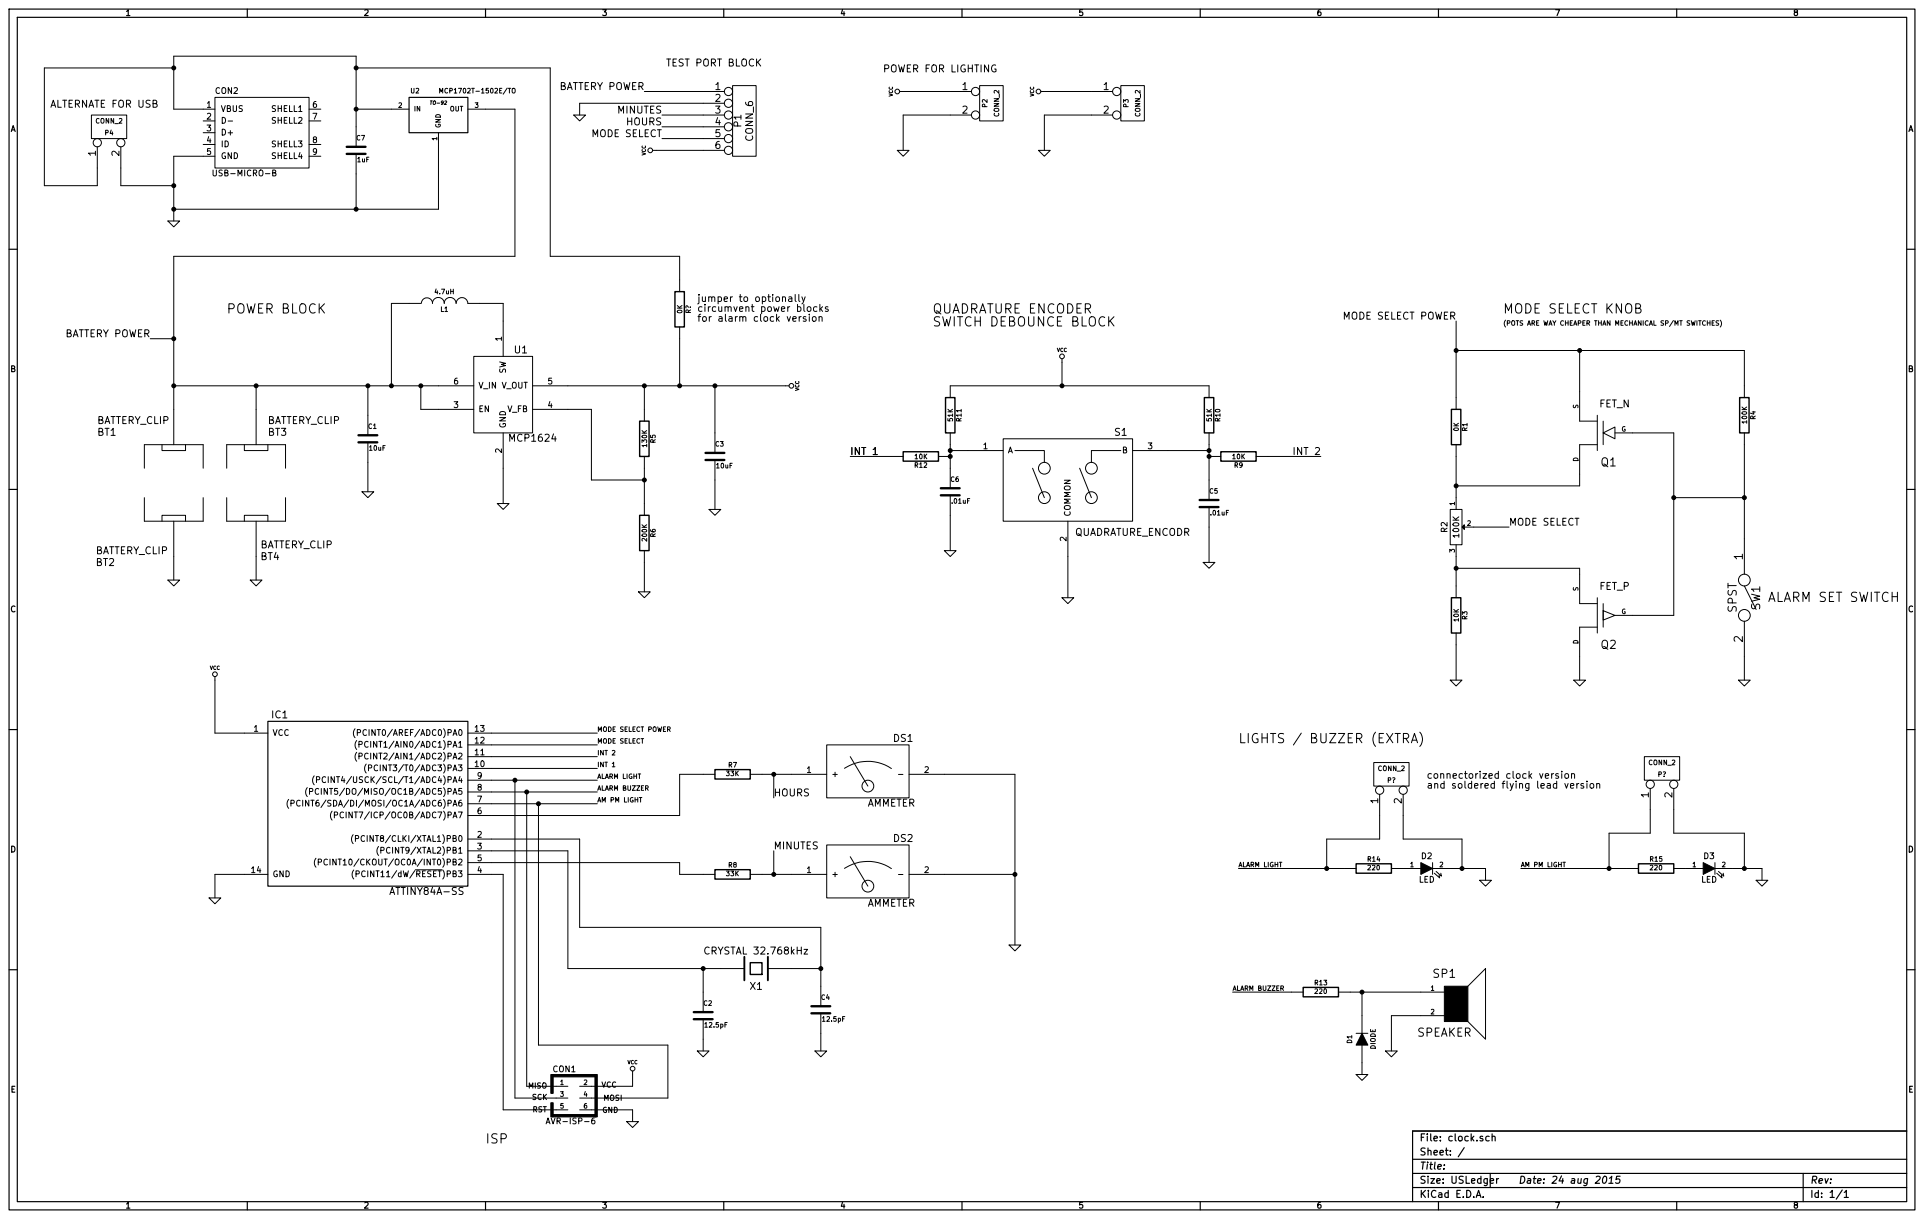
[picture p357: page 1]

INT 1 TEST PORT BLOCK

MINUTES VCC MODE SELECT

jumper to optionally
circumvent power blocks
for alarm clock version

1 2 SPST SW1 MODE SELECT POWER BLOCK 10K R3 R4 51K R11 51K R10 100K

(POTS ARE WAY CHEAPER THAN MECHANICAL SP/MT SWITCHES) R7

.01uF MODE SELECT POWER R5 130K R6 200K SW

INT 1
ALARM LIGHT ALARM BUZZER

P? CONN_2 connectorized clock version
and soldered flying lead version

Id: 1/1 Title: File: clock.sch Sheet: /
