awkwardengineer/Clock/Electrical/Reference Material/USB B micro footprint.pdf

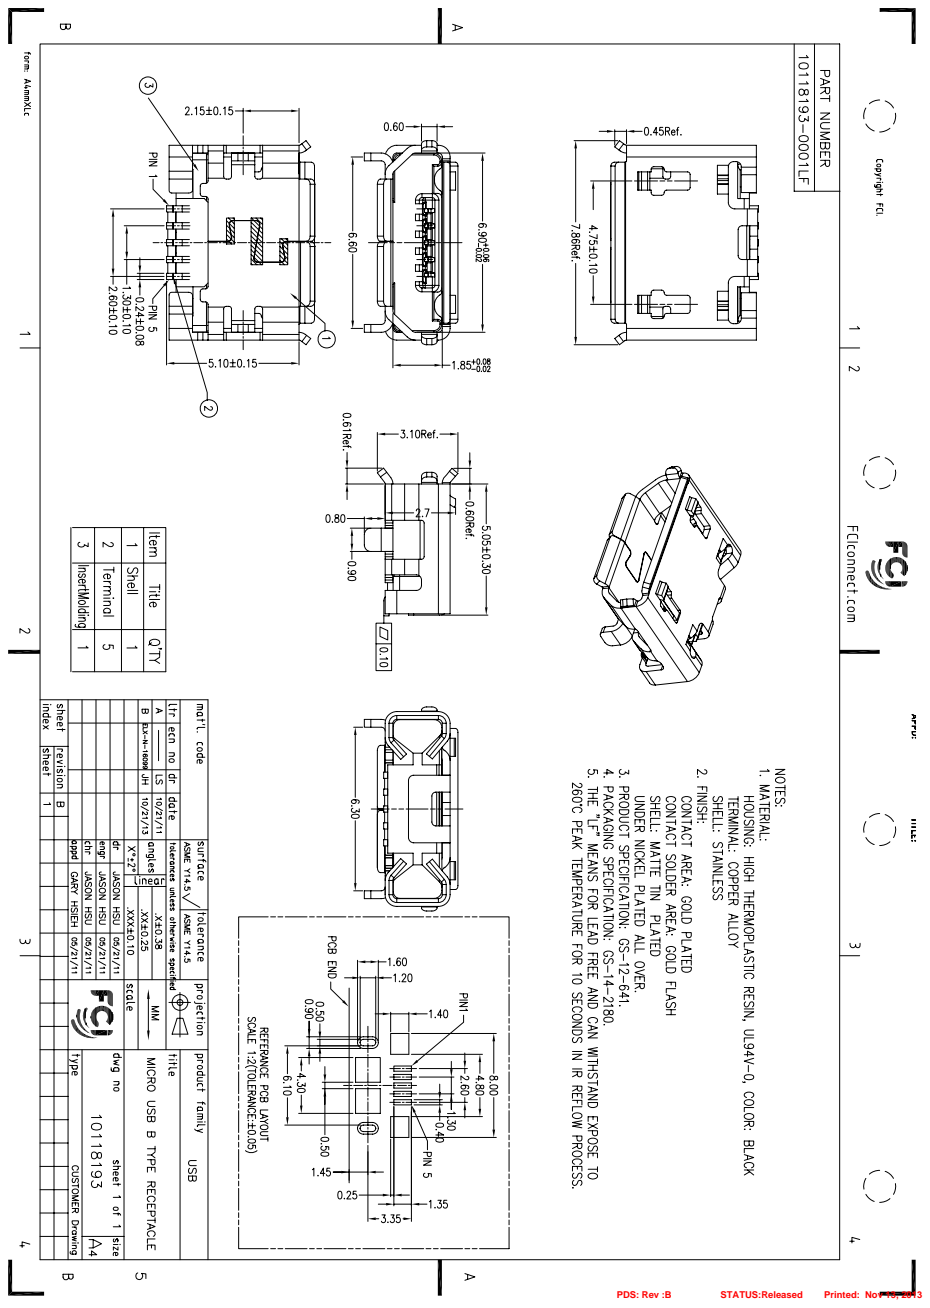
[picture p358: page 1]
PDS: Rev :B; STATUS:Released; Printed: Nov 13, 2013
