awkwardengineer/Clock/Mechanical/CAD/PDF DRAWINGS/AWK-105-0010 revJ case fabrication drawings.PDF

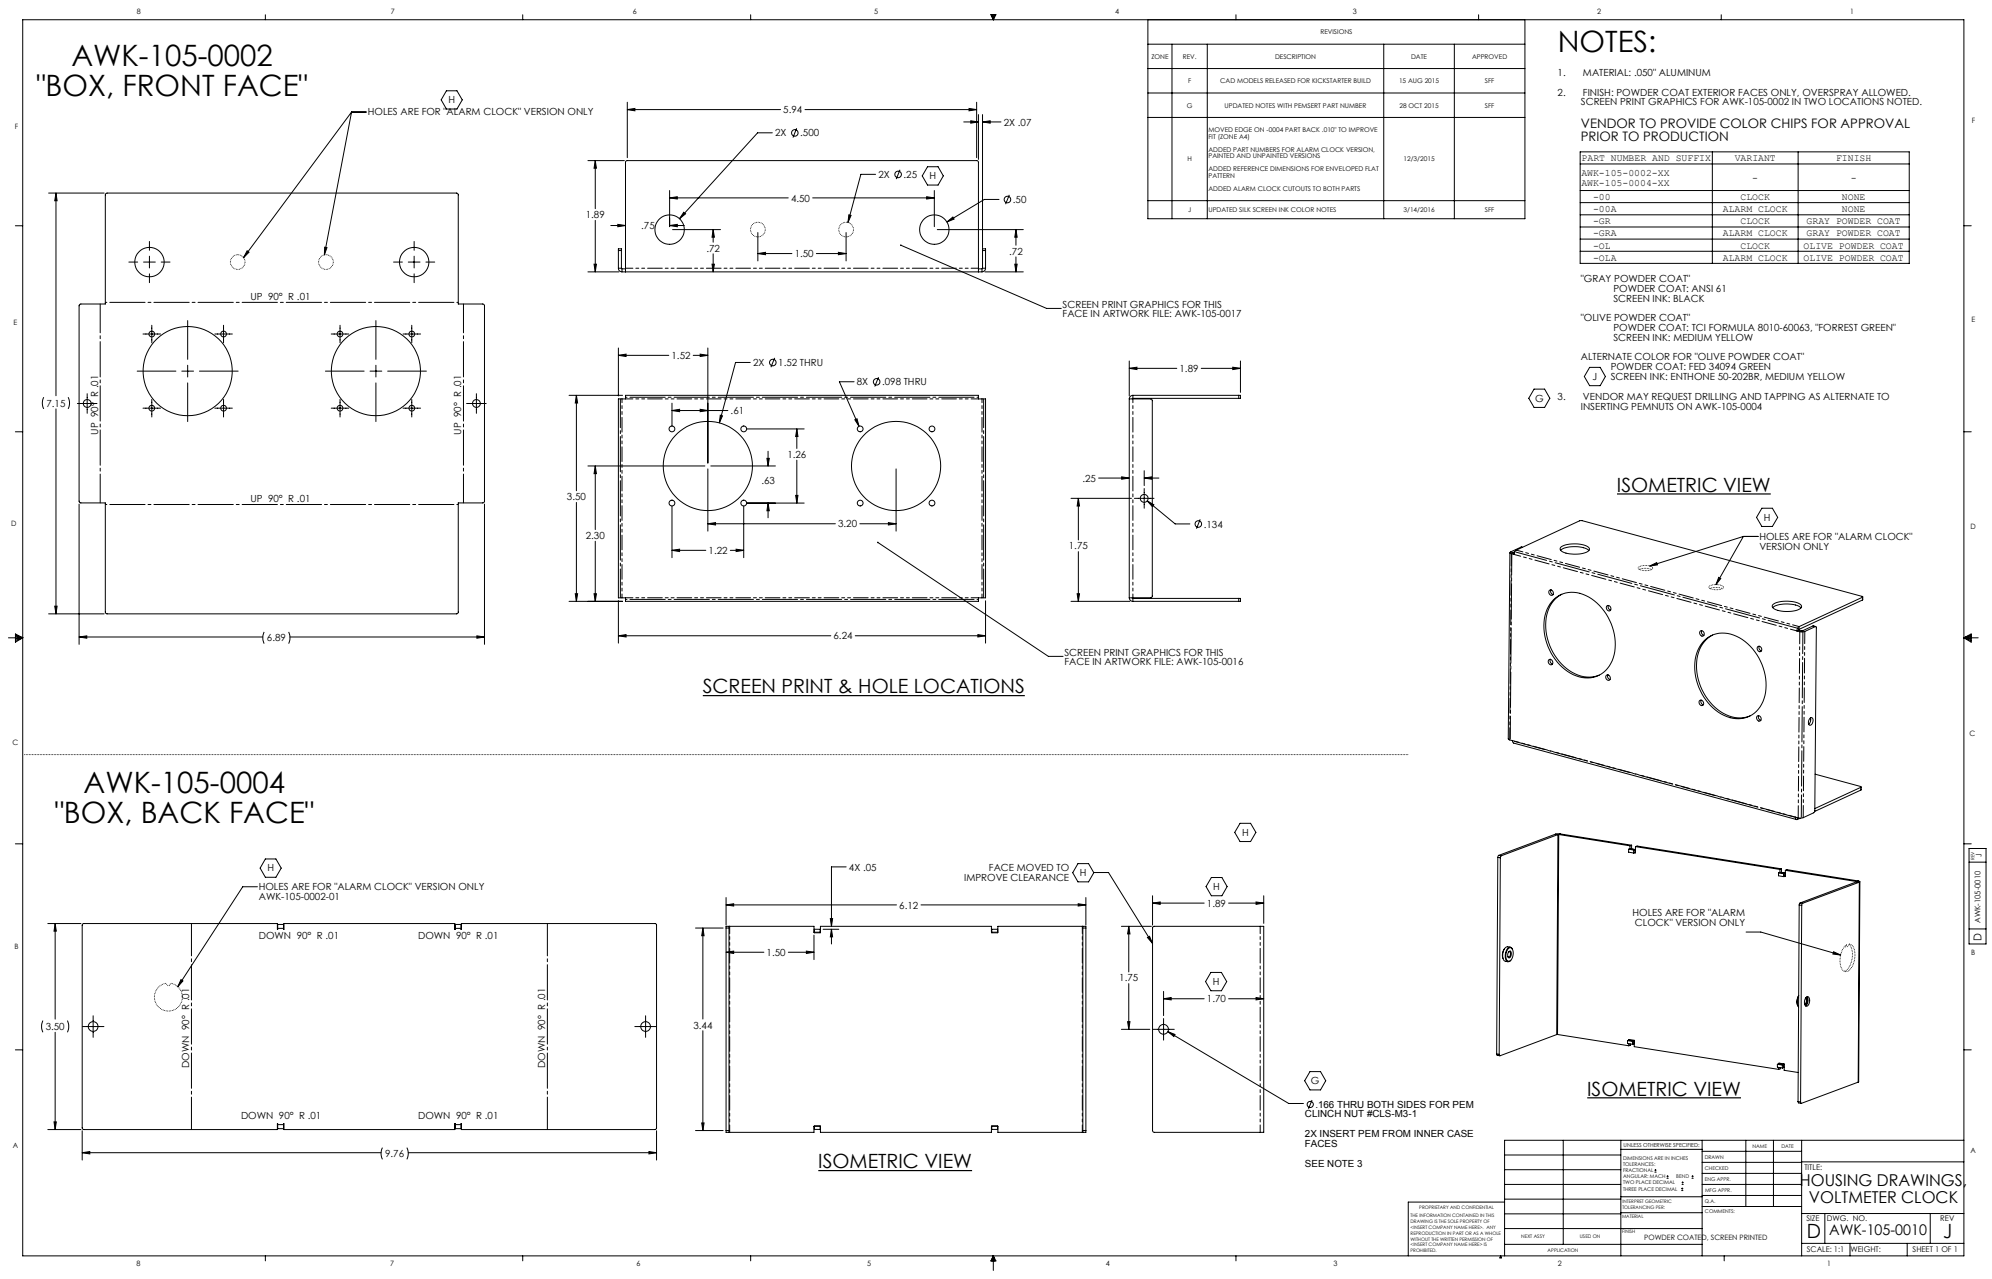
[picture p359: page 1]
ISOMETRIC VIEW; 2X 1.52 THRU; 8X .098 THRU; DOWN 90° R .01; "BOX, BACK FACE"; UPDATED SILK SCREEN INK COLOR NOTES; SFF; ALARM CLOCK; NONE; FREV AWK-105-0010; SHEET 1 OF 1; HOUSING DRAWINGS, VOLTMETER CLOCK; SCALE: 1:1 WEIGHT:; DWG. NO.; REV; MFG APPR.; ENG APPR.; ANGULAR: MACH; BEND; NEXT ASSY; USED ON

AWK-105-0002
"BOX, FRONT FACE"

ZONE | REV. | DESCRIPTION | DATE | APPROVED

1. MATERIAL: .050" ALUMINUM
2. FINISH: POWDER COAT EXTERIOR FACES ONLY, OVERSPRAY ALLOWED.
SCREEN PRINT GRAPHICS FOR AWK-105-0002 IN TWO LOCATIONS NOTED.
VENDOR TO PROVIDE COLOR CHIPS FOR APPROVAL
PRIOR TO PRODUCTION

F | CAD MODELS RELEASED FOR KICKSTARTER BUILD | 15 AUG 2015 | SFF

HOLES ARE FOR "ALARM CLOCK" VERSION ONLY

G | UPDATED NOTES WITH PEMSERT PART NUMBER | 28 OCT 2015 | SFF

H | MOVED EDGE ON -0004 PART BACK .010" TO IMPROVE FIT (ZONE A4) ADDED PART NUMBERS FOR ALARM CLOCK VERSION, PAINTED AND UNPAINTED VERSIONS ADDED REFERENCE DIMENSIONS FOR ENVELOPED FLAT PATTERN ADDED ALARM CLOCK CUTOUTS TO BOTH PARTS | 12/3/2015

PART NUMBER AND SUFFIX | VARIANT | FINISH
AWK-105-0002-XX AWK-105-0004-XX | - | -
-00 | CLOCK | NONE
-GR | CLOCK | GRAY POWDER COAT
-GRA | ALARM CLOCK | GRAY POWDER COAT
-OL | CLOCK | OLIVE POWDER COAT
-OLA | ALARM CLOCK | OLIVE POWDER COAT

"GRAY POWDER COAT"
POWDER COAT: ANSI 61
SCREEN INK: BLACK
"OLIVE POWDER COAT"
POWDER COAT: TCI FORMULA 8010-60063, "FORREST GREEN"
SCREEN INK: MEDIUM YELLOW
ALTERNATE COLOR FOR "OLIVE POWDER COAT"
POWDER COAT: FED 34094 GREEN
SCREEN INK: ENTHONE 50-202BR, MEDIUM YELLOW

SCREEN PRINT GRAPHICS FOR THIS
FACE IN ARTWORK FILE: AWK-105-0017

3. VENDOR MAY REQUEST DRILLING AND TAPPING AS ALTERNATE TO

INSERTING PEMNUTS ON AWK-105-0004

HOLES ARE FOR "ALARM CLOCK"
VERSION ONLY

FACE IN ARTWORK FILE: AWK-105-0016

SCREEN PRINT & HOLE LOCATIONS

AWK-105-0002-01

FACE MOVED TO
IMPROVE CLEARANCE

HOLES ARE FOR "ALARM
CLOCK" VERSION ONLY

.166 THRU BOTH SIDES FOR PEM
CLINCH NUT #CLS-M3-1
2X INSERT PEM FROM INNER CASE
FACES
SEE NOTE 3

UNLESS OTHERWISE SPECIFIED:

DIMENSIONS ARE IN INCHES
TOLERANCES:
FRACTIONAL
TWO PLACE DECIMAL
THREE PLACE DECIMAL

PROPRIETARY AND CONFIDENTIAL
THE INFORMATION CONTAINED IN THIS
DRAWING IS THE SOLE PROPERTY OF
<INSERT COMPANY NAME HERE>. ANY
REPRODUCTION IN PART OR AS A WHOLE
WITHOUT THE WRITTEN PERMISSION OF
<INSERT COMPANY NAME HERE> IS
PROHIBITED.

INTERPRET GEOMETRIC
TOLERANCING PER:
MATERIAL
POWDER COATED, SCREEN PRINTED FINISH
