awkwardengineer/Clock/Mechanical/Quotes/Full Turnkey Assembly/AWK-105-0010 revF case fabrication drawings.PDF

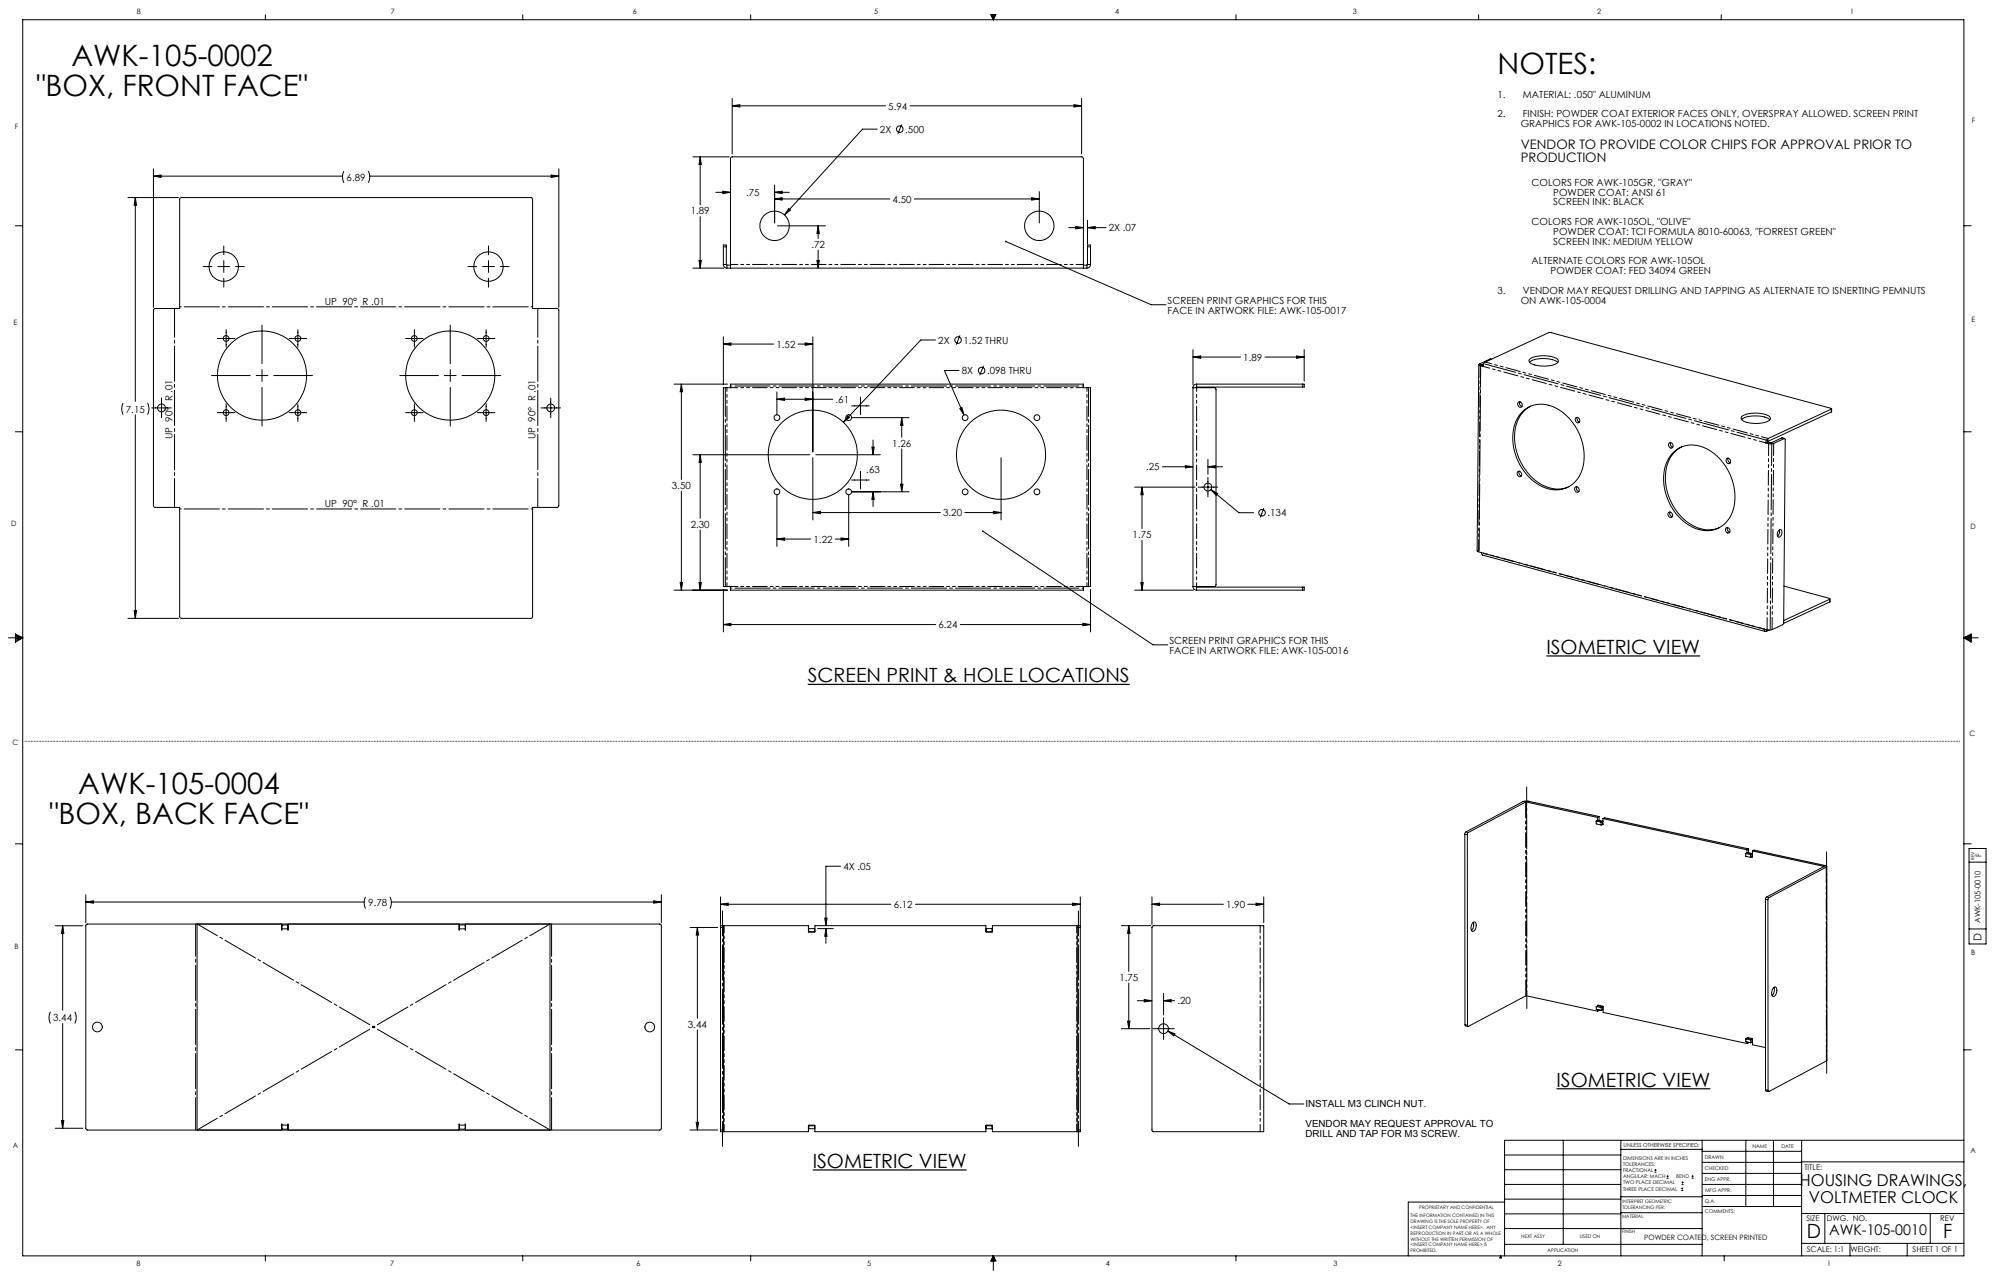
[picture p360: page 1]
ISOMETRIC VIEW; 2X 1.52 THRU; 8X .098 THRU; "BOX, BACK FACE"; "BOX, FRONT FACE"; NOTES:; FREV AWK-105-0010; SHEET 1 OF 1; HOUSING DRAWINGS, VOLTMETER CLOCK; SCALE: 1:1 WEIGHT:; DWG. NO.; REV; MFG APPR.; ENG APPR.; ANGULAR: MACH; BEND; NEXT ASSY; USED ON

1. MATERIAL: .050" ALUMINUM
2. FINISH: POWDER COAT EXTERIOR FACES ONLY, OVERSPRAY ALLOWED. SCREEN PRINT
GRAPHICS FOR AWK-105-0002 IN LOCATIONS NOTED.
VENDOR TO PROVIDE COLOR CHIPS FOR APPROVAL PRIOR TO
PRODUCTION

COLORS FOR AWK-105GR, "GRAY"
POWDER COAT: ANSI 61
SCREEN INK: BLACK
COLORS FOR AWK-105OL, "OLIVE"
POWDER COAT: TCI FORMULA 8010-60063, "FORREST GREEN"
SCREEN INK: MEDIUM YELLOW
ALTERNATE COLORS FOR AWK-105OL
POWDER COAT: FED 34094 GREEN

3. VENDOR MAY REQUEST DRILLING AND TAPPING AS ALTERNATE TO ISNERTING PEMNUTS
ON AWK-105-0004

SCREEN PRINT GRAPHICS FOR THIS
FACE IN ARTWORK FILE: AWK-105-0017

FACE IN ARTWORK FILE: AWK-105-0016

SCREEN PRINT & HOLE LOCATIONS

INSTALL M3 CLINCH NUT.
VENDOR MAY REQUEST APPROVAL TO
DRILL AND TAP FOR M3 SCREW.

UNLESS OTHERWISE SPECIFIED:

DIMENSIONS ARE IN INCHES
TOLERANCES:
FRACTIONAL
TWO PLACE DECIMAL
THREE PLACE DECIMAL

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

INTERPRET GEOMETRIC
TOLERANCING PER:
MATERIAL
POWDER COATED, SCREEN PRINTED FINISH
