awkwardengineer/Clock/Mechanical/Quotes/Case/Rev D Case Quote Package/AWK-105-0010 revD.pdf

# AWK-105-0002

"BOX, FRONT FACE" | NOTES:

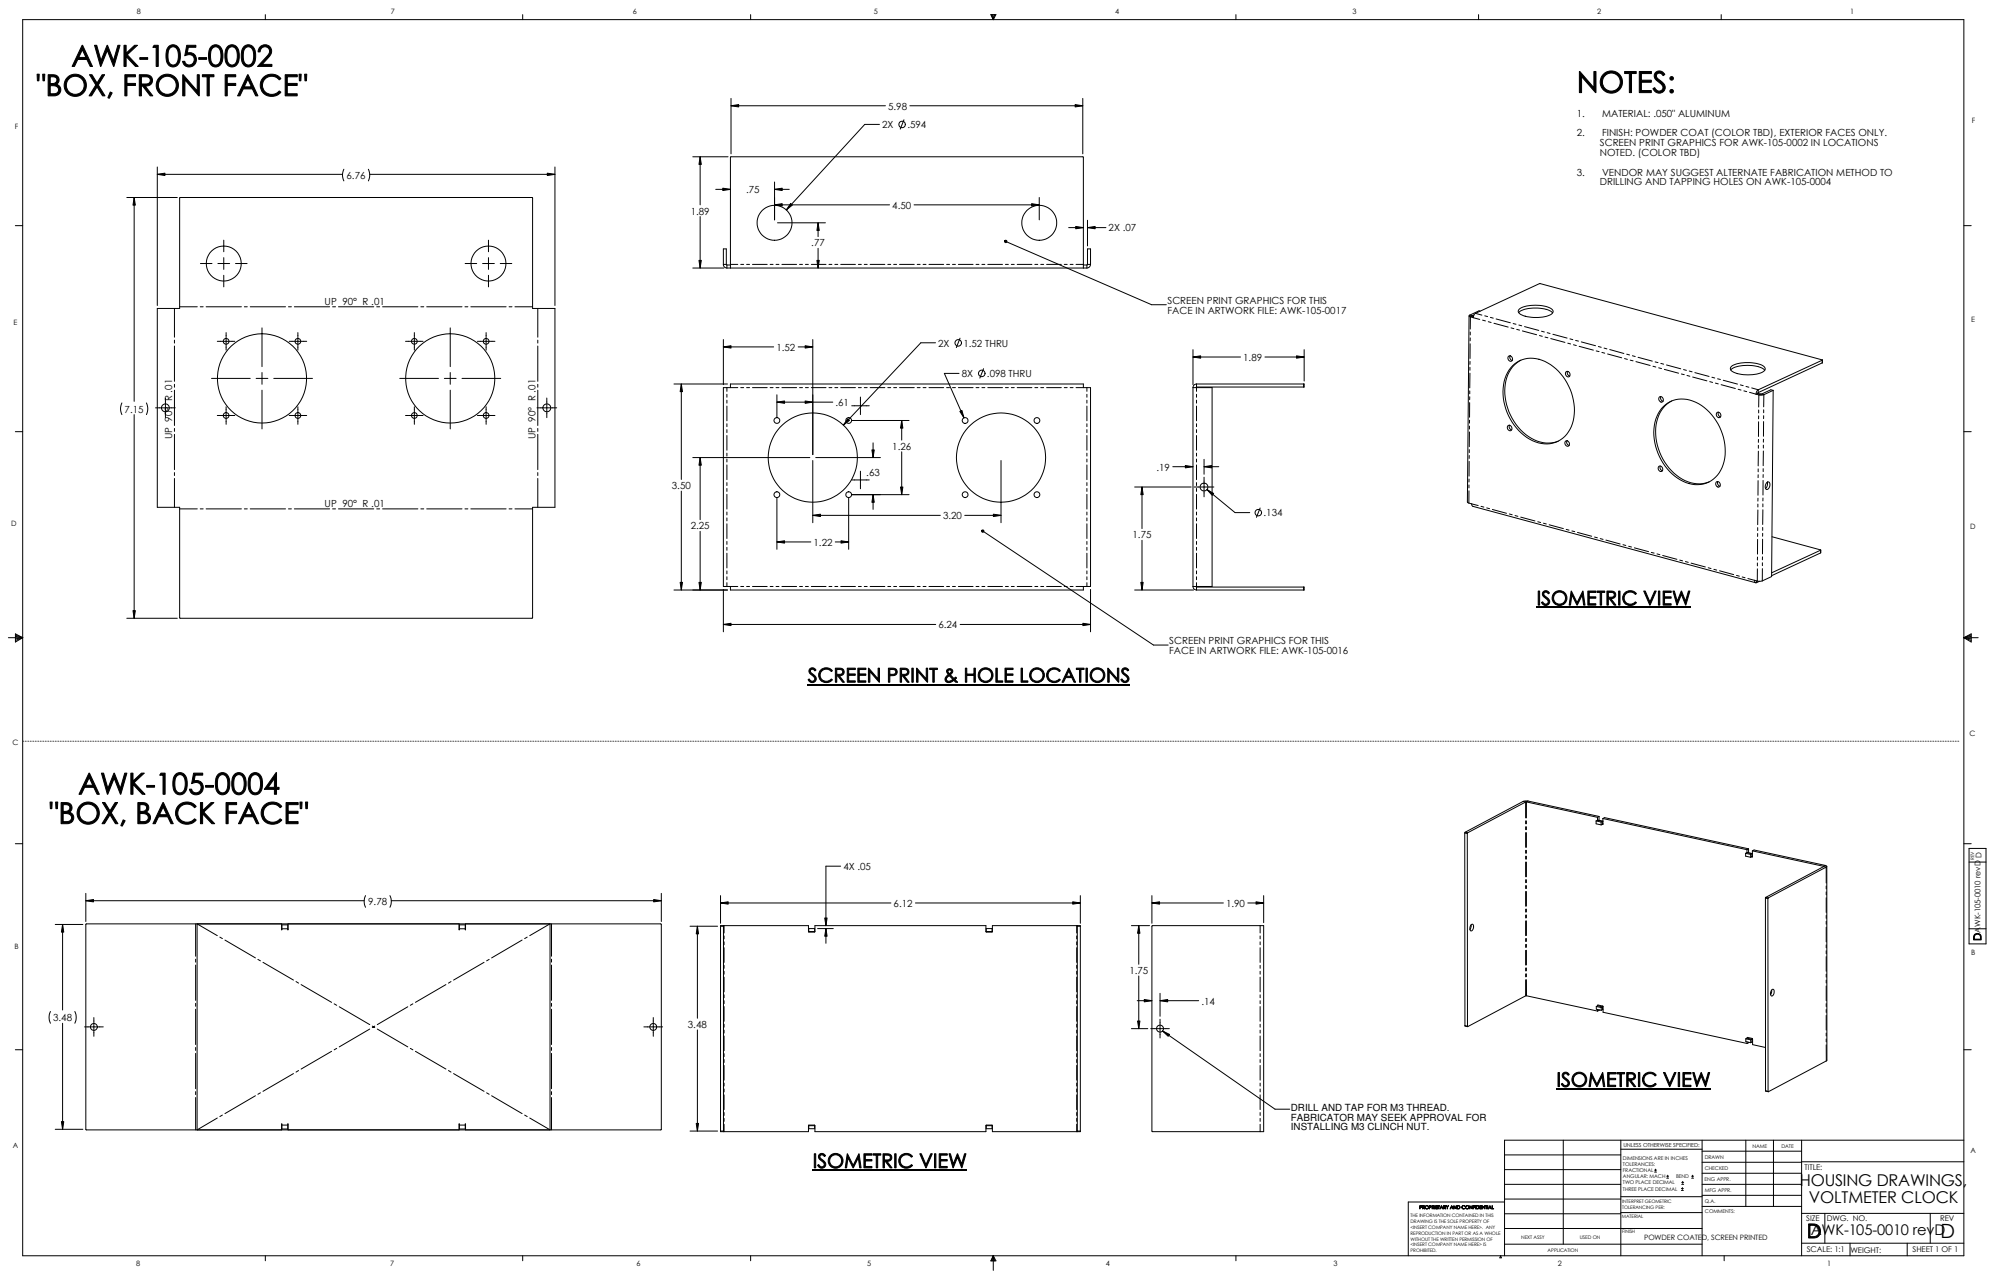
[picture p361: page 1]
AWK-105-0004 "BOX, BACK FACE"; 1. MATERIAL: .050" ALUMINUM; COMMENTS:; AWK-105-0010 revD; REV; HOUSING DRAWINGS,; ISOMETRIC VIEW; 1.52 THRU; .098 THRU

2. FINISH: POWDER COAT (COLOR TBD), EXTERIOR FACES ONLY.
SCREEN PRINT GRAPHICS FOR AWK-105-0002 IN LOCATIONS
NOTED. (COLOR TBD)

3. VENDOR MAY SUGGEST ALTERNATE FABRICATION METHOD TO
DRILLING AND TAPPING HOLES ON AWK-105-0004

SCREEN PRINT GRAPHICS FOR THIS
FACE IN ARTWORK FILE: AWK-105-0017

FACE IN ARTWORK FILE: AWK-105-0016

SCREEN PRINT & HOLE LOCATIONS

DRILL AND TAP FOR M3 THREAD.
FABRICATOR MAY SEEK APPROVAL FOR
INSTALLING M3 CLINCH NUT.

UNLESS OTHERWISE SPECIFIED: | | NAME | DATE

DIMENSIONS ARE IN INCHES TOLERANCES: FRACTIONAL ANGULAR: MACH BEND TWO PLACE DECIMAL THREE PLACE DECIMAL | DRAWN

CHECKED | | | TITLE: VOLTMETER CLOCK
MFG APPR.

ENG APPR.

INTERPRET GEOMETRIC TOLERANCING PER: | Q.A.
MATERIAL | | SIZE D AWK-105-0010 revD | DWG. NO. | REV D

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

NEXT ASSY | USED ON | FINISH

POWDER COATED, SCREEN PRINTED

APPLICATION | | | SCALE: 1:1 | WEIGHT: | SHEET 1 OF 1
