awkwardengineer/Clock/Mechanical/Testing/Clock 28Aug2015.pdf

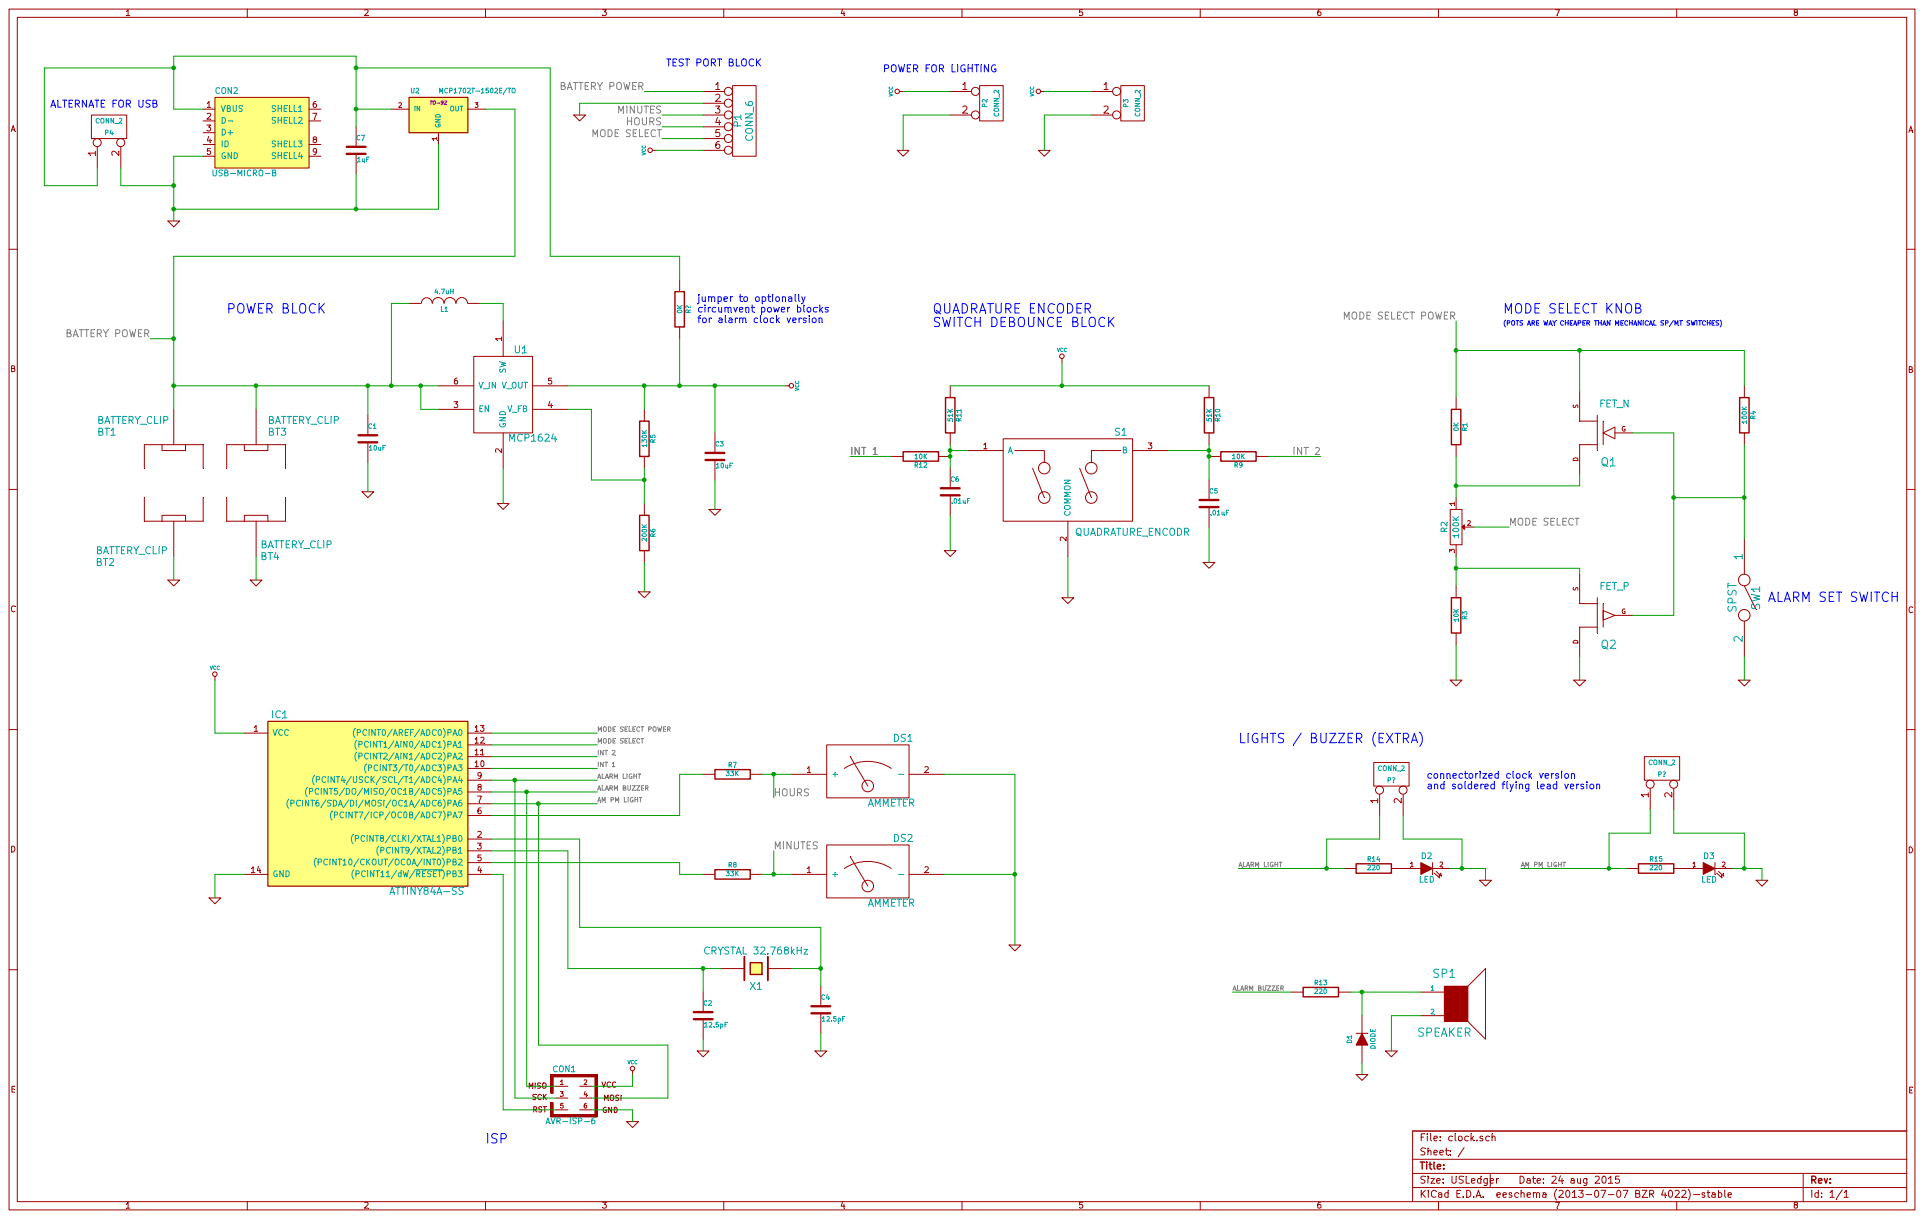
[picture p364: page 1]
