awkwardengineer/Clock/Mechanical/Artwork/AWK-105-0016 revF.pdf

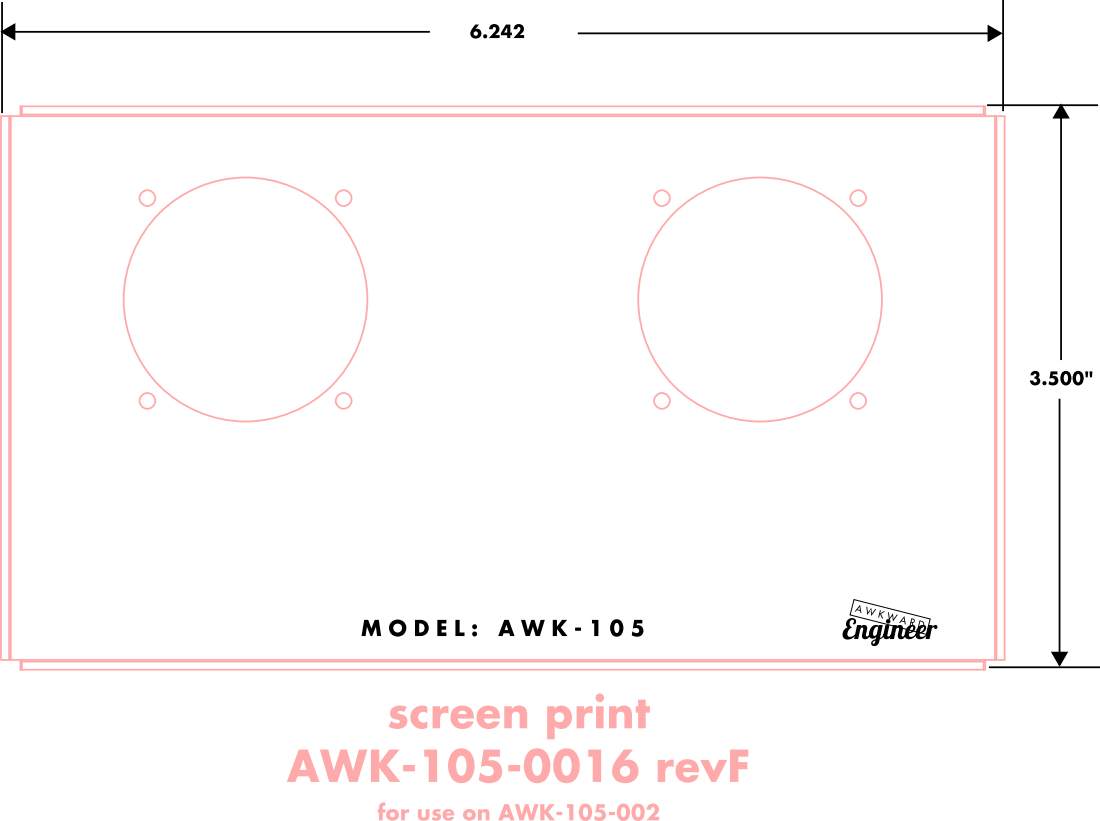
[picture p365: page 1]
