awkwardengineer/Clock/Mechanical/Artwork/AWK-105-0017 revF.pdf

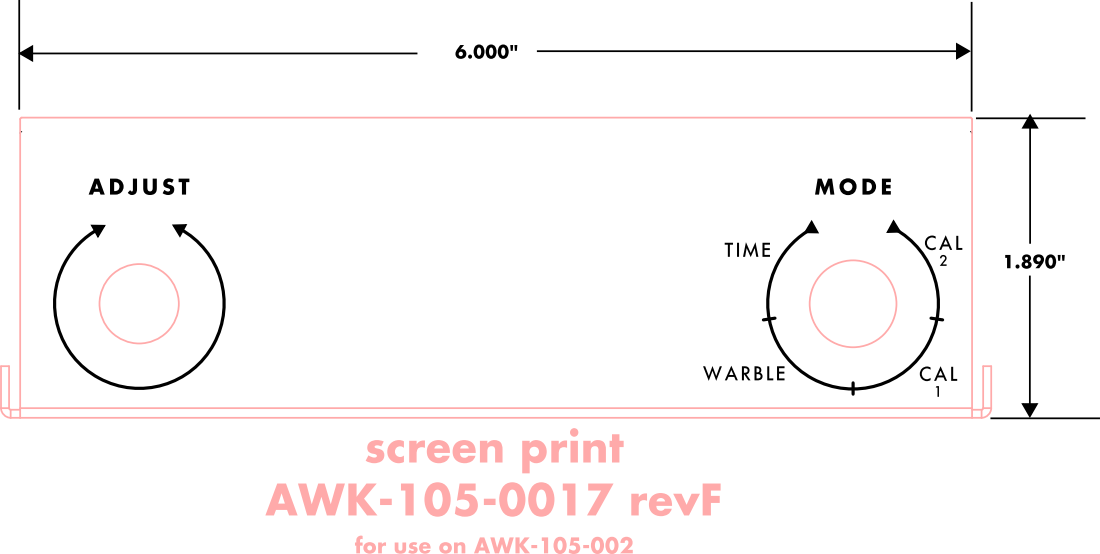
[picture p366: page 1]
