awkwardengineer/Clock/Mechanical/Artwork/laser cut and print.pdf

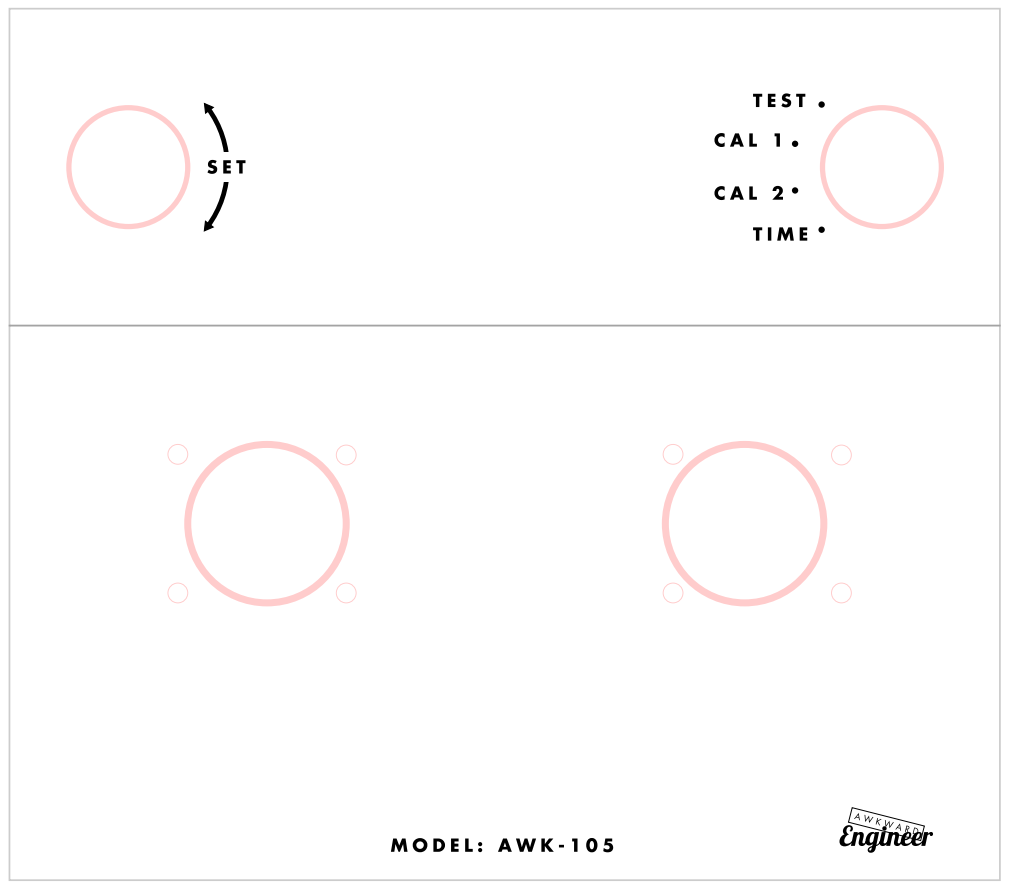
[picture p367: page 1]
