awkwardengineer/Clock/Mechanical/Artwork/Archive/sample 2.pdf

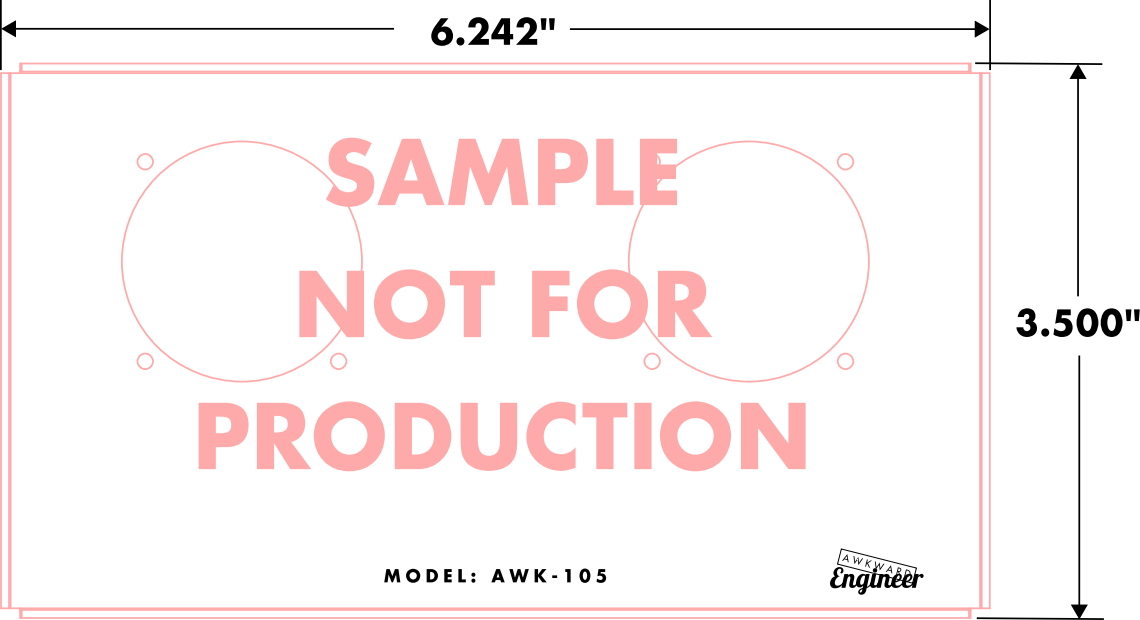
[picture p368: page 1]
