awkwardengineer/Clock/Mechanical/Artwork/Archive/sample.pdf

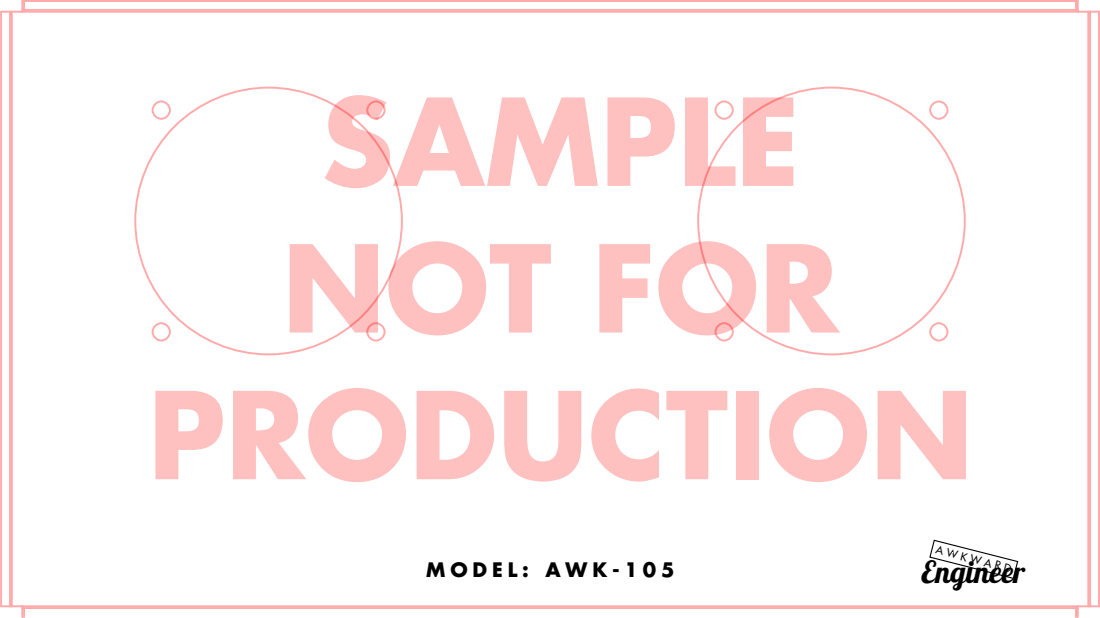
[picture p369: page 1]
Engineer
